duanestorey/Hifi-Amplifier/PCBs/AURORA/_Ready/PSU/readme.md

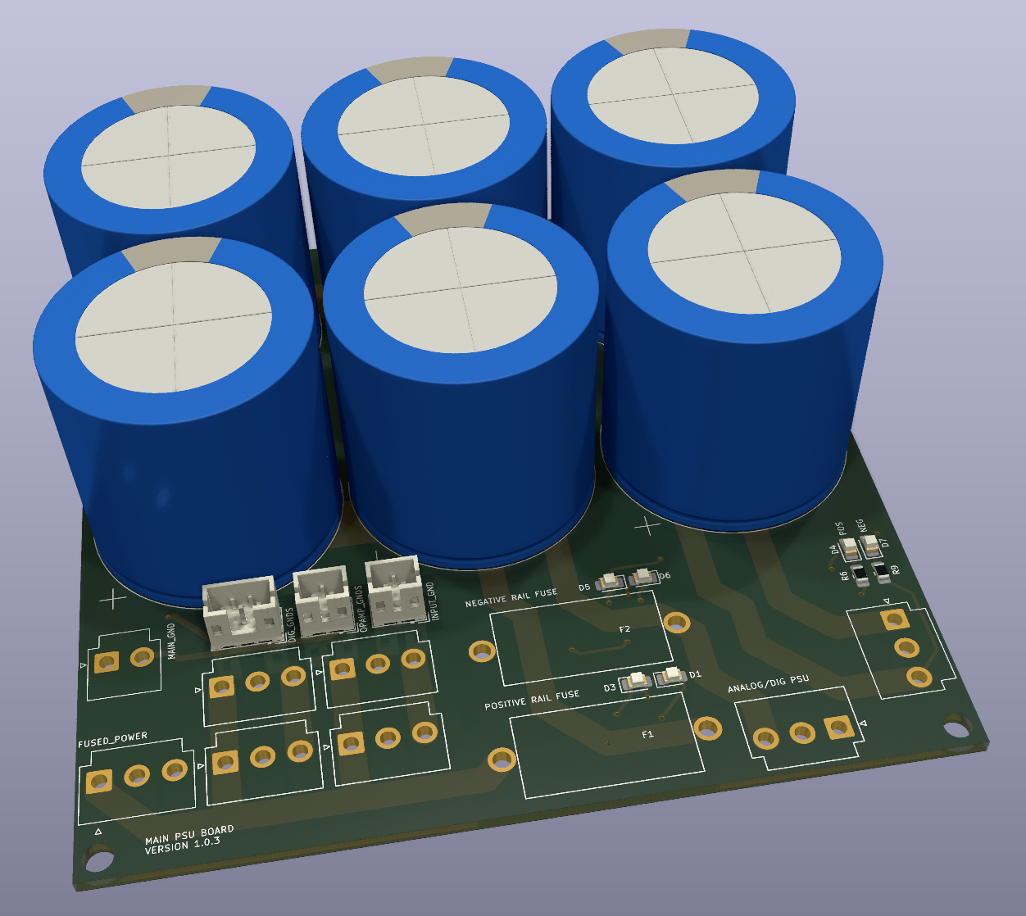
[picture p16: PCBs/AURORA/_Ready/PSU/screenshot.png]


# Main Amplifier Channel Power Supply

## Version History

- 1.0: Initial Release

## Speciality Components

* 30x50mm 15000uF 50V capacitors
* 5x20mm fuse holders
* 5V MELF Zener diodes
