duanestorey/Hifi-Amplifier/PCBs/AURORA/_Ready/FTDI/screenshot.png

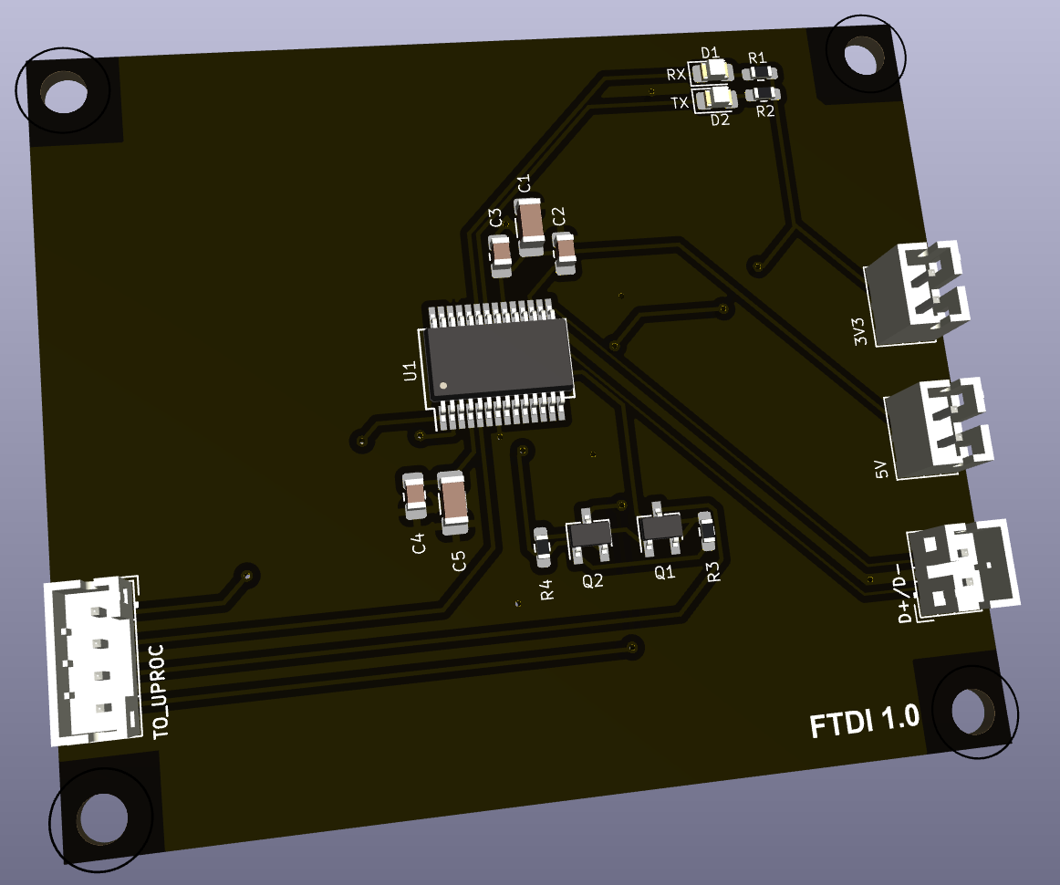
PCBs/AURORA/_Ready/FTDI/screenshot.png
