duanestorey/Hifi-Amplifier/PCBs/AURORA/_Ready/Lift/screenshot.png

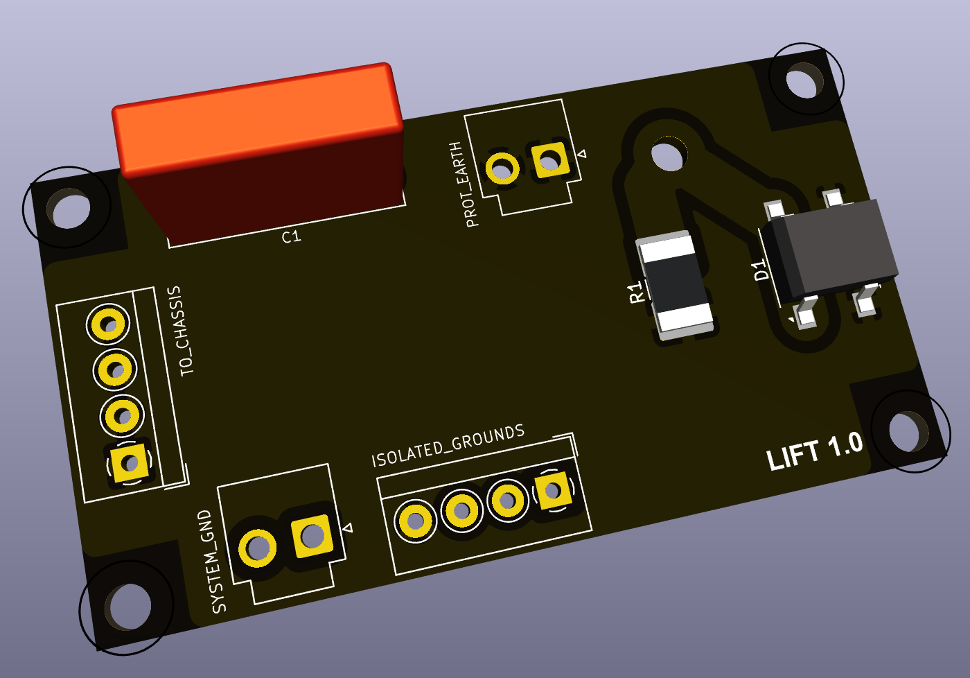
PCBs/AURORA/_Ready/Lift/screenshot.png
