duanestorey/Hifi-Amplifier/PCBs/AURORA/DSP/screenshot.png

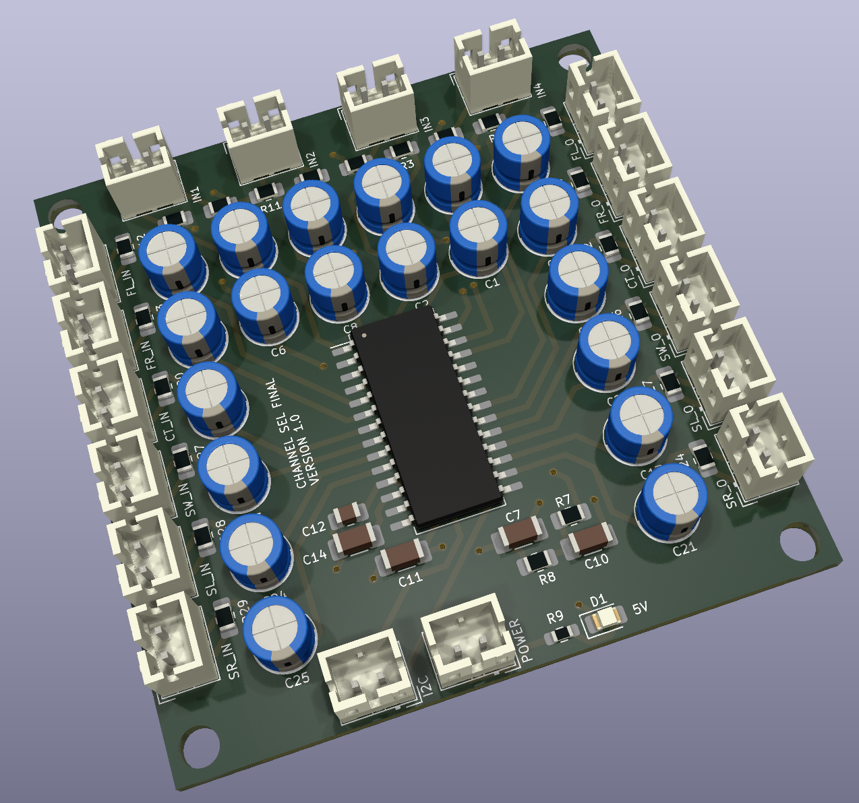
PCBs/AURORA/DSP/screenshot.png
