duanestorey/Hifi-Amplifier/PCBs/AURORA/Subwoofer/screenshot.png

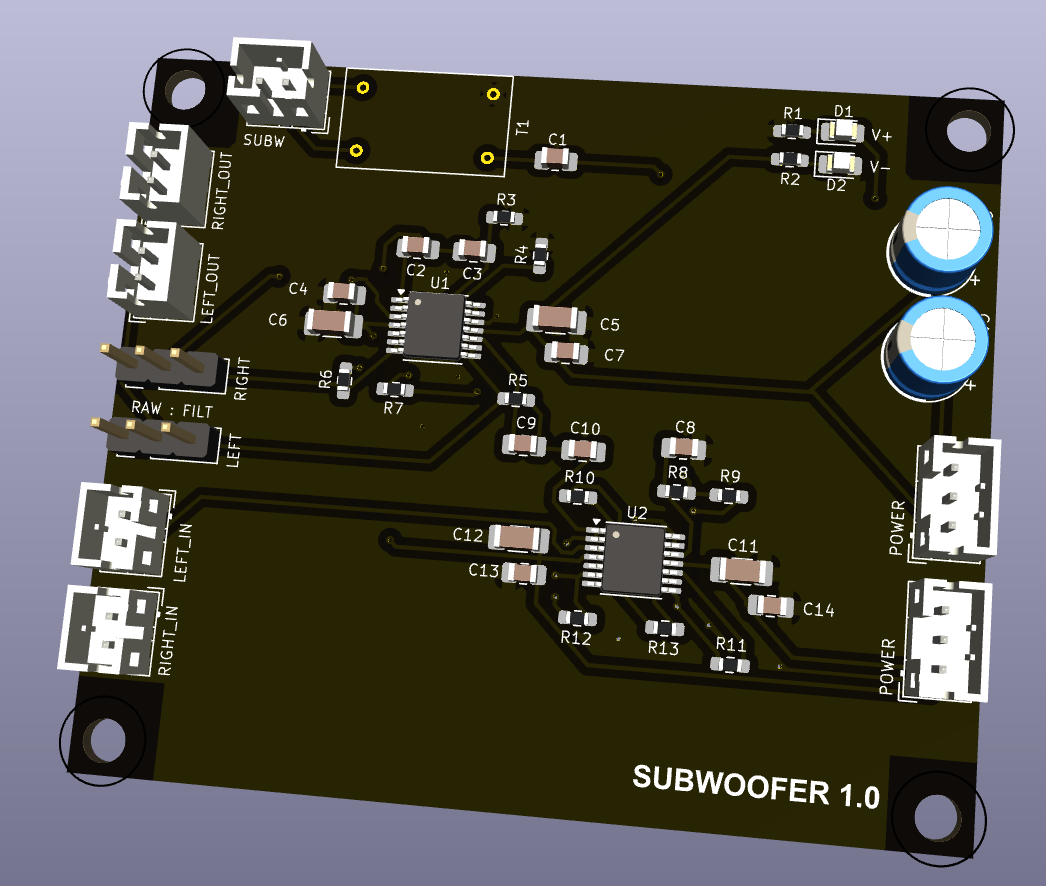
PCBs/AURORA/Subwoofer/screenshot.png
