duanestorey/Hifi-Amplifier/PCBs/DAC Filter/Filter/Low Noise/Screenshot 2023-10-08 at 9.19.52 PM.png

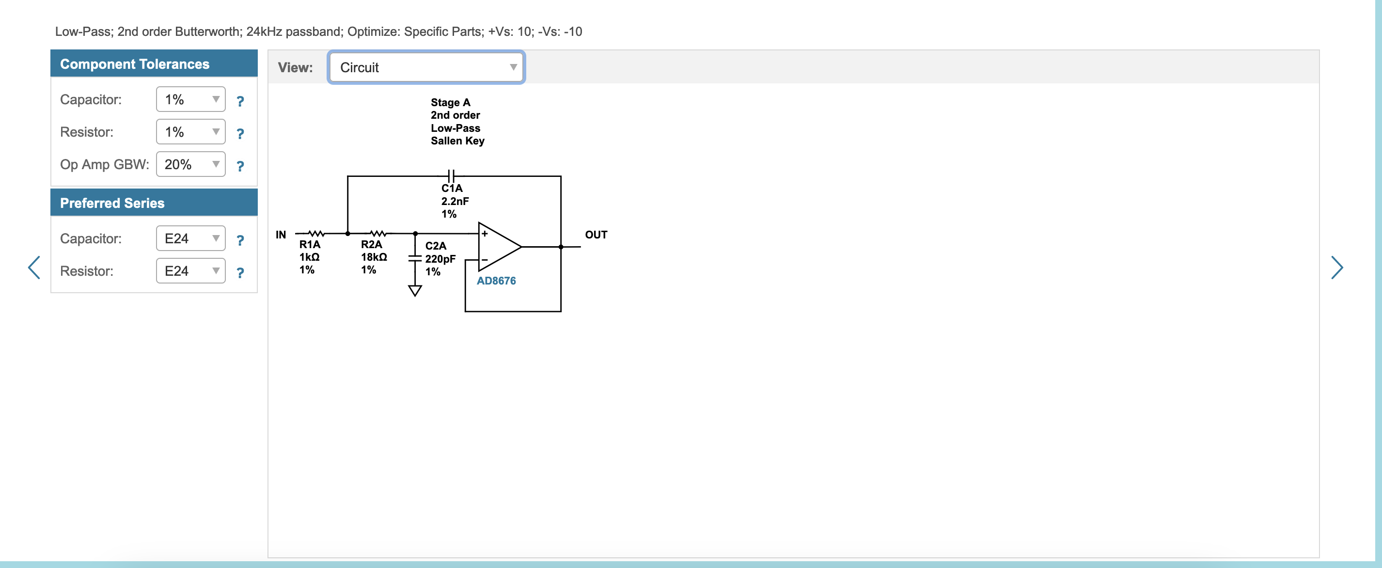
PCBs/DAC Filter/Filter/Low Noise/Screenshot 2023-10-08 at 9.19.52 PM.png
