duanestorey/Hifi-Amplifier/PCBs/AURORA/_Ready/Rectify/1.0/production/bom.csv

Designator | Footprint | Quantity | Value | LCSC Part #
C1, C2 | C_Rect_L13.0mm_W6.0mm_P10.00mm_FKS3_FKP3_MKS4 | 2 | 100N
D1, D3 | Diode_Bridge_Bourns_CD-DF4xxS | 2 | 652-CD-DF408SL
D2 | 0603 | 1 | YELLOW
D4 | 0603 | 1 | BLUE
H1, H2, H3, H4 | MountingHole_3.2mm_M3_Pad_TopOnly | 4 | MountingHole
J1 | JST_VH_B3P-VH_1x03_P3.96mm_Vertical | 1 | Conn_01x03_Male
J2, J3 | JST_VH_B2P-VH-B_1x02_P3.96mm_Vertical | 2 | Conn_01x02_Male
R1, R3 | 0603 | 2 | 16K
R2, R4 | 2512 | 2 | 10R 2W
