duanestorey/Hifi-Amplifier/PCBs/AURORA/DSP/ADAU/0.1/DSP.kicad_pcb

## KiCad design PCBs/AURORA/DSP/_Archived/ADAU/0.1/DSP.kicad_pcb (2024-12-19, an earlier design)

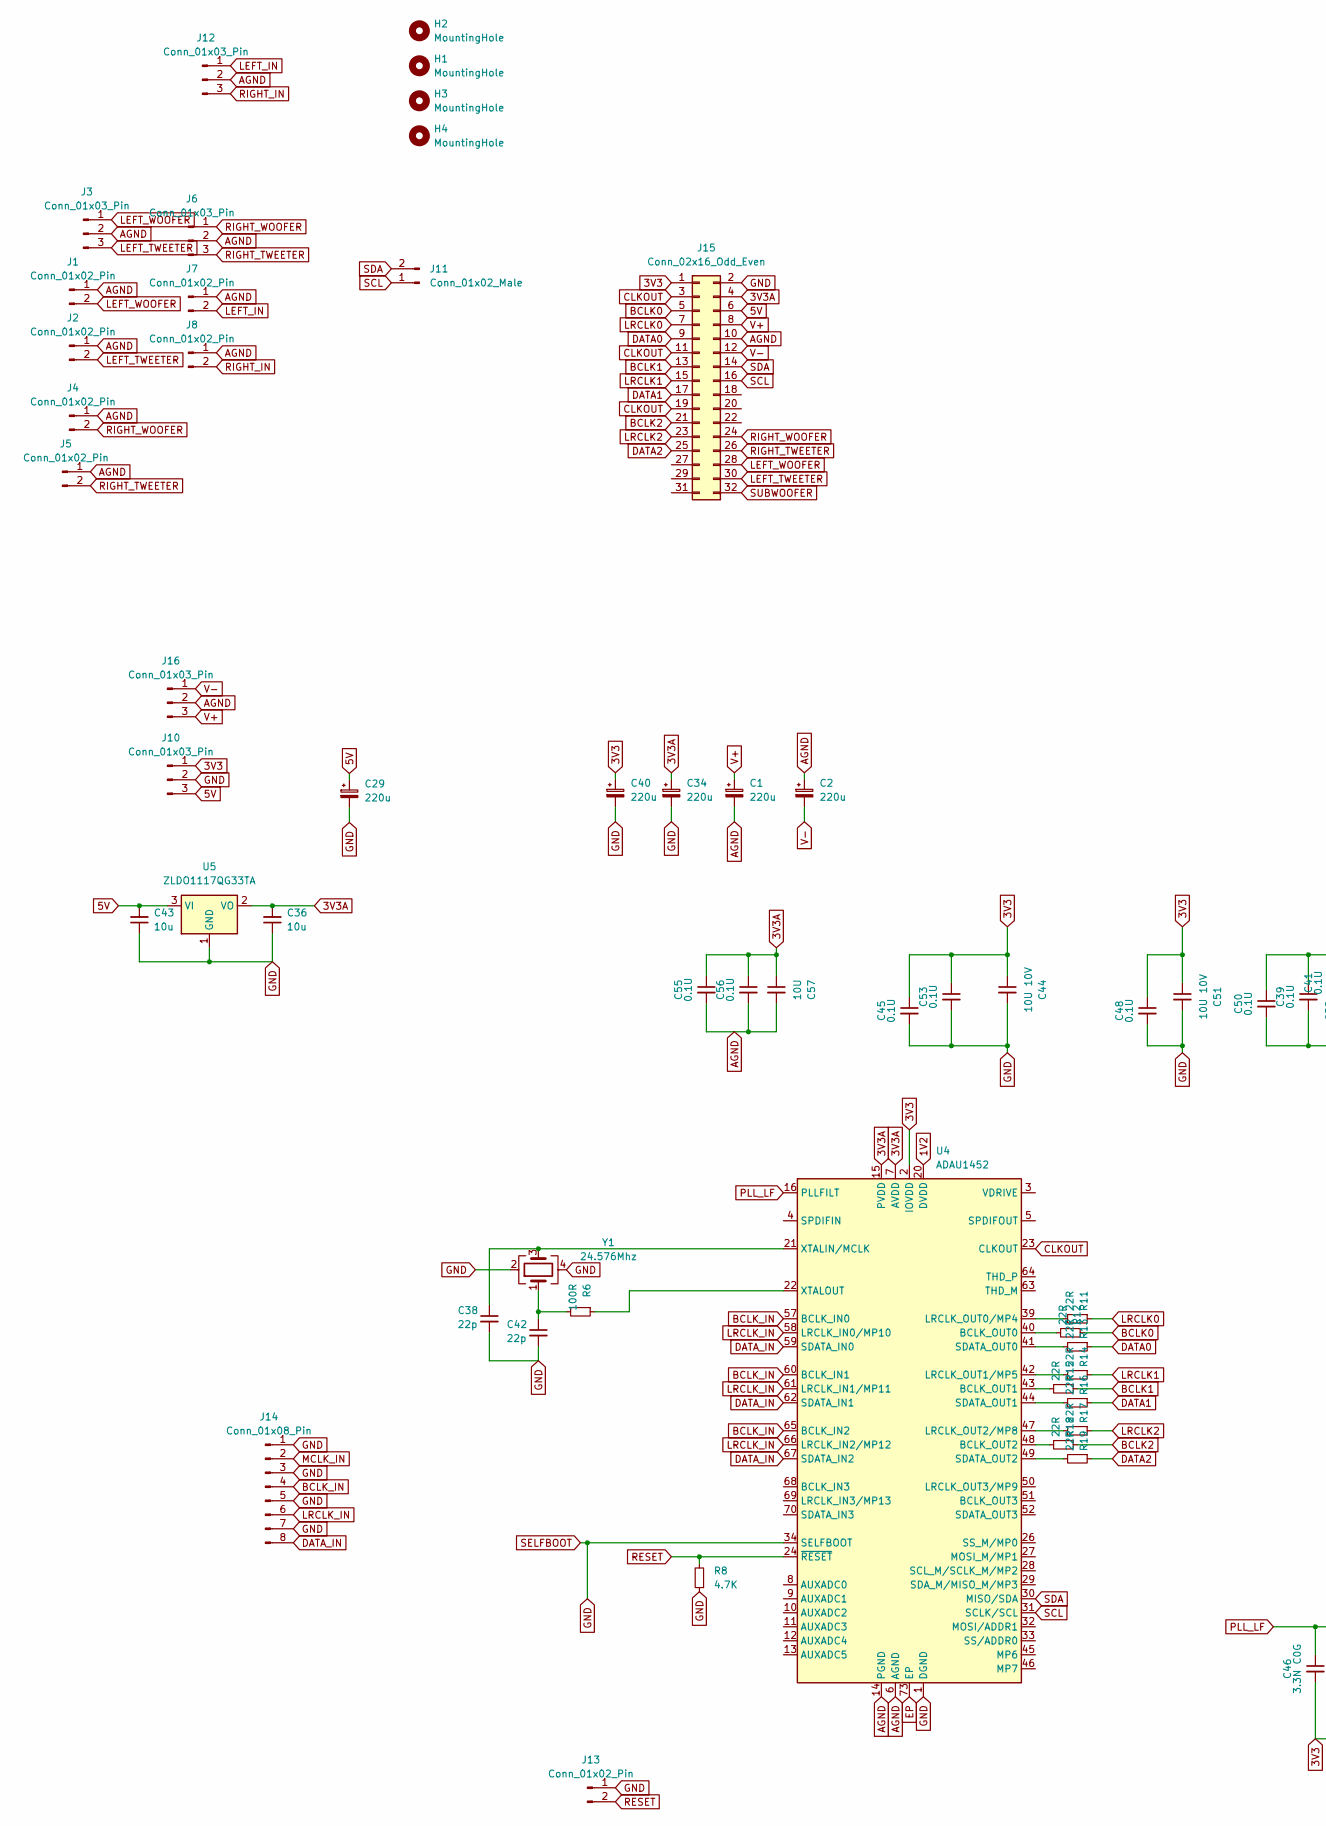
[picture p57: schematic DSP.kicad_sch, part in row 1, column 1]

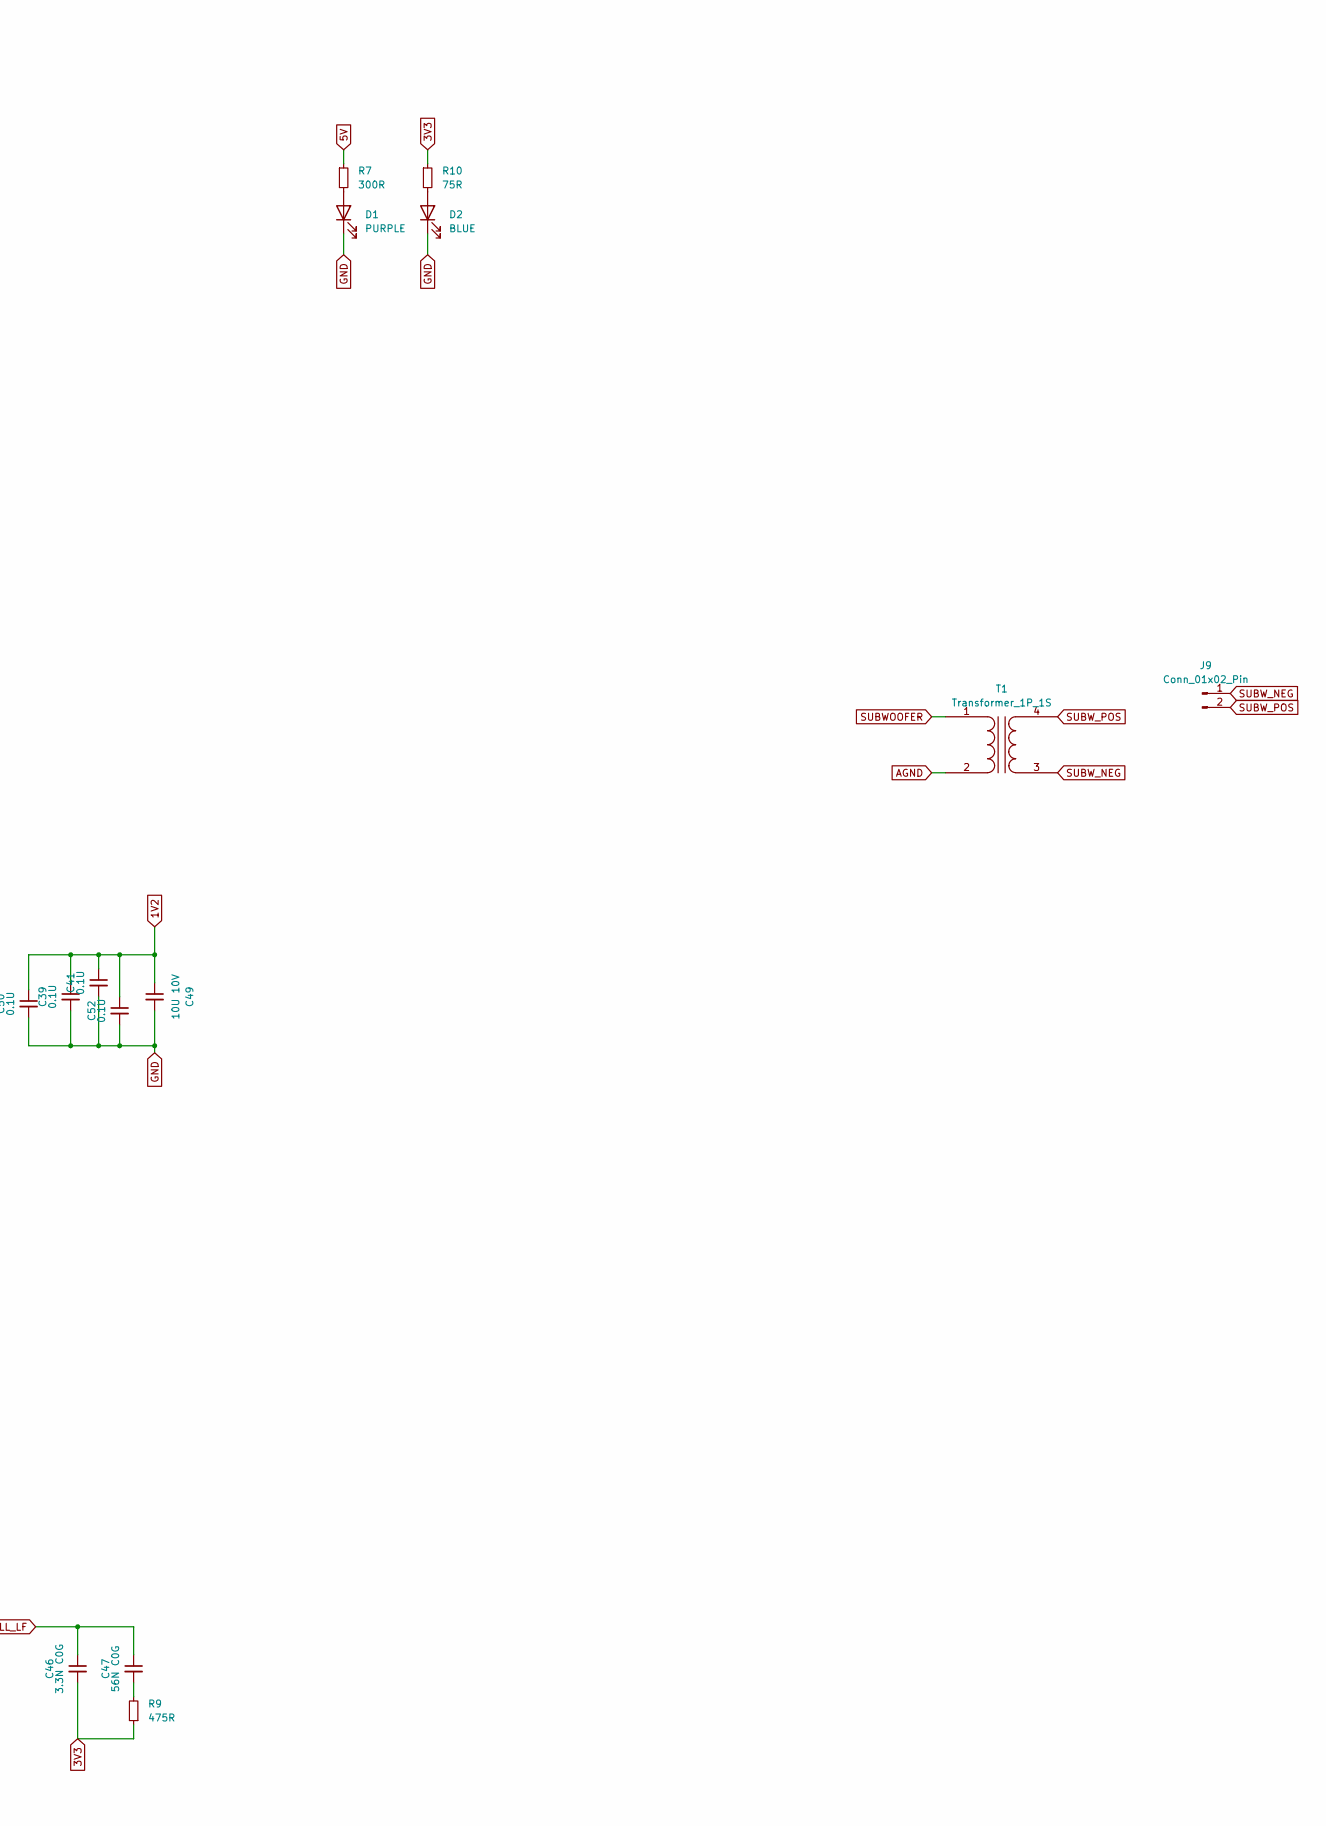
[picture p58: schematic DSP.kicad_sch, part in row 1, column 2]

Parts:
C1, C2, C29, C34, C40: 220u; CP_Radial_D6.3mm_P2.50mm
C36, C43: 10u; C_1206_3216Metric_Pad1.33x1.80mm_HandSolder
C38, C42: 22p; C_0805_2012Metric_Pad1.18x1.45mm_HandSolder
C39, C41, C45, C48, C50, C52, C53, C55, C56: 0.1U; C_0805_2012Metric_Pad1.18x1.45mm_HandSolder
C44, C49, C51: 10U 10V; C_1206_3216Metric_Pad1.33x1.80mm_HandSolder
C46: 3.3N C0G; C_0805_2012Metric_Pad1.18x1.45mm_HandSolder
C47: 56N C0G; C_0805_2012Metric_Pad1.18x1.45mm_HandSolder
C57: 10U; C_1206_3216Metric_Pad1.33x1.80mm_HandSolder
D1: PURPLE; D_0805_2012Metric
D2: BLUE; D_0805_2012Metric
H1, H2, H3, H4: MountingHole; MountingHole_3.2mm_M3
J1, J2, J4, J5, J7, J8, J9, J13: Conn_01x02_Pin; JST_PH_B2B-PH-K_1x02_P2.00mm_Vertical
J3, J6, J10, J12, J16: Conn_01x03_Pin; JST_PH_B3B-PH-K_1x03_P2.00mm_Vertical
J11: Conn_01x02_Male; JST_PH_B2B-PH-K_1x02_P2.00mm_Vertical
J14: Conn_01x08_Pin; JST_PH_B8B-PH-K_1x08_P2.00mm_Vertical
J15: Conn_02x16_Odd_Even; PinHeader_2x16_P2.54mm_Vertical
R6: 100R; R_0603_1608Metric_Pad0.98x0.95mm_HandSolder
R7: 300R; R_0603_1608Metric_Pad0.98x0.95mm_HandSolder
R8: 4.7K; R_0603_1608Metric_Pad0.98x0.95mm_HandSolder
R9: 475R; R_1206_3216Metric_Pad1.30x1.75mm_HandSolder
R10: 75R; R_0603_1608Metric_Pad0.98x0.95mm_HandSolder
R11, R12, R13, R14, R15, R16, R17, R18, R19: 22R; R_0603_1608Metric_Pad0.98x0.95mm_HandSolder
T1: Transformer_1P_1S; DA101C
U4: ADAU1452; LFCSP-72-1EP_10x10mm_P0.5mm_EP5.3x5.3mm
U5: ZLDO1117QG33TA; SOT-223-3_TabPin2
Y1: 24.576Mhz; Crystal_SMD_3225-4Pin_3.2x2.5mm_HandSoldering

Connections:
1V2: C39.1, C41.1, C49.1, C50.1, C52.1, U4.20 (DVDD), U4.35 (DVDD), U4.53 (DVDD), U4.71 (DVDD)
3V3: C40.1, C44.1, C45.1, C46.2, C48.1, C51.1, C53.1, J10.1, J15.1, R9.1, R10.1, U4.2 (IOVDD), U4.18 (IOVDD), U4.38 (IOVDD), U4.56 (IOVDD)
3V3A: C34.1, C36.2, C55.1, C56.1, C57.1, J15.4, U4.7 (AVDD), U4.15 (PVDD), U5.2 (VO)
5V: C29.1, C43.2, J10.3, J15.6, R7.1, U5.3 (VI)
AGND: C1.2, C2.1, C55.2, C56.2, C57.2, J1.1, J2.1, J3.2, J4.1, J5.1, J6.2, J7.1, J8.1, J12.2, J15.10, J16.2, T1.2 (AB), U4.6 (AGND), U4.14 (PGND)
BCLK0: J15.5, R12.1
BCLK1: J15.13, R15.1
BCLK2: J15.21, R18.1
BCLK_IN: J14.4, U4.57 (BCLK_IN0), U4.60 (BCLK_IN1), U4.65 (BCLK_IN2)
CLKOUT: J15.3, J15.11, J15.19, U4.23 (CLKOUT)
DATA0: J15.9, R13.1
DATA1: J15.17, R16.1
DATA2: J15.25, R19.1
DATA_IN: J14.8, U4.59 (SDATA_IN0), U4.62 (SDATA_IN1), U4.67 (SDATA_IN2)
EP: U4.73 (EP)
GND: C29.2, C34.2, C36.1, C38.2, C39.2, C40.2, C41.2, C42.2, C43.1, C44.2, C45.2, C48.2, C49.2, C50.2, C51.2, C52.2, C53.2, D1.1 (K), D2.1 (K), J10.2, J13.1, J14.1, J14.3, J14.5, J14.7, J15.2, R8.1, U4.1 (DGND), U4.17 (DGND), U4.19 (DGND), U4.25 (DGND), U4.34 (SELFBOOT), U4.36 (DGND), U4.37 (DGND), U4.54 (DGND), U4.55 (DGND), U4.72 (DGND), U5.1 (GND), Y1.2, Y1.4
LEFT_IN: J7.2, J12.1
LEFT_TWEETER: J2.2, J3.3, J15.30
LEFT_WOOFER: J1.2, J3.1, J15.28
LRCLK0: J15.7, R11.1
LRCLK1: J15.15, R14.1
LRCLK2: J15.23, R17.1
LRCLK_IN: J14.6, U4.58 (LRCLK_IN0/MP10), U4.61 (LRCLK_IN1/MP11), U4.66 (LRCLK_IN2/MP12)
MCLK_IN: J14.2
unnamed: C42.1, R6.2, Y1.1
unnamed: C47.2, R9.2
unnamed: D1.2 (A), R7.2
unnamed: D2.2 (A), R10.2
unnamed: R12.2, U4.40 (BCLK_OUT0)
unnamed: R15.2, U4.43 (BCLK_OUT1)
unnamed: R18.2, U4.48 (BCLK_OUT2)
unnamed: R11.2, U4.39 (LRCLK_OUT0/MP4)
unnamed: R14.2, U4.42 (LRCLK_OUT1/MP5)
unnamed: R17.2, U4.47 (LRCLK_OUT2/MP8)
unnamed: R13.2, U4.41 (SDATA_OUT0)
unnamed: R16.2, U4.44 (SDATA_OUT1)
unnamed: R19.2, U4.49 (SDATA_OUT2)
unnamed: C38.1, U4.21 (XTALIN/MCLK), Y1.3
unnamed: R6.1, U4.22 (XTALOUT)
PLL_LF: C46.1, C47.1, U4.16 (PLLFILT)
RESET: J13.2, R8.2, U4.24 (~RESET)
RIGHT_IN: J8.2, J12.3
RIGHT_TWEETER: J5.2, J6.3, J15.26
RIGHT_WOOFER: J4.2, J6.1, J15.24
SCL: J11.1, J15.16, U4.31 (SCLK/SCL)
SDA: J11.2, J15.14, U4.30 (MISO/SDA)
SUBWOOFER: J15.32, T1.1 (AA)
SUBW_NEG: J9.1, T1.3 (SA)
SUBW_POS: J9.2, T1.4 (SB)
V+: C1.1, J15.8, J16.3
V-: C2.2, J15.12, J16.1

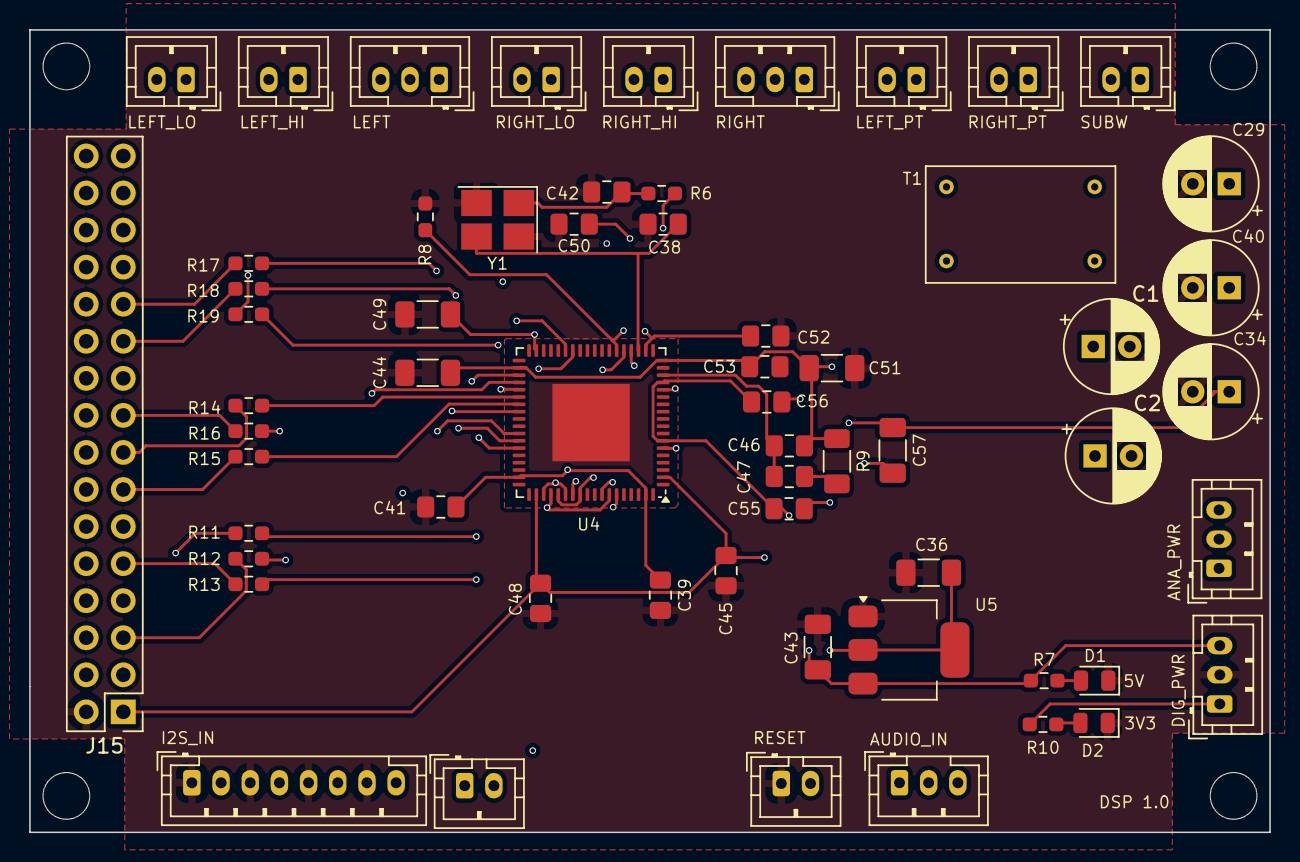
[picture p59: board PCBs/AURORA/DSP/_Archived/ADAU/0.1/DSP.kicad_pcb from above]

Board: 4 copper layers, 85.0 x 55.0 mm, 64 parts (0 on the bottom side), 49 nets.
