duanestorey/Hifi-Amplifier/PCBs/AURORA/InputSel/0.3/InputSel.kicad_pcb

## KiCad design PCBs/AURORA/InputSel/0.3/InputSel.kicad_pcb (2024-12-21)

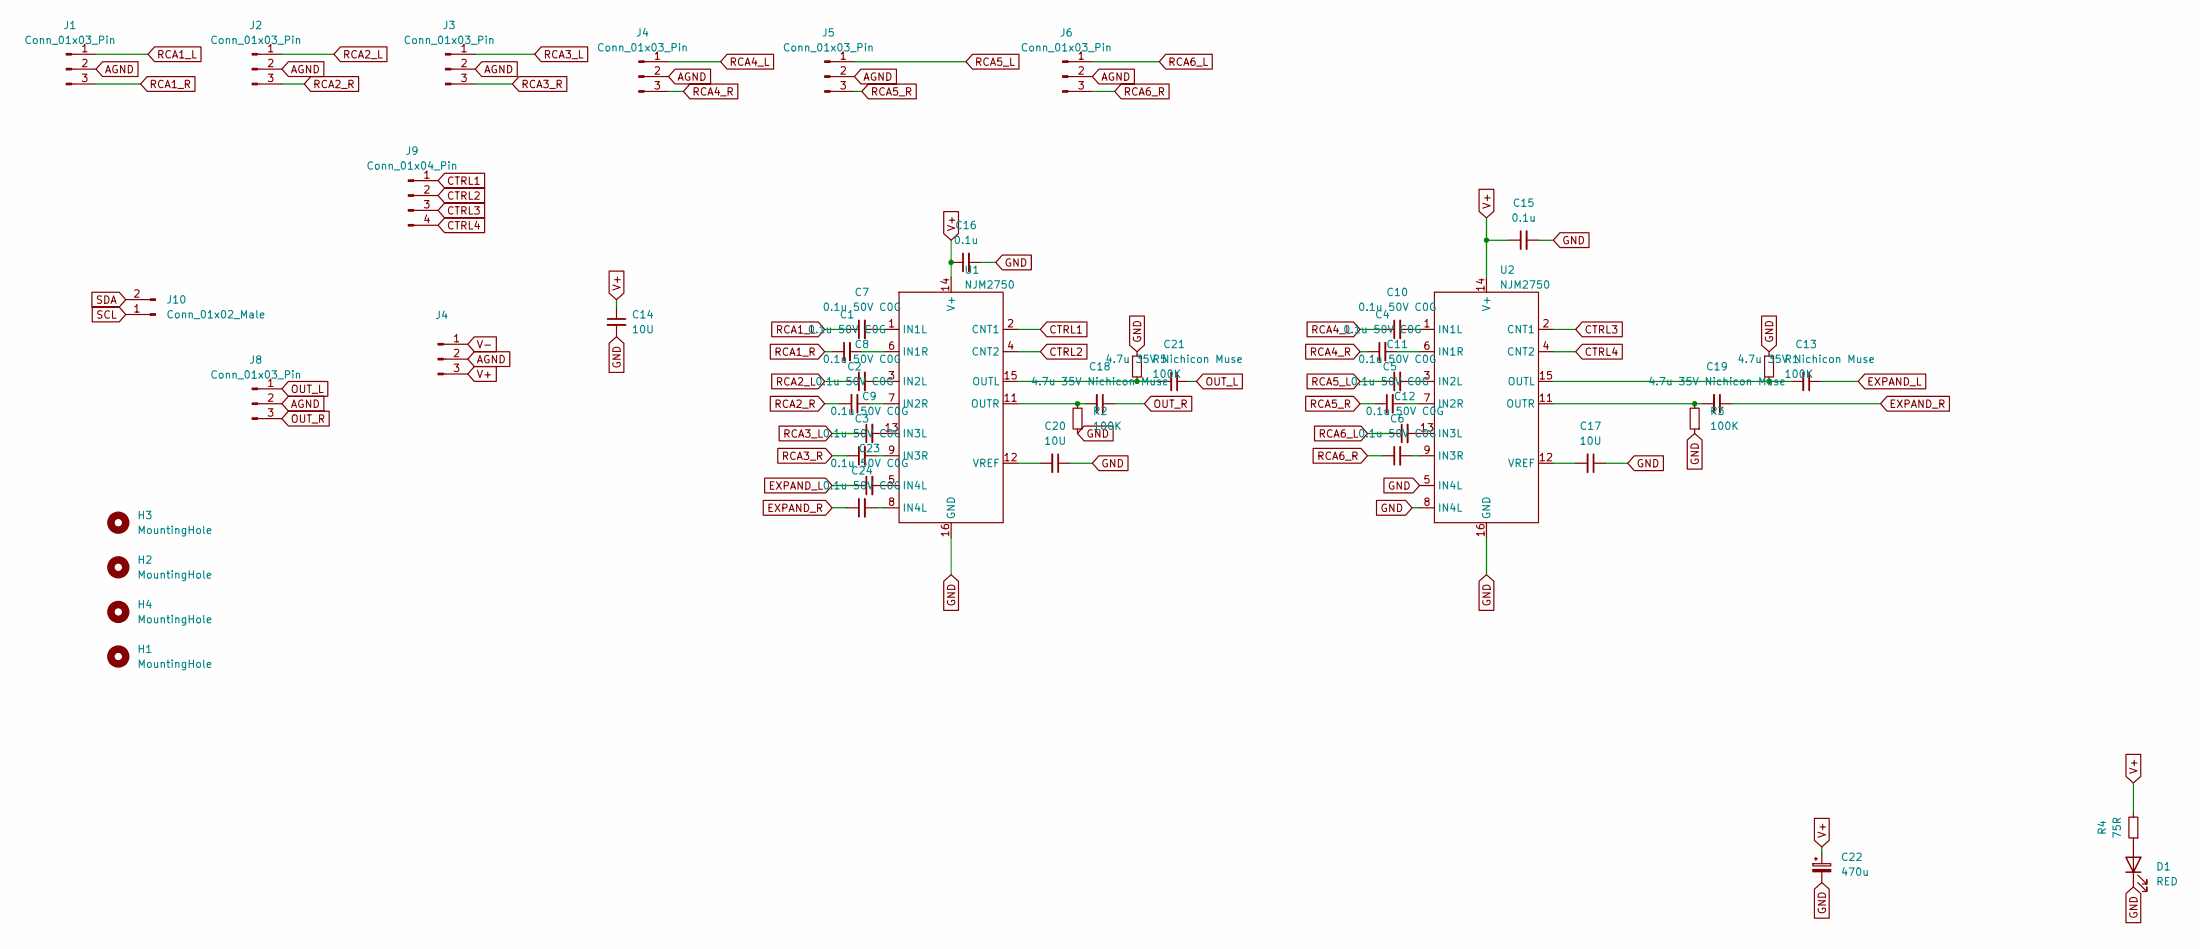
[picture p62: schematic InputSel.kicad_sch]

Parts:
C1, C2, C3, C4, C5, C6, C7, C8, C9, C10, C11, C12, C23, C24: 0.1u 50V C0G; C_1206_3216Metric_Pad1.33x1.80mm_HandSolder; Mouser 81-GRM3195C1H104JA5D
C13, C18, C19, C21: 4.7u 35V Nichicon Muse; CP_Radial_D5.0mm_P2.00mm
C14, C17, C20: 10U; C_1206_3216Metric_Pad1.33x1.80mm_HandSolder
C15, C16: 0.1u; C_0805_2012Metric_Pad1.18x1.45mm_HandSolder
C22: 470u; CP_Radial_D6.3mm_P2.50mm
D1: RED; LED_0805_2012Metric
H1, H2, H3, H4: MountingHole; MountingHole_3.2mm_M3_DIN965_Pad_TopOnly
J1, J2, J3, J5, J6, J8: Conn_01x03_Pin; JST_PH_B3B-PH-K_1x03_P2.00mm_Vertical
J4: Conn_01x03_Male; JST_PH_B3B-PH-K_1x03_P2.00mm_Vertical
J9: Conn_01x04_Pin; JST_PH_B4B-PH-K_1x04_P2.00mm_Vertical
J10: Conn_01x02_Male; JST_PH_B2B-PH-K_1x02_P2.00mm_Vertical
R1, R2, R3, R5: 100K; R_0603_1608Metric_Pad0.98x0.95mm_HandSolder; Mouser 603-AT0603FRE07100KL
R4: 75R; R_0603_1608Metric_Pad0.98x0.95mm_HandSolder
U1, U2: NJM2750; SOP-16_4.4x10.4mm_P1.27mm; Mouser NJM2750M

Connections:
AGND: J1.2, J2.2, J3.2, J4.2, J5.2, J6.2, J8.2; also elsewhere on the board
CTRL1: J9.1, U1.2 (CNT1)
CTRL2: J9.2, U1.4 (CNT2)
CTRL3: J9.3, U2.2 (CNT1)
CTRL4: J9.4, U2.4 (CNT2)
EXPAND_L: C13.1, C23.1
EXPAND_R: C19.1, C24.1
GND: C14.2, C15.2, C16.2, C17.1, C20.1, C22.2, D1.1 (K), R1.1, R2.1, R3.1, R5.1, U1.16 (GND), U2.5 (IN4L), U2.8 (IN4L), U2.16 (GND)
unnamed: C23.2, U1.5 (IN4L)
unnamed: C24.2, U1.8 (IN4L)
unnamed: D1.2 (A), R4.1
unnamed: C7.2, U1.1 (IN1L)
unnamed: C1.2, U1.6 (IN1R)
unnamed: C8.2, U1.3 (IN2L)
unnamed: C2.2, U1.7 (IN2R)
unnamed: C9.2, U1.13 (IN3L)
unnamed: C3.2, U1.9 (IN3R)
unnamed: C21.2, R5.2, U1.15 (OUTL)
unnamed: C18.2, R2.2, U1.11 (OUTR)
unnamed: C20.2, U1.12 (VREF)
unnamed: C10.2, U2.1 (IN1L)
unnamed: C4.2, U2.6 (IN1R)
unnamed: C11.2, U2.3 (IN2L)
unnamed: C5.2, U2.7 (IN2R)
unnamed: C12.2, U2.13 (IN3L)
unnamed: C6.2, U2.9 (IN3R)
unnamed: C13.2, R1.2, U2.15 (OUTL)
unnamed: C19.2, R3.2, U2.11 (OUTR)
unnamed: C17.2, U2.12 (VREF)
OUT_L: C21.1, J8.1
OUT_R: C18.1, J8.3
RCA1_L: C7.1, J1.1
RCA1_R: C1.1, J1.3
RCA2_L: C8.1, J2.1
RCA2_R: C2.1, J2.3
RCA3_L: C9.1, J3.1
RCA3_R: C3.1, J3.3
RCA5_L: C11.1, J5.1
RCA5_R: C5.1, J5.3
RCA6_L: C12.1, J6.1
RCA6_R: C6.1, J6.3
SCL: J10.1
SDA: J10.2

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
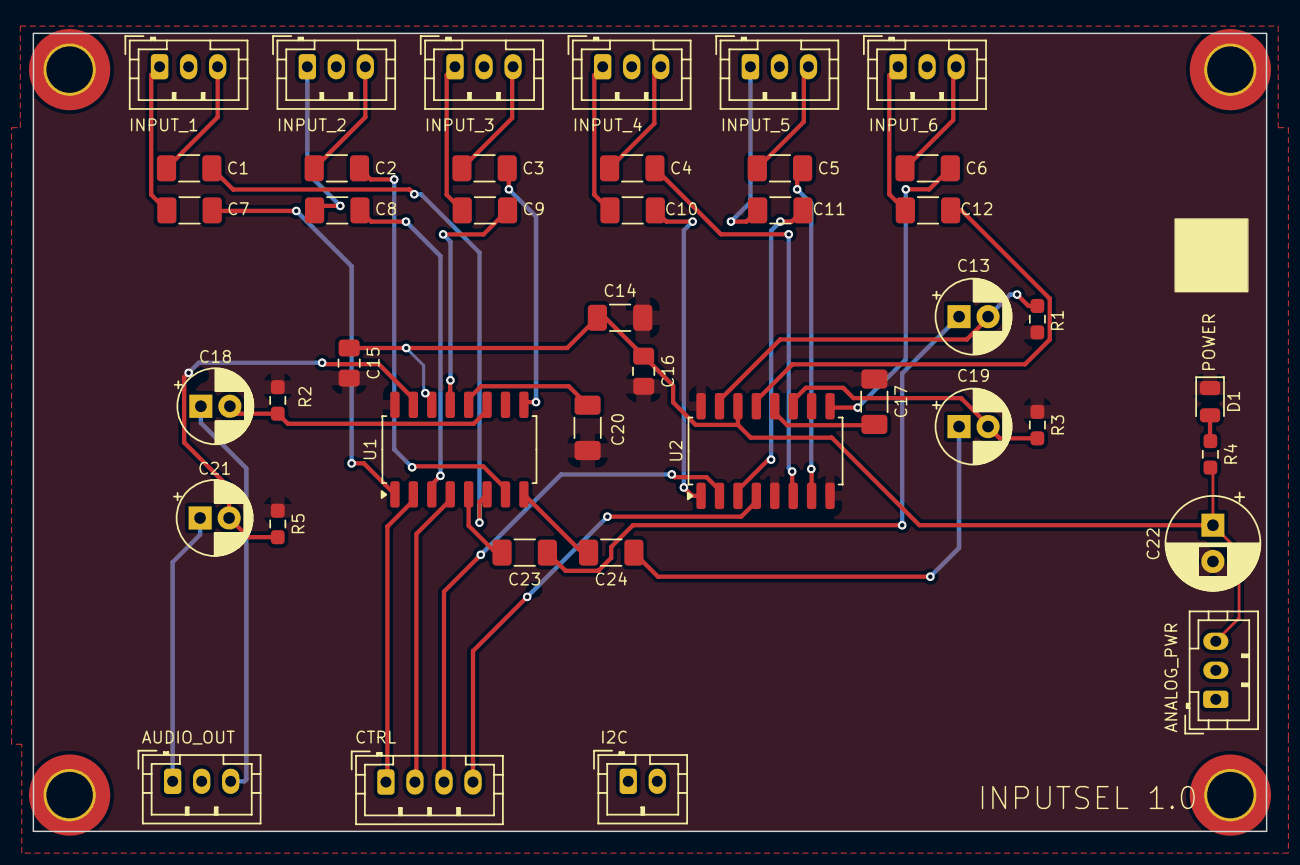
[picture p63: board PCBs/AURORA/InputSel/0.3/InputSel.kicad_pcb from above]

Board: 2 copper layers, 85.0 x 55.0 mm, 46 parts (0 on the bottom side), 44 nets.

Other parts of the board:
J7: Conn_01x03_Male; JST_PH_B3B-PH-K_1x03_P2.00mm_Vertical

Their connections:
AGND: J7.2; also elsewhere on the board
