duanestorey/Hifi-Amplifier/PCBs/AURORA/_Ready/PSU/1.0/PSU.kicad_pcb

## KiCad design PCBs/AURORA/_Ready/PSU/1.0/PSU.kicad_pcb (2024-12-19)

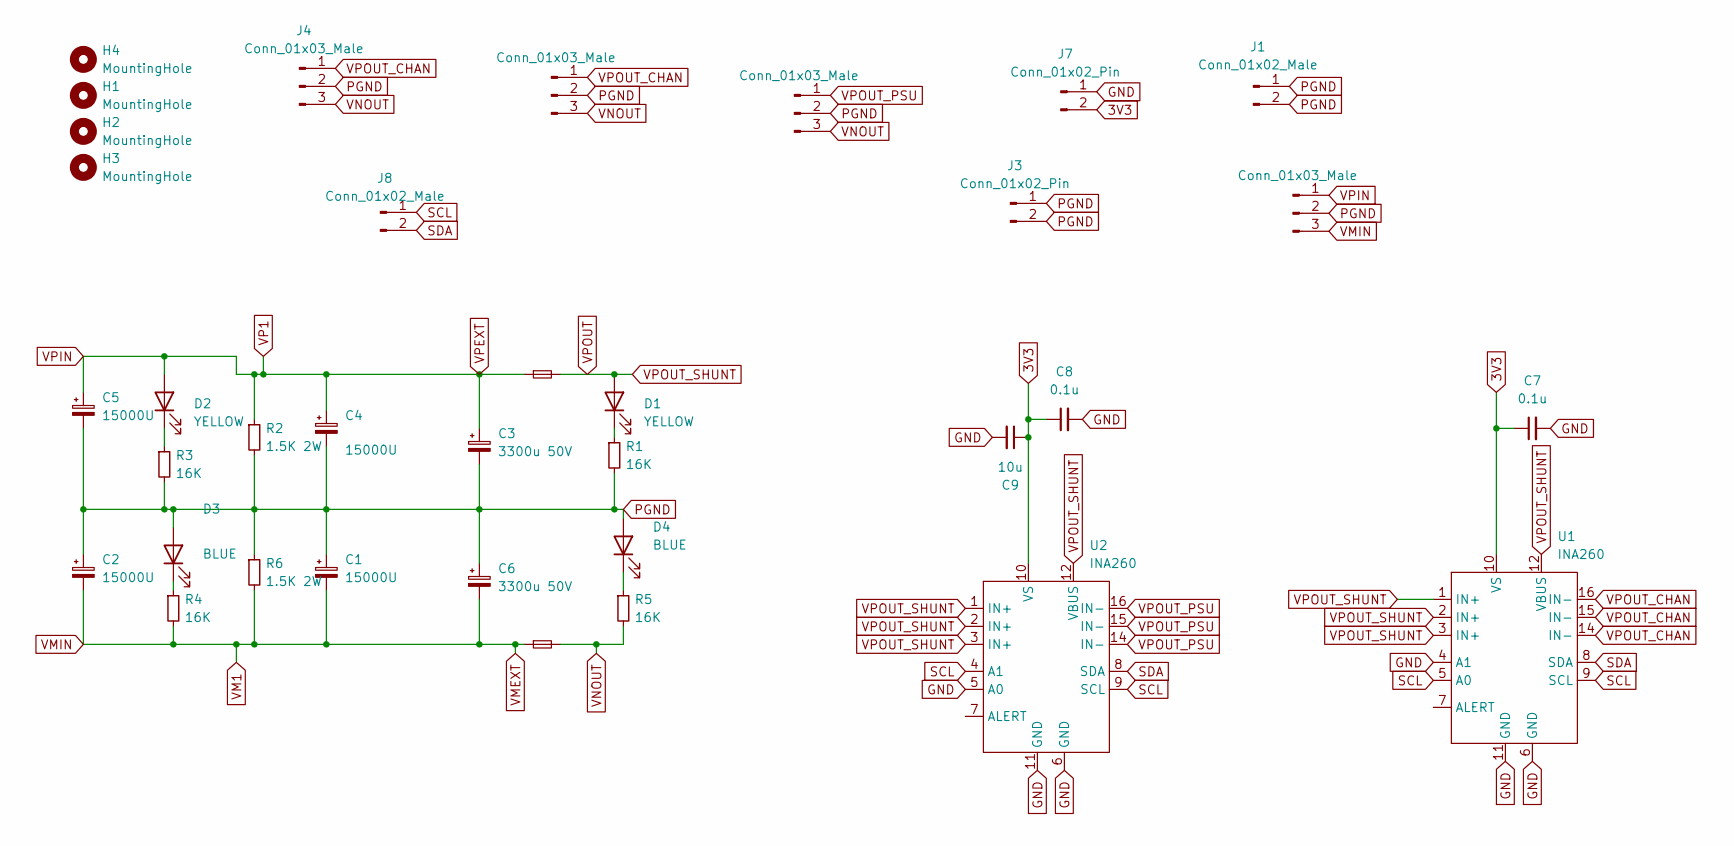
[picture p64: schematic PSU.kicad_sch]

Parts:
C1, C2, C4, C5: 15000U; CP_Radial_D30.0mm_P10.00mm_SnapIn
C3, C6: 3300u 50V; CP_Radial_D18.0mm_P7.50mm
C7, C8: 0.1u; C_0805_2012Metric_Pad1.18x1.45mm_HandSolder
C9: 10u; C_1206_3216Metric_Pad1.33x1.80mm_HandSolder
D1, D2: YELLOW; LED_0603_1608Metric_Pad1.05x0.95mm_HandSolder
D3, D4: BLUE; LED_0603_1608Metric_Pad1.05x0.95mm_HandSolder
F1, F2: Fuse_Small; Aliexpress Fuse 5x20
H1, H2, H3, H4: MountingHole; MountingHole_3mm_Pad_TopOnly
J1: Conn_01x02_Male; JST_VH_B2P-VH-B_1x02_P3.96mm_Vertical
J2, J4, J5, J6: Conn_01x03_Male; JST_VH_B3P-VH_1x03_P3.96mm_Vertical
J3, J7: Conn_01x02_Pin; JST_PH_B2B-PH-K_1x02_P2.00mm_Vertical
J8: Conn_01x02_Male; JST_PH_B2B-PH-K_1x02_P2.00mm_Vertical
R1, R3, R4, R5: 16K; LED_0603_1608Metric_Pad1.05x0.95mm_HandSolder; Mouser 71-CRCW060316K0FKEAC
R2, R6: 1.5K 2W; R_2512_6332Metric_Pad1.40x3.35mm_HandSolder; Mouser 652-CRM2512JW152ELF
U1, U2: INA260; TSSOP-16_4.4x5mm_P0.65mm; Mouser 595-INA260AIPWR

Connections:
3V3: C7.1, C8.1, C9.1, J7.2, U1.10 (VS), U2.10 (VS)
GND: C7.2, C8.2, C9.2, J7.1, U1.4 (A1), U1.6 (GND), U1.11 (GND), U2.5 (A0), U2.6 (GND), U2.11 (GND)
unnamed: D1.1 (K), R1.1
unnamed: D2.1 (K), R3.1
unnamed: D3.1 (K), R4.1
unnamed: D4.1 (K), R5.1
PGND: C1.1, C2.1, C3.2, C4.2, C5.2, C6.1, D3.2 (A), D4.2 (A), J1.1, J1.2, J2.2, J3.1, J3.2, J4.2, J5.2, J6.2, R1.2, R2.2, R3.2, R6.1
SCL: J8.1, U1.5 (A0), U1.9 (SCL), U2.4 (A1), U2.9 (SCL)
SDA: J8.2, U1.8 (SDA), U2.8 (SDA)
VM1: C1.2, C2.2, C6.2, F2.1, J2.3, R4.2, R6.2
VNOUT: F2.2, J4.3, J5.3, J6.3, R5.2
VP1: C3.1, C4.1, C5.1, D2.2 (A), F1.1, J2.1, R2.1
VPOUT: D1.2 (A), F1.2, U1.1 (IN+), U1.2 (IN+), U1.3 (IN+), U1.12 (VBUS), U2.1 (IN+), U2.2 (IN+), U2.3 (IN+), U2.12 (VBUS)
VPOUT_CHAN: J4.1, J5.1, U1.14 (IN-), U1.15 (IN-), U1.16 (IN-)
VPOUT_PSU: J6.1, U2.14 (IN-), U2.15 (IN-), U2.16 (IN-)

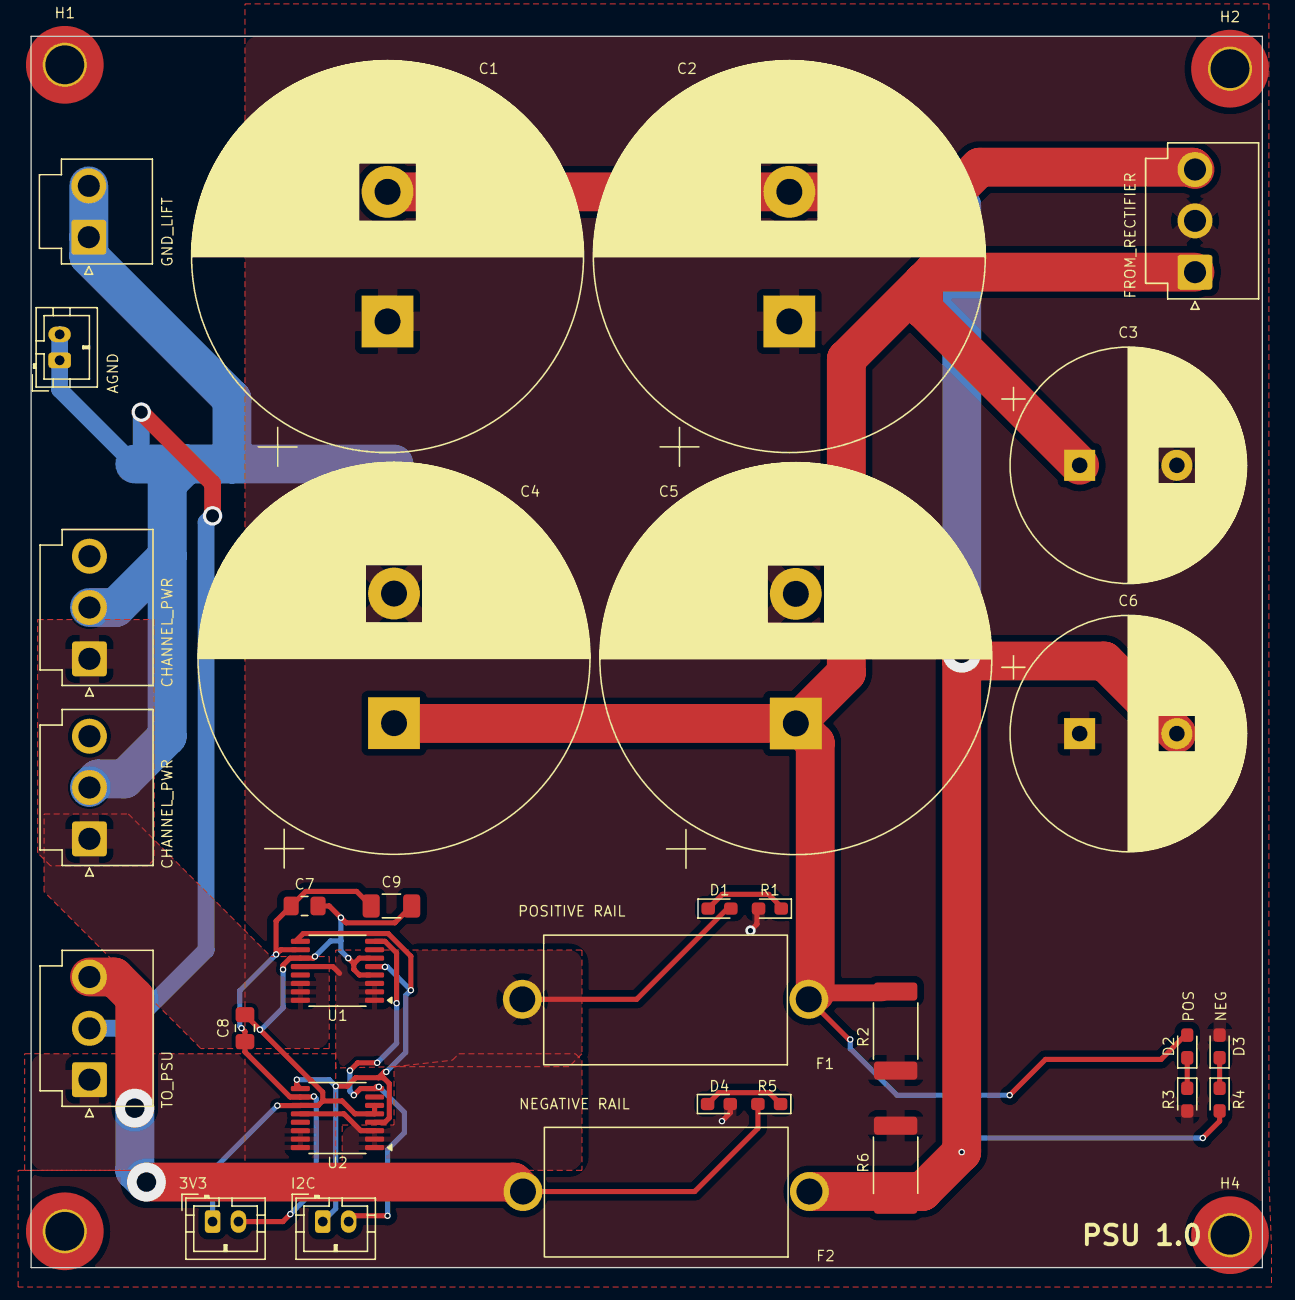
[picture p65: board PSU.kicad_pcb from above]

Board: 2 copper layers, 95.0 x 95.0 mm, 35 parts (0 on the bottom side), 15 nets.
