duanestorey/Hifi-Amplifier/PCBs/AURORA/_Ready/LM3886/1.0/LM3886.kicad_pcb

## KiCad design PCBs/AURORA/_Ready/LM3886/1.0/LM3886.kicad_pcb (2024-12-19)

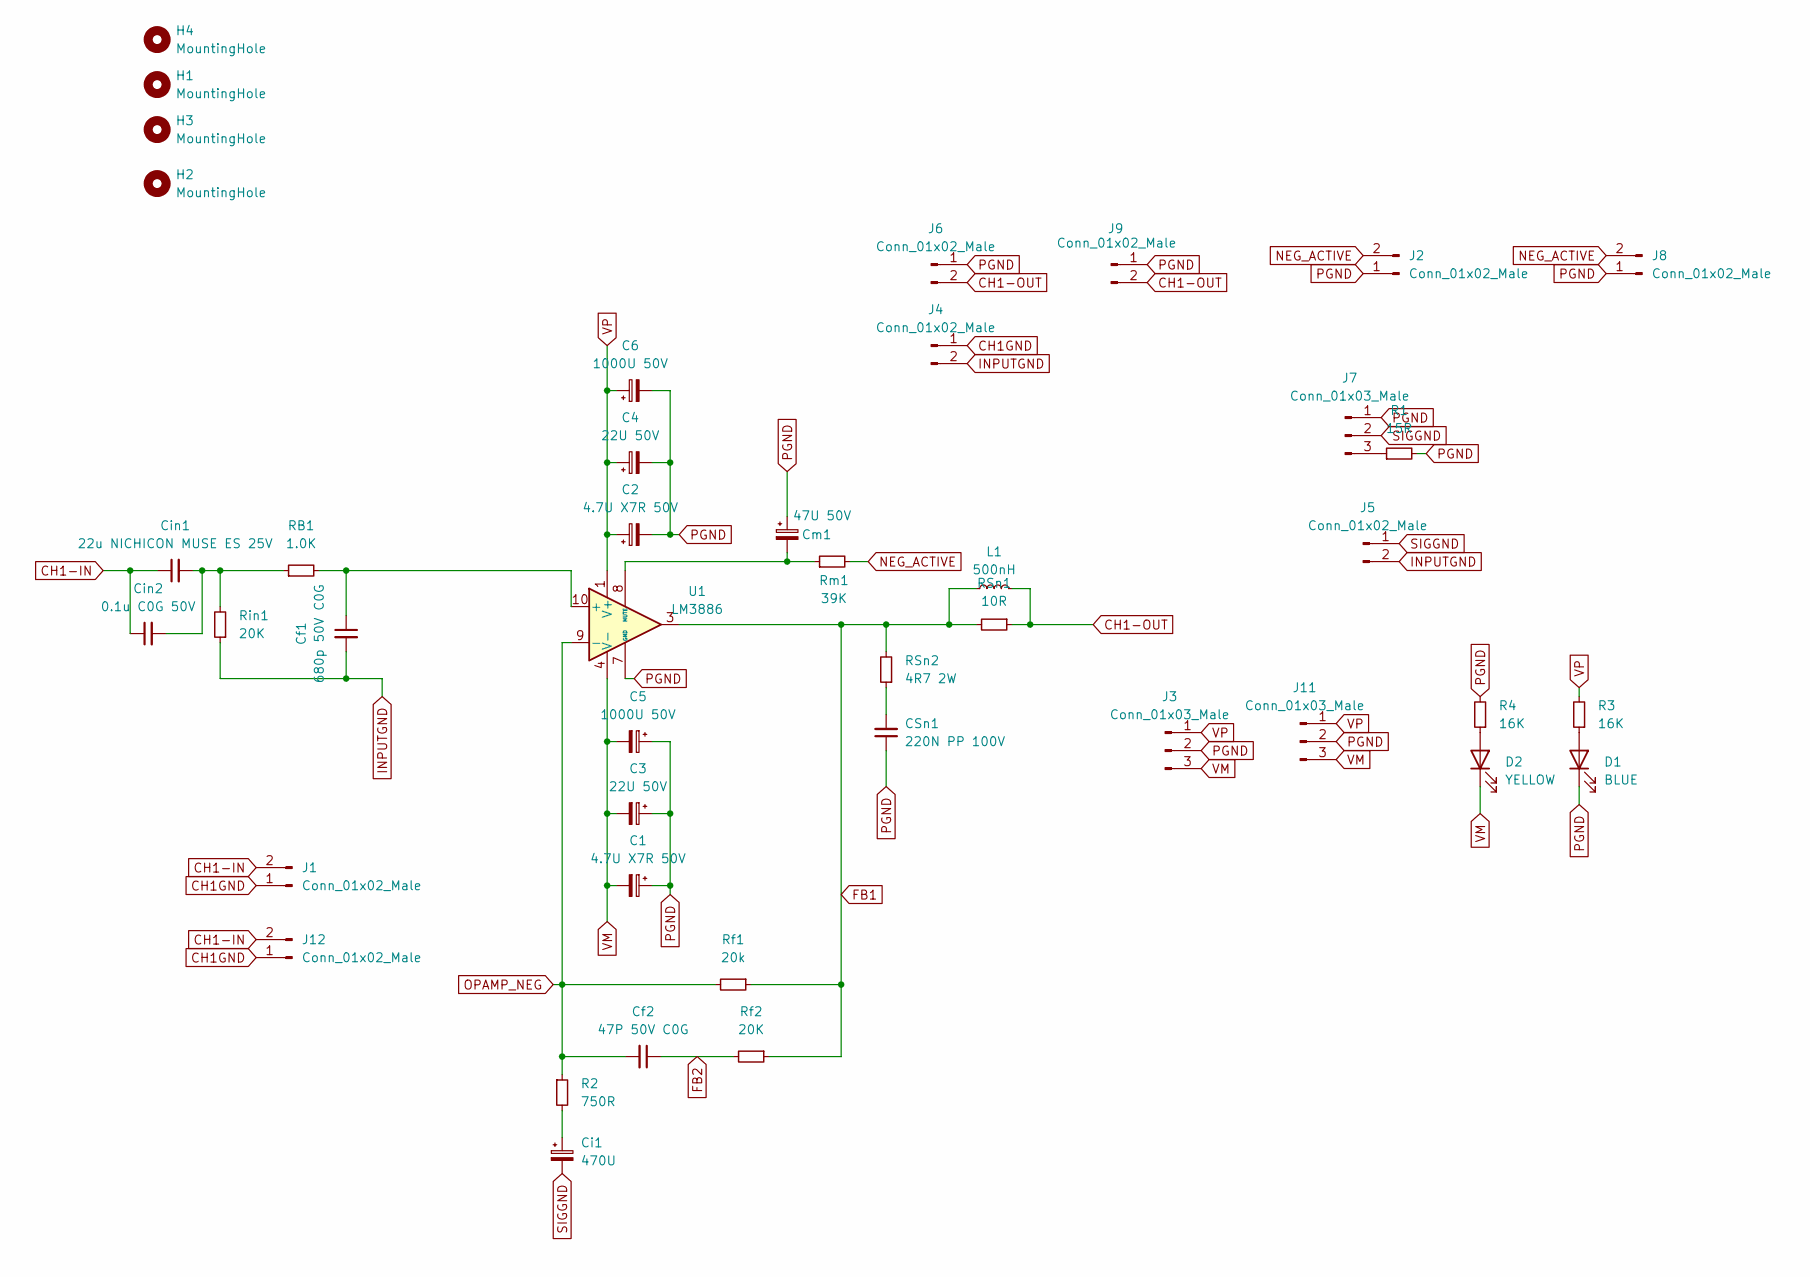
[picture p66: schematic LM3886.kicad_sch]

Parts:
C1, C2: 4.7U X7R 50V; C_1206_3216Metric_Pad1.33x1.80mm_HandSolder; Mouser 80-C1206X475J5RACTU
C3, C4: 22U 50V; CP_Radial_D6.3mm_P2.50mm
C5, C6: 1000U 50V; CP_Radial_D12.5mm_P5.00mm
CSn1: 220N PP 100V; C_Rect_L18.0mm_W7.0mm_P15.00mm_FKS3_FKP3; Mouser 505-MKP1D032204D00JB
Cf1: 680p 50V C0G; C_1206_3216Metric_Pad1.33x1.80mm_HandSolder; Mouser 603-CC126GRNPO9BN681
Cf2: 47P 50V C0G; C_1206_3216Metric_Pad1.33x1.80mm_HandSolder; Mouser 791-1206N470F500CT
Ci1: 470U; CP_Radial_D12.5mm_P5.00mm
Cin1: 22u NICHICON MUSE ES 25V; C_Radial_D6.3mm_H5.0mm_P2.50mm
Cin2: 0.1u C0G 50V; C_1206_3216Metric_Pad1.33x1.80mm_HandSolder; Mouser 81-GRT31C5C1H104FA2L
Cm1: 47U 50V; CP_Radial_D6.3mm_P2.50mm
D1: BLUE; LED_0603_1608Metric_Pad1.05x0.95mm_HandSolder
D2: YELLOW; LED_0603_1608Metric_Pad1.05x0.95mm_HandSolder
H1, H2, H3, H4: MountingHole; M3 Slot
J1, J2, J8, J12: Conn_01x02_Male; JST_PH_B2B-PH-K_1x02_P2.00mm_Vertical
J3, J11: Conn_01x03_Male; JST_VH_B3P-VH-B_1x03_P3.96mm_Vertical
J4, J5: Conn_01x02_Male; PinHeader_1x02_P2.54mm_Vertical
J6, J9: Conn_01x02_Male; JST_VH_B2P-VH_1x02_P3.96mm_Vertical
J7: Conn_01x03_Male; PinHeader_1x03_P2.54mm_Vertical
L1: 500nH; 500nH Inductor Aliexpress Air Gap
R1: 15R; R_1206_3216Metric_Pad1.30x1.75mm_HandSolder
R2: 750R; R_1206_3216Metric_Pad1.30x1.75mm_HandSolder; Mouser 603-RT1206FRE07750RL
R3, R4: 16K; R_0603_1608Metric_Pad0.98x0.95mm_HandSolder
RB1: 1.0K; R_1206_3216Metric_Pad1.30x1.75mm_HandSolder; Mouser 603-RT1206FRE131KL
RSn1: 10R; R_4020_10251Metric_Pad1.65x5.30mm_HandSolder; Mouser 279-355010RJT
RSn2: 4R7 2W; R_2512_6332Metric_Pad1.40x3.35mm_HandSolder; Mouser 603-RC2512JK-7W4R7
Rf1: 20k; R_1206_3216Metric_Pad1.30x1.75mm_HandSolder; Mouser 603-RT1206FRD0720KL
Rf2: 20K; R_1206_3216Metric_Pad1.30x1.75mm_HandSolder; Mouser 603-RT1206FRD0720KL
Rin1: 20K; R_1206_3216Metric_Pad1.30x1.75mm_HandSolder; Mouser 603-RT1206FRD0720KL
Rm1: 39K; R_1206_3216Metric_Pad1.30x1.75mm_HandSolder; Mouser 603-RC1206JR-0739KL
U1: LM3886; TO-220-11_P3.4x5.08mm_StaggerOdd_Lead4.85mm_Vertical

Connections:
CH1-IN: Cin1.1, Cin2.1, J1.2, J12.2
CH1-OUT: J6.2, J9.2, L1.2, RSn1.1
CH1GND: J1.1, J4.1, J12.1
FB1: L1.1, RSn1.2, RSn2.2, Rf1.1, Rf2.1, U1.3
FB2: Cf2.1, Rf2.2
INPUTGND: Cf1.2, J4.2, J5.2, Rin1.1
NEG_ACTIVE: J2.2, J8.2, Rm1.2
unnamed: CSn1.2, RSn2.1
unnamed: Ci1.1, R2.2
unnamed: Cin1.2, Cin2.2, RB1.1, Rin1.2
unnamed: D1.2 (A), R3.1
unnamed: D2.2 (A), R4.1
unnamed: J7.3, R1.1
unnamed: Cf1.1, RB1.2, U1.10 (+)
unnamed: Cm1.2, Rm1.1, U1.8 (MUTE)
OPAMP_NEG: Cf2.2, R2.1, Rf1.2, U1.9 (-)
PGND: C1.1, C2.2, C3.1, C4.2, C5.1, C6.2, CSn1.1, Cm1.1, D1.1 (K), J2.1, J3.2, J6.1, J7.1, J8.1, J9.1, J11.2, R1.2, R4.2, U1.7 (GND)
SIGGND: Ci1.2, J5.1, J7.2
VM: C1.2, C3.2, C5.2, D2.1 (K), J3.3, J11.3, U1.4 (V-)
VP: C2.1, C4.1, C6.1, J3.1, J11.1, R3.2, U1.1 (V+), U1.5 (V+)

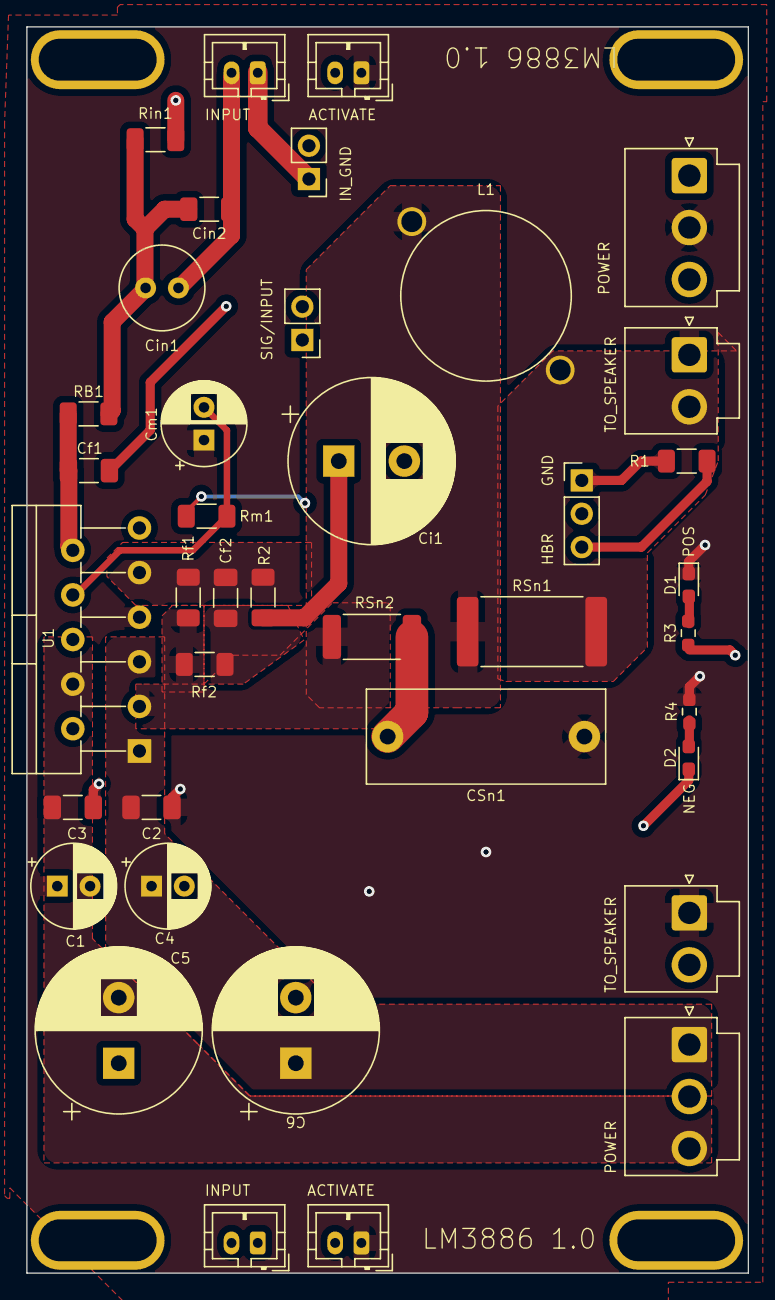
[picture p67: board LM3886.kicad_pcb from above]

Board: 4 copper layers, 55.0 x 95.0 mm, 43 parts (0 on the bottom side), 20 nets.
