duanestorey/Hifi-Amplifier/PCBs/AURORA/_Ready/Rectify/1.0/Rectify.kicad_pcb

## KiCad design PCBs/AURORA/_Ready/Rectify/1.0/Rectify.kicad_pcb (2024-12-19)

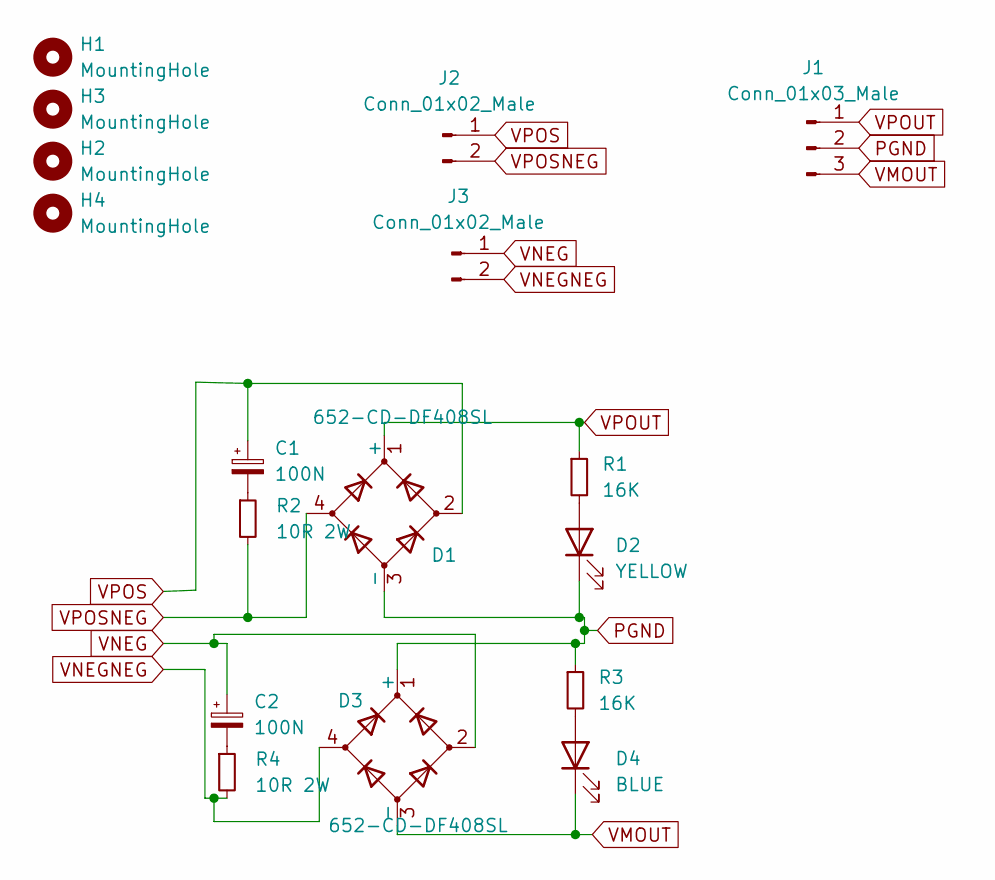
[picture p68: schematic Rectify.kicad_sch]

Parts:
C1, C2: 100N; C_Rect_L13.0mm_W6.0mm_P10.00mm_FKS3_FKP3_MKS4; Mouser 505-MKP1D031003G00JS
D1, D3: 652-CD-DF408SL; Diode_Bridge_Bourns_CD-DF4xxS; Mouser 652-CD-DF408SL
D2: YELLOW; LED_0603_1608Metric_Pad1.05x0.95mm_HandSolder
D4: BLUE; LED_0603_1608Metric_Pad1.05x0.95mm_HandSolder
H1, H2, H3, H4: MountingHole; MountingHole_3.2mm_M3_Pad_TopOnly
J1: Conn_01x03_Male; JST_VH_B3P-VH_1x03_P3.96mm_Vertical
J2, J3: Conn_01x02_Male; JST_VH_B2P-VH-B_1x02_P3.96mm_Vertical
R1, R3: 16K; R_0603_1608Metric_Pad0.98x0.95mm_HandSolder
R2, R4: 10R 2W; R_2512_6332Metric; Mouser 603-SR2512JK-7W10RL

Connections:
unnamed: C1.2, R2.1
unnamed: C2.2, R4.1
unnamed: D2.2 (A), R1.2
unnamed: D4.2 (A), R3.2
PGND: D1.3 (-), D2.1 (K), D3.1 (+), J1.2, R3.1
VMOUT: D3.3 (-), D4.1 (K), J1.3
VNEG: C2.1, D3.2, J3.1
VNEGNEG: D3.4, J3.2, R4.2
VPOS: C1.1, D1.2, J2.1
VPOSNEG: D1.4, J2.2, R2.2
VPOUT: D1.1 (+), J1.1, R1.1
