duanestorey/Hifi-Amplifier/PCBs/AURORA/_Ready/Rectify/1.0/Rectify.kicad_pcb

## KiCad design PCBs/AURORA/_Ready/Rectify/1.0/Rectify.kicad_pcb (continued)

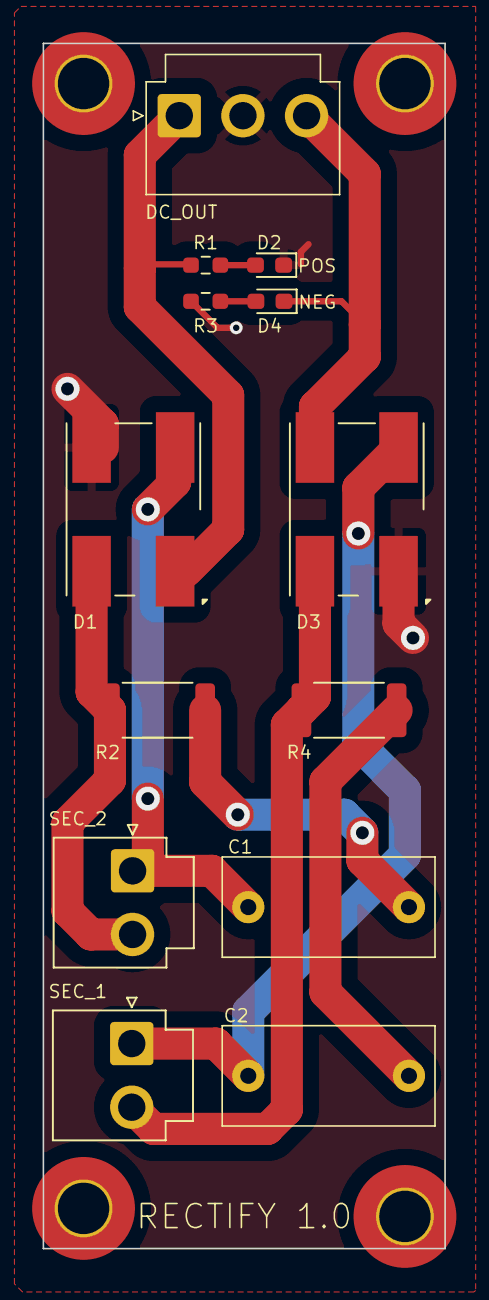
[picture p69: board Rectify.kicad_pcb from above]

Board: 2 copper layers, 25.0 x 75.0 mm, 17 parts (0 on the bottom side), 11 nets.
