duanestorey/Hifi-Amplifier/PCBs/AURORA/Subwoofer/0.1/Subwoofer.kicad_pcb

## KiCad design PCBs/_Archive/Subwoofer/0.1/Subwoofer.kicad_pcb (2024-12-08, an earlier design)

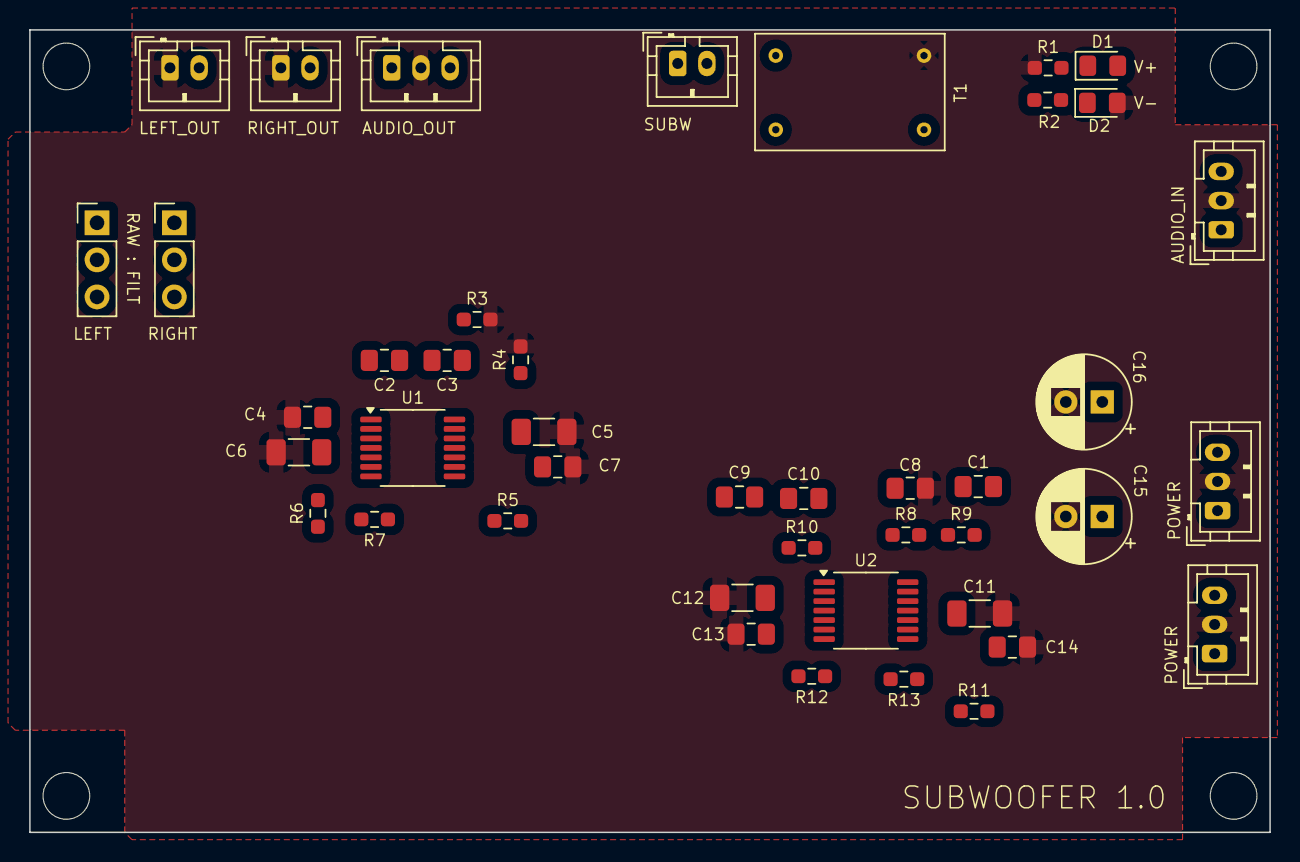
[picture p71: board Subwoofer.kicad_pcb from above]

Board: 2 copper layers, 85.0 x 55.0 mm, 47 parts (0 on the bottom side), 29 nets, no tracks yet.

Parts:
C1, C2, C3, C9, C10: 200N C0G; C_0805_2012Metric_Pad1.18x1.45mm_HandSolder
C4, C7, C13, C14: 0.1U; C_0805_2012Metric_Pad1.18x1.45mm_HandSolder
C5, C6, C11, C12: 10U; C_1206_3216Metric_Pad1.33x1.80mm_HandSolder
C8: 91N C0G; C_0805_2012Metric_Pad1.18x1.45mm_HandSolder
C15, C16: 470u; CP_Radial_D6.3mm_P2.50mm
D1: YELLOW; LED_0805_2012Metric_Pad1.15x1.40mm_HandSolder
D2: BLUE; LED_0805_2012Metric_Pad1.15x1.40mm_HandSolder
H1, H2, H3, H4: MountingHole; MountingHole_3.2mm_M3
J1, J2, J3: Conn_01x02_Pin; JST_PH_B2B-PH-K_1x02_P2.00mm_Vertical
J4, J5: Conn_01x03_Pin; PinHeader_1x03_P2.54mm_Vertical
J6, J8: Conn_01x03_Male; JST_PH_B3B-PH-K_1x03_P2.00mm_Vertical
J7, J10: Conn_01x03_Pin; JST_PH_B3B-PH-K_1x03_P2.00mm_Vertical
R1: 1.25K; R_0603_1608Metric_Pad0.98x0.95mm_HandSolder
R2: 1K; R_0603_1608Metric_Pad0.98x0.95mm_HandSolder
R3, R4, R5, R6: 6.8K; R_0603_1608Metric_Pad0.98x0.95mm_HandSolder
R7: 25k; R_0603_1608Metric_Pad0.98x0.95mm_HandSolder
R8: 20K; R_0603_1608Metric_Pad0.98x0.95mm_HandSolder
R9: 11K; R_0603_1608Metric_Pad0.98x0.95mm_HandSolder
R10, R11, R12, R13: 25K; R_0603_1608Metric_Pad0.98x0.95mm_HandSolder
T1: Transformer_Audio; DA101C
U1, U2: Opamp_Quad; TSSOP-14_4.4x5mm_P0.65mm

Connections:
AGND: C4.2, C5.2, C6.2, C7.2, C8.1, C11.2, C12.2, C13.2, C14.2, C15.2, C16.2, D2.2 (A), J2.1, J3.1, J6.2, J7.2, J8.2, J10.2, R1.1, R3.2, R4.2, T1.2 (AB), U1.12 (+)
LEFT_FILT: J5.3, R5.1, U1.8, U1.9 (-)
LEFT_IN: J5.1, J10.1, U2.3 (+)
LEFT_OUT: J3.2, J5.2, J7.1
unnamed: C1.2, R8.2, R9.1
unnamed: C2.1, C3.2, R6.2
unnamed: C9.2, C10.1, R5.2
unnamed: D1.1 (K), R1.2
unnamed: D2.1 (K), R2.2
unnamed: R10.1, R13.2, U2.7
unnamed: R9.2, R11.1, U2.8
unnamed: C2.2, R7.2, U1.1, U1.2 (-)
unnamed: C3.1, R3.1, U1.5 (+)
unnamed: C9.1, R4.1, U1.10 (+)
unnamed: U1.13 (-), U1.14
unnamed: C10.2, R12.2, U2.1, U2.2 (-)
unnamed: R10.2, U2.5 (+)
unnamed: R7.1, R12.1, U2.6 (-)
unnamed: R11.2, U2.10 (+)
unnamed: R13.1, U2.9 (-)
unnamed: C8.2, R8.1, U2.12 (+)
RIGHT_FILT: J4.3, R6.1, U1.6 (-), U1.7
RIGHT_IN: J4.1, J10.3, U1.3 (+)
RIGHT_OUT: J2.2, J4.2, J7.3
SUBW: C1.1, T1.1 (AA), U2.13 (-), U2.14
SUBWN: J1.1, T1.3 (SA)
SUBWP: J1.2, T1.4 (SB)
V+: C4.1, C6.1, C12.1, C13.1, C15.1, D1.2 (A), J6.3, J8.3, U1.4 (V+), U2.4 (V+)
V-: C5.1, C7.1, C11.1, C14.1, C16.1, J6.1, J8.1, R2.1, U1.11 (V-), U2.11 (V-)
