duanestorey/Hifi-Amplifier/PCBs/AURORA/_Ready/Mono/1.0/Mono.kicad_pcb

## KiCad design PCBs/AURORA/_Ready/Mono/1.0/Mono.kicad_pcb (2024-12-19)

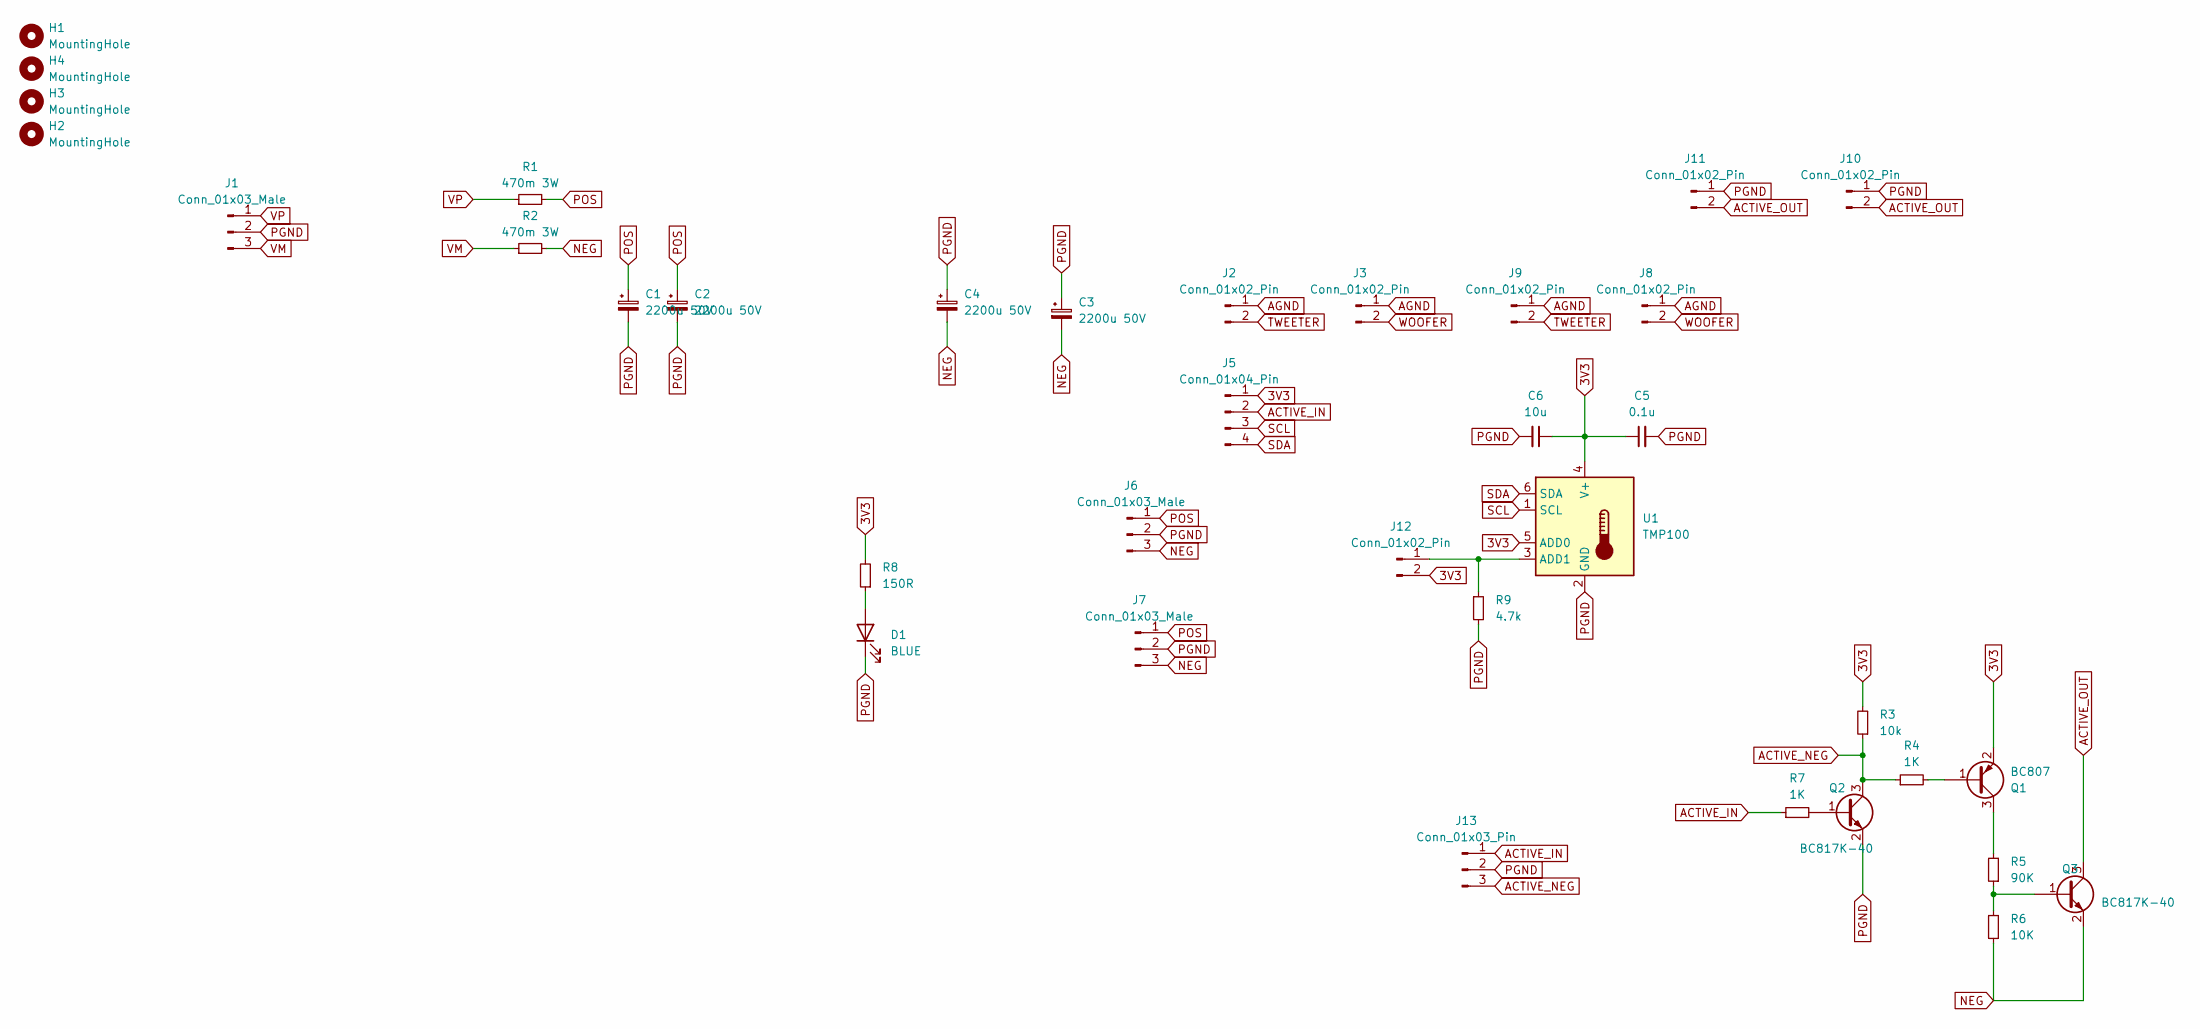
[picture p72: schematic Mono.kicad_sch]

Parts:
C1, C2, C3, C4: 2200u 50V; CP_Radial_D16.0mm_P7.50mm; Mouser 80-ESH228M050AM3AA
C5: 0.1u; C_0805_2012Metric_Pad1.18x1.45mm_HandSolder
C6: 10u; C_1206_3216Metric_Pad1.33x1.80mm_HandSolder
D1: BLUE; LED_0603_1608Metric_Pad1.05x0.95mm_HandSolder
H1, H2, H3, H4: MountingHole; MountingHole_3.2mm_M3_DIN965_Pad_TopOnly
J1, J6, J7: Conn_01x03_Male; JST_VH_B3P-VH-B_1x03_P3.96mm_Vertical
J2, J3, J8, J9, J10, J11: Conn_01x02_Pin; JST_PH_B2B-PH-K_1x02_P2.00mm_Vertical
J5: Conn_01x04_Pin; JST_PH_B4B-PH-K_1x04_P2.00mm_Vertical
J12: Conn_01x02_Pin; PinHeader_1x02_P2.54mm_Vertical
J13: Conn_01x03_Pin; JST_PH_B3B-PH-K_1x03_P2.00mm_Vertical
Q1: BC807; TSOT-23; Mouser 637-BC807-16
Q2, Q3: BC817K-40; TSOT-23; Mouser 637-BC817K-40
R1, R2: 470m 3W; R_1218_3246Metric_Pad1.22x4.75mm_HandSolder; Mouser RLW73PA3FR47TDF
R3: 10k; R_0603_1608Metric_Pad0.98x0.95mm_HandSolder
R4, R7: 1K; R_0603_1608Metric_Pad0.98x0.95mm_HandSolder
R5: 90K; R_0603_1608Metric_Pad0.98x0.95mm_HandSolder
R6: 10K; R_0603_1608Metric_Pad0.98x0.95mm_HandSolder
R8: 150R; R_0603_1608Metric_Pad0.98x0.95mm_HandSolder
R9: 4.7k; R_0603_1608Metric_Pad0.98x0.95mm_HandSolder
U1: TMP100; SOT-23-6

Connections:
3V3: C5.1, C6.1, J5.1, J12.2, Q1.2 (E), R3.2, R8.2, U1.4 (V+), U1.5 (ADD0)
ACTIVE_IN: J5.2, J13.1, R7.1
ACTIVE_NEG: J13.3, Q2.3 (C), R3.1, R4.1
ACTIVE_OUT: J10.2, J11.2, Q3.3 (C)
AGND: J2.1, J3.1, J8.1, J9.1
NEG: C3.2, C4.2, J6.3, J7.3, Q3.2 (E), R2.2, R6.1
unnamed: D1.2 (A), R8.1
unnamed: J12.1, R9.1, U1.3 (ADD1)
unnamed: Q1.1 (B), R4.2
unnamed: Q1.3 (C), R5.2
unnamed: Q2.1 (B), R7.2
unnamed: Q3.1 (B), R5.1, R6.2
PGND: C1.2, C2.2, C3.1, C4.1, C5.2, C6.2, D1.1 (K), J1.2, J6.2, J7.2, J10.1, J11.1, J13.2, Q2.2 (E), R9.2, U1.2 (GND)
POS: C1.1, C2.1, J6.1, J7.1, R1.2
SCL: J5.3, U1.1 (SCL)
SDA: J5.4, U1.6 (SDA)
TWEETER: J2.2, J9.2
VM: J1.3, R2.1
VP: J1.1, R1.1
WOOFER: J3.2, J8.2

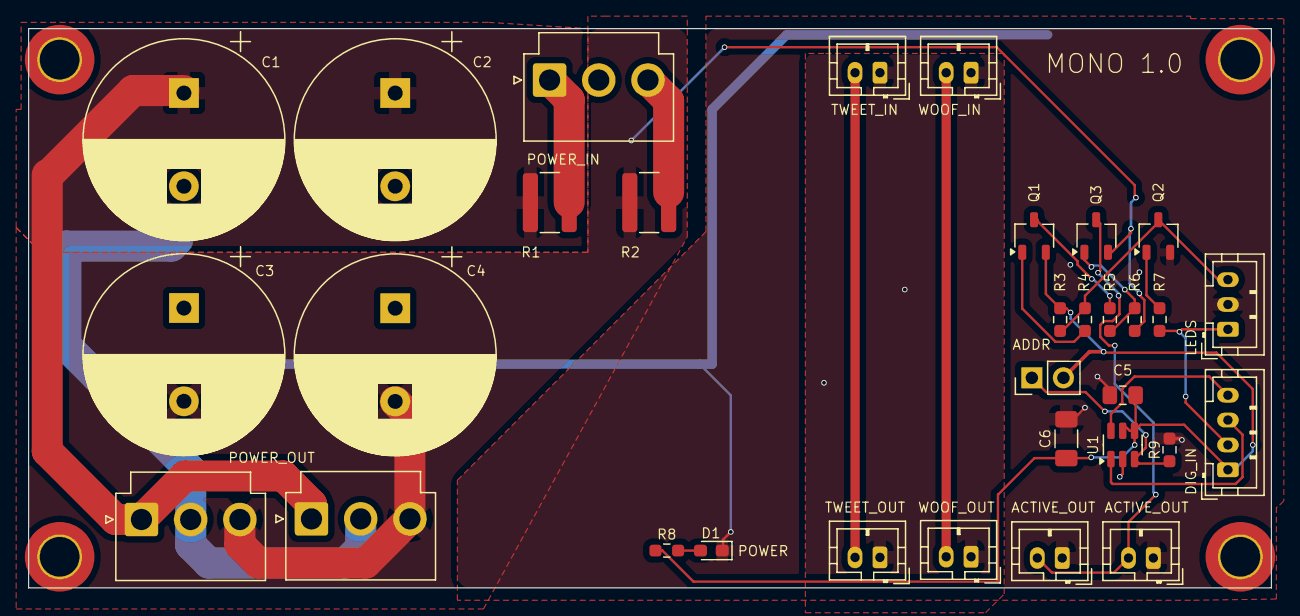
[picture p73: board Mono.kicad_pcb from above]

Board: 2 copper layers, 100.0 x 45.0 mm, 36 parts (0 on the bottom side), 20 nets.
