duanestorey/Hifi-Amplifier/PCBs/AURORA/InputSel/0.2/InputSel.kicad_pcb

## KiCad design PCBs/AURORA/InputSel/0.2/InputSel.kicad_pcb (2024-12-19)

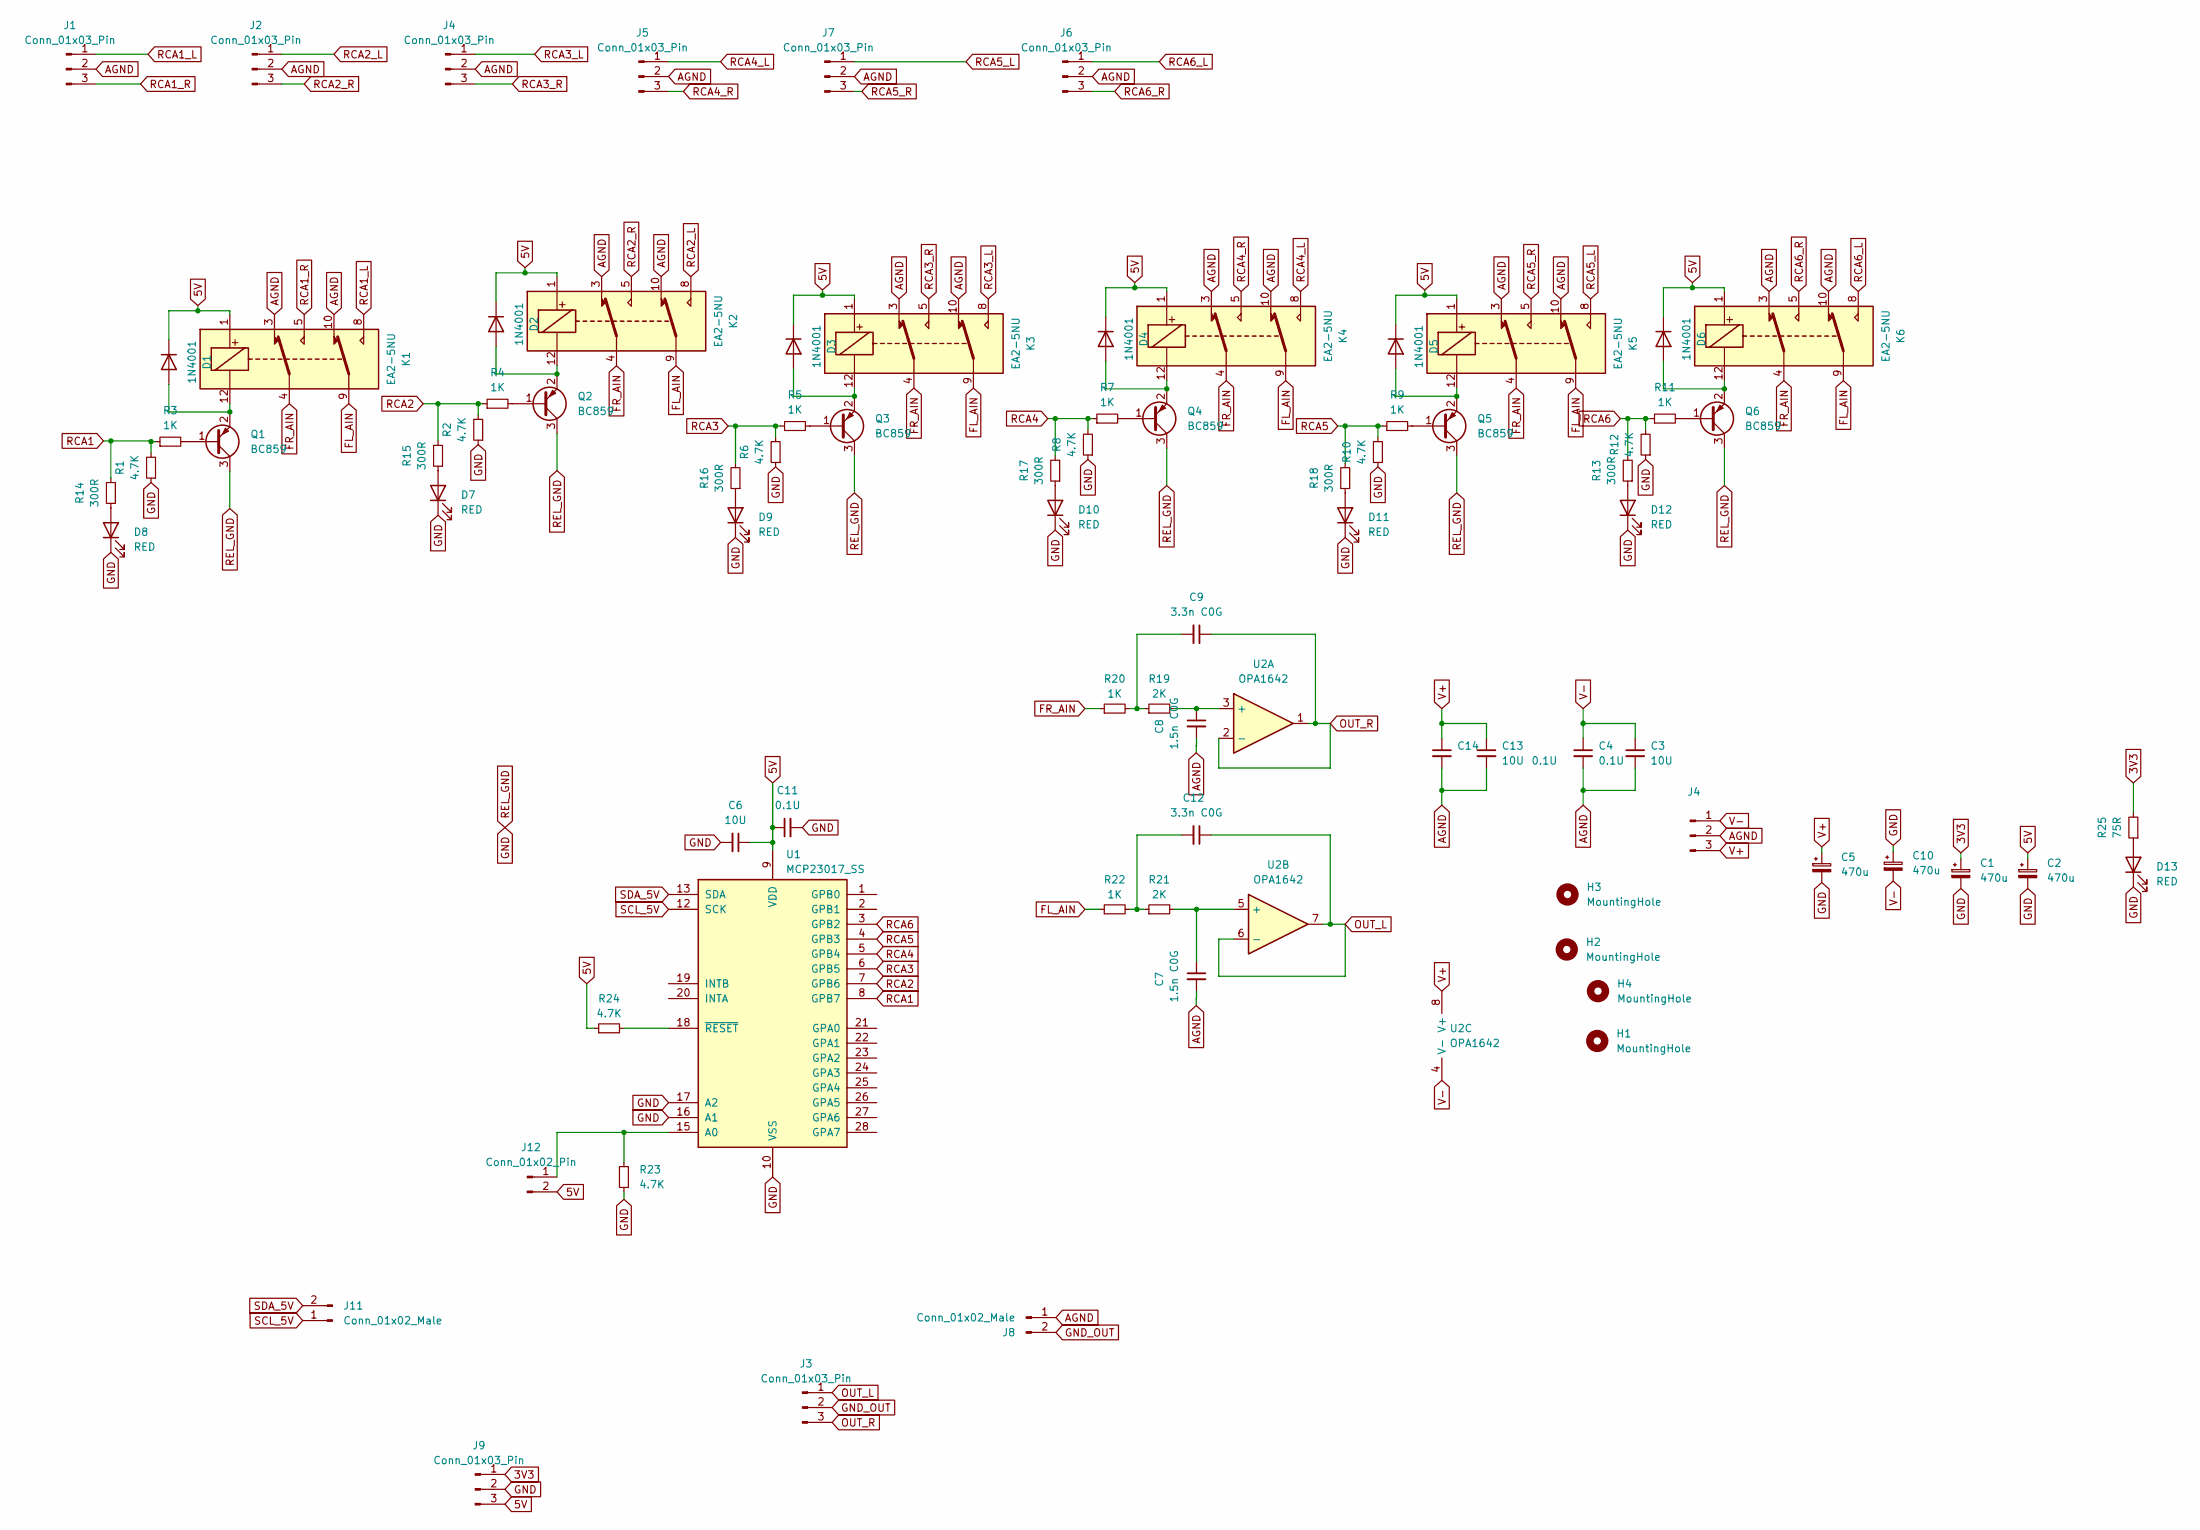
[picture p74: schematic InputSel.kicad_sch]

Parts:
C1, C2, C5, C10: 470u; CP_Radial_D6.3mm_P2.50mm
C3, C6, C13: 10U; C_1206_3216Metric_Pad1.33x1.80mm_HandSolder
C4, C11, C14: 0.1U; C_0805_2012Metric_Pad1.18x1.45mm_HandSolder
C7, C8: 1.5n C0G; C_0805_2012Metric_Pad1.18x1.45mm_HandSolder
C9, C12: 3.3n C0G; C_0805_2012Metric_Pad1.18x1.45mm_HandSolder
D1, D2, D3, D4, D5, D6: 1N4001; D_SMA
D7, D8, D9, D10, D11, D12, D13: RED; LED_0805_2012Metric
H1, H2, H3, H4: MountingHole; MountingHole_3.2mm_M3
J1, J2, J3, J5, J6, J7, J9: Conn_01x03_Pin; JST_PH_B3B-PH-K_1x03_P2.00mm_Vertical
J4: Conn_01x03_Male; JST_PH_B3B-PH-K_1x03_P2.00mm_Vertical
J8: Conn_01x02_Male; PinHeader_1x02_P2.54mm_Vertical
J11: Conn_01x02_Male; JST_PH_B2B-PH-K_1x02_P2.00mm_Vertical
J12: Conn_01x02_Pin; PinHeader_1x02_P2.54mm_Vertical
K1, K2, K3, K4, K5, K6: EA2-5NU; KEMET EA2
Q1, Q2, Q3, Q4, Q5, Q6: BC859; SOT-23
R1, R2, R6, R8, R10, R12, R23, R24: 4.7K; R_0603_1608Metric_Pad0.98x0.95mm_HandSolder
R3, R4, R5, R7, R9, R11, R20, R22: 1K; R_0603_1608Metric_Pad0.98x0.95mm_HandSolder
R13, R14, R15, R16, R17, R18: 300R; R_0603_1608Metric_Pad0.98x0.95mm_HandSolder
R19, R21: 2K; R_0603_1608Metric_Pad0.98x0.95mm_HandSolder
R25: 75R; R_0603_1608Metric_Pad0.98x0.95mm_HandSolder
U1: MCP23017_SS; SSOP-28_5.3x10.2mm_P0.65mm
U2: OPA1642; VSSOP-8_3x3mm_P0.65mm

Connections:
3V3: C1.1, J9.1, R25.2
5V: C2.1, C6.1, C11.1, D1.1 (K), D2.1 (K), D3.1 (K), D4.1 (K), D5.1 (K), D6.1 (K), J9.3, J12.2, K1.1, K2.1, K3.1, K4.1, K5.1, K6.1, R24.1, U1.9 (VDD)
AGND: C3.2, C4.2, C7.2, C8.2, C13.2, C14.2, J1.2, J2.2, J4.2, J5.2, J6.2, J7.2, J8.1, K1.3, K1.10, K2.3, K2.10, K3.3, K3.10, K4.3, K4.10, K5.3, K5.10, K6.3, K6.10; also elsewhere on the board
FL_AIN: K1.9, K2.9, K3.9, K4.9, K5.9, K6.9, R22.1
FR_AIN: K1.4, K2.4, K3.4, K4.4, K5.4, K6.4, R20.1
GND: C1.2, C2.2, C5.2, C6.2, C10.1, C11.2, D7.1 (K), D8.1 (K), D9.1 (K), D10.1 (K), D11.1 (K), D12.1 (K), D13.1 (K), J9.2, Q1.3 (C), Q2.3 (C), Q3.3 (C), Q4.3 (C), Q5.3 (C), Q6.3 (C), R1.1, R2.1, R6.1, R8.1, R10.1, R12.1, R23.1, U1.10 (VSS), U1.16 (A1), U1.17 (A2)
GND_OUT: J3.2, J8.2
unnamed: C9.2, R19.1, R20.2
unnamed: C12.2, R21.1, R22.2
unnamed: D1.2 (A), K1.12, Q1.2 (E)
unnamed: D2.2 (A), K2.12, Q2.2 (E)
unnamed: D3.2 (A), K3.12, Q3.2 (E)
unnamed: D4.2 (A), K4.12, Q4.2 (E)
unnamed: D5.2 (A), K5.12, Q5.2 (E)
unnamed: D6.2 (A), K6.12, Q6.2 (E)
unnamed: D7.2 (A), R15.1
unnamed: D8.2 (A), R14.1
unnamed: D9.2 (A), R16.1
unnamed: D10.2 (A), R17.1
unnamed: D11.2 (A), R18.1
unnamed: D12.2 (A), R13.1
unnamed: D13.2 (A), R25.1
unnamed: J12.1, R23.2, U1.15 (A0)
unnamed: Q1.1 (B), R3.2
unnamed: Q2.1 (B), R4.2
unnamed: Q3.1 (B), R5.2
unnamed: Q4.1 (B), R7.2
unnamed: Q5.1 (B), R9.2
unnamed: Q6.1 (B), R11.2
unnamed: R24.2, U1.18 (~RESET)
unnamed: C8.1, R19.2, U2.3 (+)
unnamed: C7.1, R21.2, U2.5 (+)
OUT_L: C12.1, J3.1, U2.6 (-), U2.7
OUT_R: C9.1, J3.3, U2.1, U2.2 (-)
RCA1: R1.2, R3.1, R14.2, U1.8 (GPB7)
RCA1_L: J1.1, K1.8
RCA1_R: J1.3, K1.5
RCA2: R2.2, R4.1, R15.2, U1.7 (GPB6)
RCA2_L: J2.1, K2.8
RCA2_R: J2.3, K2.5
RCA3: R5.1, R6.2, R16.2, U1.6 (GPB5)
RCA4: R7.1, R8.2, R17.2, U1.5 (GPB4)
RCA4_L: J5.1, K4.8
RCA4_R: J5.3, K4.5
RCA5: R9.1, R10.2, R18.2, U1.4 (GPB3)
RCA5_L: J7.1, K5.8
RCA5_R: J7.3, K5.5
RCA6: R11.1, R12.2, R13.2, U1.3 (GPB2)
RCA6_L: J6.1, K6.8
RCA6_R: J6.3, K6.5
SCL_5V: J11.1, U1.12 (SCK)
SDA_5V: J11.2, U1.13 (SDA)

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
Board: 4 copper layers, 82 parts (0 on the bottom side), 56 nets, no tracks yet.

Other parts of the board:
J10: Conn_01x03_Male; JST_PH_B3B-PH-K_1x03_P2.00mm_Vertical

Their connections:
AGND: J10.2; also elsewhere on the board
