duanestorey/Hifi-Amplifier/PCBs/AURORA/DualPSU/1.0/DualPSU.kicad_pcb

## KiCad design PCBs/AURORA/DualPSU/1.0/DualPSU.kicad_pcb (2024-12-19)

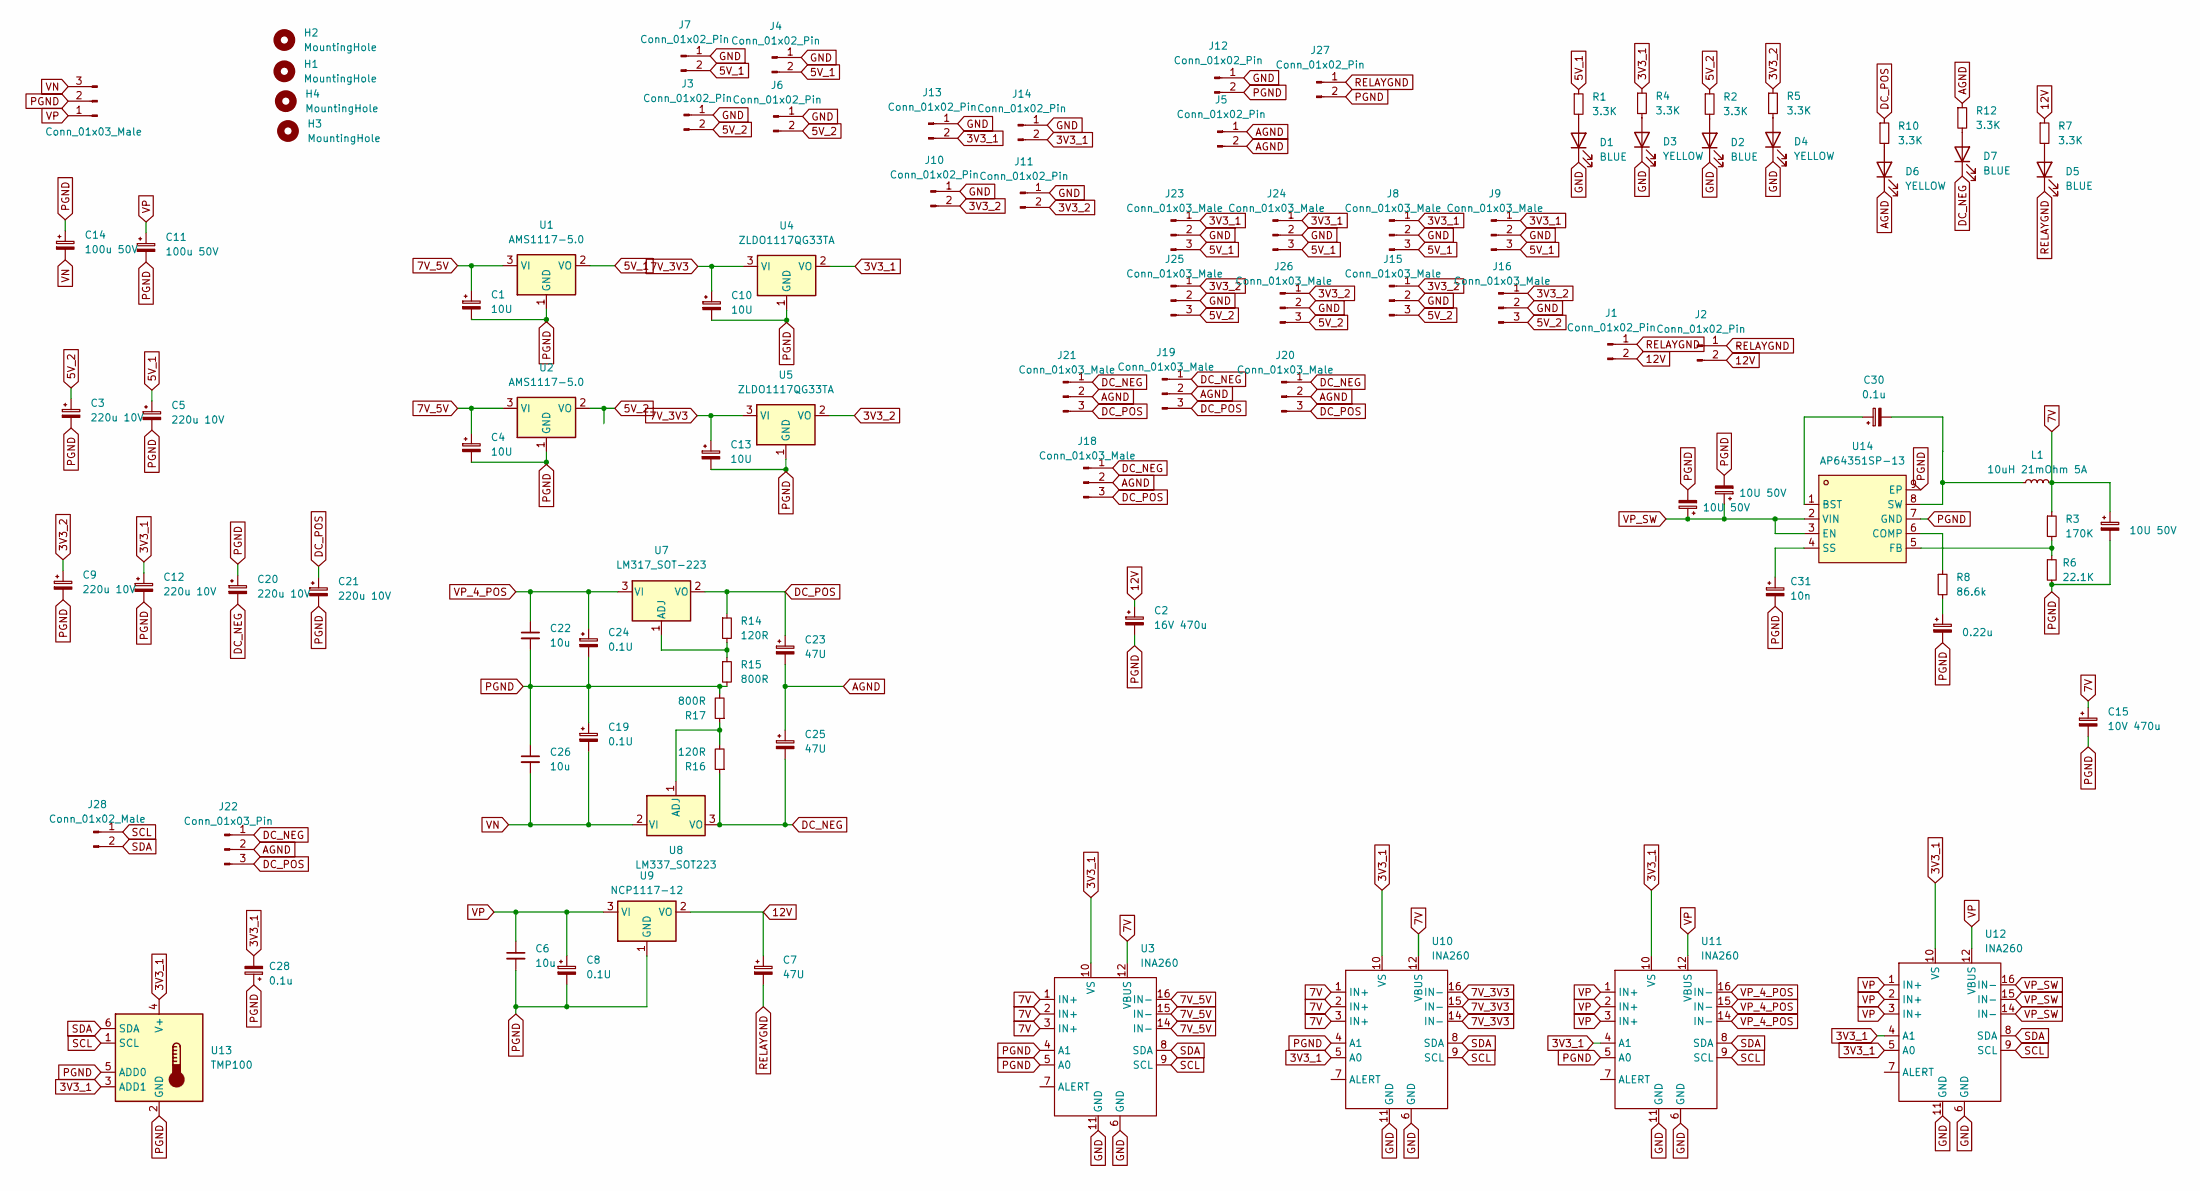
[picture p75: schematic DualPSU.kicad_sch]

Parts:
C1, C4, C10, C13: 10U; C_1206_3216Metric_Pad1.33x1.80mm_HandSolder
C2: 16V 470u; CP_Radial_D8.0mm_P3.50mm
C3, C5, C9, C12, C20, C21: 220u 10V; CP_Radial_D6.3mm_P2.50mm
C6, C22, C26: 10u; C_1206_3216Metric_Pad1.33x1.80mm_HandSolder
C7, C23, C25: 47U; C_1206_3216Metric_Pad1.33x1.80mm_HandSolder
C8, C19, C24: 0.1U; C_0603_1608Metric_Pad1.08x0.95mm_HandSolder
C11, C14: 100u 50V; CP_Radial_D8.0mm_P3.50mm
C15: 10V 470u; CP_Radial_D8.0mm_P3.50mm
C16, C18, C29: 10U 50V; C_1206_3216Metric_Pad1.33x1.80mm_HandSolder
C27: 0.22u; C_0805_2012Metric_Pad1.18x1.45mm_HandSolder
C28, C30: 0.1u; C_0805_2012Metric_Pad1.18x1.45mm_HandSolder
C31: 10n; C_0805_2012Metric_Pad1.18x1.45mm_HandSolder
D1, D2, D5, D7: BLUE; LED_0805_2012Metric_Pad1.15x1.40mm_HandSolder
D3, D4, D6: YELLOW; LED_0805_2012Metric_Pad1.15x1.40mm_HandSolder
H1, H2, H3, H4: MountingHole; MountingHole_3.2mm_M3_DIN965_Pad_TopOnly
J1, J2, J3, J4, J5, J6, J7, J10, J11, J13, J14: Conn_01x02_Pin; JST_PH_B2B-PH-K_1x02_P2.00mm_Vertical
J8, J9, J15, J16, J18, J19, J20, J21, J23, J24, J25, J26: Conn_01x03_Male; JST_PH_B3B-PH-K_1x03_P2.00mm_Vertical
J12, J27: Conn_01x02_Pin; PinHeader_1x02_P2.54mm_Vertical
J17: Conn_01x03_Male; JST_VH_B3P-VH_1x03_P3.96mm_Vertical
J22: Conn_01x03_Pin; PinHeader_1x03_P2.54mm_Vertical
J28: Conn_01x02_Male; JST_PH_B2B-PH-K_1x02_P2.00mm_Vertical
L1: 10uH 21mOhm 5A; L_Vishay_IHLP-4040; Mouser 704-DR1040-7R0-R
R1, R2, R4, R5, R7, R10, R12: 3.3K; R_0603_1608Metric_Pad0.98x0.95mm_HandSolder
R3: 170K; R_0603_1608Metric_Pad0.98x0.95mm_HandSolder
R6: 22.1K; R_0603_1608Metric_Pad0.98x0.95mm_HandSolder; Mouser 603-RC0603JR-07820KP
R8: 86.6k; R_0603_1608Metric_Pad0.98x0.95mm_HandSolder; Mouser 71-CRCW0603-86.6K-E3
R14, R16: 120R; R_0603_1608Metric_Pad0.98x0.95mm_HandSolder
R15, R17: 800R; R_0603_1608Metric_Pad0.98x0.95mm_HandSolder
U1, U2: AMS1117-5.0; SOT-223-3_TabPin2; Mouser 926-LM1117MPX5.0NOPB
U3, U10, U11, U12: INA260; TSSOP-16_4.4x5mm_P0.65mm
U4, U5: ZLDO1117QG33TA; SOT-223-3_TabPin2; Mouser ZLDO1117QG33TA
U7: LM317_SOT-223; SOT-223-3_TabPin2; Mouser 595-LM317DCY
U8: LM337_SOT223; SOT-223-3_TabPin2; Mouser 926-LM337IMPX/NOPB
U9: NCP1117-12; SOT-223; Mouser 863-NCP1117ST12T3G
U13: TMP100; SOT-23-6; Mouser 595-TMP100NA/3K
U14: AP64351SP-13; SOIC-8_L4.9-W3.9-P1.27-LS6.0-BL-EP; LCSC Part C3192339

Connections:
3V3_1: C12.1, C28.2, J8.1, J9.1, J13.2, J14.2, J23.1, J24.1, R4.1, U3.10 (VS), U4.2 (VO), U10.5 (A0), U10.10 (VS), U11.4 (A1), U11.10 (VS), U12.4 (A1), U12.5 (A0), U12.10 (VS), U13.3 (ADD1), U13.4 (V+)
3V3_2: C9.1, J10.2, J11.2, J15.1, J16.1, J25.1, J26.1, R5.1, U5.2 (VO)
5V_1: C5.1, J4.2, J7.2, J8.3, J9.3, J23.3, J24.3, R1.1, U1.2 (VO)
5V_2: C3.1, J3.2, J6.2, J15.3, J16.3, J25.3, J26.3, R2.1, U2.2 (VO)
7V: C15.1, C18.1, L1.2, R3.1, U3.1 (IN+), U3.2 (IN+), U3.3 (IN+), U3.12 (VBUS), U10.1 (IN+), U10.2 (IN+), U10.3 (IN+), U10.12 (VBUS)
7V_3V3: C10.1, C13.1, U4.3 (VI), U5.3 (VI), U10.14 (IN-), U10.15 (IN-), U10.16 (IN-)
7V_5V: C1.1, C4.1, U1.3 (VI), U2.3 (VI), U3.14 (IN-), U3.15 (IN-), U3.16 (IN-)
12V: C2.1, C7.1, J1.2, J2.2, R7.1, U9.2 (VO)
AGND: C23.2, C25.1, D6.1 (K), J5.1, J5.2, J18.2, J19.2, J20.2, J21.2, J22.2, R12.1
DC_NEG: C20.2, C25.2, D7.1 (K), J18.1, J19.1, J20.1, J21.1, J22.1, R16.1, U8.3 (VO)
DC_POS: C21.1, C23.1, J18.3, J19.3, J20.3, J21.3, J22.3, R10.1, R14.1, U7.2 (VO)
GND: D1.1 (K), D2.1 (K), D3.1 (K), D4.1 (K), J3.1, J4.1, J6.1, J7.1, J8.2, J9.2, J10.1, J11.1, J12.1, J13.1, J14.1, J15.2, J16.2, J23.2, J24.2, J25.2, J26.2, U3.6 (GND), U3.11 (GND), U10.6 (GND), U10.11 (GND), U11.6 (GND), U11.11 (GND), U12.6 (GND), U12.11 (GND)
unnamed: C27.1, R8.2
unnamed: D1.2 (A), R1.2
unnamed: D2.2 (A), R2.2
unnamed: D3.2 (A), R4.2
unnamed: D4.2 (A), R5.2
unnamed: D5.2 (A), R7.2
unnamed: D6.2 (A), R10.2
unnamed: D7.2 (A), R12.2
unnamed: R14.2, R15.1, U7.1 (ADJ)
unnamed: R16.2, R17.1, U8.1 (ADJ)
unnamed: C30.1, U14.1 (BST)
unnamed: R8.1, U14.6 (COMP)
unnamed: R3.2, R6.1, U14.5 (FB)
unnamed: C31.1, U14.4 (SS)
unnamed: C30.2, L1.1, U14.8 (SW)
PGND: C1.2, C2.2, C3.2, C4.2, C5.2, C6.2, C8.2, C9.2, C10.2, C11.2, C12.2, C13.2, C14.1, C15.2, C16.2, C18.2, C19.1, C20.1, C21.2, C22.2, C24.2, C26.1, C27.2, C28.1, C29.2, C31.2, J12.2, J17.2, J27.2, R6.2, R15.2, R17.2, U1.1 (GND), U2.1 (GND), U3.4 (A1), U3.5 (A0), U4.1 (GND), U5.1 (GND), U9.1 (GND), U10.4 (A1), U11.5 (A0), U13.2 (GND), U13.5 (ADD0), U14.7 (GND), U14.9 (EP)
RELAYGND: C7.2, D5.1 (K), J1.1, J2.1, J27.1
SCL: J28.1, U3.9 (SCL), U10.9 (SCL), U11.9 (SCL), U12.9 (SCL), U13.1 (SCL)
SDA: J28.2, U3.8 (SDA), U10.8 (SDA), U11.8 (SDA), U12.8 (SDA), U13.6 (SDA)
VN: C14.2, C19.2, C26.2, J17.3, U8.2 (VI)
VP: C6.1, C8.1, C11.1, J17.1, U9.3 (VI), U11.1 (IN+), U11.2 (IN+), U11.3 (IN+), U11.12 (VBUS), U12.1 (IN+), U12.2 (IN+), U12.3 (IN+), U12.12 (VBUS)
VP_4_POS: C22.1, C24.1, U7.3 (VI), U11.14 (IN-), U11.15 (IN-), U11.16 (IN-)
VP_SW: C16.1, C29.1, U12.14 (IN-), U12.15 (IN-), U12.16 (IN-), U14.2 (VIN), U14.3 (EN)

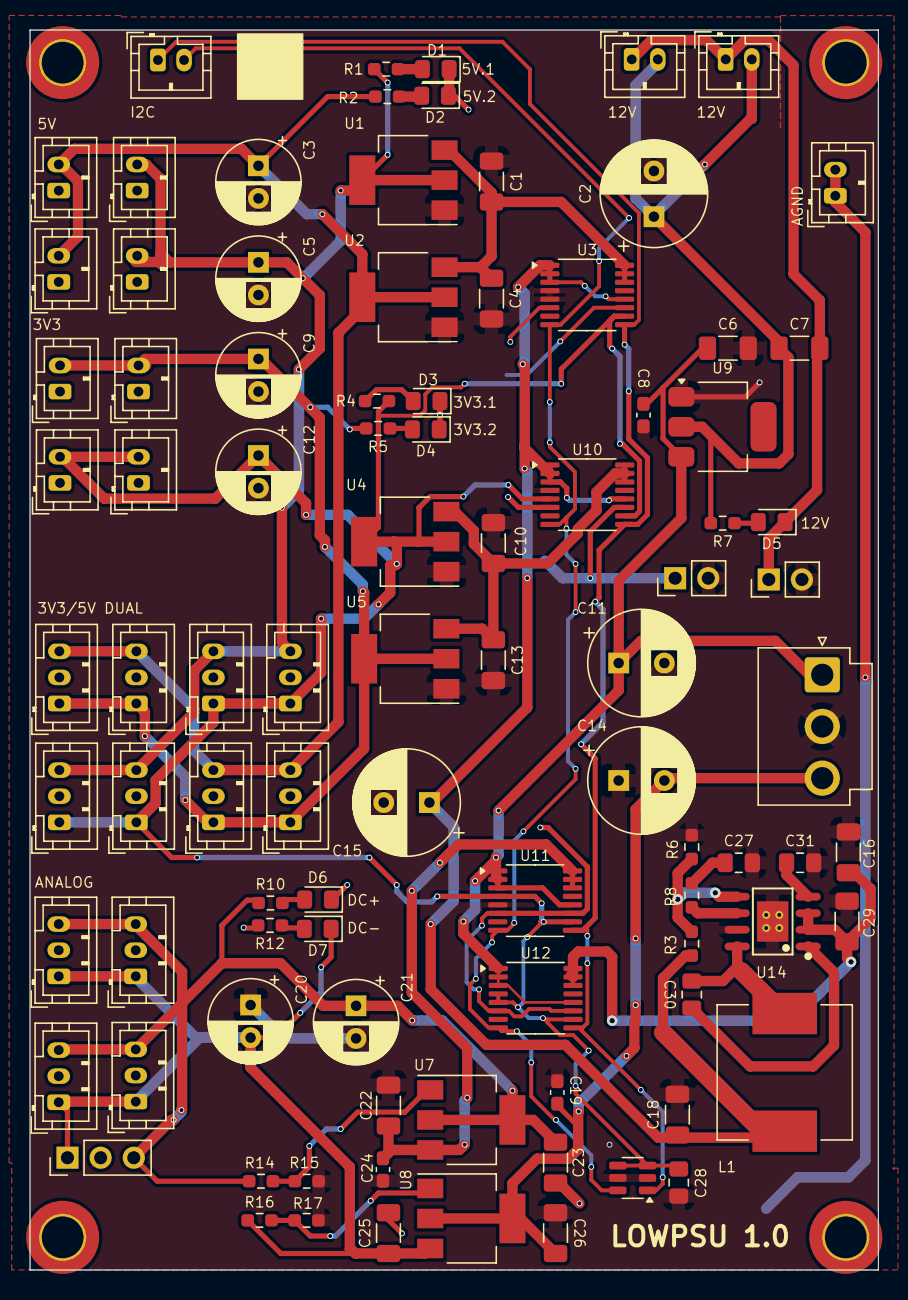
[picture p76: board DualPSU.kicad_pcb from above]

Board: 2 copper layers, 65.0 x 95.0 mm, 97 parts (0 on the bottom side), 35 nets.
