duanestorey/Hifi-Amplifier/PCBs/AURORA/_Ready/Vinyl/1.0/Vinyl.kicad_pcb

## KiCad design PCBs/AURORA/_Ready/Vinyl/1.0/Vinyl.kicad_pcb (2024-12-19)

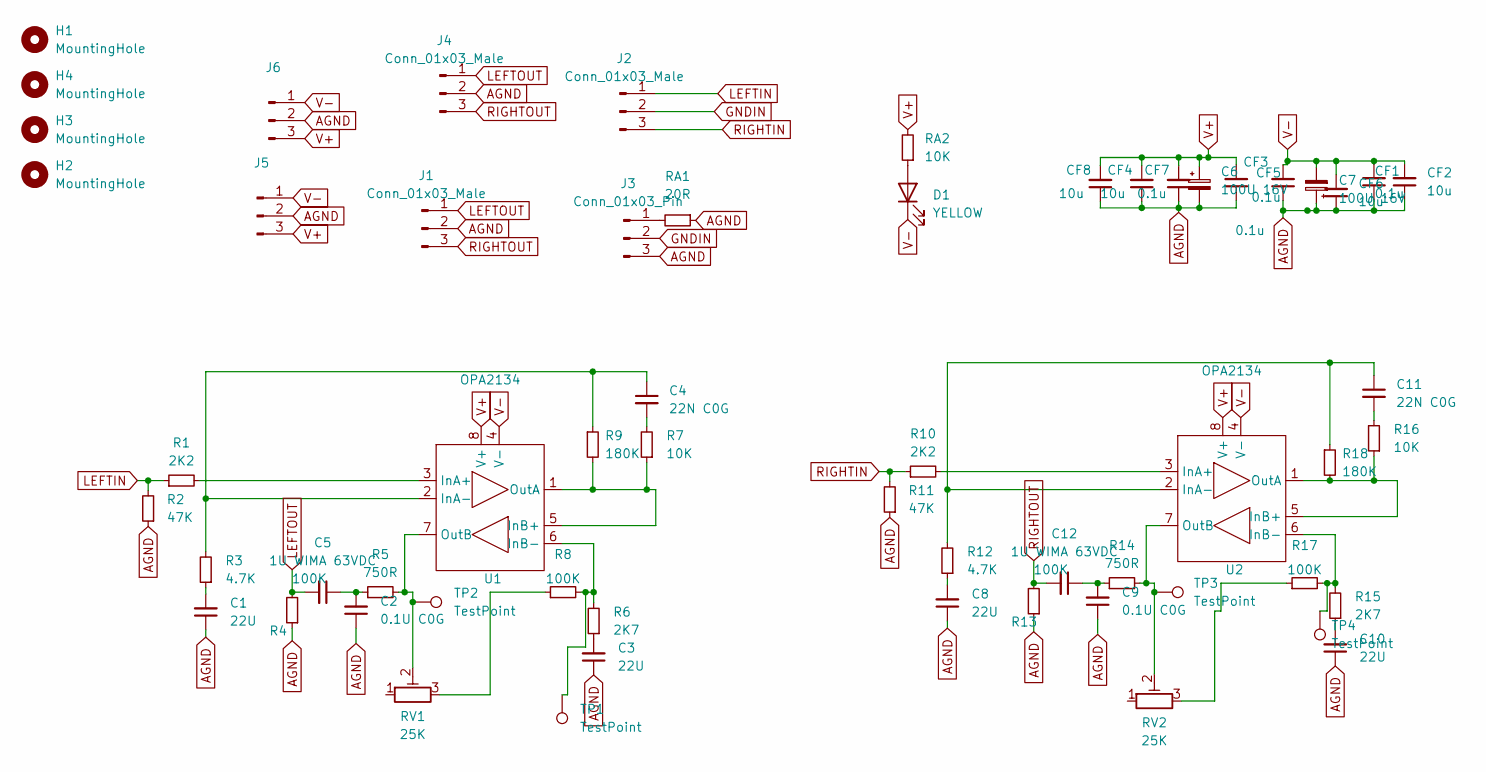
[picture p77: schematic Vinyl.kicad_sch]

Parts:
C1, C3, C8, C10: 22U; CP_Radial_D6.3mm_P2.50mm
C2, C9: 0.1U C0G; C_1206_3216Metric_Pad1.33x1.80mm_HandSolder
C4, C11: 22N C0G; C_0805_2012Metric_Pad1.18x1.45mm_HandSolder
C5, C12: 1U WIMA 63VDC; C_Rect_L7.2mm_W11.0mm_P5.00mm_FKS2_FKP2_MKS2_MKP2; Mouser 505-MKP2C0411NMN
C6, C7: 100U 16V; CP_Radial_D6.3mm_P2.50mm
CF1, CF3, CF5, CF7: 0.1u; C_0805_2012Metric_Pad1.18x1.45mm_HandSolder
CF2, CF4, CF6, CF8: 10u; C_1206_3216Metric_Pad1.33x1.80mm_HandSolder
D1: YELLOW; LED_0603_1608Metric_Pad1.05x0.95mm_HandSolder
H1, H2, H3, H4: MountingHole; MountingHole_3.2mm_M3_DIN965_Pad_TopOnly
J1, J2, J5, J6: Conn_01x03_Male; JST_PH_B3B-PH-K_1x03_P2.00mm_Vertical
J3: Conn_01x03_Pin; PinHeader_1x03_P2.54mm_Vertical
J4: Conn_01x03_Male; PinHeader_1x03_P2.54mm_Vertical
R1, R10: 2K2; R_0805_2012Metric_Pad1.20x1.40mm_HandSolder
R2, R11: 47K; R_0805_2012Metric_Pad1.20x1.40mm_HandSolder
R3, R12: 4.7K; R_0805_2012Metric_Pad1.20x1.40mm_HandSolder
R4, R8, R13, R17: 100K; R_0805_2012Metric_Pad1.20x1.40mm_HandSolder
R5, R14: 750R; R_0805_2012Metric_Pad1.20x1.40mm_HandSolder
R6, R15: 2K7; R_0805_2012Metric_Pad1.20x1.40mm_HandSolder
R7, R16: 10K; R_0805_2012Metric_Pad1.20x1.40mm_HandSolder
R9, R18: 180K; R_0805_2012Metric_Pad1.20x1.40mm_HandSolder
RA1: 20R; R_0603_1608Metric
RA2: 10K; R_0603_1608Metric
RV1, RV2: 25K; Potentiometer_Bourns_3296W_Vertical
TP1, TP2, TP3, TP4: TestPoint; TestPoint_THTPad_1.5x1.5mm_Drill0.7mm
U1, U2: OPA2134; DIP-8_W7.62mm_Socket

Connections:
AGND: C1.1, C2.1, C3.1, C6.2, C7.1, C8.1, C9.1, C10.1, CF1.1, CF2.1, CF3.1, CF4.1, CF5.1, CF6.1, CF7.1, CF8.1, J1.2, J3.3, J4.2, J5.2, J6.2, R2.1, R4.1, R11.1, R13.1, RA1.1
GNDIN: J2.2, J3.2
LEFTIN: J2.1, R1.1, R2.2
LEFTOUT: C5.2, J1.1, J4.1, R4.2
unnamed: C1.2, R3.1
unnamed: C2.2, C5.1, R5.1
unnamed: C3.2, R6.1
unnamed: C4.2, R7.2
unnamed: C8.2, R12.1
unnamed: C10.2, R15.1
unnamed: C11.2, R16.2
unnamed: C9.2, C12.1, R14.1
unnamed: D1.2 (A), RA2.1
unnamed: J3.1, RA1.2
unnamed: R8.1, RV1.3
unnamed: R17.1, RV2.3
unnamed: R1.2, U1.3 (InA+)
unnamed: C4.1, R3.2, R9.1, U1.2 (InA-)
unnamed: R7.1, R9.2, U1.1 (OutA), U1.5 (InB+)
unnamed: R6.2, R8.2, TP1.1, U1.6 (InB-)
unnamed: R5.2, RV1.2, TP2.1, U1.7 (OutB)
unnamed: R10.2, U2.3 (InA+)
unnamed: C11.1, R12.2, R18.1, U2.2 (InA-)
unnamed: R16.1, R18.2, U2.1 (OutA), U2.5 (InB+)
unnamed: R15.2, R17.2, TP4.1, U2.6 (InB-)
unnamed: R14.2, RV2.2, TP3.1, U2.7 (OutB)
RIGHTIN: J2.3, R10.1, R11.2
RIGHTOUT: C12.2, J1.3, J4.3, R13.2
V+: C6.1, CF3.2, CF4.2, CF7.2, CF8.2, J5.3, J6.3, RA2.2, U1.8 (V+), U2.8 (V+)
V-: C7.2, CF1.2, CF2.2, CF5.2, CF6.2, D1.1 (K), J5.1, J6.1, U1.4 (V-), U2.4 (V-)

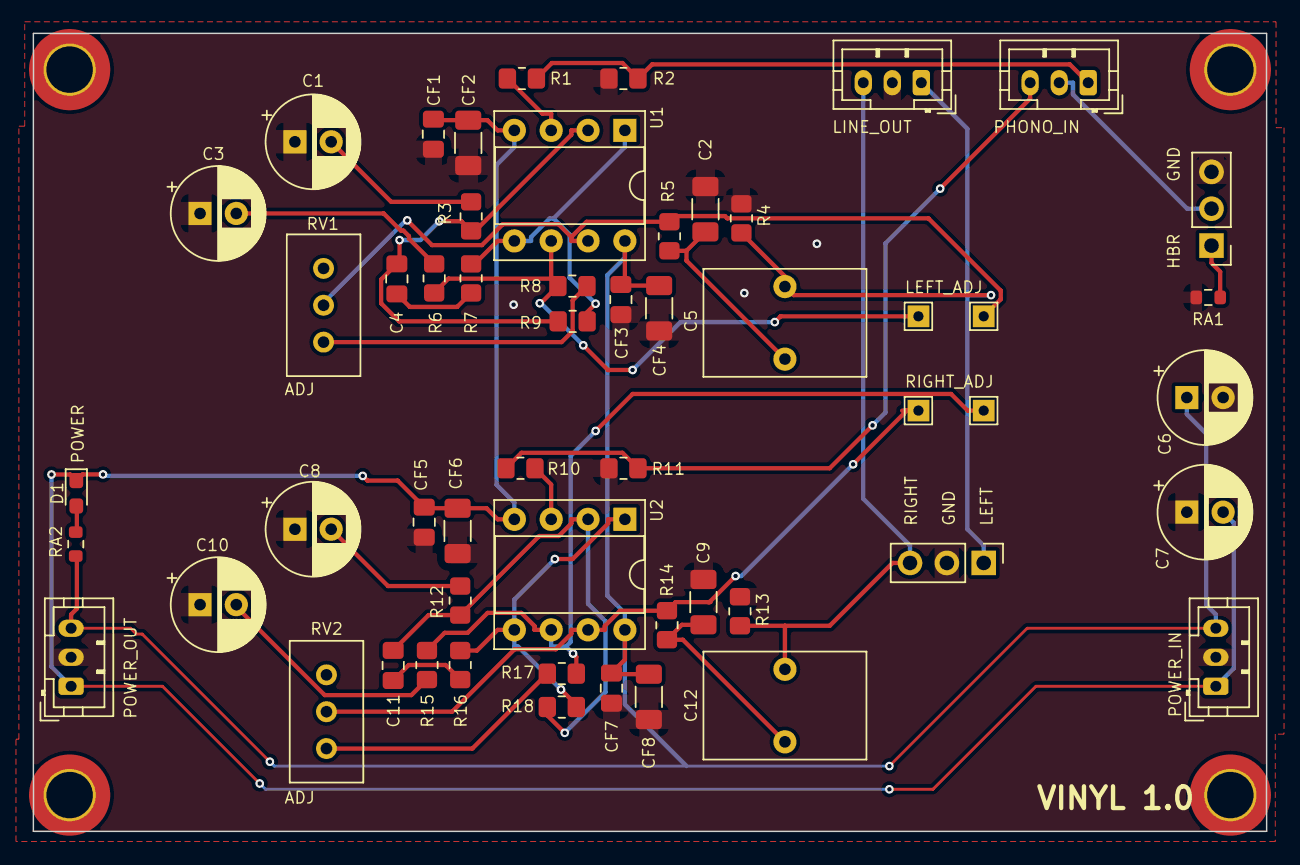
[picture p78: board Vinyl.kicad_pcb from above]

Board: 2 copper layers, 85.0 x 55.0 mm, 59 parts (0 on the bottom side), 30 nets.
