duanestorey/Hifi-Amplifier/PCBs/Test/Test.kicad_pcb

## KiCad design PCBs/Test/Test.kicad_pcb (2024-12-19)

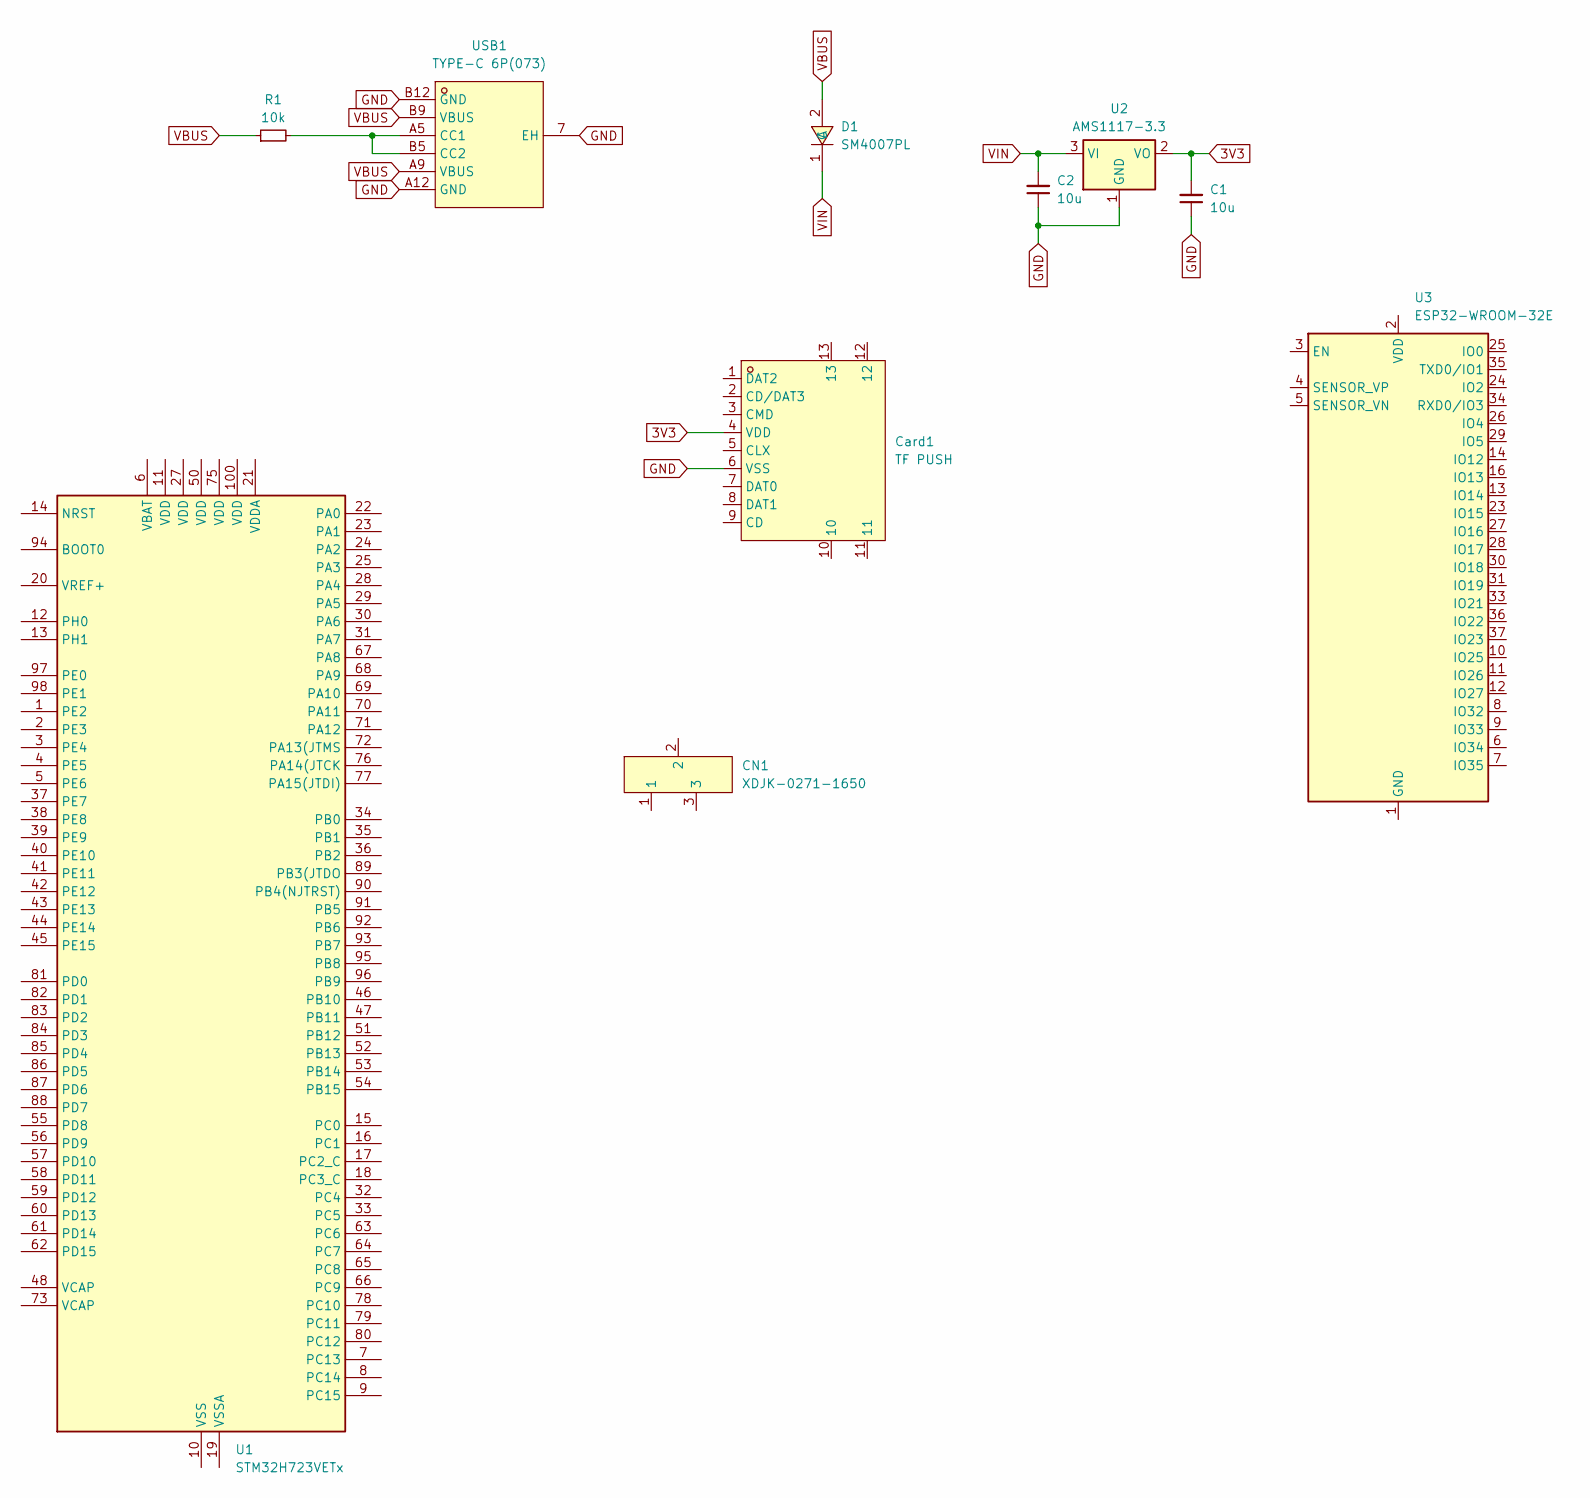
[picture p79: schematic Test.kicad_sch]

Parts:
C1, C2: 10u; C_0603_1608Metric; LCSC C57112
CN1: XDJK-0271-1650; CONN-TH_XDJK-0271-1650; LCSC Part C7527522
Card1: TF PUSH; TF-SMD_TF-PUSH; LCSC Part C393941
D1: SM4007PL; SOD-123F_L2.8-W1.8-LS3.7-RD; LCSC Part C64898
R1: 10k; R_0402_1005Metric; LCSC C25744
U1: STM32H723VETx; LQFP-100_14x14mm_P0.5mm; LCSC C730141
U2: AMS1117-3.3; SOT-223-3_TabPin2; LCSC C6186
U3: ESP32-WROOM-32E; ESP32-WROOM-32D; LCSC C701342
USB1: TYPE-C 6P(073); TYPE-C-SMD_TYPE-C-6P_5; LCSC Part C668623

Connections:
3V3: C1.2, Card1.4 (VDD), U2.2 (VO)
GND: C1.1, C2.1, Card1.6 (VSS), U2.1 (GND), USB1.7 (EH), USB1.A12 (GND), USB1.B12 (GND)
unnamed: U1.10 (VSS), U1.26 (VSS), U1.49 (VSS), U1.74 (VSS), U1.99 (VSS)
unnamed: U3.1 (GND), U3.15 (GND), U3.38 (GND), U3.39 (GND)
unnamed: R1.2, USB1.A5 (CC1), USB1.B5 (CC2)
VBUS: D1.2 (A), R1.1, USB1.A9 (VBUS), USB1.B9 (VBUS)
VIN: C2.2, D1.1 (C), U2.3 (VI)

Board: 2 copper layers, 10 parts (0 on the bottom side), 7 nets, no tracks yet.
