duanestorey/Hifi-Amplifier/PCBs/1/CS8416 + PCB5122/1.0/CS8416-PCB5122.kicad_pcb

## KiCad design PCBs/1/CS8416 + PCB5122/1.0/CS8416-PCB5122.kicad_pcb (2024-12-19)

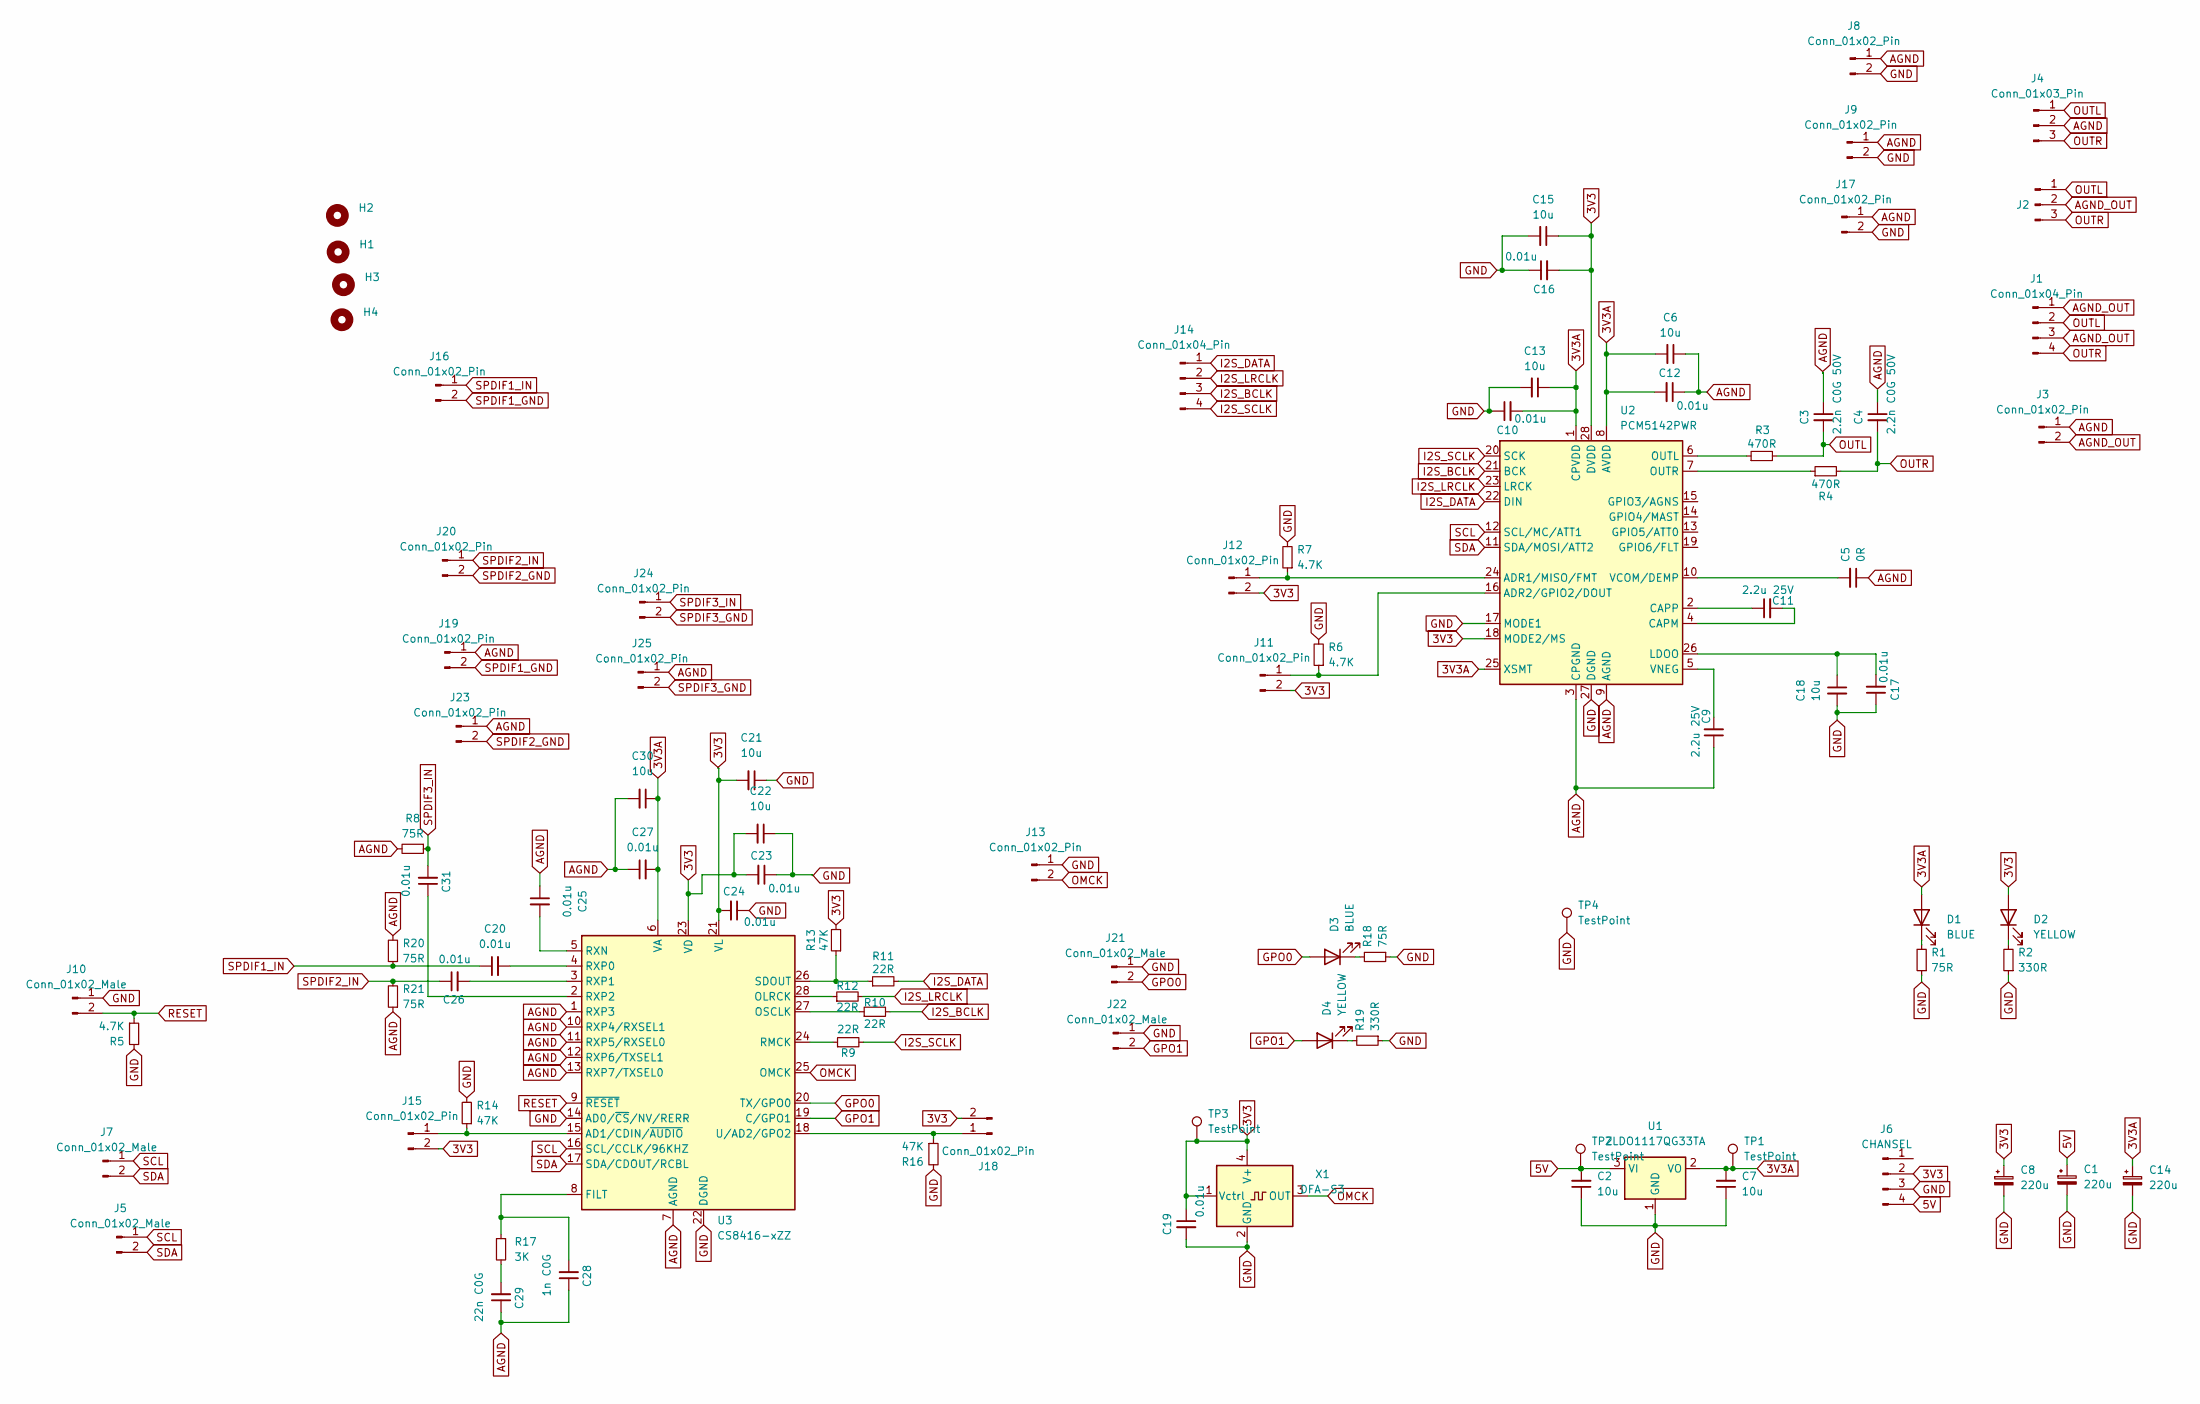
[picture p80: schematic CS8416-PCB5122.kicad_sch]

Parts:
C1, C8, C14: 220u; CP_Radial_D6.3mm_P2.50mm
C2, C6, C7, C13, C15, C18, C21, C22, C30: 10u; C_1206_3216Metric_Pad1.33x1.80mm_HandSolder
C3, C4: 2.2n C0G 50V; C_0805_2012Metric
C5: 0R; C_1206_3216Metric_Pad1.33x1.80mm_HandSolder
C9, C11: 2.2u 25V; C_0805_2012Metric
C10, C12, C16, C17, C19, C23, C24, C27: 0.01u; C_0805_2012Metric
C20, C25, C26, C31: 0.01u; C_0805_2012Metric_Pad1.18x1.45mm_HandSolder
C28: 1n C0G; C_0805_2012Metric_Pad1.18x1.45mm_HandSolder
C29: 22n C0G; C_0805_2012Metric_Pad1.18x1.45mm_HandSolder
D1, D3: BLUE; LED_0805_2012Metric_Pad1.15x1.40mm_HandSolder
D2, D4: YELLOW; LED_0805_2012Metric_Pad1.15x1.40mm_HandSolder
H1, H2, H3, H4: MountingHole; MountingHole_3.2mm_M3
J1: Conn_01x04_Pin; JST_PH_B4B-PH-K_1x04_P2.00mm_Vertical
J2: Conn_01x03_Pin; JST_PH_B3B-PH-K_1x03_P2.00mm_Vertical
J3, J8, J9, J11, J12, J13, J15, J17, J18, J19, J23, J25: Conn_01x02_Pin; PinHeader_1x02_P2.54mm_Vertical
J4: Conn_01x03_Pin; PinHeader_1x03_P2.54mm_Vertical
J5, J7, J10, J21, J22: Conn_01x02_Male; JST_PH_B2B-PH-K_1x02_P2.00mm_Vertical
J6: CHANSEL; JST_XH_B4B-XH-A_1x04_P2.50mm_Vertical
J14: Conn_01x04_Pin; PinHeader_1x04_P2.54mm_Vertical
J16, J20, J24: Conn_01x02_Pin; JST_XH_B2B-XH-A_1x02_P2.50mm_Vertical
R1, R8, R18, R20, R21: 75R; R_0603_1608Metric_Pad0.98x0.95mm_HandSolder
R2, R19: 330R; R_0603_1608Metric_Pad0.98x0.95mm_HandSolder
R3, R4: 470R; R_0603_1608Metric_Pad0.98x0.95mm_HandSolder
R5, R6, R7: 4.7K; R_0603_1608Metric_Pad0.98x0.95mm_HandSolder
R9, R10, R11, R12: 22R; R_0603_1608Metric_Pad0.98x0.95mm_HandSolder
R13, R14, R16: 47K; R_0603_1608Metric_Pad0.98x0.95mm_HandSolder
R17: 3K; R_0603_1608Metric_Pad0.98x0.95mm_HandSolder
TP1, TP2, TP3, TP4: TestPoint; TestPoint_Pad_2.0x2.0mm
U1: ZLDO1117QG33TA; SOT-223-3_TabPin2
U2: PCM5142PWR; TSSOP-28_4.4x9.7mm_P0.65mm
U3: CS8416-xZZ; TSSOP-28_4.4x9.7mm_P0.65mm
X1: DFA-S3; Oscillator_SMD_EuroQuartz_XO53-4Pin_5.0x3.2mm

Connections:
3V3: C8.1, C15.1, C16.2, C19.1, C21.2, C22.2, C23.2, C24.2, D2.2 (A), J6.2, J11.2, J12.2, J15.2, J18.2, R13.2, TP3.1, U2.18 (MODE2/MS), U2.28 (DVDD), U3.21 (VL), U3.23 (VD), X1.1 (Vctrl), X1.4 (V+)
3V3A: C6.2, C7.2, C10.2, C12.2, C13.1, C14.1, C27.2, C30.1, D1.2 (A), TP1.1, U1.2 (VO), U2.1 (CPVDD), U2.8 (AVDD), U2.25 (XSMT), U3.6 (VA)
5V: C1.1, C2.2, J6.4, TP2.1, U1.3 (VI)
AGND: C3.1, C4.1, C5.1, C6.1, C9.1, C12.1, C25.1, C27.1, C28.1, C29.1, C30.2, J3.1, J4.2, J8.1, J9.1, J17.1, J19.1, J23.1, J25.1, R8.2, R20.2, R21.1, U2.3 (CPGND), U2.9 (AGND), U3.1 (RXP3), U3.7 (AGND), U3.10 (RXP4/RXSEL1), U3.11 (RXP5/RXSEL0), U3.12 (RXP6/TXSEL1), U3.13 (RXP7/TXSEL0)
AGND_OUT: J1.1, J1.3, J2.2, J3.2
GND: C1.2, C2.1, C7.1, C8.2, C10.1, C13.2, C14.2, C15.2, C16.1, C17.1, C18.2, C19.2, C21.1, C22.1, C23.1, C24.1, J6.3, J8.2, J9.2, J10.1, J13.1, J17.2, J21.1, J22.1, R1.1, R2.1, R5.2, R6.2, R7.2, R14.2, R16.2, R18.1, R19.1, TP4.1, U1.1 (GND), U2.17 (MODE1), U2.27 (DGND), U3.14 (AD0/~CS/NV/RERR), U3.22 (DGND), X1.2 (GND)
GPO0: D3.2 (A), J21.2, U3.20 (TX/GPO0)
GPO1: D4.2 (A), J22.2, U3.19 (C/GPO1)
I2S_BCLK: J14.3, R10.2, U2.21 (BCK)
I2S_DATA: J14.1, R11.2, U2.22 (DIN)
I2S_LRCLK: J14.2, R12.2, U2.23 (LRCK)
I2S_SCLK: J14.4, R9.2, U2.20 (SCK)
unnamed: C29.2, R17.2
unnamed: D1.1 (K), R1.2
unnamed: D2.1 (K), R2.2
unnamed: D3.1 (K), R18.2
unnamed: D4.1 (K), R19.2
unnamed: J11.1, R6.1, U2.16 (ADR2/GPIO2/DOUT)
unnamed: J12.1, R7.1, U2.24 (ADR1/MISO/FMT)
unnamed: J15.1, R14.1, U3.15 (AD1/CDIN/~AUDIO)
unnamed: J18.1, R16.1, U3.18 (U/AD2/GPO2)
unnamed: C11.2, U2.4 (CAPM)
unnamed: C11.1, U2.2 (CAPP)
unnamed: C17.2, C18.1, U2.26 (LDOO)
unnamed: R3.1, U2.6 (OUTL)
unnamed: R4.1, U2.7 (OUTR)
unnamed: C5.2, U2.10 (VCOM/DEMP)
unnamed: C9.2, U2.5 (VNEG)
unnamed: C28.2, R17.1, U3.8 (FILT)
unnamed: R12.1, U3.28 (OLRCK)
unnamed: R10.1, U3.27 (OSCLK)
unnamed: R9.1, U3.24 (RMCK)
unnamed: C25.2, U3.5 (RXN)
unnamed: C20.2, U3.4 (RXP0)
unnamed: C26.2, U3.3 (RXP1)
unnamed: C31.1, U3.2 (RXP2)
unnamed: R11.1, R13.1, U3.26 (SDOUT)
OMCK: J13.2, U3.25 (OMCK), X1.3 (OUT)
OUTL: C3.2, J1.2, J2.1, J4.1, R3.2
OUTR: C4.2, J1.4, J2.3, J4.3, R4.2
RESET: J10.2, R5.1, U3.9 (~RESET)
SCL: J5.1, J7.1, U2.12 (SCL/MC/ATT1), U3.16 (SCL/CCLK/96KHZ)
SDA: J5.2, J7.2, U2.11 (SDA/MOSI/ATT2), U3.17 (SDA/CDOUT/RCBL)
SPDIF1_GND: J16.2, J19.2
SPDIF1_IN: C20.1, J16.1, R20.1
SPDIF2_GND: J20.2, J23.2
SPDIF2_IN: C26.1, J20.1, R21.2
SPDIF3_GND: J24.2, J25.2
SPDIF3_IN: C31.2, J24.1, R8.1

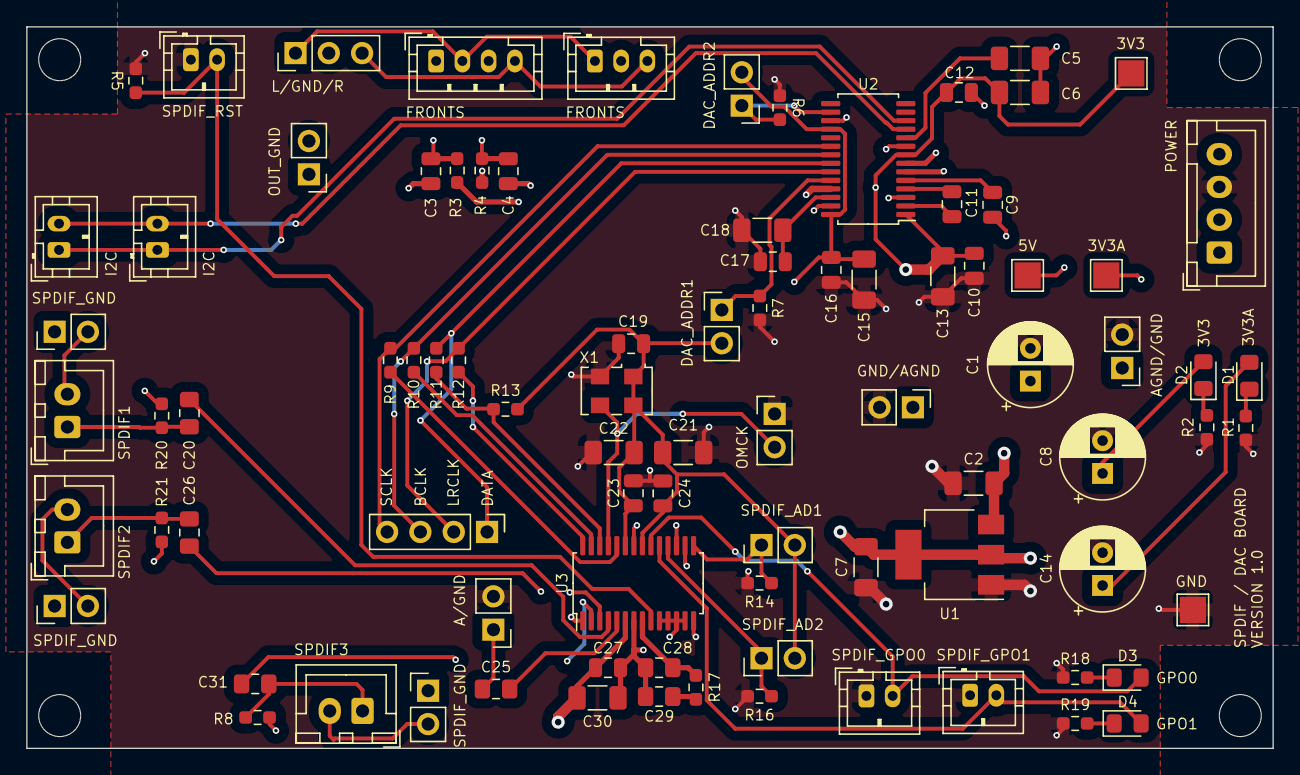
[picture p81: board CS8416-PCB5122.kicad_pcb from above]

Board: 4 copper layers, 95.0 x 55.0 mm, 92 parts (0 on the bottom side), 49 nets.
