duanestorey/Hifi-Amplifier/PCBs/1/Channel Amplifier/2.0/PowerAmp.kicad_pcb

## KiCad design PCBs/1/Channel Amplifier/2.0/PowerAmp.kicad_pcb (2024-12-08)

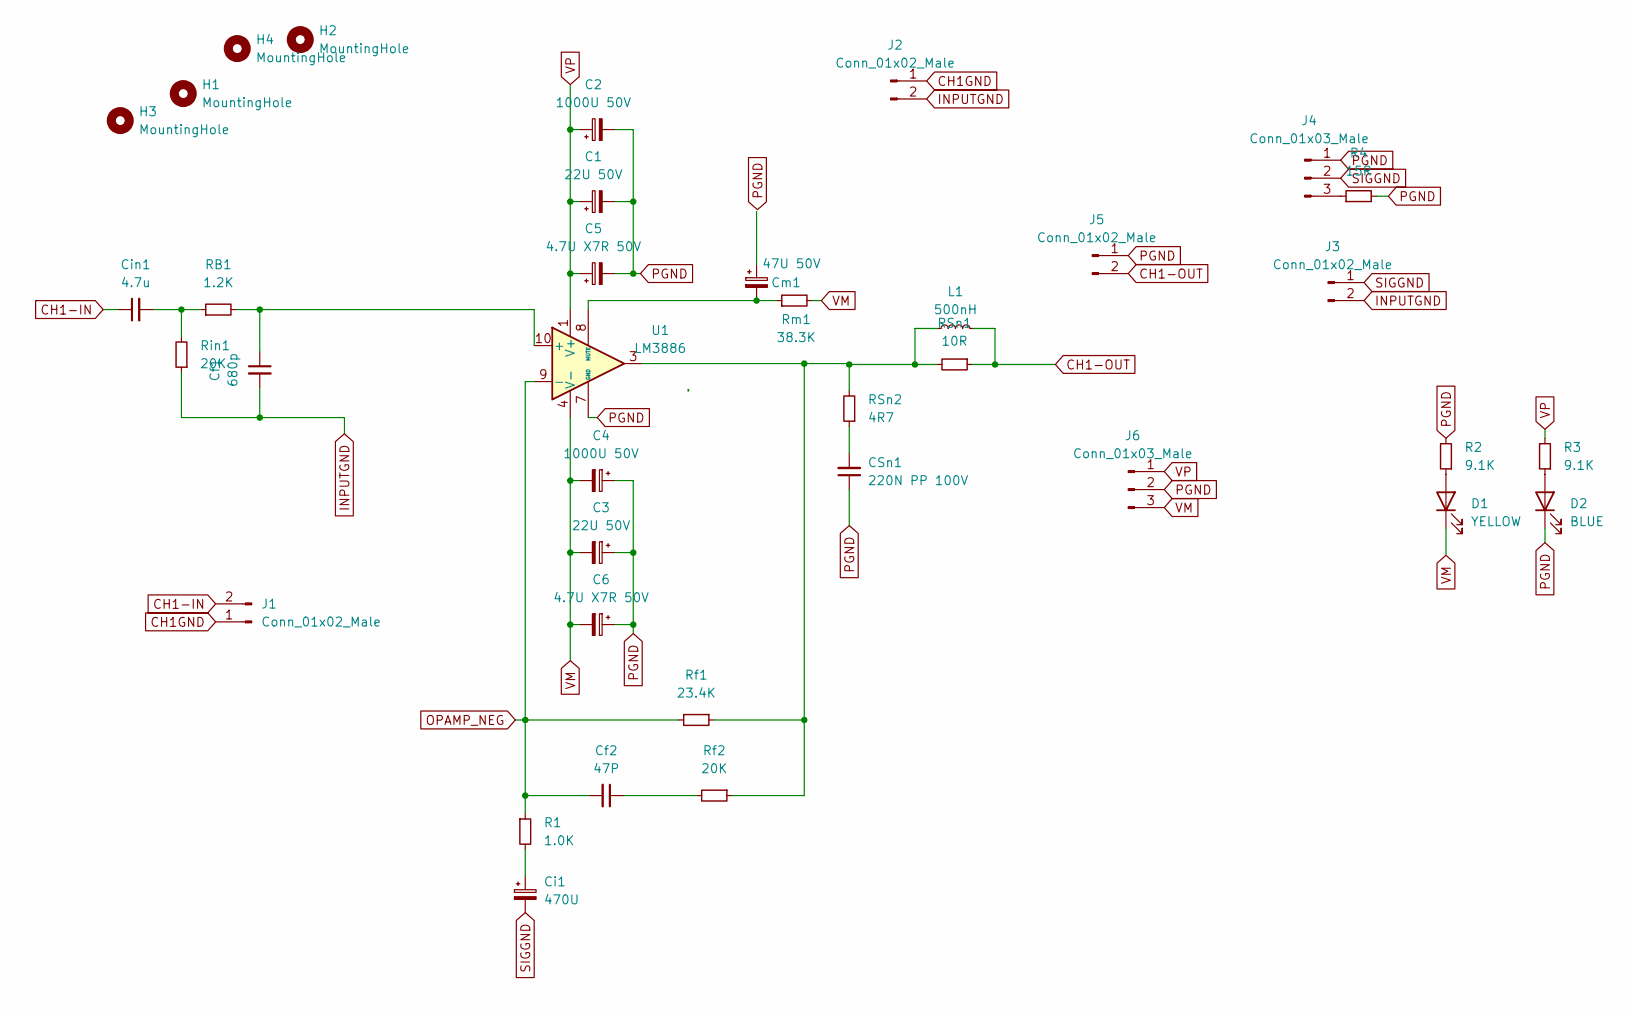
[picture p84: schematic PowerAmp.kicad_sch]

Parts:
C1, C3: 22U 50V; CP_Radial_D6.3mm_P2.50mm
C2, C4: 1000U 50V; CP_Radial_D12.5mm_P5.00mm
C5, C6: 4.7U X7R 50V; C_1206_3216Metric_Pad1.33x1.80mm_HandSolder
CSn1: 220N PP 100V; C_Rect_L18.0mm_W7.0mm_P15.00mm_FKS3_FKP3
Cf1: 680p; C_1206_3216Metric_Pad1.33x1.80mm_HandSolder
Cf2: 47P; C_1206_3216Metric_Pad1.33x1.80mm_HandSolder
Ci1: 470U; CP_Radial_D12.5mm_P5.00mm
Cin1: 4.7u; 4.7uF Polypropylene Aliexpress
Cm1: 47U 50V; CP_Radial_D6.3mm_P2.50mm
D1: YELLOW; LED_0805_2012Metric_Pad1.15x1.40mm_HandSolder
D2: BLUE; LED_0805_2012Metric_Pad1.15x1.40mm_HandSolder
H1, H2, H3, H4: MountingHole; MountingHole_3mm
J1: Conn_01x02_Male; JST_PH_B2B-PH-K_1x02_P2.00mm_Vertical
J2, J3: Conn_01x02_Male; PinHeader_1x02_P2.54mm_Vertical
J4: Conn_01x03_Male; PinHeader_1x03_P2.54mm_Vertical
J5: Conn_01x02_Male; JST_VH_B2P-VH_1x02_P3.96mm_Vertical
J6: Conn_01x03_Male; JST_VH_B3P-VH-B_1x03_P3.96mm_Vertical
L1: 500nH; 500nH Inductor Aliexpress Air Gap
R1: 1.0K; R_1206_3216Metric_Pad1.30x1.75mm_HandSolder
R2, R3: 9.1K; R_0805_2012Metric_Pad1.20x1.40mm_HandSolder
R4: 15R; R_0805_2012Metric_Pad1.20x1.40mm_HandSolder
RB1: 1.2K; R_1206_3216Metric_Pad1.30x1.75mm_HandSolder
RSn1: 10R; R_4020_10251Metric_Pad1.65x5.30mm_HandSolder
RSn2: 4R7; R_Axial_DIN0411_L9.9mm_D3.6mm_P12.70mm_Horizontal
Rf1: 23.4K; R_1206_3216Metric_Pad1.30x1.75mm_HandSolder
Rf2: 20K; R_1206_3216Metric_Pad1.30x1.75mm_HandSolder
Rin1: 20K; R_1206_3216Metric_Pad1.30x1.75mm_HandSolder
Rm1: 38.3K; R_1206_3216Metric_Pad1.30x1.75mm_HandSolder
U1: LM3886; TO-220-11_P3.4x5.08mm_StaggerOdd_Lead4.85mm_Vertical

Connections:
CH1-IN: Cin1.1, J1.2
CH1-OUT: J5.2, L1.2, RSn1.1
CH1GND: J1.1, J2.1
INPUTGND: Cf1.2, J2.2, J3.2, Rin1.1
unnamed: CSn1.2, RSn2.1
unnamed: Cf2.1, Rf2.2
unnamed: Ci1.1, R1.2
unnamed: Cin1.2, RB1.1, Rin1.2
unnamed: D1.2 (A), R2.1
unnamed: D2.2 (A), R3.1
unnamed: J4.3, R4.1
unnamed: L1.1, RSn1.2, RSn2.2, Rf1.1, Rf2.1, U1.3
unnamed: Cf1.1, RB1.2, U1.10 (+)
unnamed: Cm1.2, Rm1.1, U1.8 (MUTE)
OPAMP_NEG: Cf2.2, R1.1, Rf1.2, U1.9 (-)
PGND: C1.2, C2.2, C3.1, C4.1, C5.2, C6.1, CSn1.1, D2.1 (K), J4.1, J5.1, J6.2, R2.2, R4.2, U1.7 (GND)
SIGGND: Ci1.2, J3.1, J4.2
VM: C3.2, C4.2, C6.2, D1.1 (K), J6.3, Rm1.2, U1.4 (V-)
VP: C1.1, C2.1, C5.1, J6.1, R3.2, U1.1 (V+), U1.5 (V+)

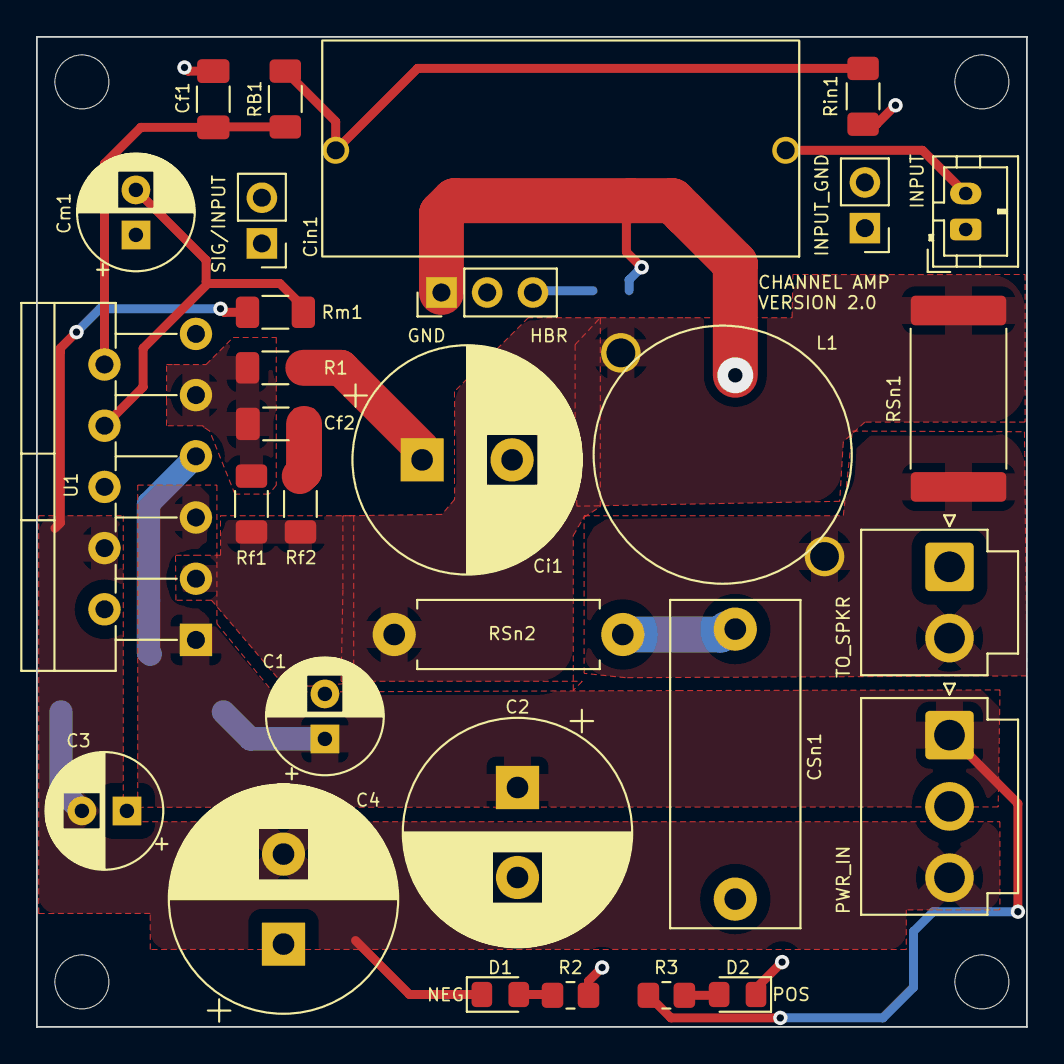
[picture p85: board PowerAmp.kicad_pcb from above]

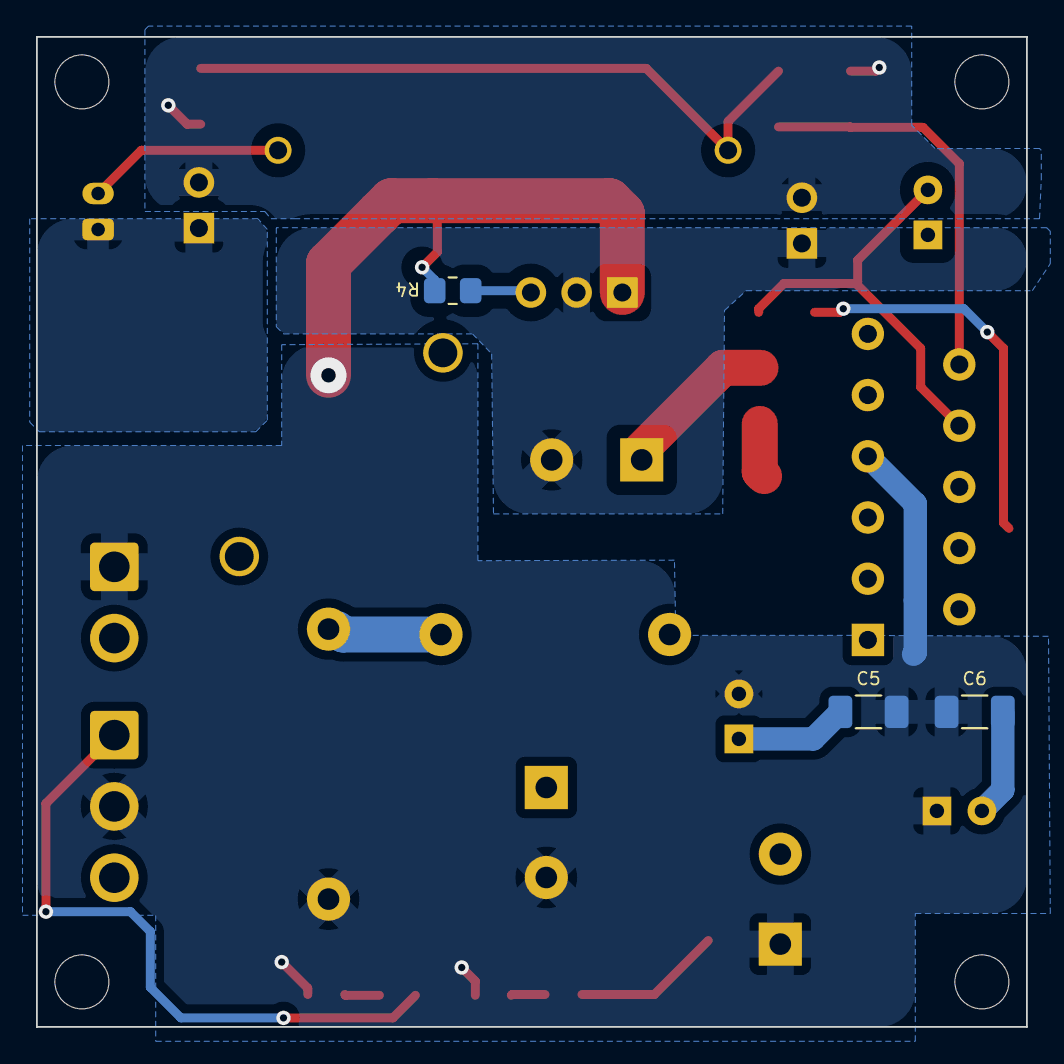
[picture p86: board PowerAmp.kicad_pcb from below]

Board: 2 copper layers, 55.0 x 55.0 mm, 37 parts (3 on the bottom side), 19 nets.
