duanestorey/Hifi-Amplifier/PCBs/AURORA/InputSel/0.1/ChannelSelector.kicad_pcb

## KiCad design PCBs/AURORA/InputSel/0.1/ChannelSelector.kicad_pcb (2024-12-08)

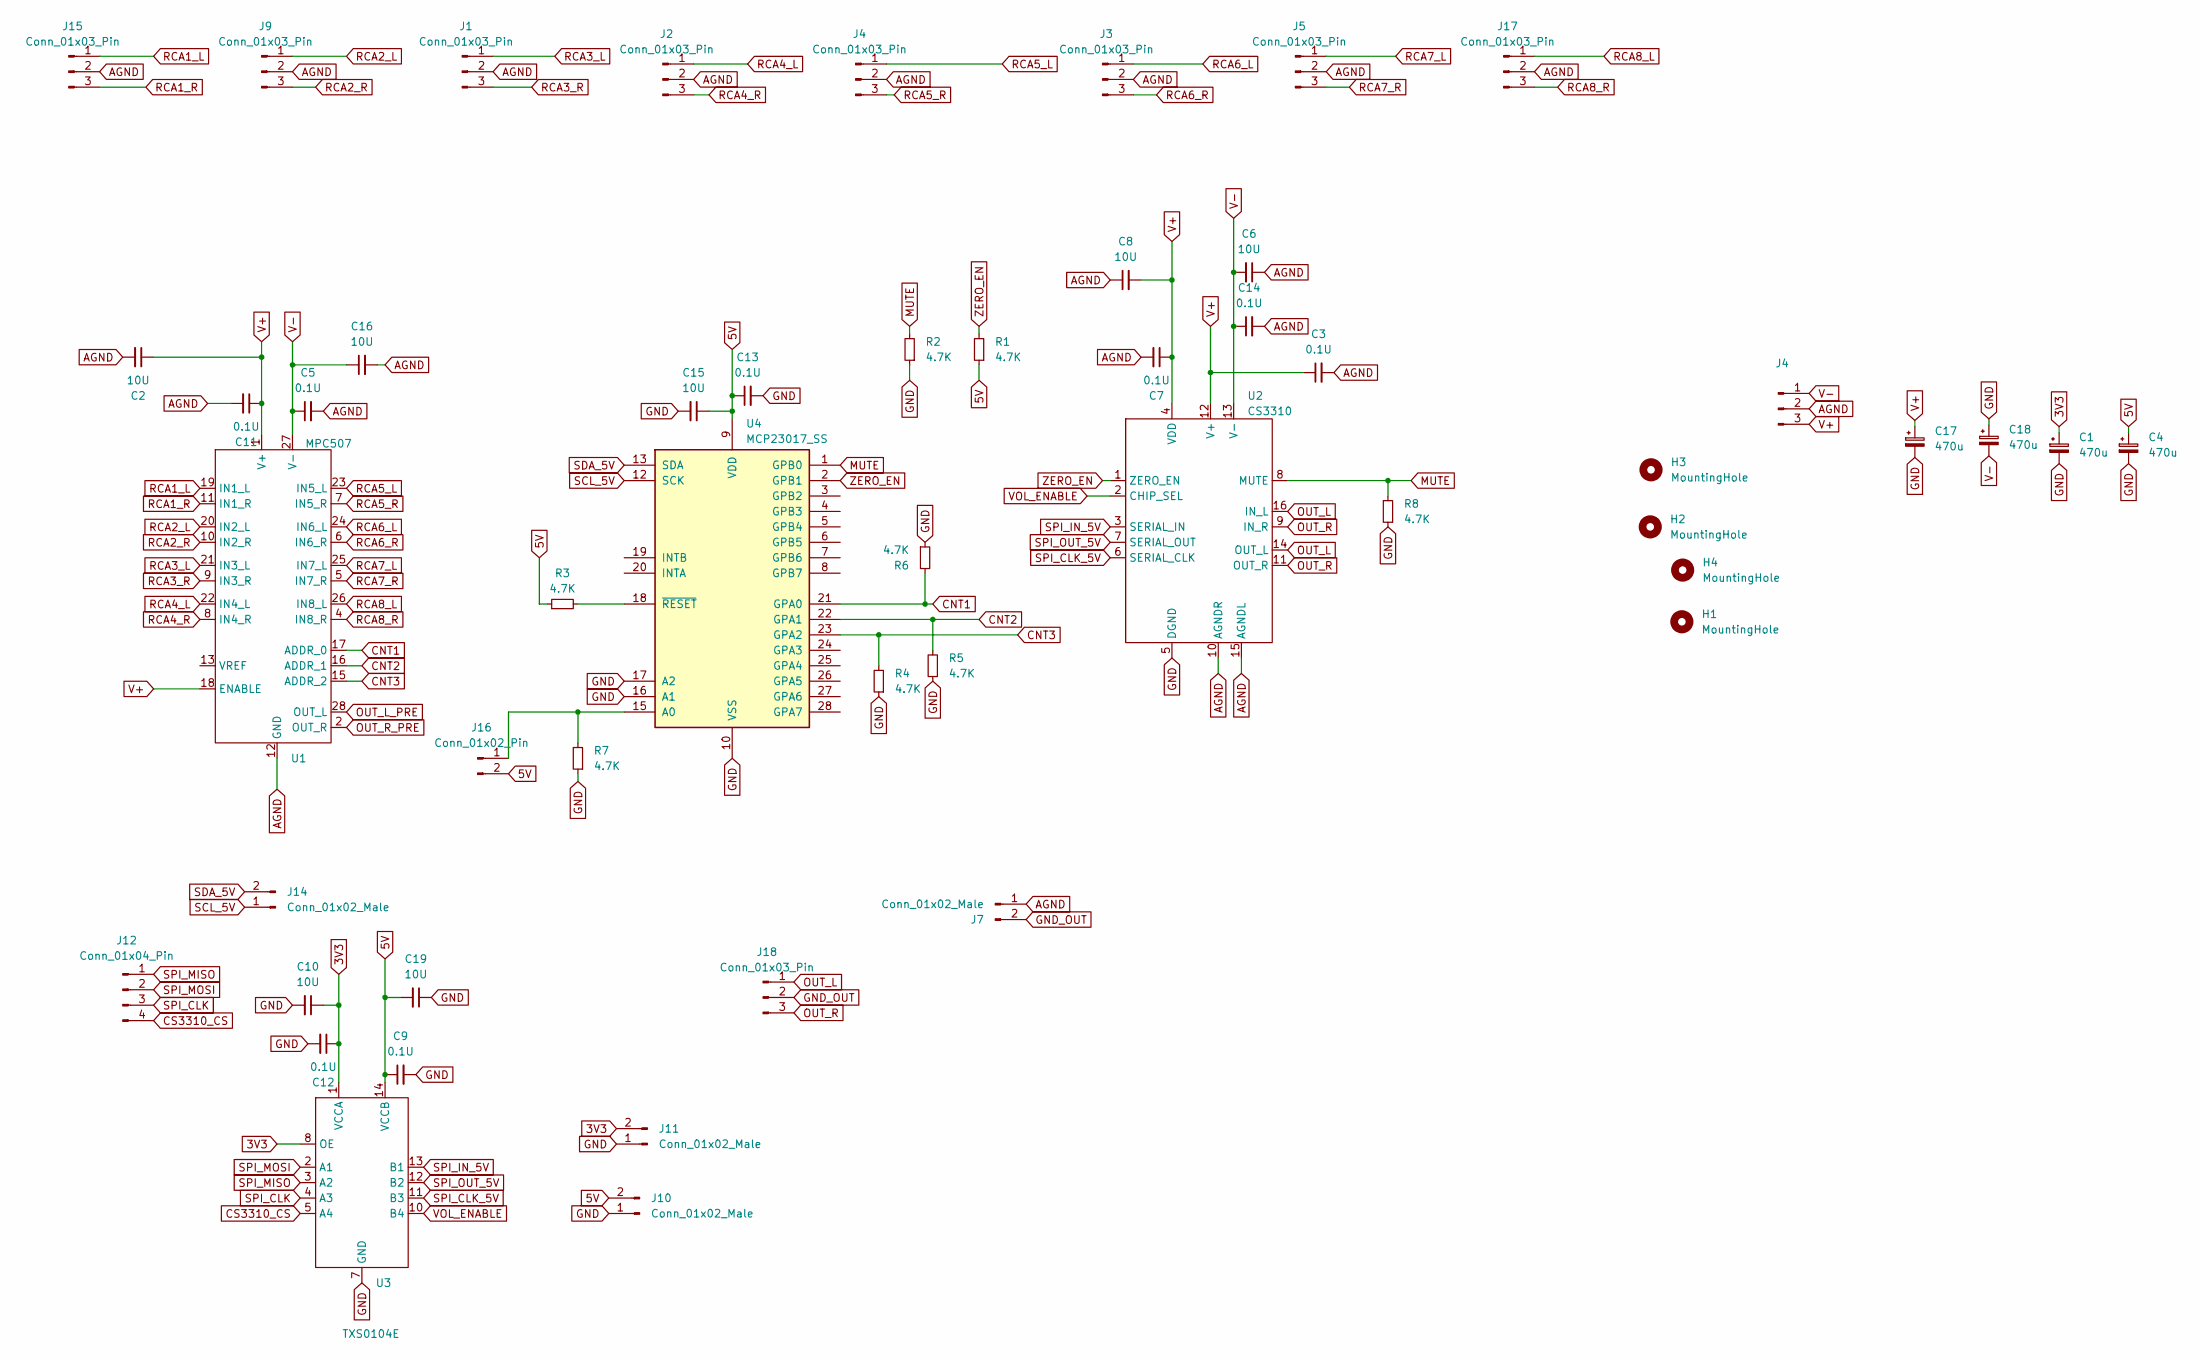
[picture p87: schematic ChannelSelector.kicad_sch]

Parts:
C1, C4, C17, C18: 470u; CP_Radial_D6.3mm_P2.50mm
C2, C6, C8, C10, C15, C16, C19: 10U; C_1206_3216Metric_Pad1.33x1.80mm_HandSolder
C3, C5, C7, C9, C11, C12, C13, C14: 0.1U; C_0805_2012Metric_Pad1.18x1.45mm_HandSolder
H1, H2, H3, H4: MountingHole; MountingHole_3.2mm_M3
J1, J2, J3, J4, J5, J9, J15, J17, J18: Conn_01x03_Pin; JST_PH_B3B-PH-K_1x03_P2.00mm_Vertical
J7: Conn_01x02_Male; PinHeader_1x02_P2.54mm_Vertical
J10, J11, J14: Conn_01x02_Male; JST_PH_B2B-PH-K_1x02_P2.00mm_Vertical
J12: Conn_01x04_Pin; JST_PH_B4B-PH-K_1x04_P2.00mm_Vertical
J16: Conn_01x02_Pin; PinHeader_1x02_P2.54mm_Vertical
R1, R2, R3, R4, R5, R6, R7, R8: 4.7K; R_0603_1608Metric_Pad0.98x0.95mm_HandSolder
U1: MPC507; SOIC-28W_7.5x18.7mm_P1.27mm
U2: CS3310; SOIC-16W_7.5x10.3mm_P1.27mm
U3: TXS0104E; TSSOP-14_4.4x5mm_P0.65mm
U4: MCP23017_SS; SSOP-28_5.3x10.2mm_P0.65mm

Connections:
3V3: C1.1, C10.1, C12.1, J11.2, U3.1 (VCCA), U3.8 (OE)
5V: C4.1, C9.1, C13.1, C15.1, C19.2, J10.2, J16.2, R1.1, R3.1, U3.14 (VCCB), U4.9 (VDD)
AGND: C2.2, C3.2, C5.2, C6.1, C7.2, C8.1, C11.2, C14.2, C16.2, J1.2, J2.2, J3.2, J4.2, J5.2, J7.1, J9.2, J15.2, J17.2, U1.12 (GND), U2.10 (AGNDR), U2.15 (AGNDL); also elsewhere on the board
CNT1: R6.2, U1.17 (ADDR_0), U4.21 (GPA0)
CNT2: R5.2, U1.16 (ADDR_1), U4.22 (GPA1)
CNT3: R4.2, U1.15 (ADDR_2), U4.23 (GPA2)
CS3310_CS: J12.4, U3.5 (A4)
GND: C1.2, C4.2, C9.2, C10.2, C12.2, C13.2, C15.2, C17.2, C18.1, C19.1, J10.1, J11.1, R2.1, R4.1, R5.1, R6.1, R7.1, R8.1, U2.5 (DGND), U3.7 (GND), U4.10 (VSS), U4.16 (A1), U4.17 (A2)
GND_OUT: J7.2, J18.2
MUTE: R2.2, R8.2, U2.8 (MUTE), U4.1 (GPB0)
unnamed: J16.1, R7.2, U4.15 (A0)
unnamed: R3.2, U4.18 (~RESET)
OUT_L: J18.1, U2.14 (OUT_L), U2.16 (IN_L)
OUT_L_PRE: U1.28 (OUT_L)
OUT_R: J18.3, U2.9 (IN_R), U2.11 (OUT_R)
OUT_R_PRE: U1.2 (OUT_R)
RCA1_L: J15.1, U1.19 (IN1_L)
RCA1_R: J15.3, U1.11 (IN1_R)
RCA2_L: J9.1, U1.20 (IN2_L)
RCA2_R: J9.3, U1.10 (IN2_R)
RCA3_L: J1.1, U1.21 (IN3_L)
RCA3_R: J1.3, U1.9 (IN3_R)
RCA4_L: J2.1, U1.22 (IN4_L)
RCA4_R: J2.3, U1.8 (IN4_R)
RCA6_L: J3.1, U1.24 (IN6_L)
RCA6_R: J3.3, U1.6 (IN6_R)
RCA7_L: J5.1, U1.25 (IN7_L)
RCA7_R: J5.3, U1.5 (IN7_R)
RCA8_L: J17.1, U1.26 (IN8_L)
RCA8_R: J17.3, U1.4 (IN8_R)
SCL_5V: J14.1, U4.12 (SCK)
SDA_5V: J14.2, U4.13 (SDA)
SPI_CLK: J12.3, U3.4 (A3)
SPI_CLK_5V: U2.6 (SERIAL_CLK), U3.11 (B3)
SPI_IN_5V: U2.3 (SERIAL_IN), U3.13 (B1)
SPI_MISO: J12.1, U3.3 (A2)
SPI_MOSI: J12.2, U3.2 (A1)
SPI_OUT_5V: U2.7 (SERIAL_OUT), U3.12 (B2)
VOL_ENABLE: U2.2 (CHIP_SEL), U3.10 (B4)
ZERO_EN: R1.2, U2.1 (ZERO_EN), U4.2 (GPB1)

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
Board: 4 copper layers, 51 parts (0 on the bottom side), 42 nets, no tracks yet.

Other parts of the board:
J13: Conn_01x03_Male; JST_PH_B3B-PH-K_1x03_P2.00mm_Vertical

Their connections:
AGND: J13.2; also elsewhere on the board
