duanestorey/Hifi-Amplifier/PCBs/1/Microprocessor/2.0/uProcessor.kicad_pcb

## KiCad design PCBs/1/Microprocessor/2.0/uProcessor.kicad_pcb (2024-12-05, an earlier design)

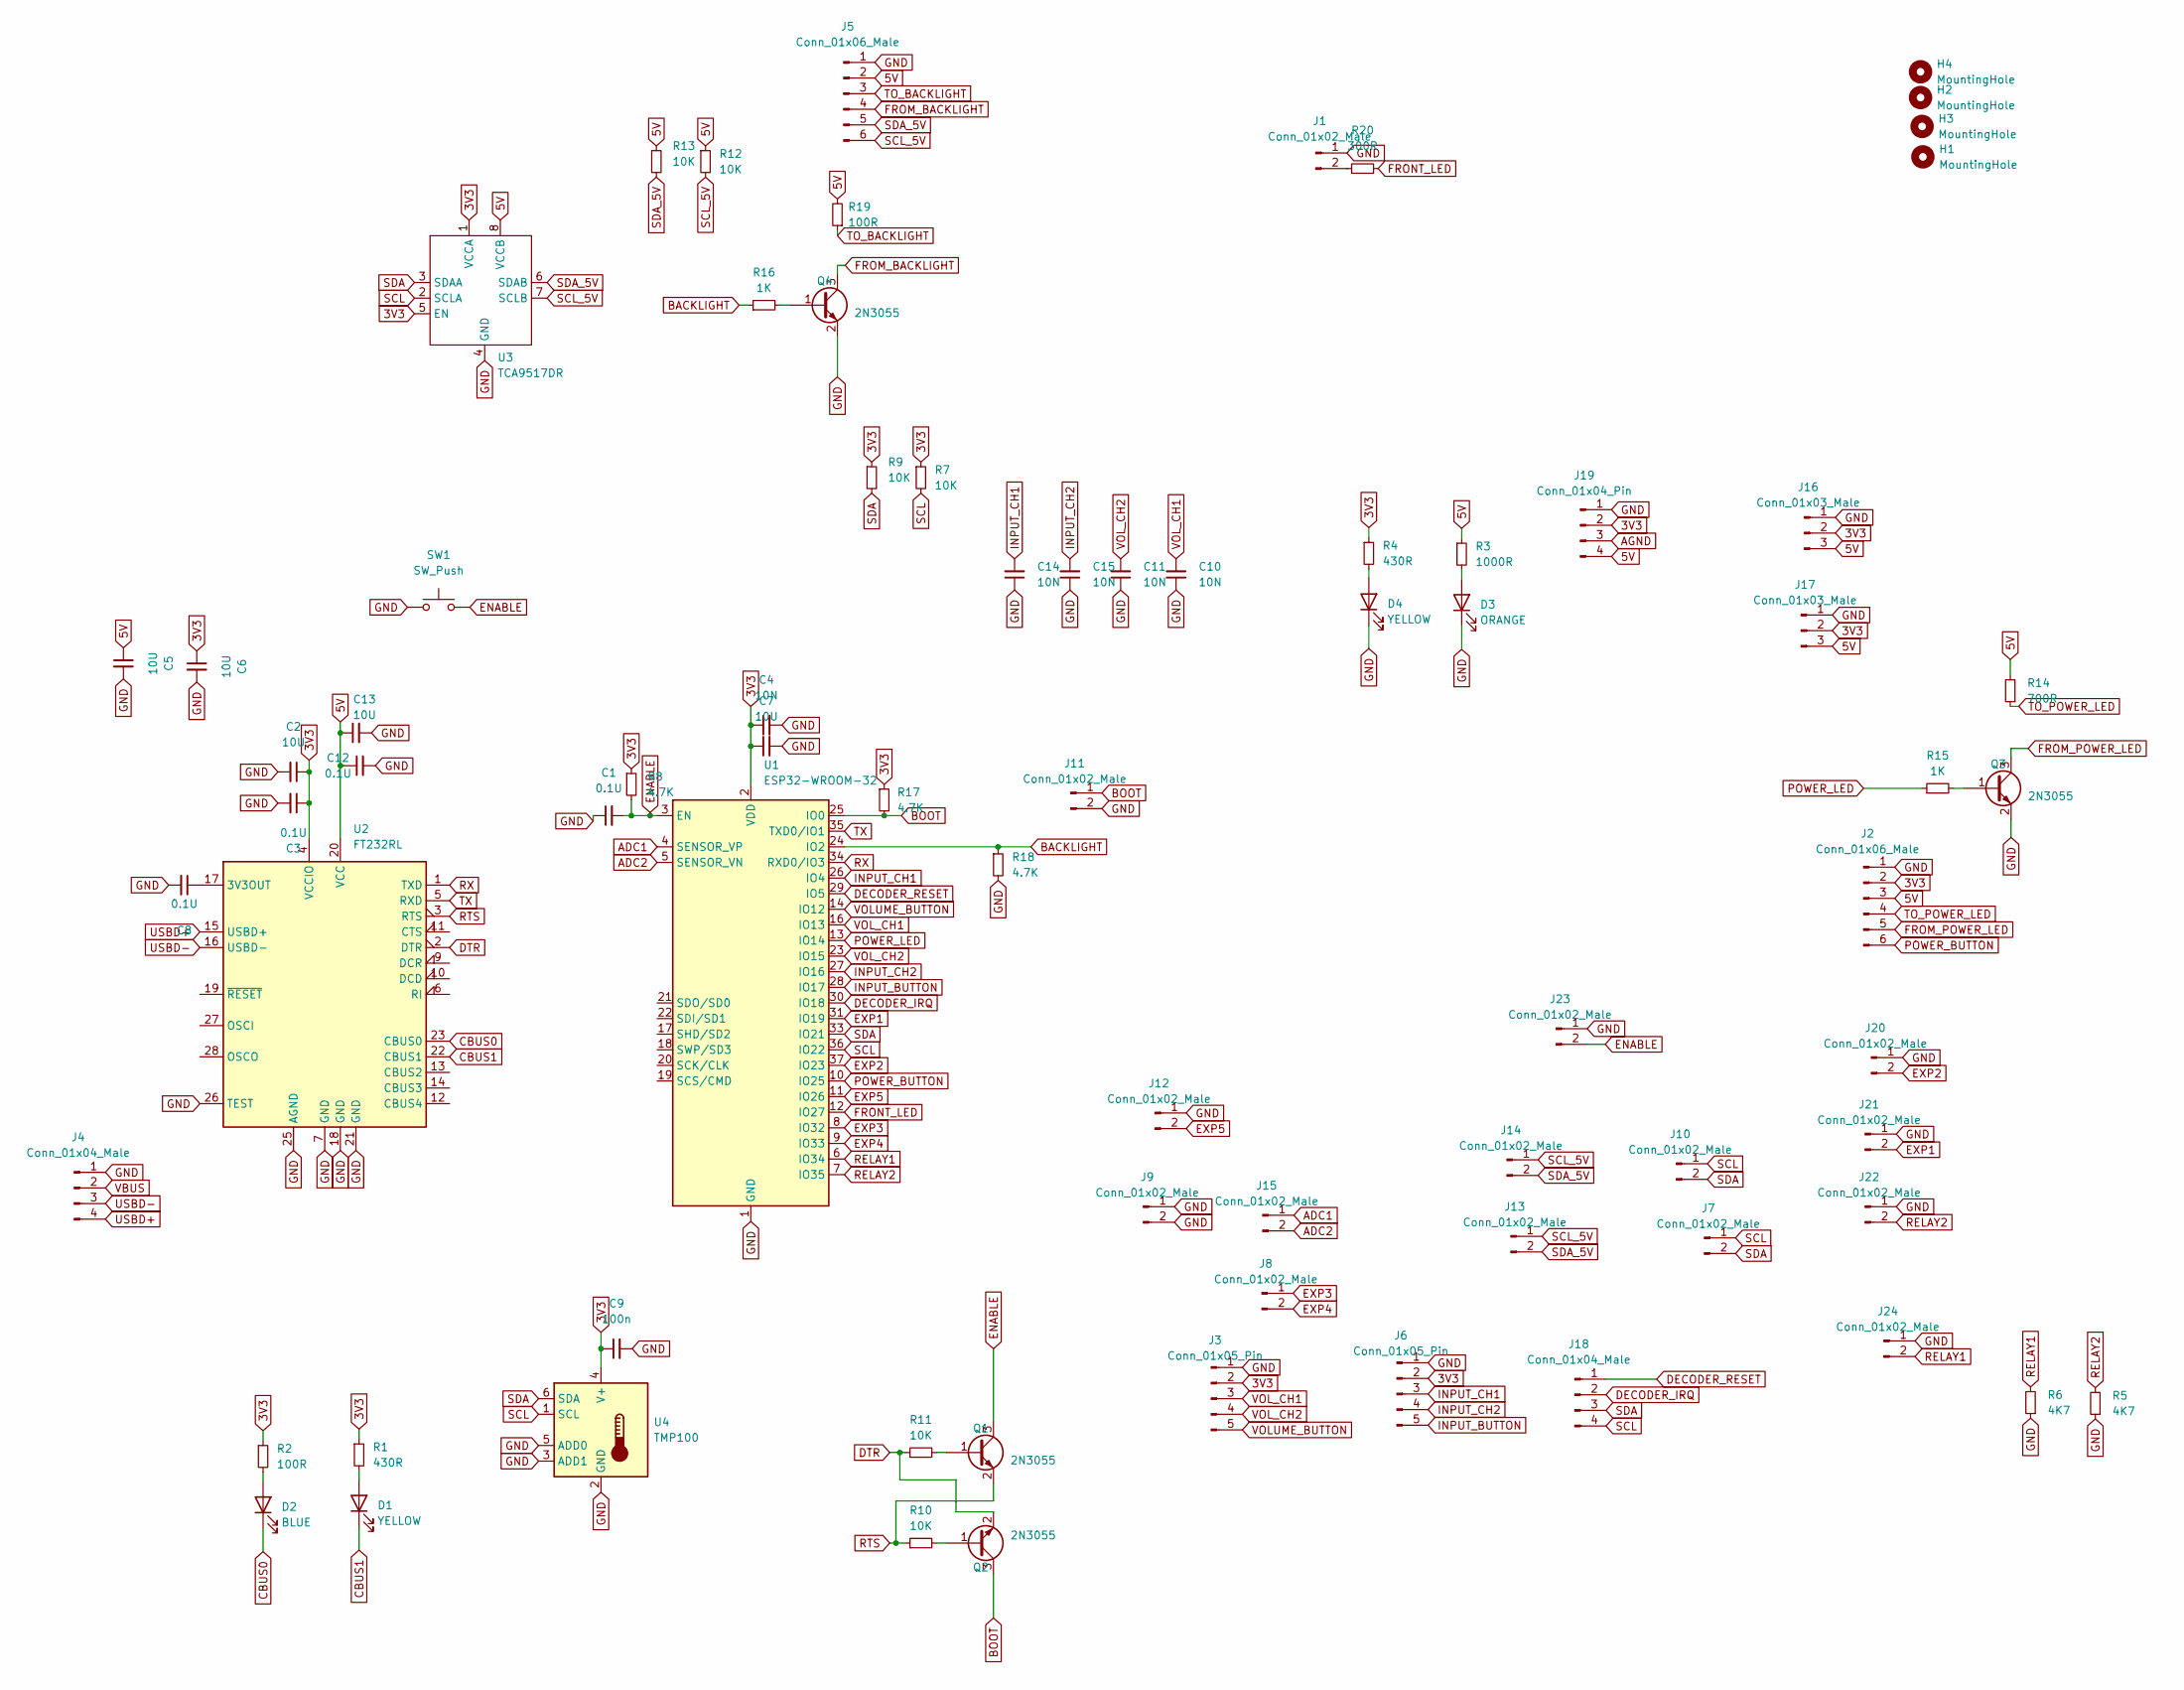
[picture p88: schematic uProcessor.kicad_sch]

Parts:
C1, C3, C8, C12: 0.1U; C_0805_2012Metric_Pad1.18x1.45mm_HandSolder
C2, C5, C6, C7, C13: 10U; C_1206_3216Metric_Pad1.33x1.80mm_HandSolder
C4: 10N; C_0805_2012Metric_Pad1.18x1.45mm_HandSolder
C9: 100n; C_0805_2012Metric_Pad1.18x1.45mm_HandSolder
C10, C11, C14, C15: 10N; C_0603_1608Metric_Pad1.08x0.95mm_HandSolder
D1: YELLOW; LED_0805_2012Metric_Pad1.15x1.40mm_HandSolder; LCSC XL-1608UBC-04
D2: BLUE; LED_0805_2012Metric_Pad1.15x1.40mm_HandSolder; LCSC XL-1608UBC-04
D3: ORANGE; LED_0805_2012Metric_Pad1.15x1.40mm_HandSolder; LCSC XL-1608UBC-04
D4: YELLOW; LED_0805_2012Metric_Pad1.15x1.40mm_HandSolder; LCSC NCD0603R1
H1, H2, H3, H4: MountingHole; MountingHole_3.2mm_M3
J1, J7, J10, J13, J14, J20, J21, J22, J23, J24: Conn_01x02_Male; JST_PH_B2B-PH-K_1x02_P2.00mm_Vertical
J2, J5: Conn_01x06_Male; JST_PH_B6B-PH-K_1x06_P2.00mm_Vertical
J3, J6: Conn_01x05_Pin; JST_PH_B5B-PH-K_1x05_P2.00mm_Vertical
J4, J18: Conn_01x04_Male; JST_PH_B4B-PH-K_1x04_P2.00mm_Vertical
J8, J9, J11, J12, J15: Conn_01x02_Male; PinHeader_1x02_P2.54mm_Vertical
J16, J17: Conn_01x03_Male; PinHeader_1x03_P2.54mm_Vertical
J19: Conn_01x04_Pin; JST_XH_B4B-XH-A_1x04_P2.50mm_Vertical
Q1, Q2, Q3, Q4: 2N3055; TSOT-23
R1, R4: 430R; R_0603_1608Metric_Pad0.98x0.95mm_HandSolder
R2, R19: 100R; R_0603_1608Metric_Pad0.98x0.95mm_HandSolder
R3: 1000R; R_0603_1608Metric_Pad0.98x0.95mm_HandSolder
R5, R6: 4K7; R_0603_1608Metric_Pad0.98x0.95mm_HandSolder
R7, R9, R10, R11, R12, R13: 10K; R_0603_1608Metric_Pad0.98x0.95mm_HandSolder
R8, R17, R18: 4.7K; R_0603_1608Metric_Pad0.98x0.95mm_HandSolder
R14: 700R; R_0603_1608Metric_Pad0.98x0.95mm_HandSolder
R15, R16: 1K; R_0603_1608Metric_Pad0.98x0.95mm_HandSolder
R20: 300R; R_0603_1608Metric_Pad0.98x0.95mm_HandSolder
SW1: SW_Push; Button Aliexpress 4x4
U1: ESP32-WROOM-32; ESP32-WROOM-32UE
U2: FT232RL; SSOP-28_5.3x10.2mm_P0.65mm
U3: TCA9517DR; SOIC-8_3.9x4.9mm_P1.27mm
U4: TMP100; SOT-23-6

Connections:
3V3: C2.1, C3.1, C4.1, C6.1, C7.1, C9.1, J2.2, J3.2, J6.2, J16.2, J17.2, J19.2, R1.1, R2.1, R4.1, R7.1, R8.1, R9.1, R17.1, U1.2 (VDD), U2.4 (VCCIO), U3.1 (VCCA), U3.5 (EN), U4.4 (V+)
5V: C5.1, C12.1, C13.1, J2.3, J5.2, J16.3, J17.3, J19.4, R3.1, R12.1, R13.1, R14.2, R19.2, U2.20 (VCC), U3.8 (VCCB)
ADC1: J15.1, U1.4 (SENSOR_VP)
ADC2: J15.2, U1.5 (SENSOR_VN)
AGND: J19.3
BACKLIGHT: R16.1, R18.1, U1.24 (IO2)
BOOT: J11.1, Q2.3 (C), R17.2, U1.25 (IO0)
CBUS0: D2.1 (K), U2.23 (CBUS0)
CBUS1: D1.1 (K), U2.22 (CBUS1)
DECODER_IRQ: J18.2, U1.30 (IO18)
DECODER_RESET: J18.1, U1.29 (IO5)
DTR: Q2.2 (E), R11.1, U2.2 (DTR)
ENABLE: C1.2, J23.2, Q1.3 (C), R8.2, SW1.2, U1.3 (EN)
EXP1: J21.2, U1.31 (IO19)
EXP2: J20.2, U1.37 (IO23)
EXP3: J8.1, U1.8 (IO32)
EXP4: J8.2, U1.9 (IO33)
EXP5: J12.2, U1.11 (IO26)
FROM_BACKLIGHT: J5.4, Q4.3 (C)
FROM_POWER_LED: J2.5, Q3.3 (C)
FRONT_LED: R20.2, U1.12 (IO27)
GND: C1.1, C2.2, C3.2, C4.2, C5.2, C6.2, C7.2, C8.2, C9.2, C10.1, C11.1, C12.2, C13.2, C14.1, C15.1, D3.1 (K), D4.1 (K), J1.1, J2.1, J3.1, J4.1, J5.1, J6.1, J9.1, J9.2, J11.2, J12.1, J16.1, J17.1, J19.1, J20.1, J21.1, J22.1, J23.1, J24.1, Q3.2 (E), Q4.2 (E), R5.1, R6.1, R18.2, SW1.1, U1.1 (GND), U1.15 (GND), U1.38 (GND), U1.39 (GND), U2.7 (GND), U2.18 (GND), U2.21 (GND), U2.25 (AGND), U2.26 (TEST), U3.4 (GND), U4.2 (GND), U4.3 (ADD1), U4.5 (ADD0)
INPUT_BUTTON: J6.5, U1.28 (IO17)
INPUT_CH1: C14.2, J6.3, U1.26 (IO4)
INPUT_CH2: C15.2, J6.4, U1.27 (IO16)
unnamed: D1.2 (A), R1.2
unnamed: D2.2 (A), R2.2
unnamed: D3.2 (A), R3.2
unnamed: D4.2 (A), R4.2
unnamed: J1.2, R20.1
unnamed: Q1.1 (B), R11.2
unnamed: Q2.1 (B), R10.2
unnamed: Q3.1 (B), R15.2
unnamed: Q4.1 (B), R16.2
unnamed: C8.1, U2.17 (3V3OUT)
POWER_BUTTON: J2.6, U1.10 (IO25)
POWER_LED: R15.1, U1.13 (IO14)
RELAY1: J24.2, R6.2, U1.6 (IO34)
RELAY2: J22.2, R5.2, U1.7 (IO35)
RTS: Q1.2 (E), R10.1, U2.3 (RTS)
RX: U1.34 (RXD0/IO3), U2.1 (TXD)
SCL: J7.1, J10.1, J18.4, R7.2, U1.36 (IO22), U3.2 (SCLA), U4.1 (SCL)
SCL_5V: J5.6, J13.1, J14.1, R12.2, U3.7 (SCLB)
SDA: J7.2, J10.2, J18.3, R9.2, U1.33 (IO21), U3.3 (SDAA), U4.6 (SDA)
SDA_5V: J5.5, J13.2, J14.2, R13.2, U3.6 (SDAB)
TO_BACKLIGHT: J5.3, R19.1
TO_POWER_LED: J2.4, R14.1
TX: U1.35 (TXD0/IO1), U2.5 (RXD)
USBD+: J4.4, U2.15 (USBD+)
USBD-: J4.3, U2.16 (USBD-)
VBUS: J4.2
VOLUME_BUTTON: J3.5, U1.14 (IO12)
VOL_CH1: C10.2, J3.3, U1.16 (IO13)
VOL_CH2: C11.2, J3.4, U1.23 (IO15)

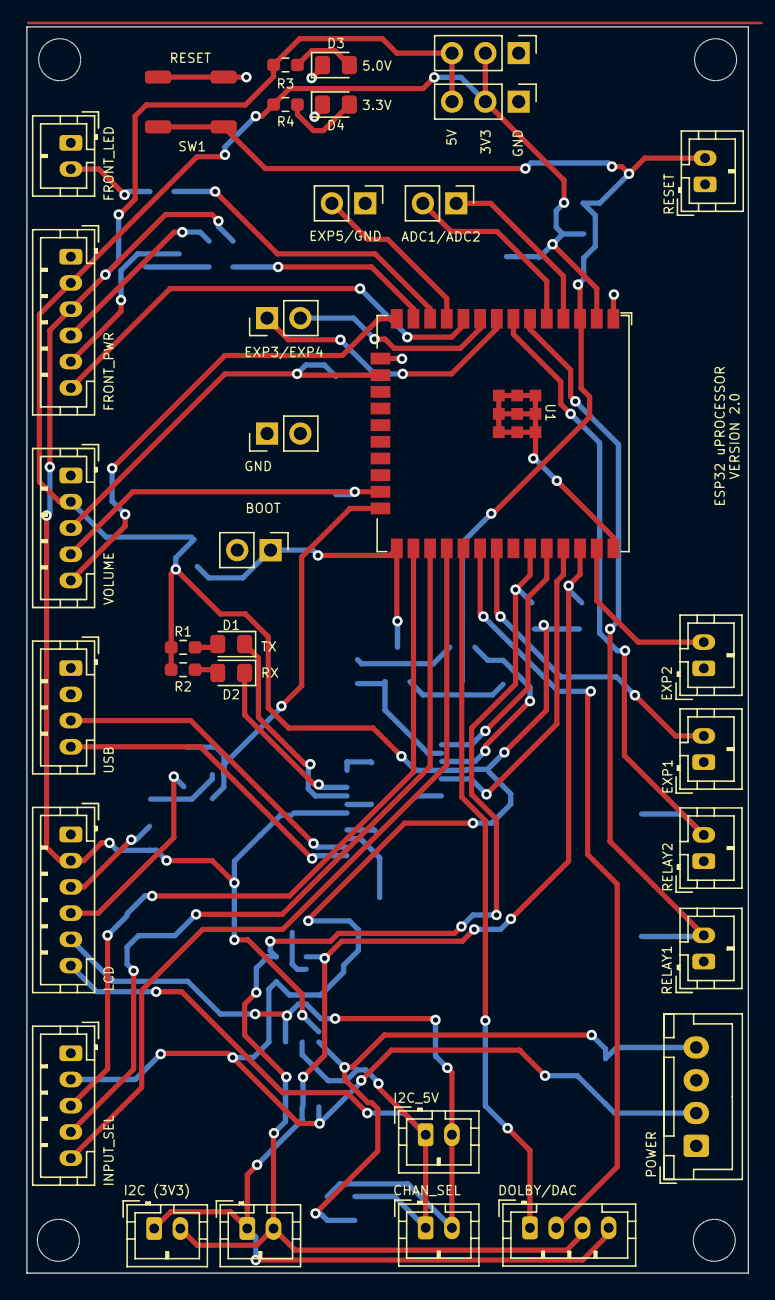
[picture p89: board PCBs/1/Microprocessor/2.0/uProcessor.kicad_pcb from above]

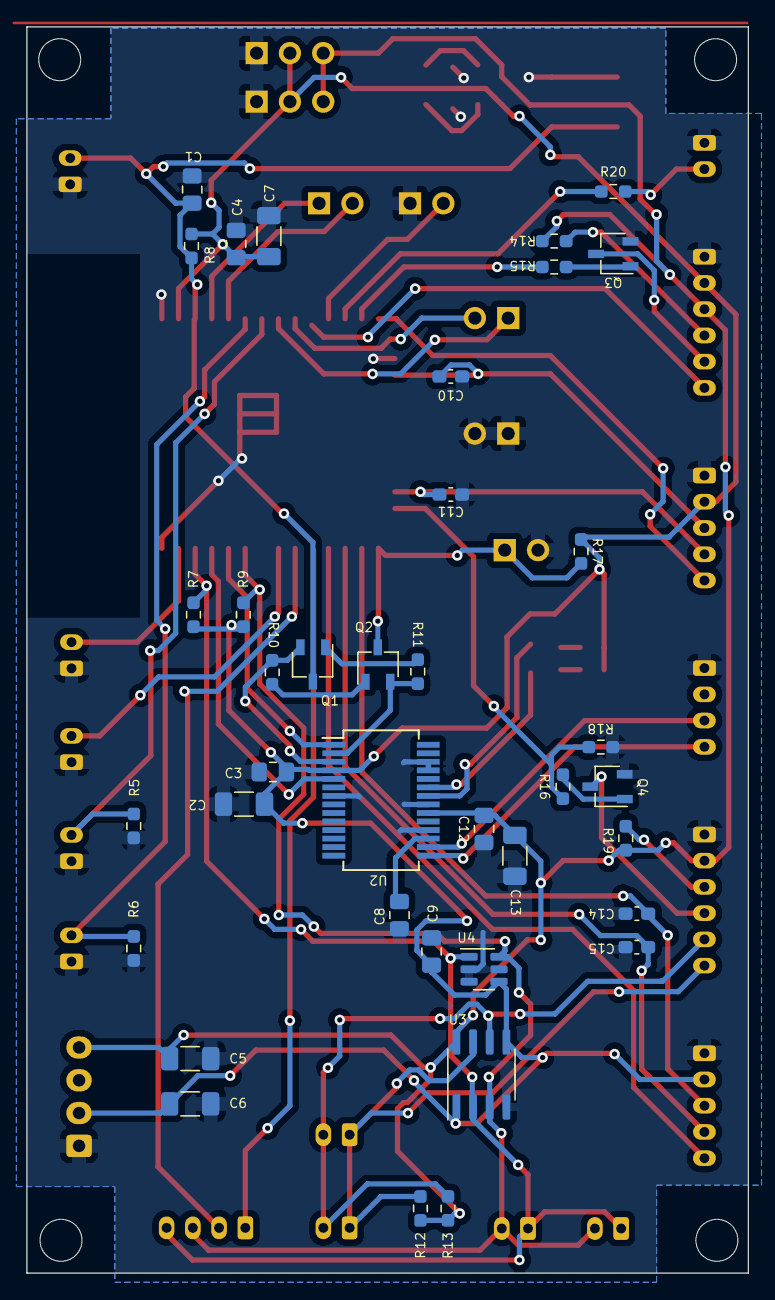
[picture p90: board PCBs/1/Microprocessor/2.0/uProcessor.kicad_pcb from below]

Board: 2 copper layers, 55.0 x 95.0 mm, 76 parts (38 on the bottom side), 52 nets.
