duanestorey/Hifi-Amplifier/PCBs/1/Power Supply (Opamps)/2.1/OpampPower.kicad_pcb

## KiCad design PCBs/1/Power Supply (Opamps)/2.1/OpampPower.kicad_pcb (2023-11-04)

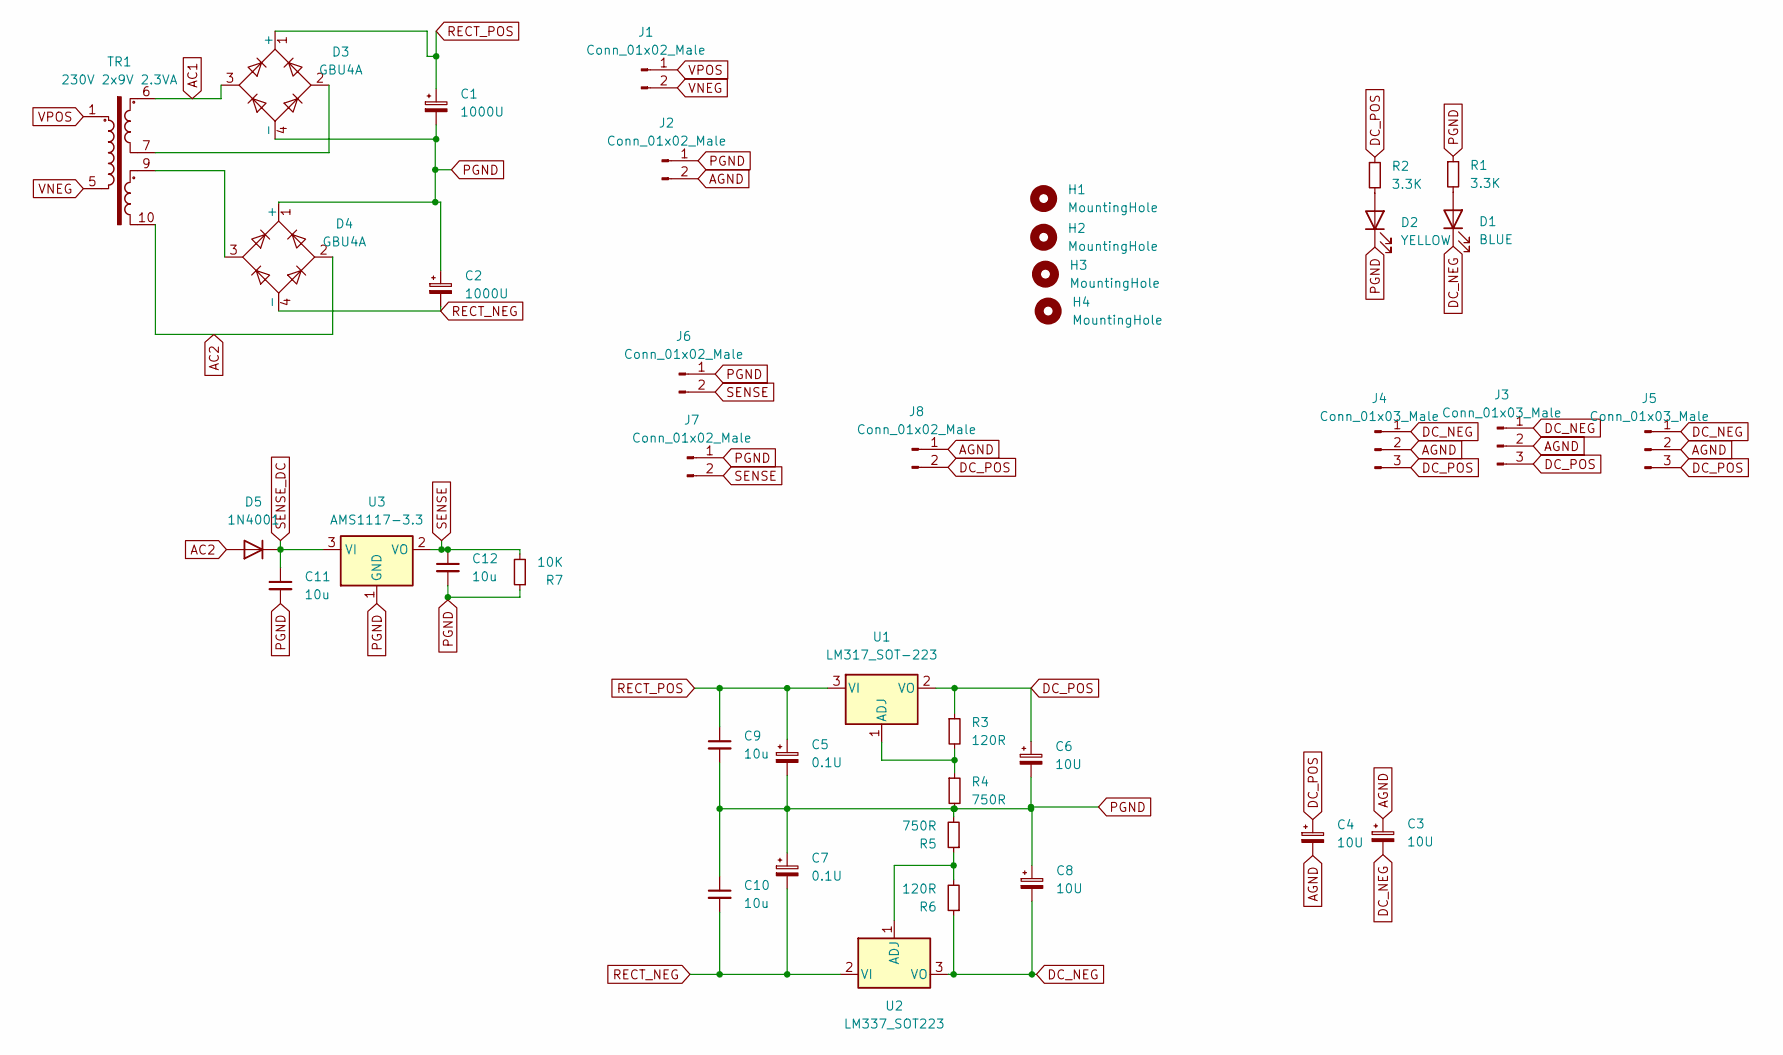
[picture p91: schematic OpampPower.kicad_sch]

Parts:
C1, C2: 1000U; CP_Radial_D10.0mm_P5.00mm_P7.50mm
C3, C4, C6, C8: 10U; C_1206_3216Metric_Pad1.33x1.80mm_HandSolder
C5, C7: 0.1U; C_0603_1608Metric_Pad1.08x0.95mm_HandSolder
C9, C10, C11, C12: 10u; C_1206_3216Metric_Pad1.33x1.80mm_HandSolder
D1: BLUE; LED_0805_2012Metric_Pad1.15x1.40mm_HandSolder
D2: YELLOW; LED_0805_2012Metric_Pad1.15x1.40mm_HandSolder
D3, D4: GBU4A; Diode_Bridge_Vishay_GBU
D5: 1N4001; D_SMA
H1, H2, H3, H4: MountingHole; MountingHole_3.2mm_M3
J1, J2: Conn_01x02_Male; JST_XH_B2B-XH-A_1x02_P2.50mm_Vertical
J3, J4, J5: Conn_01x03_Male; JST_PH_B3B-PH-K_1x03_P2.00mm_Vertical
J6, J7, J8: Conn_01x02_Male; JST_PH_B2B-PH-K_1x02_P2.00mm_Vertical
R1, R2: 3.3K; R_0603_1608Metric_Pad0.98x0.95mm_HandSolder
R3, R6: 120R; R_0603_1608Metric_Pad0.98x0.95mm_HandSolder
R4, R5: 750R; R_0603_1608Metric_Pad0.98x0.95mm_HandSolder
R7: 10K; R_0603_1608Metric_Pad0.98x0.95mm_HandSolder
TR1: 230V 2x9V 2.3VA; Transformer_Breve_TEZ-28x33
U1: LM317_SOT-223; SOT-223-3_TabPin2
U2: LM337_SOT223; SOT-223-3_TabPin2
U3: AMS1117-3.3; SOT-223-3_TabPin2

Connections:
AC1: D3.3, TR1.6
AC2: D4.2, D5.2 (A), TR1.10
AGND: C3.1, C4.2, J2.2, J3.2, J4.2, J5.2, J8.1
DC_NEG: C3.2, C8.2, D1.1 (K), J3.1, J4.1, J5.1, R6.1, U2.3 (VO)
DC_POS: C4.1, C6.1, J3.3, J4.3, J5.3, J8.2, R2.1, R3.1, U1.2 (VO)
unnamed: D1.2 (A), R1.2
unnamed: D2.2 (A), R2.2
unnamed: D3.2, TR1.7
unnamed: D4.3, TR1.9
unnamed: R3.2, R4.1, U1.1 (ADJ)
unnamed: R5.1, R6.2, U2.1 (ADJ)
PGND: C1.2, C2.1, C5.2, C6.2, C7.1, C8.1, C9.2, C10.1, C11.2, C12.2, D2.1 (K), D3.4 (-), D4.1 (+), J2.1, J6.1, J7.1, R1.1, R4.2, R5.2, R7.1, U3.1 (GND)
RECT_NEG: C2.2, C7.2, C10.2, D4.4 (-), U2.2 (VI)
RECT_POS: C1.1, C5.1, C9.1, D3.1 (+), U1.3 (VI)
SENSE: C12.1, J6.2, J7.2, R7.2, U3.2 (VO)
SENSE_DC: C11.1, D5.1 (K), U3.3 (VI)
VNEG: J1.2, TR1.5
VPOS: J1.1, TR1.1

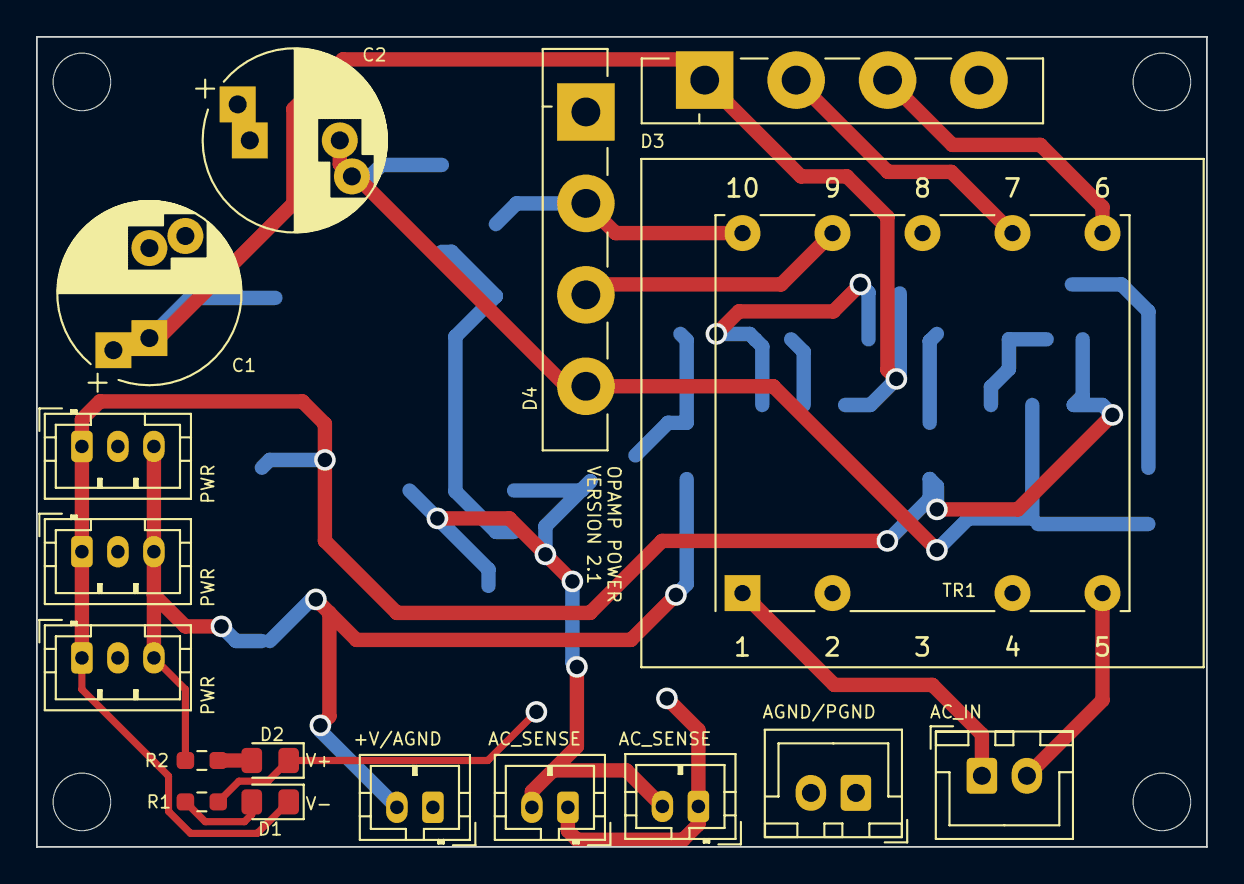
[picture p92: board OpampPower.kicad_pcb from above]

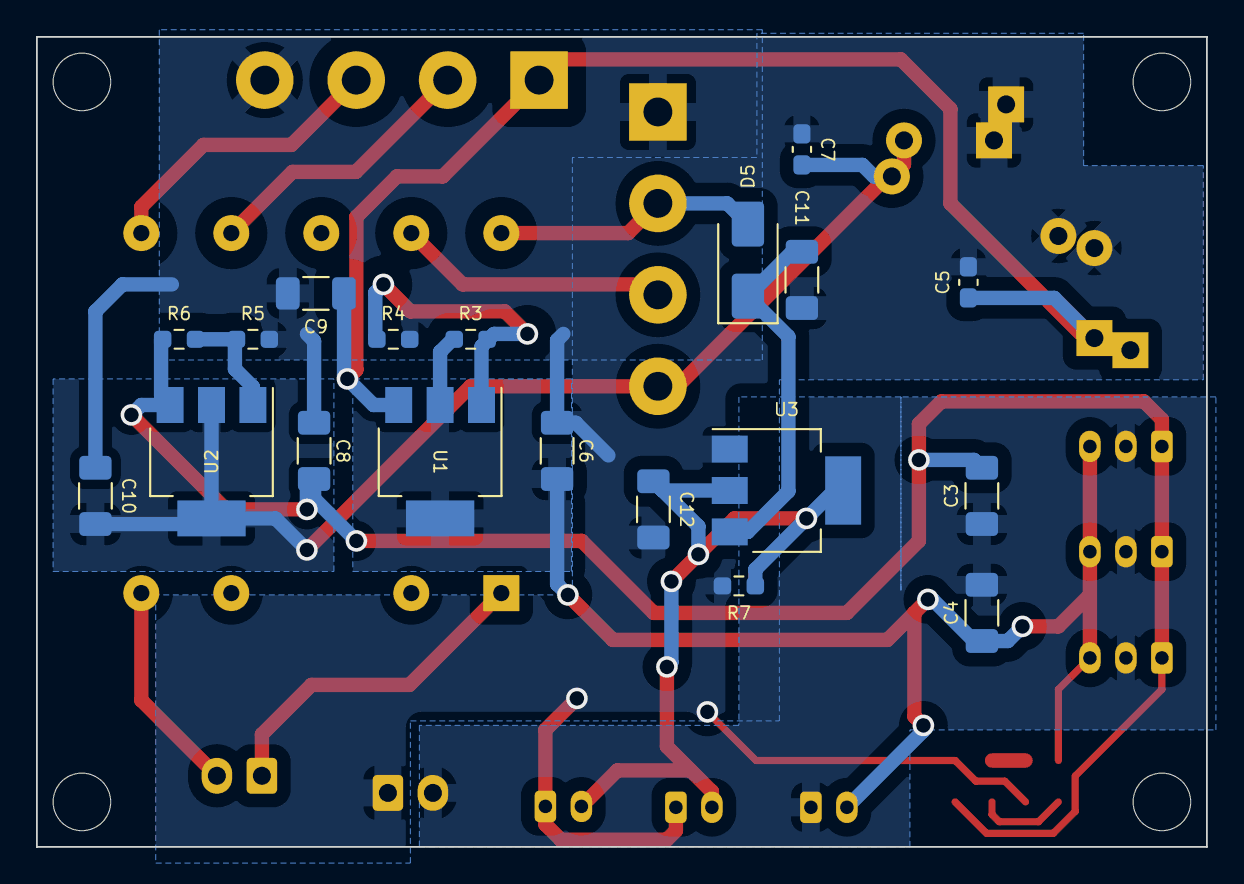
[picture p93: board OpampPower.kicad_pcb from below]

Board: 2 copper layers, 65.0 x 45.0 mm, 40 parts (19 on the bottom side), 18 nets.
