duanestorey/Hifi-Amplifier/PCBs/1/Channel Selector/1.3/ChannelSelector.kicad_pcb

## KiCad design PCBs/1/Channel Selector/1.3/ChannelSelector.kicad_pcb (2023-10-25)

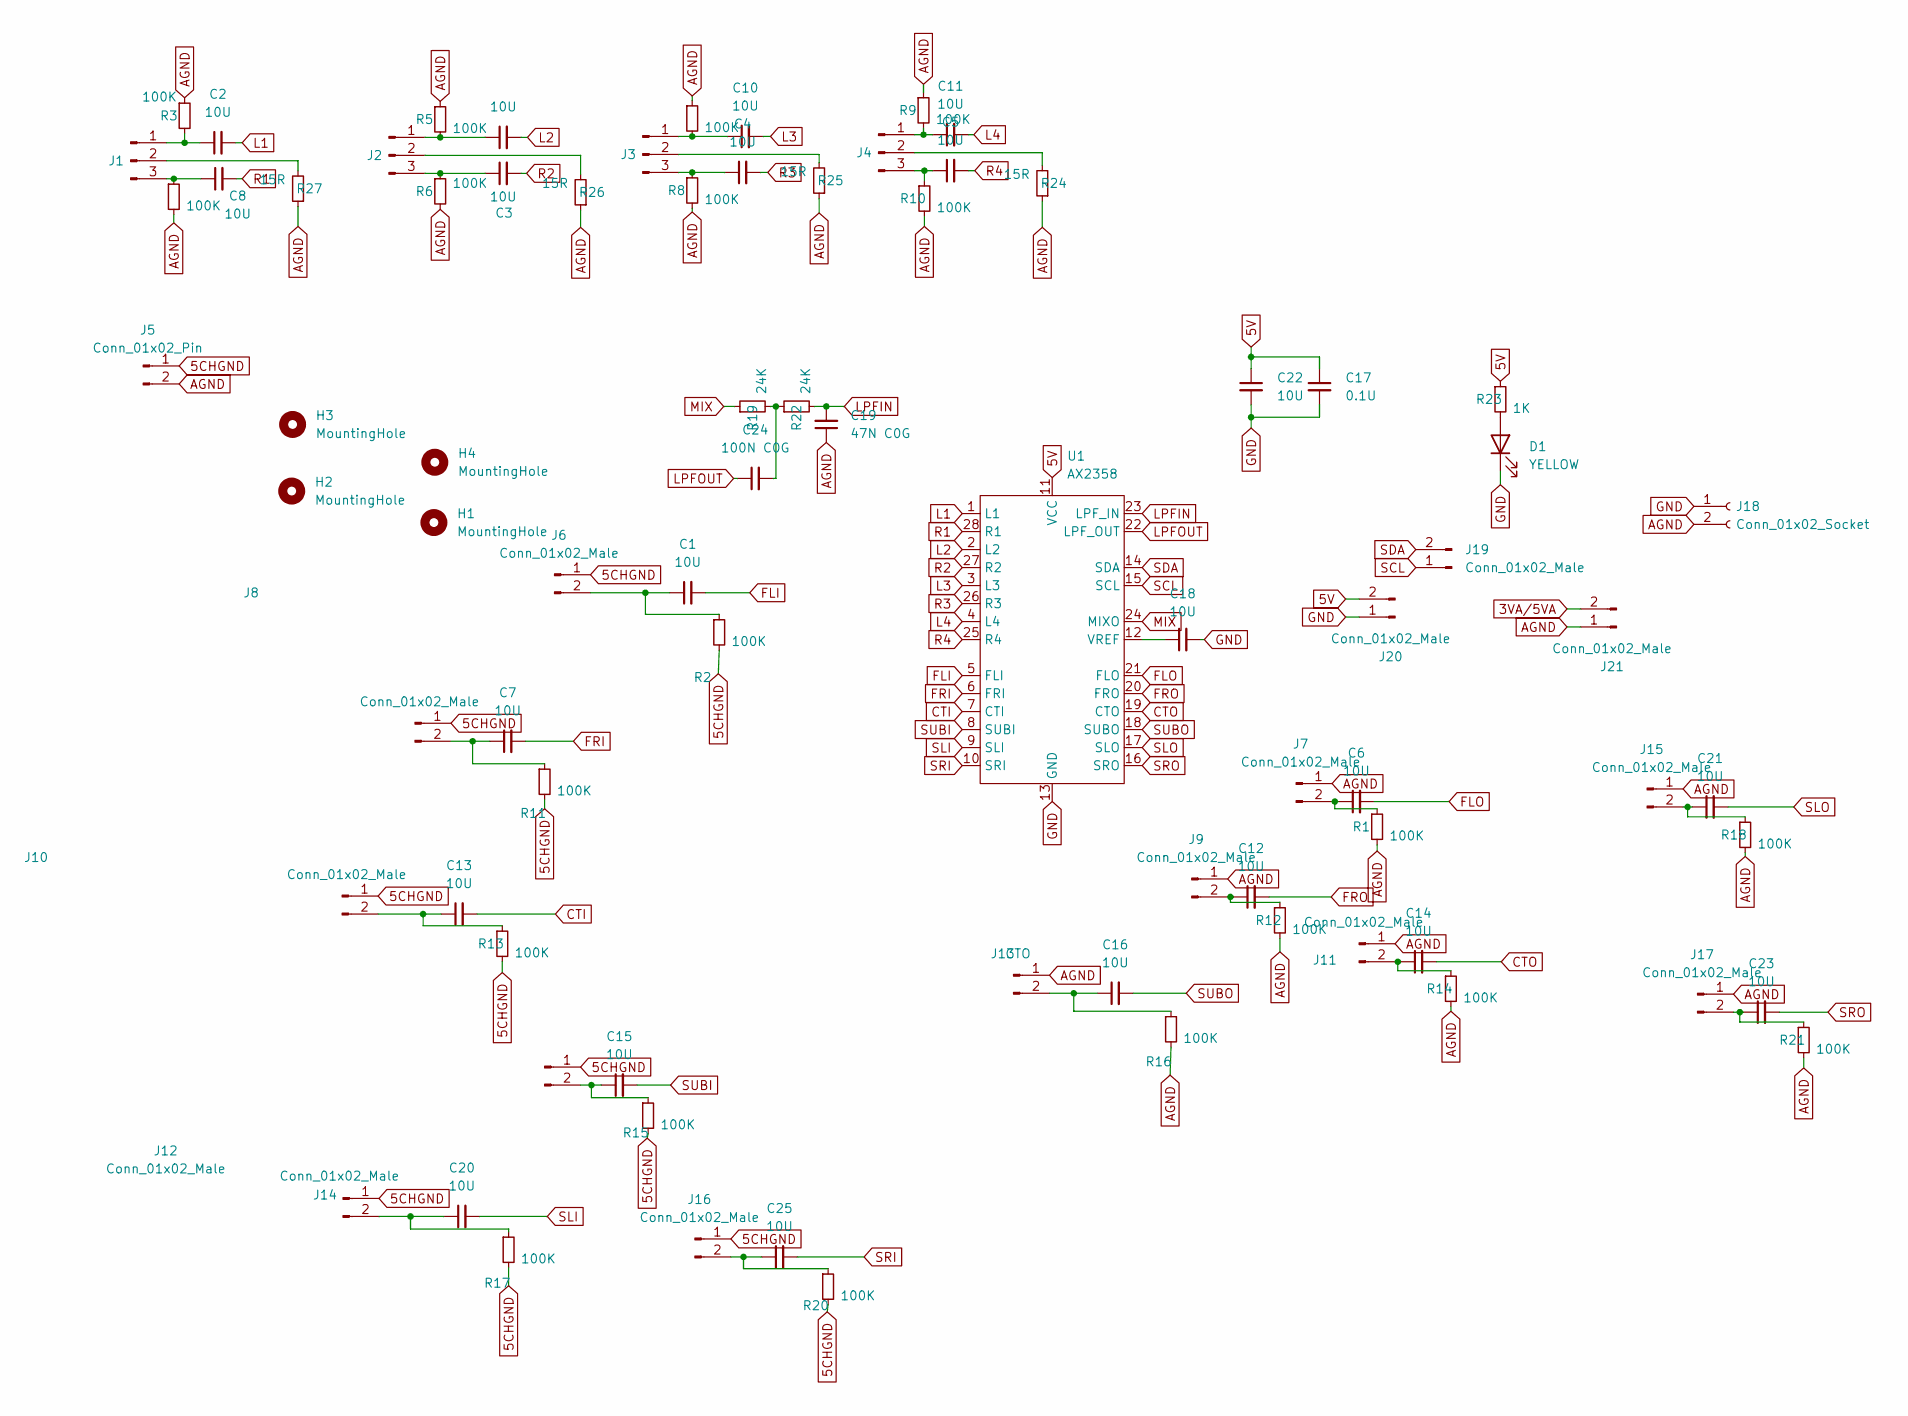
[picture p94: schematic ChannelSelector.kicad_sch]

Parts:
C1, C2, C3, C4, C5, C6, C7, C8, C9, C10, C11, C12, C13, C14, C15, C16, C20, C21, C23, C25: 10U; CP_Radial_D5.0mm_P2.50mm
C17: 0.1U; C_0805_2012Metric_Pad1.18x1.45mm_HandSolder
C18, C22: 10U; C_1206_3216Metric_Pad1.33x1.80mm_HandSolder
C19: 47N C0G; C_1206_3216Metric_Pad1.33x1.80mm_HandSolder
C24: 100N C0G; C_1206_3216Metric_Pad1.33x1.80mm_HandSolder
D1: YELLOW; LED_0805_2012Metric_Pad1.15x1.40mm_HandSolder
H1, H2, H3, H4: MountingHole; MountingHole_3.2mm_M3
J1, J2, J3, J4: Conn_01x03_Pin; JST_PH_B3B-PH-K_1x03_P2.00mm_Vertical
J5: Conn_01x02_Pin; PinHeader_1x02_P2.54mm_Vertical
J6, J7, J8, J9, J10, J11, J12, J14, J15, J16, J17, J19, J20, J21: Conn_01x02_Male; JST_PH_B2B-PH-K_1x02_P2.00mm_Vertical
J13: CTO; JST_PH_B2B-PH-K_1x02_P2.00mm_Vertical
J18: Conn_01x02_Socket; PinHeader_1x02_P2.54mm_Vertical
R1, R2, R3, R4, R5, R6, R7, R8, R9, R10, R11, R12, R13, R14, R15, R16, R17, R18, R20, R21: 100K; R_0805_2012Metric_Pad1.20x1.40mm_HandSolder
R19, R22: 24K; R_0805_2012Metric_Pad1.20x1.40mm_HandSolder
R23: 1K; R_0603_1608Metric_Pad0.98x0.95mm_HandSolder
R24, R25, R26, R27: 15R; R_0603_1608Metric_Pad0.98x0.95mm_HandSolder
U1: AX2358; SOIC-28W_7.5x18.7mm_P1.27mm

Connections:
3VA/5VA: J21.2
5CHGND: J5.1, J6.1, J8.1, J10.1, J12.1, J14.1, J16.1, R2.2, R11.2, R13.2, R15.2, R17.2, R20.2
5V: C17.1, C22.1, J20.2, R23.1, U1.11 (VCC)
AGND: C19.1, J5.2, J7.1, J9.1, J11.1, J13.1, J15.1, J17.1, J18.2, J21.1, R1.2, R3.1, R4.2, R5.1, R6.2, R7.1, R8.2, R9.1, R10.2, R12.2, R14.2, R16.2, R18.2, R21.2, R24.1, R25.1, R26.1, R27.1
CTI: C13.2, U1.7 (CTI)
CTO: C14.2, U1.19 (CTO)
FLI: C1.2, U1.5 (FLI)
FLO: C6.2, U1.21 (FLO)
FRI: C7.2, U1.6 (FRI)
FRO: C12.2, U1.20 (FRO)
GND: C17.2, C18.2, C22.2, D1.1 (K), J18.1, J20.1, U1.13 (GND)
L1: C2.2, U1.1 (L1)
L2: C9.2, U1.2 (L2)
L3: C10.2, U1.3 (L3)
L4: C11.2, U1.4 (L4)
LPFIN: C19.2, R22.2, U1.23 (LPF_IN)
LPFOUT: C24.1, U1.22 (LPF_OUT)
MIX: R19.1, U1.24 (MIXO)
unnamed: C24.2, R19.2, R22.1
unnamed: D1.2 (A), R23.2
unnamed: C2.1, J1.1, R3.2
unnamed: J1.2, R27.2
unnamed: C8.1, J1.3, R4.1
unnamed: C9.1, J2.1, R5.2
unnamed: J2.2, R26.2
unnamed: C3.1, J2.3, R6.1
unnamed: C10.1, J3.1, R7.2
unnamed: J3.2, R25.2
unnamed: C4.1, J3.3, R8.1
unnamed: C11.1, J4.1, R9.2
unnamed: J4.2, R24.2
unnamed: C5.1, J4.3, R10.1
unnamed: C1.1, J6.2, R2.1
unnamed: C6.1, J7.2, R1.1
unnamed: C7.1, J8.2, R11.1
unnamed: C12.1, J9.2, R12.1
unnamed: C13.1, J10.2, R13.1
unnamed: C14.1, J11.2, R14.1
unnamed: C15.1, J12.2, R15.1
unnamed: C16.1, J13.2, R16.1
unnamed: C20.1, J14.2, R17.1
unnamed: C21.1, J15.2, R18.1
unnamed: C25.1, J16.2, R20.1
unnamed: C23.1, J17.2, R21.1
unnamed: C18.1, U1.12 (VREF)
R1: C8.2, U1.28 (R1)
R2: C3.2, U1.27 (R2)
R3: C4.2, U1.26 (R3)
R4: C5.2, U1.25 (R4)
SCL: J19.1, U1.15 (SCL)
SDA: J19.2, U1.14 (SDA)
SLI: C20.2, U1.9 (SLI)
SLO: C21.2, U1.17 (SLO)
SRI: C25.2, U1.10 (SRI)
SRO: C23.2, U1.16 (SRO)
SUBI: C15.2, U1.8 (SUBI)
SUBO: C16.2, U1.18 (SUBO)
