duanestorey/Hifi-Amplifier/PCBs/1/Channel Selector/1.3/ChannelSelector.kicad_pcb

## KiCad design PCBs/1/Channel Selector/1.3/ChannelSelector.kicad_pcb (continued)

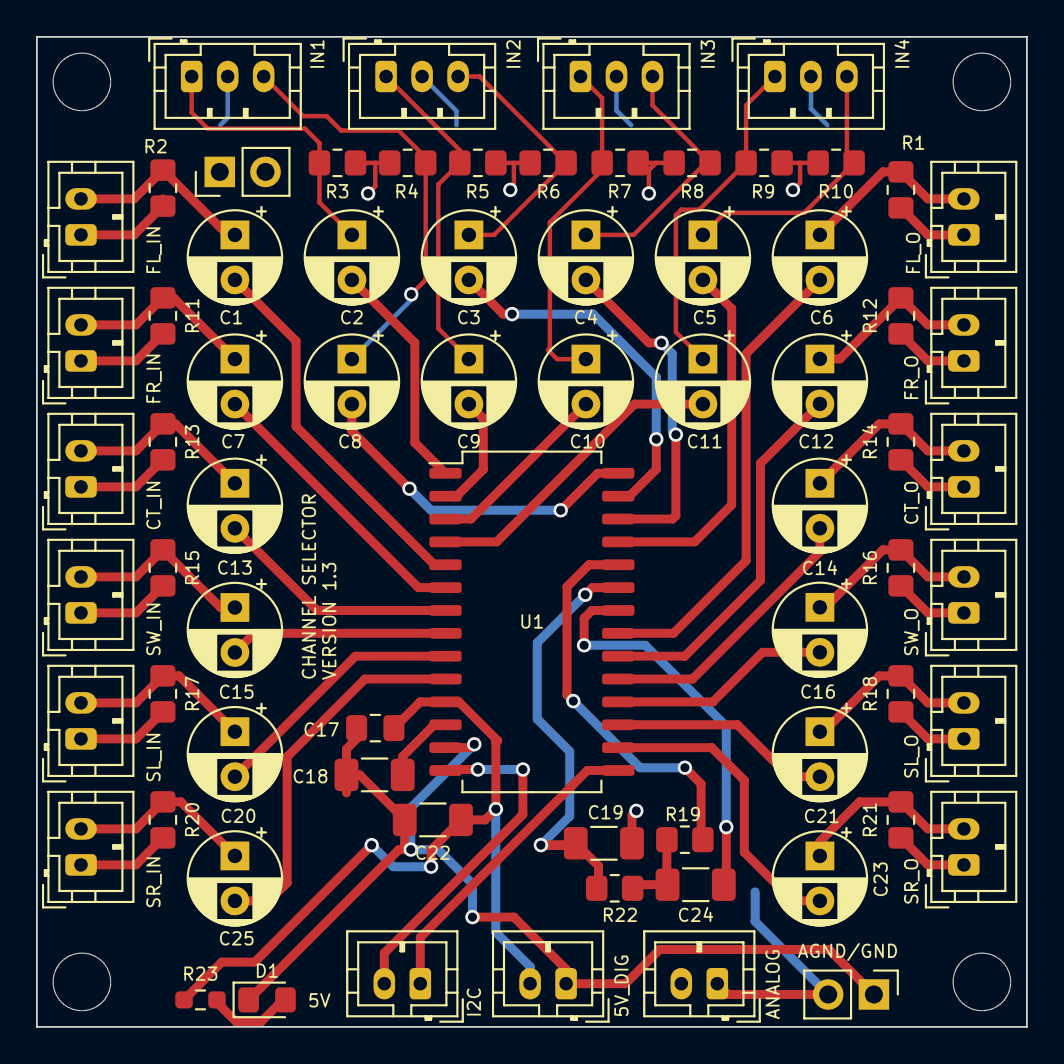
[picture p95: board PCBs/1/Channel Selector/1.3/ChannelSelector.kicad_pcb from above]

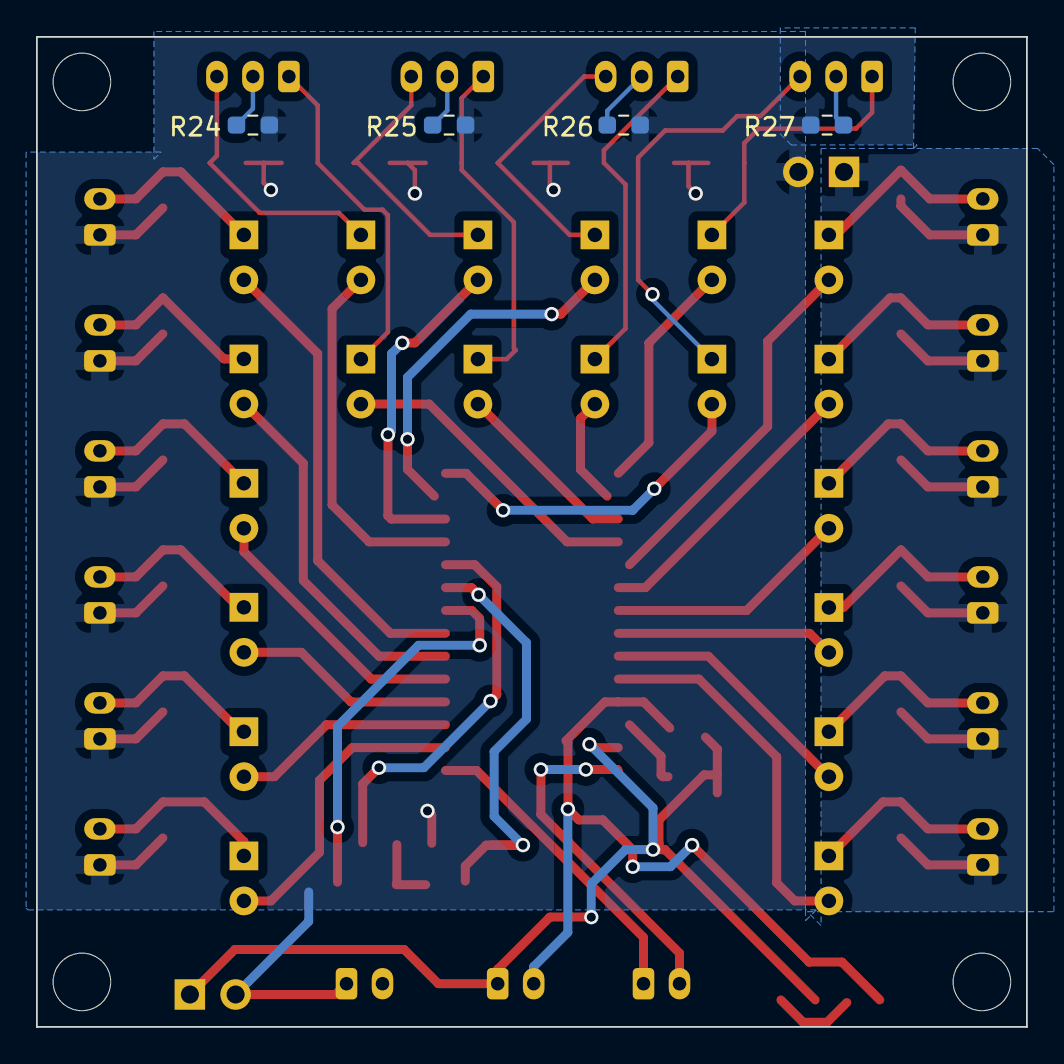
[picture p96: board PCBs/1/Channel Selector/1.3/ChannelSelector.kicad_pcb from below]

Board: 2 copper layers, 55.0 x 55.0 mm, 79 parts (4 on the bottom side), 56 nets.
