duanestorey/Hifi-Amplifier/PCBs/_Archive/DAC PCM5122/1.1/DAC.kicad_pcb

## KiCad design PCBs/_Archive/DAC PCM5122/1.1/DAC.kicad_pcb (2023-10-27, an earlier design)

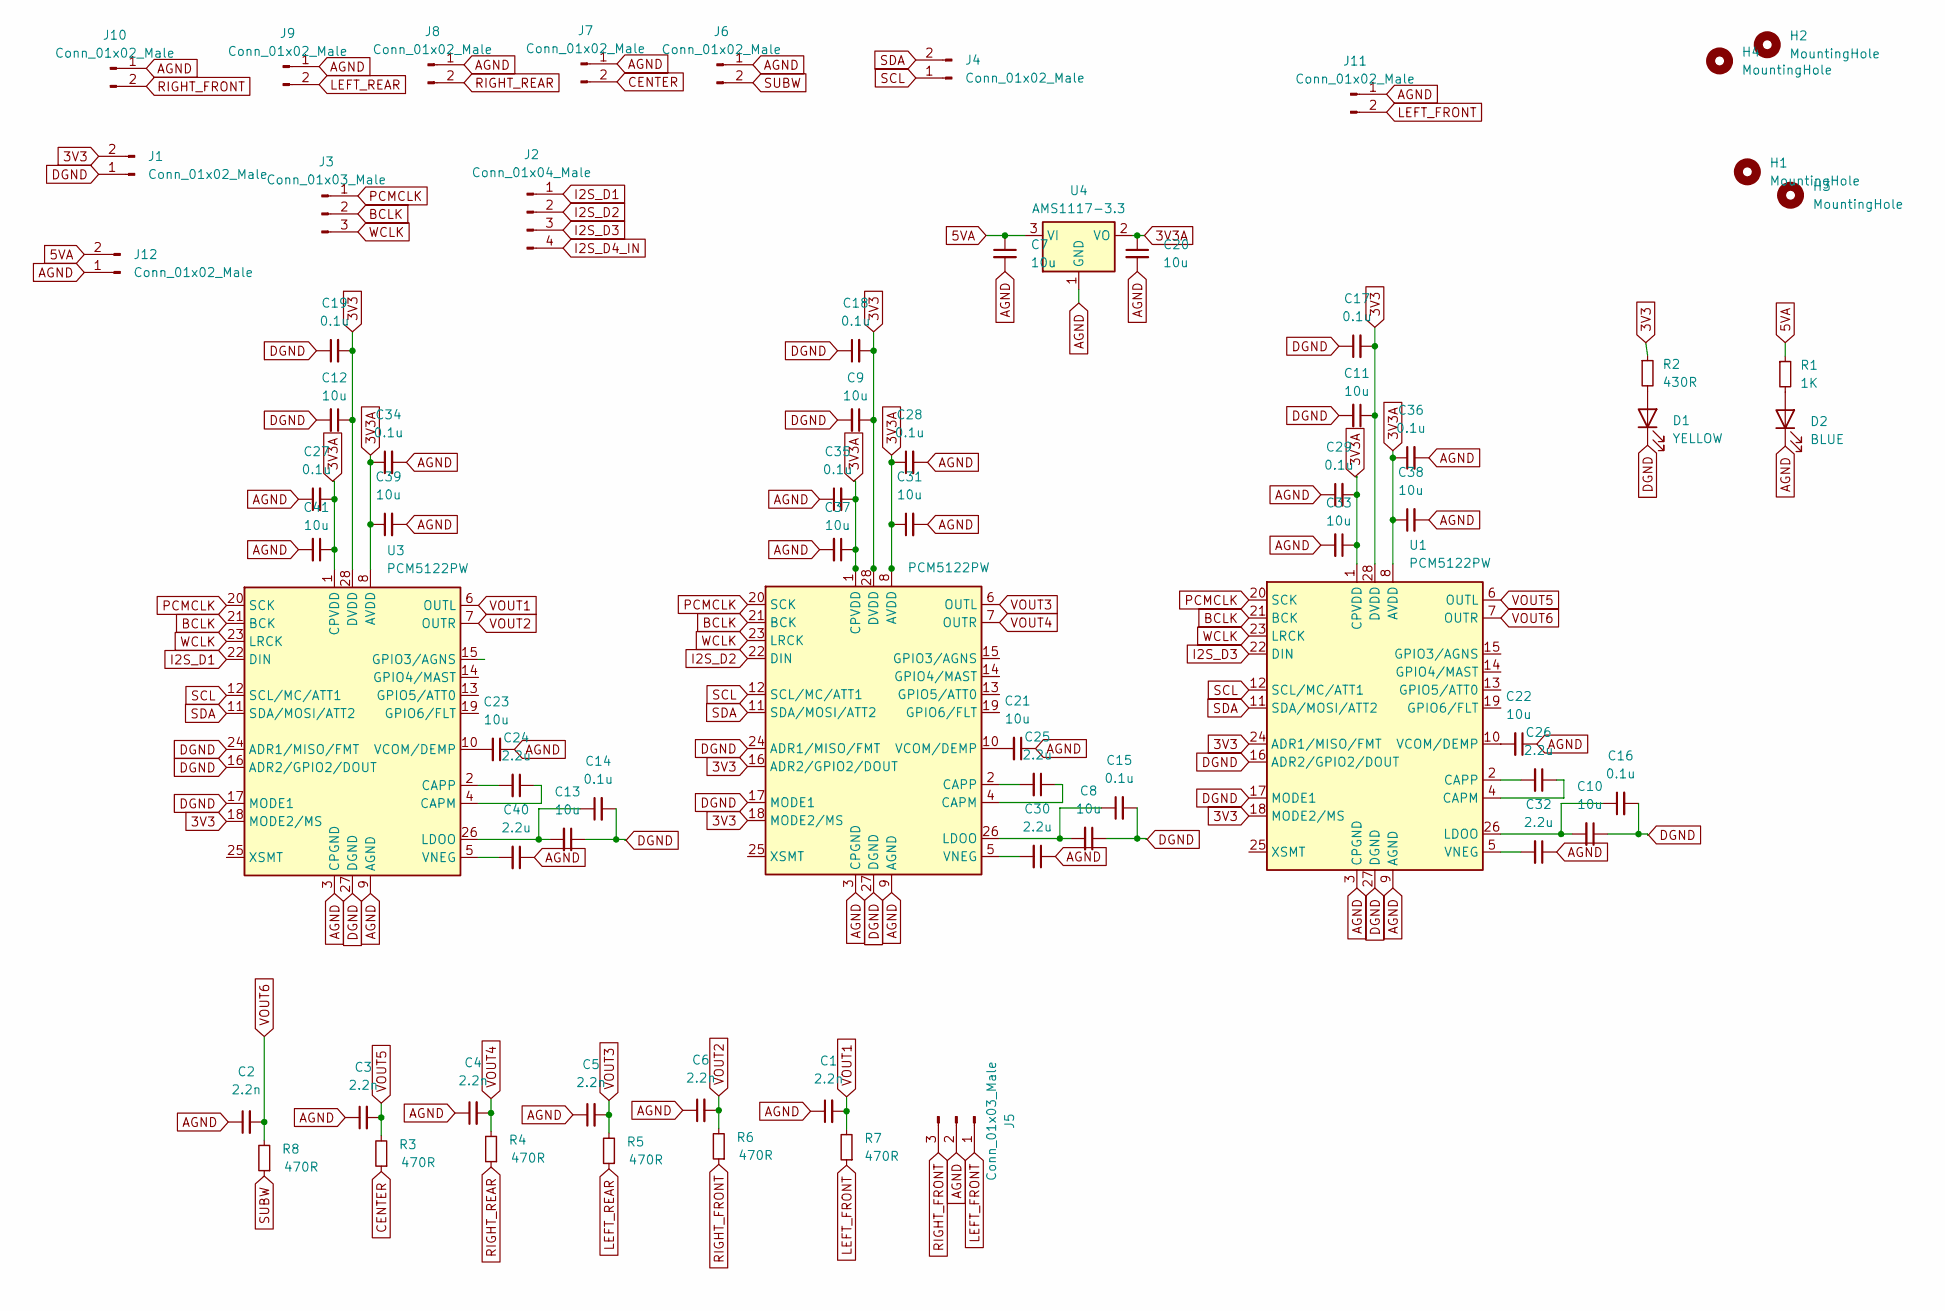
[picture p97: schematic DAC.kicad_sch]

Parts:
C1, C2, C3, C4, C5, C6: 2.2n; C_1206_3216Metric_Pad1.33x1.80mm_HandSolder
C7, C8, C9, C10, C11, C12, C13, C20, C21, C22, C23, C31, C33, C37, C38, C39, C41: 10u; C_1206_3216Metric_Pad1.33x1.80mm_HandSolder
C14, C15, C16, C17, C18, C19, C27, C28, C29, C34, C35, C36: 0.1u; C_0805_2012Metric_Pad1.18x1.45mm_HandSolder
C24, C25, C26, C30, C32, C40: 2.2u; C_1206_3216Metric_Pad1.33x1.80mm_HandSolder
D1: YELLOW; LED_0805_2012Metric_Pad1.15x1.40mm_HandSolder
D2: BLUE; LED_0805_2012Metric_Pad1.15x1.40mm_HandSolder
H1, H2, H3, H4: MountingHole; MountingHole_3.2mm_M3
J1, J4, J6, J7, J8, J9, J10, J11, J12: Conn_01x02_Male; JST_PH_B2B-PH-K_1x02_P2.00mm_Vertical
J2: Conn_01x04_Male; JST_PH_B4B-PH-K_1x04_P2.00mm_Vertical
J3: Conn_01x03_Male; JST_PH_B3B-PH-K_1x03_P2.00mm_Vertical
J5: Conn_01x03_Male; PinHeader_1x03_P2.54mm_Vertical
R1: 1K; R_0603_1608Metric_Pad0.98x0.95mm_HandSolder
R2: 430R; R_0603_1608Metric_Pad0.98x0.95mm_HandSolder
R3, R4, R5, R6, R7, R8: 470R; R_1206_3216Metric_Pad1.30x1.75mm_HandSolder
U1, U2, U3: PCM5122PW; TSSOP-28_4.4x9.7mm_P0.65mm
U4: AMS1117-3.3; SOT-223-3_TabPin2

Connections:
3V3: C9.1, C11.1, C12.1, C17.2, C18.2, C19.2, J1.2, R2.1, U1.18 (MODE2/MS), U1.24 (ADR1/MISO/FMT), U1.28 (DVDD), U2.16 (ADR2/GPIO2/DOUT), U2.18 (MODE2/MS), U2.28 (DVDD), U3.18 (MODE2/MS), U3.28 (DVDD)
3V3A: C20.1, C27.2, C28.1, C29.2, C31.1, C33.1, C34.1, C35.2, C36.1, C37.1, C38.1, C39.1, C41.1, U1.1 (CPVDD), U1.8 (AVDD), U2.1 (CPVDD), U2.8 (AVDD), U3.1 (CPVDD), U3.8 (AVDD), U4.2 (VO)
5VA: C7.1, J12.2, R1.1, U4.3 (VI)
AGND: C1.1, C2.1, C3.1, C4.1, C5.1, C6.1, C7.2, C20.2, C21.1, C22.1, C23.1, C27.1, C28.2, C29.1, C30.1, C31.2, C32.1, C33.2, C34.2, C35.1, C36.2, C37.2, C38.2, C39.2, C40.1, C41.2, D2.1 (K), J5.2, J6.1, J7.1, J8.1, J9.1, J10.1, J11.1, J12.1, U1.3 (CPGND), U1.9 (AGND), U2.3 (CPGND), U2.9 (AGND), U3.3 (CPGND), U3.9 (AGND), U4.1 (GND)
BCLK: J3.2, U1.21 (BCK), U2.21 (BCK), U3.21 (BCK)
CENTER: J7.2, R3.1
DGND: C8.1, C9.2, C10.1, C11.2, C12.2, C13.1, C14.2, C15.2, C16.2, C17.1, C18.1, C19.1, D1.1 (K), J1.1, U1.16 (ADR2/GPIO2/DOUT), U1.17 (MODE1), U1.27 (DGND), U2.17 (MODE1), U2.24 (ADR1/MISO/FMT), U2.27 (DGND), U3.16 (ADR2/GPIO2/DOUT), U3.17 (MODE1), U3.24 (ADR1/MISO/FMT), U3.27 (DGND)
I2S_D1: J2.1, U3.22 (DIN)
I2S_D2: J2.2, U2.22 (DIN)
I2S_D3: J2.3, U1.22 (DIN)
I2S_D4_IN: J2.4
LEFT_FRONT: J5.1, J11.2, R7.1
LEFT_REAR: J9.2, R5.1
unnamed: D1.2 (A), R2.2
unnamed: D2.2 (A), R1.2
unnamed: C26.1, U1.4 (CAPM)
unnamed: C26.2, U1.2 (CAPP)
unnamed: C10.2, C16.1, U1.26 (LDOO)
unnamed: C22.2, U1.10 (VCOM/DEMP)
unnamed: C32.2, U1.5 (VNEG)
unnamed: C25.1, U2.4 (CAPM)
unnamed: C25.2, U2.2 (CAPP)
unnamed: C8.2, C15.1, U2.26 (LDOO)
unnamed: C21.2, U2.10 (VCOM/DEMP)
unnamed: C30.2, U2.5 (VNEG)
unnamed: C24.1, U3.4 (CAPM)
unnamed: C24.2, U3.2 (CAPP)
unnamed: C13.2, C14.1, U3.26 (LDOO)
unnamed: C23.2, U3.10 (VCOM/DEMP)
unnamed: C40.2, U3.5 (VNEG)
PCMCLK: J3.1, U1.20 (SCK), U2.20 (SCK), U3.20 (SCK)
RIGHT_FRONT: J5.3, J10.2, R6.1
RIGHT_REAR: J8.2, R4.1
SCL: J4.1, U1.12 (SCL/MC/ATT1), U2.12 (SCL/MC/ATT1), U3.12 (SCL/MC/ATT1)
SDA: J4.2, U1.11 (SDA/MOSI/ATT2), U2.11 (SDA/MOSI/ATT2), U3.11 (SDA/MOSI/ATT2)
SUBW: J6.2, R8.1
VOUT1: C1.2, R7.2, U3.6 (OUTL)
VOUT2: C6.2, R6.2, U3.7 (OUTR)
VOUT3: C5.2, R5.2, U2.6 (OUTL)
VOUT4: C4.2, R4.2, U2.7 (OUTR)
VOUT5: C3.2, R3.2, U1.6 (OUTL)
VOUT6: C2.2, R8.2, U1.7 (OUTR)
WCLK: J3.3, U1.23 (LRCK), U2.23 (LRCK), U3.23 (LRCK)

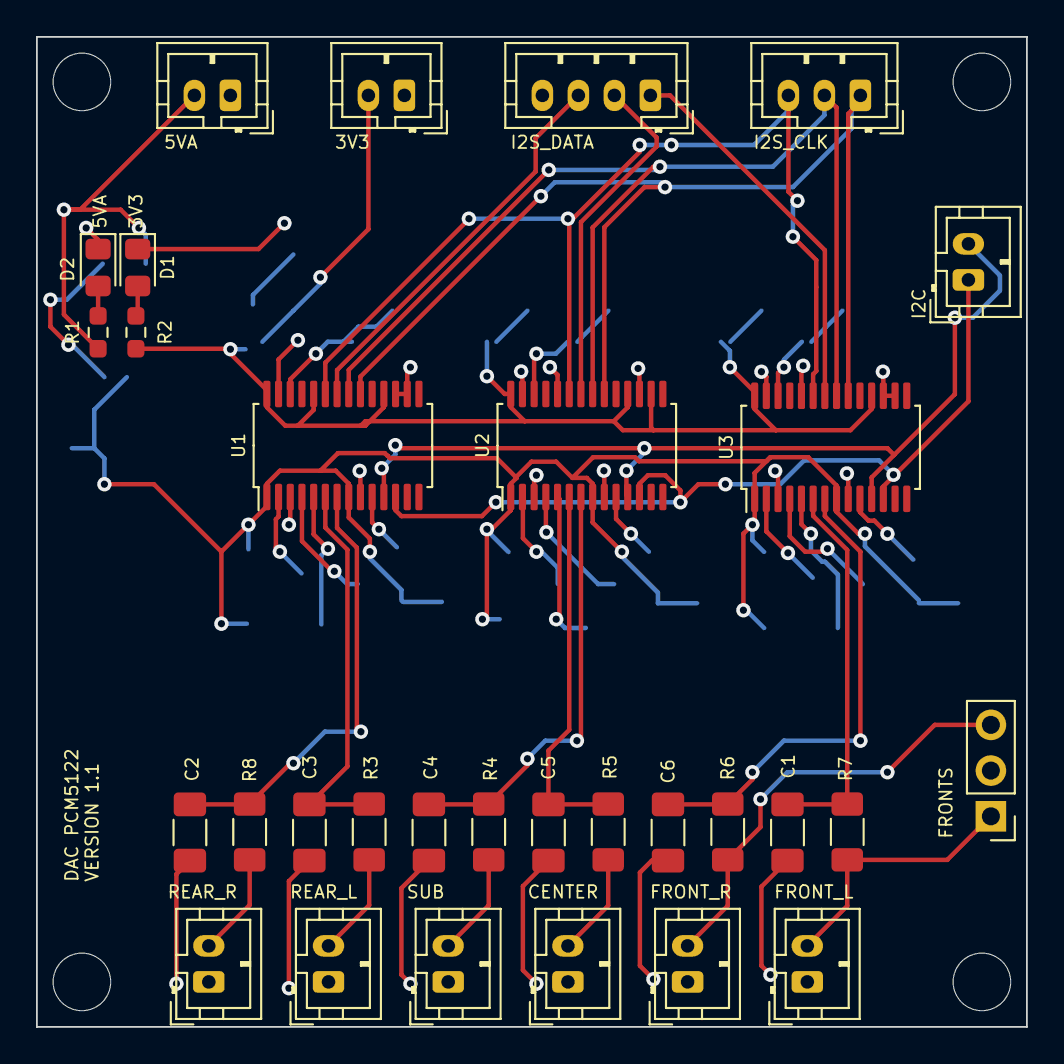
[picture p98: board PCBs/_Archive/DAC PCM5122/1.1/DAC.kicad_pcb from above]

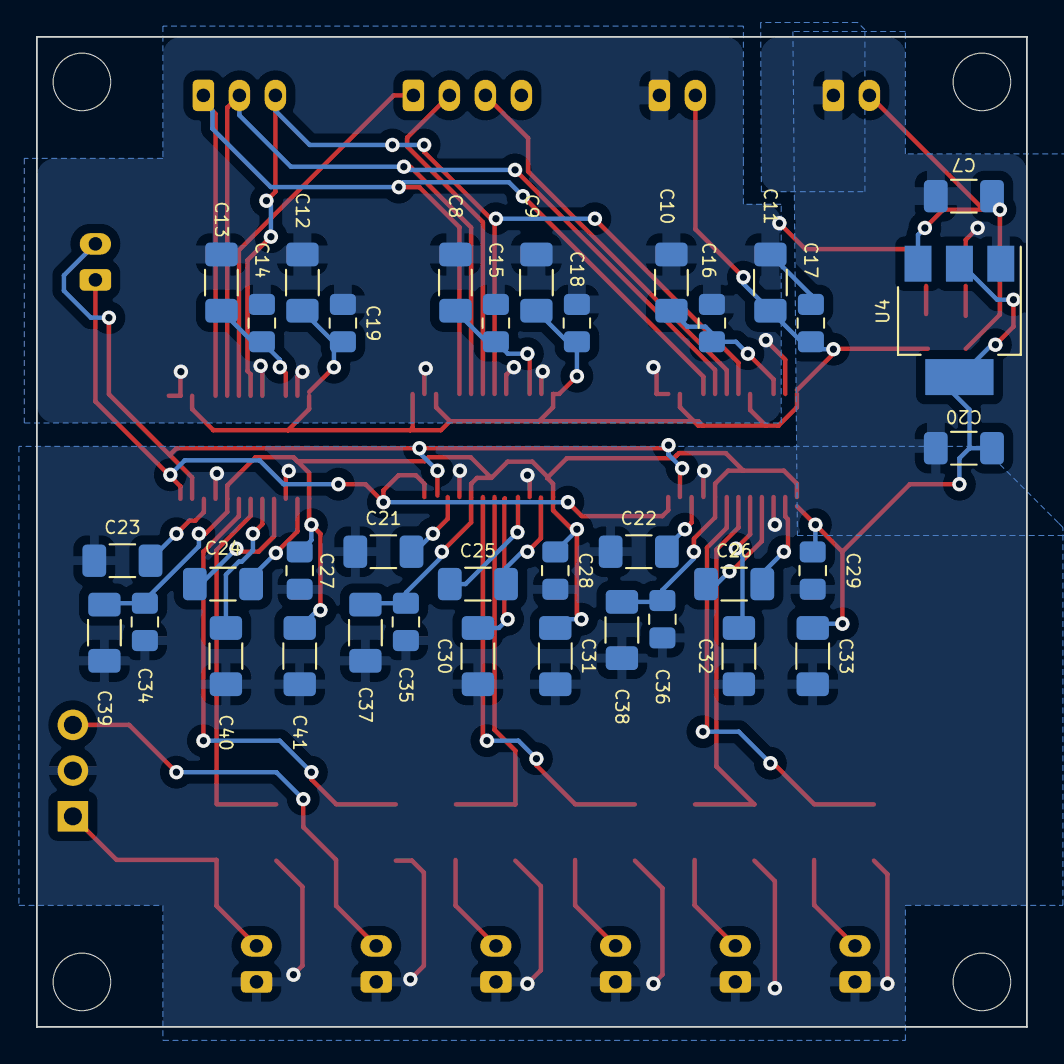
[picture p99: board PCBs/_Archive/DAC PCM5122/1.1/DAC.kicad_pcb from below]

Board: 2 copper layers, 55.0 x 55.0 mm, 71 parts (36 on the bottom side), 42 nets.
