duanestorey/Hifi-Amplifier/PCBs/1/Power Supply (Digital)/2.1/DPSU.kicad_pcb

## KiCad design PCBs/1/Power Supply (Digital)/2.1/DPSU.kicad_pcb (2023-10-31)

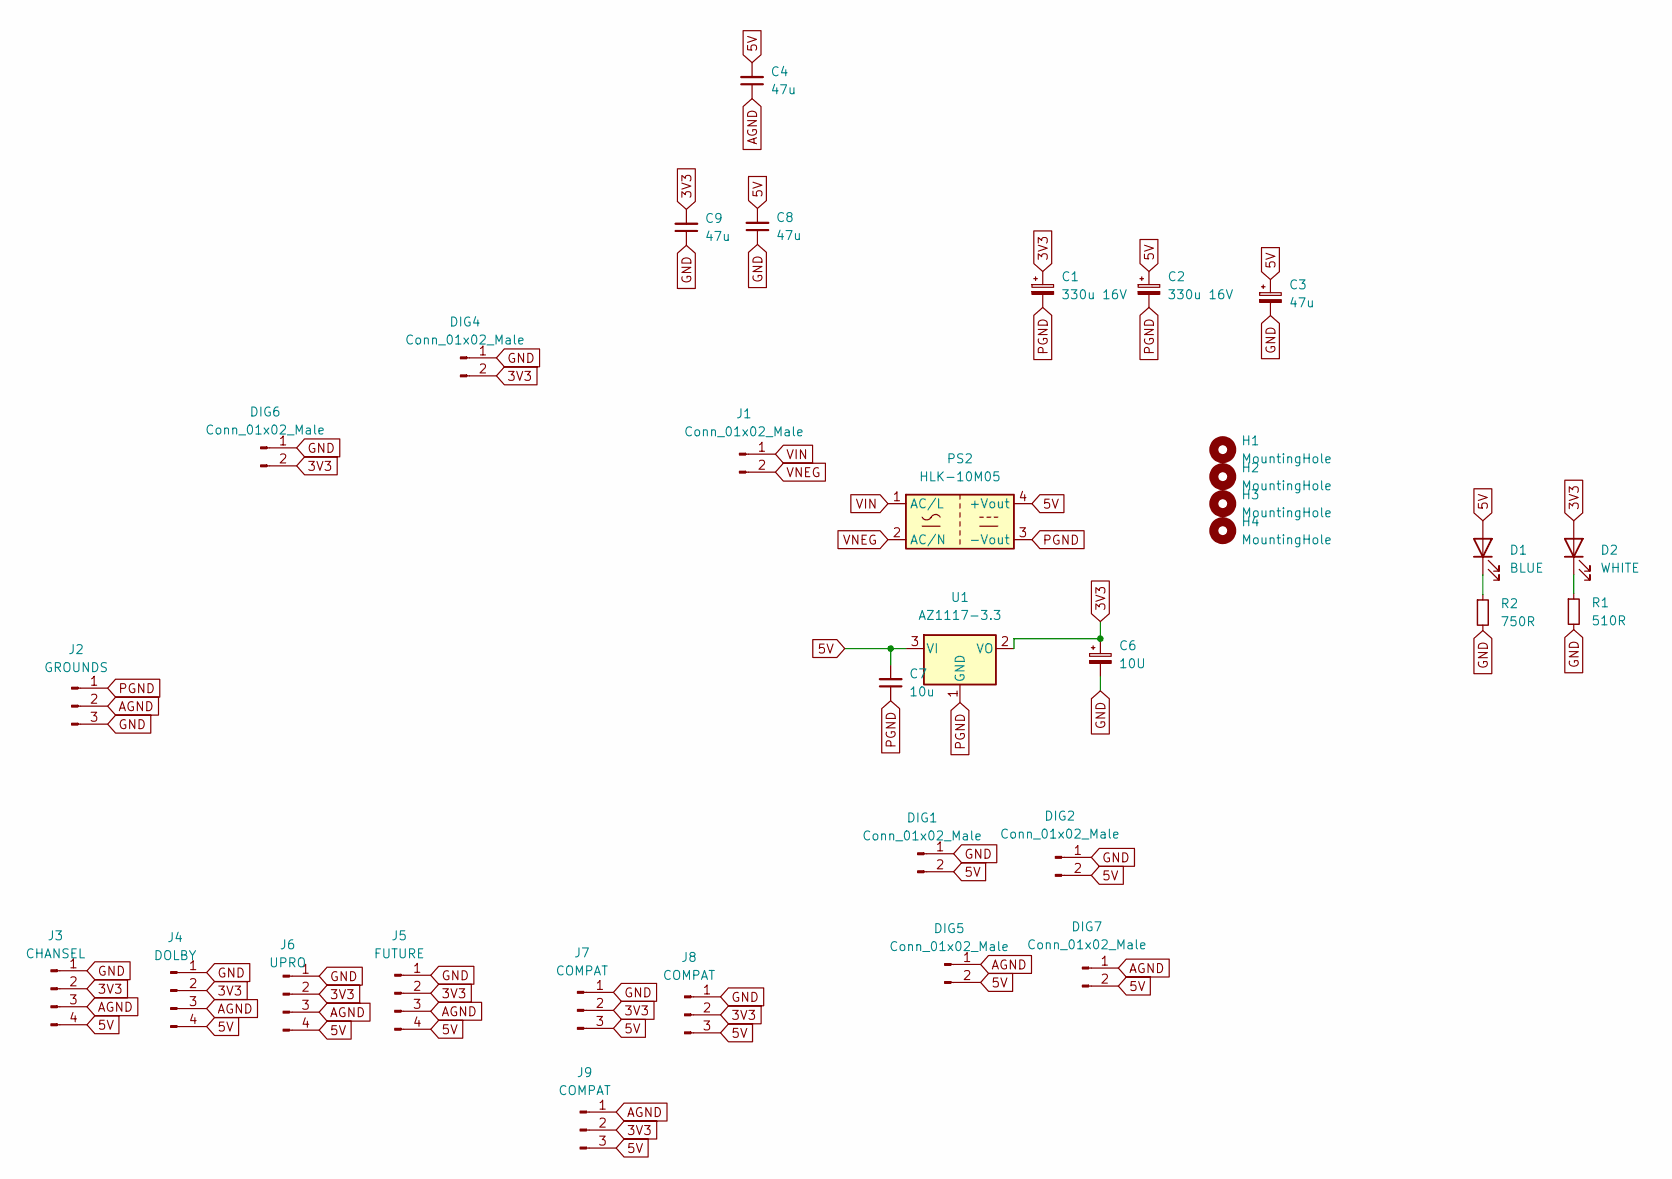
[picture p100: schematic DPSU.kicad_sch]

Parts:
C1, C2: 330u 16V; CP_Radial_D8.0mm_P2.50mm
C3, C4, C8, C9: 47u; C_1206_3216Metric_Pad1.33x1.80mm_HandSolder
C6: 10U; C_1206_3216Metric_Pad1.33x1.80mm_HandSolder
C7: 10u; C_1206_3216Metric_Pad1.33x1.80mm_HandSolder
D1: BLUE; LED_0805_2012Metric_Pad1.15x1.40mm_HandSolder
D2: WHITE; LED_0805_2012Metric_Pad1.15x1.40mm_HandSolder
DIG1, DIG2, DIG4, DIG5, DIG6, DIG7: Conn_01x02_Male; JST_PH_B2B-PH-K_1x02_P2.00mm_Vertical
H1, H2, H3, H4: MountingHole; MountingHole_3.2mm_M3
J1: Conn_01x02_Male; JST_XH_B2B-XH-A_1x02_P2.50mm_Vertical
J2: GROUNDS; JST_XH_B3B-XH-A_1x03_P2.50mm_Vertical
J3: CHANSEL; JST_XH_B4B-XH-A_1x04_P2.50mm_Vertical
J4: DOLBY; JST_XH_B4B-XH-A_1x04_P2.50mm_Vertical
J5: FUTURE; JST_XH_B4B-XH-A_1x04_P2.50mm_Vertical
J6: UPRO; JST_XH_B4B-XH-A_1x04_P2.50mm_Vertical
J7, J8, J9: COMPAT; JST_PH_B3B-PH-K_1x03_P2.00mm_Vertical
PS2: HLK-10M05
R1: 510R; R_0805_2012Metric_Pad1.20x1.40mm_HandSolder
R2: 750R; R_0805_2012Metric_Pad1.20x1.40mm_HandSolder
U1: AZ1117-3.3; SOT-223

Connections:
3V3: C1.1, C6.1, C9.2, D2.2 (A), DIG4.2, DIG6.2, J3.2, J4.2, J5.2, J6.2, J7.2, J8.2, J9.2, U1.2 (VO)
5V: C2.1, C3.1, C4.2, C7.2, C8.2, D1.2 (A), DIG1.2, DIG2.2, DIG5.2, DIG7.2, J3.4, J4.4, J5.4, J6.4, J7.3, J8.3, J9.3, PS2.4 (+Vout), U1.3 (VI)
AGND: C4.1, DIG5.1, DIG7.1, J2.2, J3.3, J4.3, J5.3, J6.3, J9.1
GND: C3.2, C6.2, C8.1, C9.1, DIG1.1, DIG2.1, DIG4.1, DIG6.1, J2.3, J3.1, J4.1, J5.1, J6.1, J7.1, J8.1, R1.2, R2.2
unnamed: D1.1 (K), R2.1
unnamed: D2.1 (K), R1.1
PGND: C1.2, C2.2, C7.1, J2.1, PS2.3 (-Vout), U1.1 (GND)
VIN: J1.1, PS2.1 (AC/L)
VNEG: J1.2, PS2.2 (AC/N)

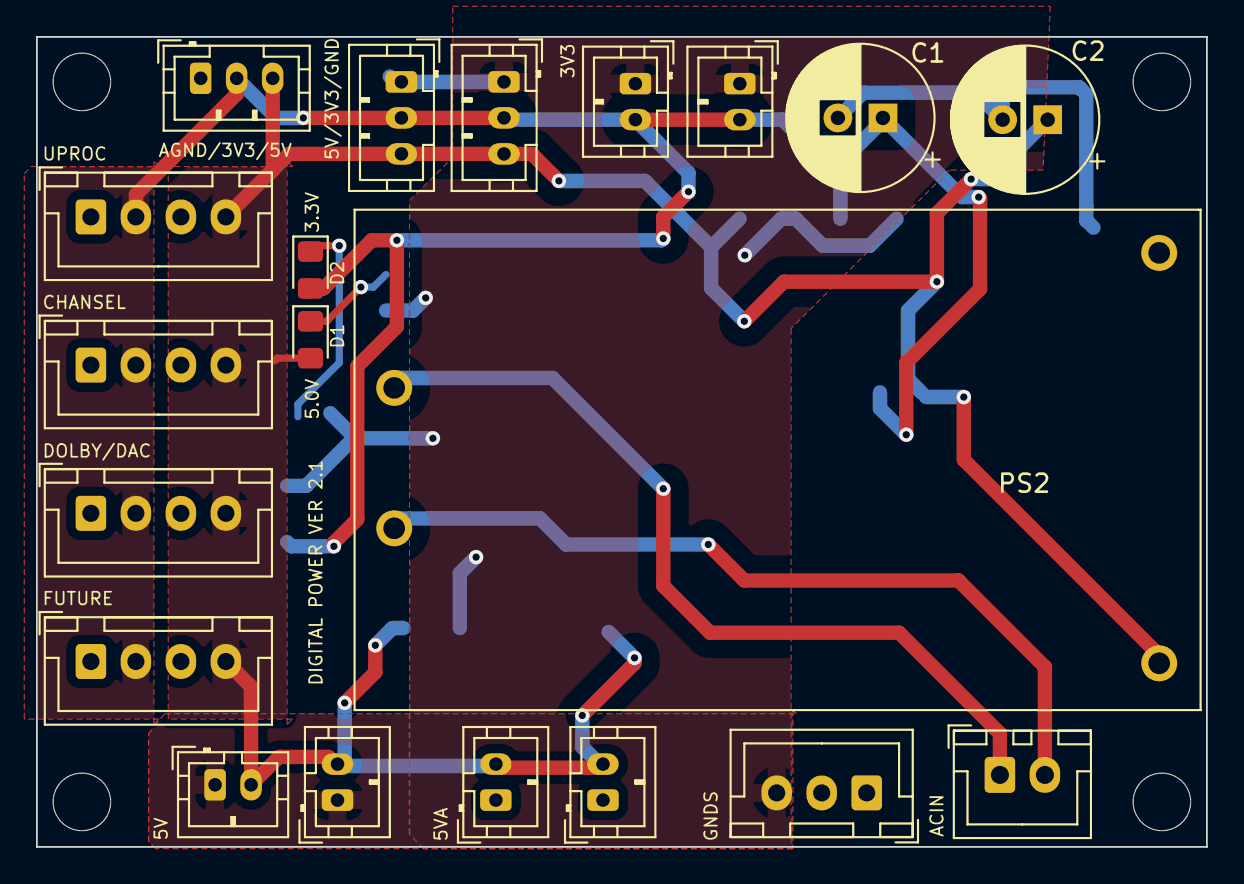
[picture p101: board DPSU.kicad_pcb from above]

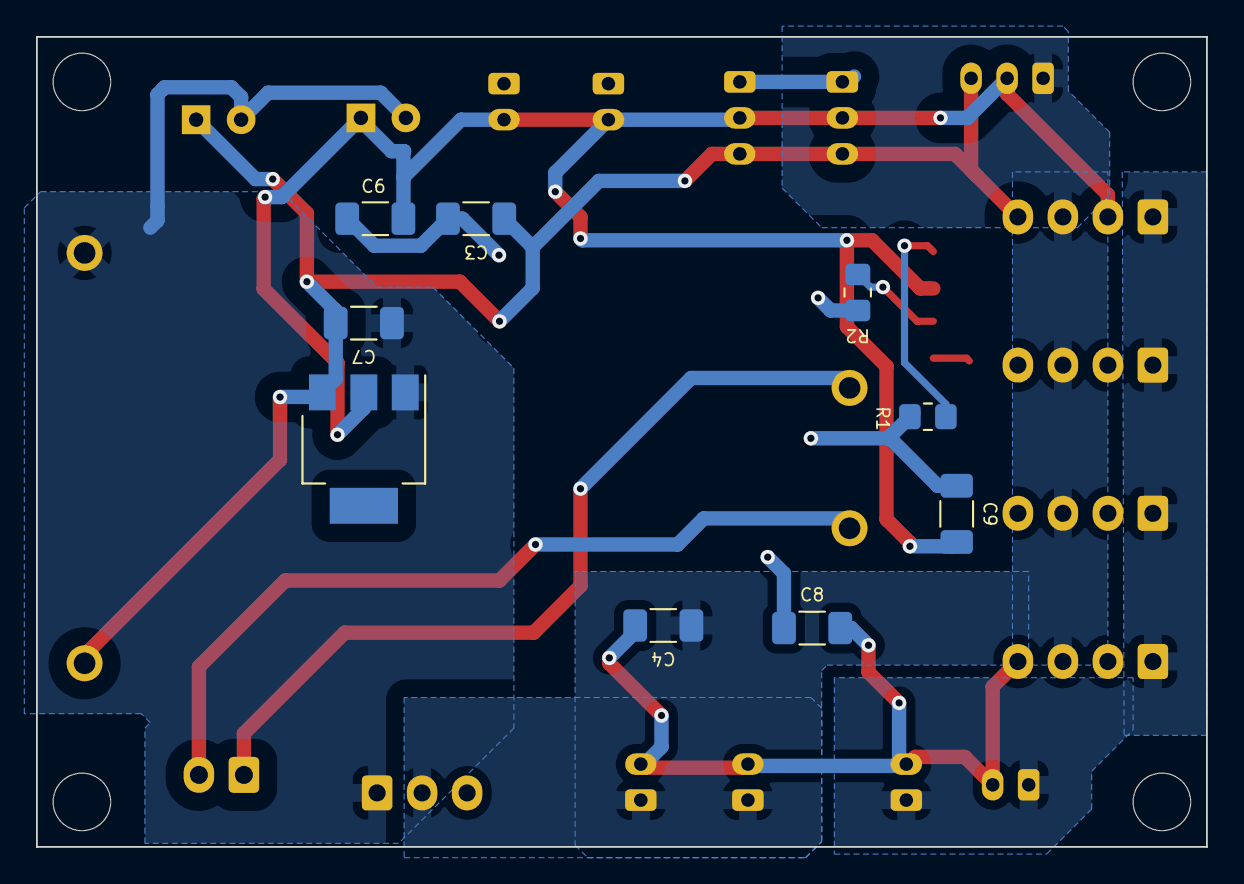
[picture p102: board DPSU.kicad_pcb from below]

Board: 2 copper layers, 65.0 x 45.0 mm, 33 parts (9 on the bottom side), 9 nets.
