duanestorey/Hifi-Amplifier/PCBs/CS8416 SPDIF/3.0/DAC.kicad_sch

## KiCad design PCBs/CS8416 SPDIF/3.0/DAC.kicad_sch (2024-11-29)

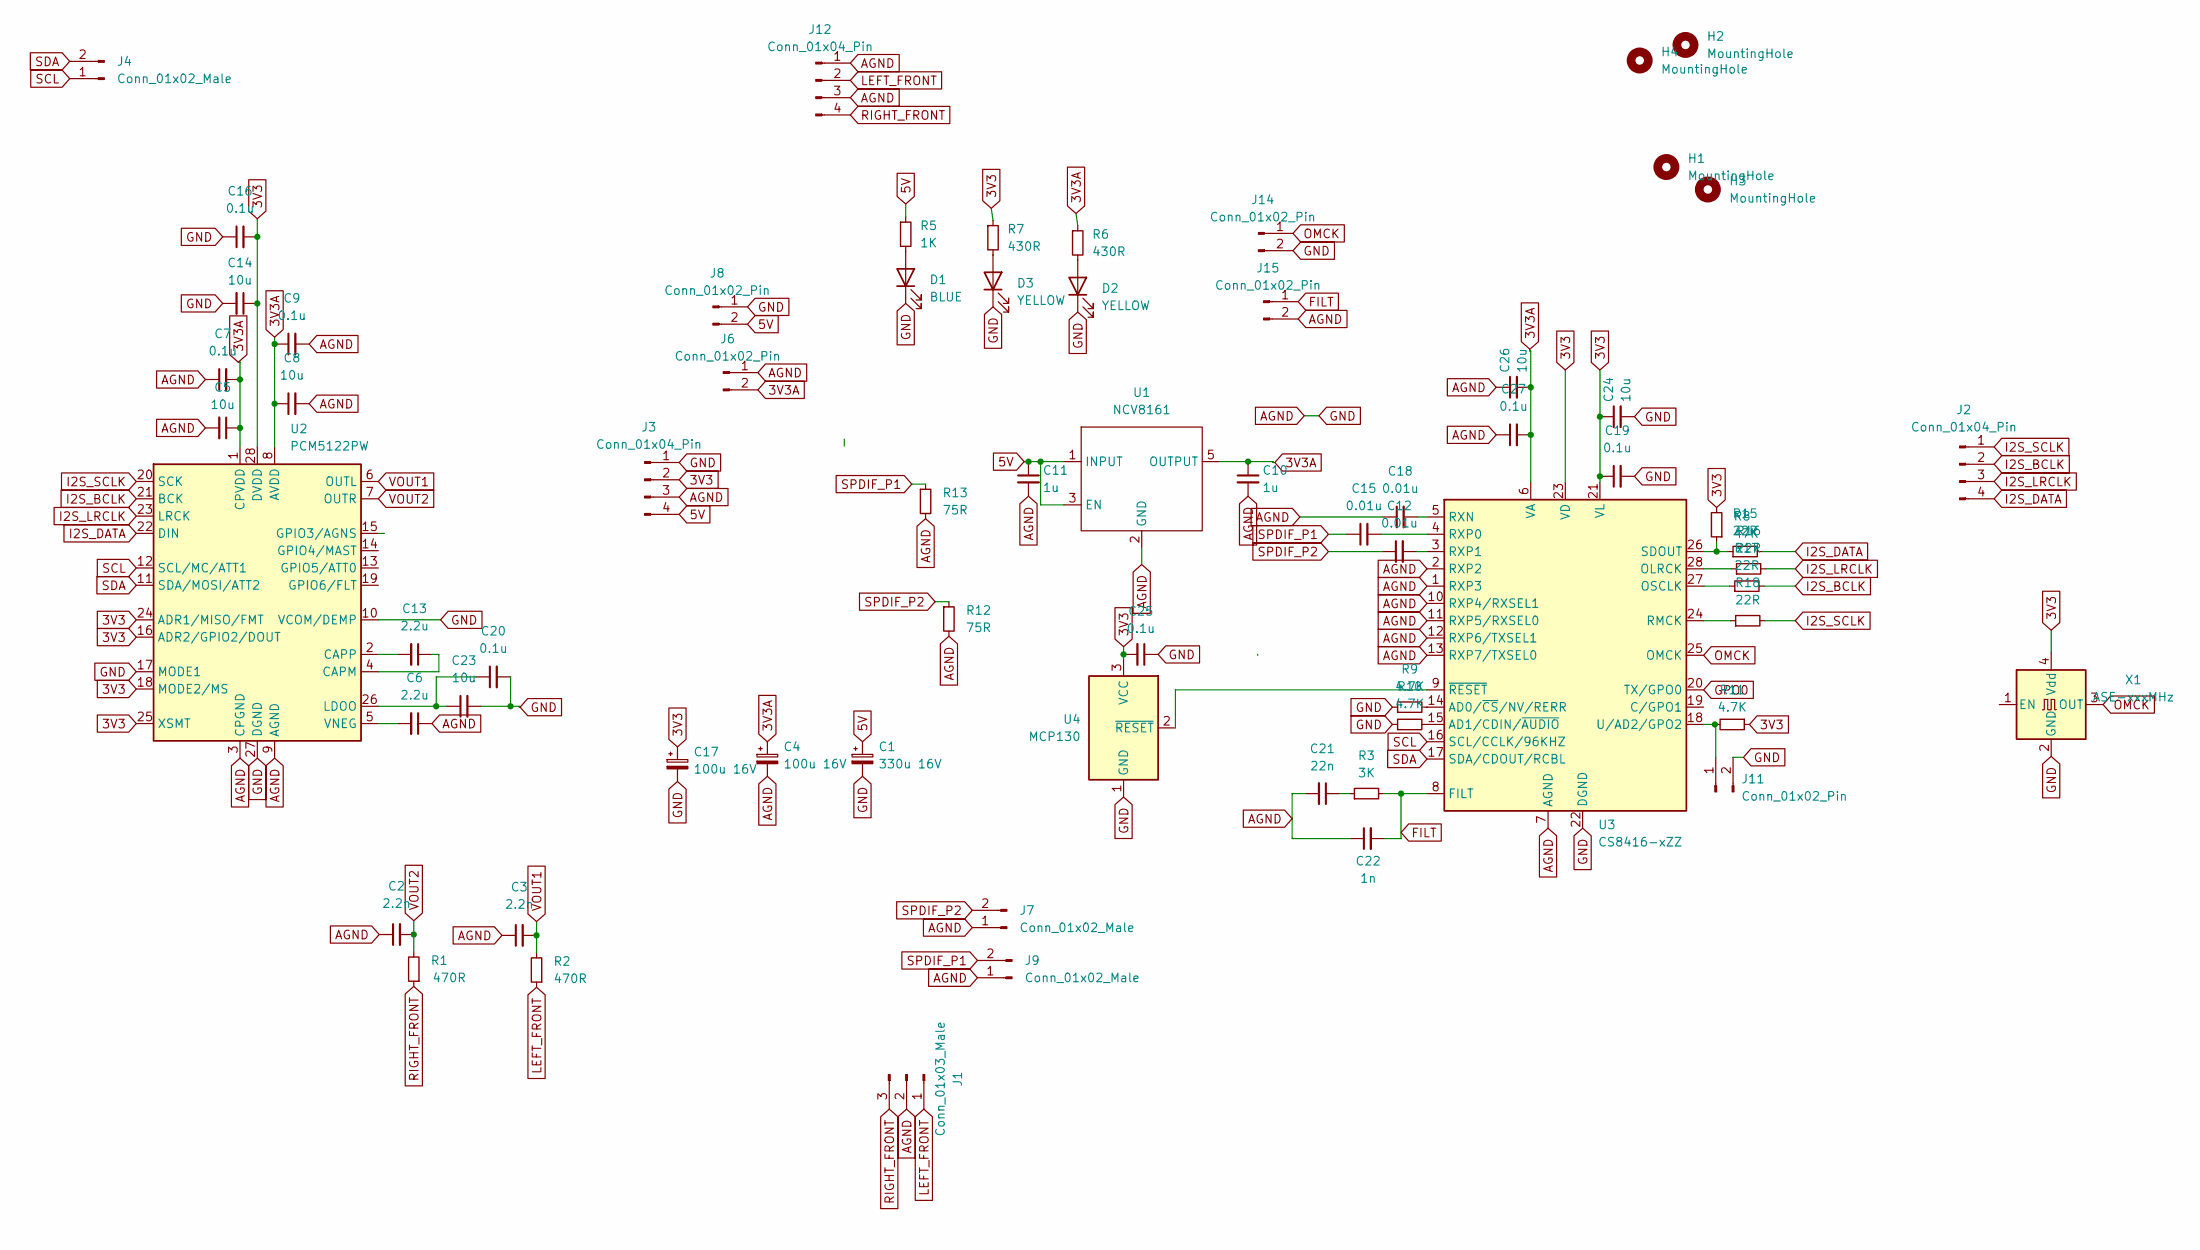
[picture p103: schematic DAC.kicad_sch]

Parts:
C1: 330u 16V; CP_Radial_D8.0mm_P2.50mm
C2, C3: 2.2n; C_1206_3216Metric_Pad1.33x1.80mm_HandSolder
C4, C17: 100u 16V; CP_Radial_D5.0mm_P2.50mm
C5, C8, C14, C23, C24, C26: 10u; C_1206_3216Metric_Pad1.33x1.80mm_HandSolder
C6, C13: 2.2u; C_1206_3216Metric_Pad1.33x1.80mm_HandSolder
C7, C9, C16, C19, C20, C25, C27: 0.1u; C_0805_2012Metric_Pad1.18x1.45mm_HandSolder
C10, C11: 1u; C_1206_3216Metric_Pad1.33x1.80mm_HandSolder
C12, C15, C18: 0.01u; C_0805_2012Metric_Pad1.18x1.45mm_HandSolder
C21: 22n; C_0805_2012Metric_Pad1.18x1.45mm_HandSolder
C22: 1n; C_0805_2012Metric_Pad1.18x1.45mm_HandSolder
D1: BLUE; LED_0805_2012Metric_Pad1.15x1.40mm_HandSolder
D2, D3: YELLOW; LED_0805_2012Metric_Pad1.15x1.40mm_HandSolder
H1, H2, H3, H4: MountingHole; MountingHole_3.2mm_M3
J1: Conn_01x03_Male; PinHeader_1x03_P2.54mm_Vertical
J2: Conn_01x04_Pin; PinHeader_1x04_P2.54mm_Vertical
J3: Conn_01x04_Pin; JST_XH_B4B-XH-A_1x04_P2.50mm_Vertical
J4: Conn_01x02_Male; JST_PH_B2B-PH-K_1x02_P2.00mm_Vertical
J6, J8, J11, J14, J15: Conn_01x02_Pin; PinHeader_1x02_P2.54mm_Vertical
J7, J9: Conn_01x02_Male; JST_XH_B2B-XH-A_1x02_P2.50mm_Vertical
J12: Conn_01x04_Pin; JST_PH_B4B-PH-K_1x04_P2.00mm_Vertical
R1, R2: 470R; R_1206_3216Metric_Pad1.30x1.75mm_HandSolder
R3: 3K; R_0603_1608Metric_Pad0.98x0.95mm_HandSolder
R5: 1K; R_0603_1608Metric_Pad0.98x0.95mm_HandSolder
R6, R7: 430R; R_0603_1608Metric_Pad0.98x0.95mm_HandSolder
R8: 47K; R_0603_1608Metric_Pad0.98x0.95mm_HandSolder
R9, R10, R11: 4.7K; R_0603_1608Metric_Pad0.98x0.95mm_HandSolder
R12, R13: 75R; R_0603_1608Metric_Pad0.98x0.95mm_HandSolder
R15, R16, R17, R18: 22R; R_0603_1608Metric_Pad0.98x0.95mm_HandSolder
U1: NCV8161; TSOT-23-5
U2: PCM5122PW; TSSOP-28_4.4x9.7mm_P0.65mm
U3: CS8416-xZZ; TSSOP-28_4.4x9.7mm_P0.65mm
U4: MCP130; SOT-23
X1: ASE-xxxMHz; Oscillator_SMD_Abracon_ASE-4Pin_3.2x2.5mm

Connections:
3V3: C14.1, C16.2, C17.1, C19.1, C24.1, C25.2, J3.2, R7.1, R8.2, R11.1, U2.16 (ADR2/GPIO2/DOUT), U2.18 (MODE2/MS), U2.24 (ADR1/MISO/FMT), U2.25 (XSMT), U2.28 (DVDD), U3.21 (VL), U3.23 (VD), U4.3 (VCC), X1.4 (Vdd)
3V3A: C4.1, C5.1, C7.2, C8.1, C9.1, C10.1, C26.2, C27.2, J6.2, R6.1, U1.5 (OUTPUT), U2.1 (CPVDD), U2.8 (AVDD), U3.6 (VA)
5V: C1.1, C11.1, J3.4, J8.2, R5.1, U1.1 (INPUT), U1.3 (EN)
AGND: C1.2, C2.1, C3.1, C4.2, C5.2, C6.1, C7.1, C8.2, C9.2, C10.2, C11.2, C14.2, C16.1, C17.2, C18.1, C19.2, C20.2, C21.2, C22.1, C23.2, C24.2, C25.1, C26.1, C27.1, D1.1 (K), D2.1 (K), D3.1 (K), J1.2, J3.1, J3.3, J6.1, J7.1, J8.1, J9.1, J11.2, J12.1, J12.3, J14.2, J15.2, R9.1, R10.1, R12.2, R13.2, U1.2 (GND), U2.3 (CPGND), U2.9 (AGND), U2.10 (VCOM/DEMP), U2.17 (MODE1), U2.27 (DGND), U3.1 (RXP3), U3.2 (RXP2), U3.7 (AGND), U3.10 (RXP4/RXSEL1), U3.11 (RXP5/RXSEL0), U3.12 (RXP6/TXSEL1), U3.13 (RXP7/TXSEL0), U3.22 (DGND), U4.1 (GND), X1.2 (GND)
FILT: C22.2, J15.1, R3.2, U3.8 (FILT)
GPO0: U3.20 (TX/GPO0)
I2S_BCLK: J2.2, R17.2, U2.21 (BCK)
I2S_DATA: J2.4, R15.2, U2.22 (DIN)
I2S_LRCLK: J2.3, R16.2, U2.23 (LRCK)
I2S_SCLK: J2.1, R18.2, U2.20 (SCK)
LEFT_FRONT: J1.1, J12.2, R2.1
unnamed: C6.2, U2.5 (VNEG)
unnamed: C12.2, U3.3 (RXP1)
unnamed: C13.1, U2.4 (CAPM)
unnamed: C13.2, U2.2 (CAPP)
unnamed: C15.2, U3.4 (RXP0)
unnamed: C18.2, U3.5 (RXN)
unnamed: C20.1, C23.1, U2.26 (LDOO)
unnamed: C21.1, R3.1
unnamed: D1.2 (A), R5.2
unnamed: D2.2 (A), R6.2
unnamed: D3.2 (A), R7.2
unnamed: J11.1, R11.2, U3.18 (U/AD2/GPO2)
unnamed: R9.2, U3.14 (AD0/~CS/NV/RERR)
unnamed: R10.2, U3.15 (AD1/CDIN/~AUDIO)
unnamed: R8.1, R15.1, U3.26 (SDOUT)
unnamed: R16.1, U3.28 (OLRCK)
unnamed: R17.1, U3.27 (OSCLK)
unnamed: R18.1, U3.24 (RMCK)
unnamed: U3.9 (~RESET), U4.2 (~RESET)
OMCK: J14.1, U3.25 (OMCK), X1.3 (OUT)
RIGHT_FRONT: J1.3, J12.4, R1.1
SCL: J4.1, U2.12 (SCL/MC/ATT1), U3.16 (SCL/CCLK/96KHZ)
SDA: J4.2, U2.11 (SDA/MOSI/ATT2), U3.17 (SDA/CDOUT/RCBL)
SPDIF_P1: C15.1, J9.2, R13.1
SPDIF_P2: C12.1, J7.2, R12.1
VOUT1: C3.2, R2.2, U2.6 (OUTL)
VOUT2: C2.2, R1.2, U2.7 (OUTR)
