duanestorey/Hifi-Amplifier/PCBs/DAC Filter/1.1/DAC Filter.kicad_sch

## KiCad design PCBs/DAC Filter/1.1/DAC Filter.kicad_sch (2023-10-17)

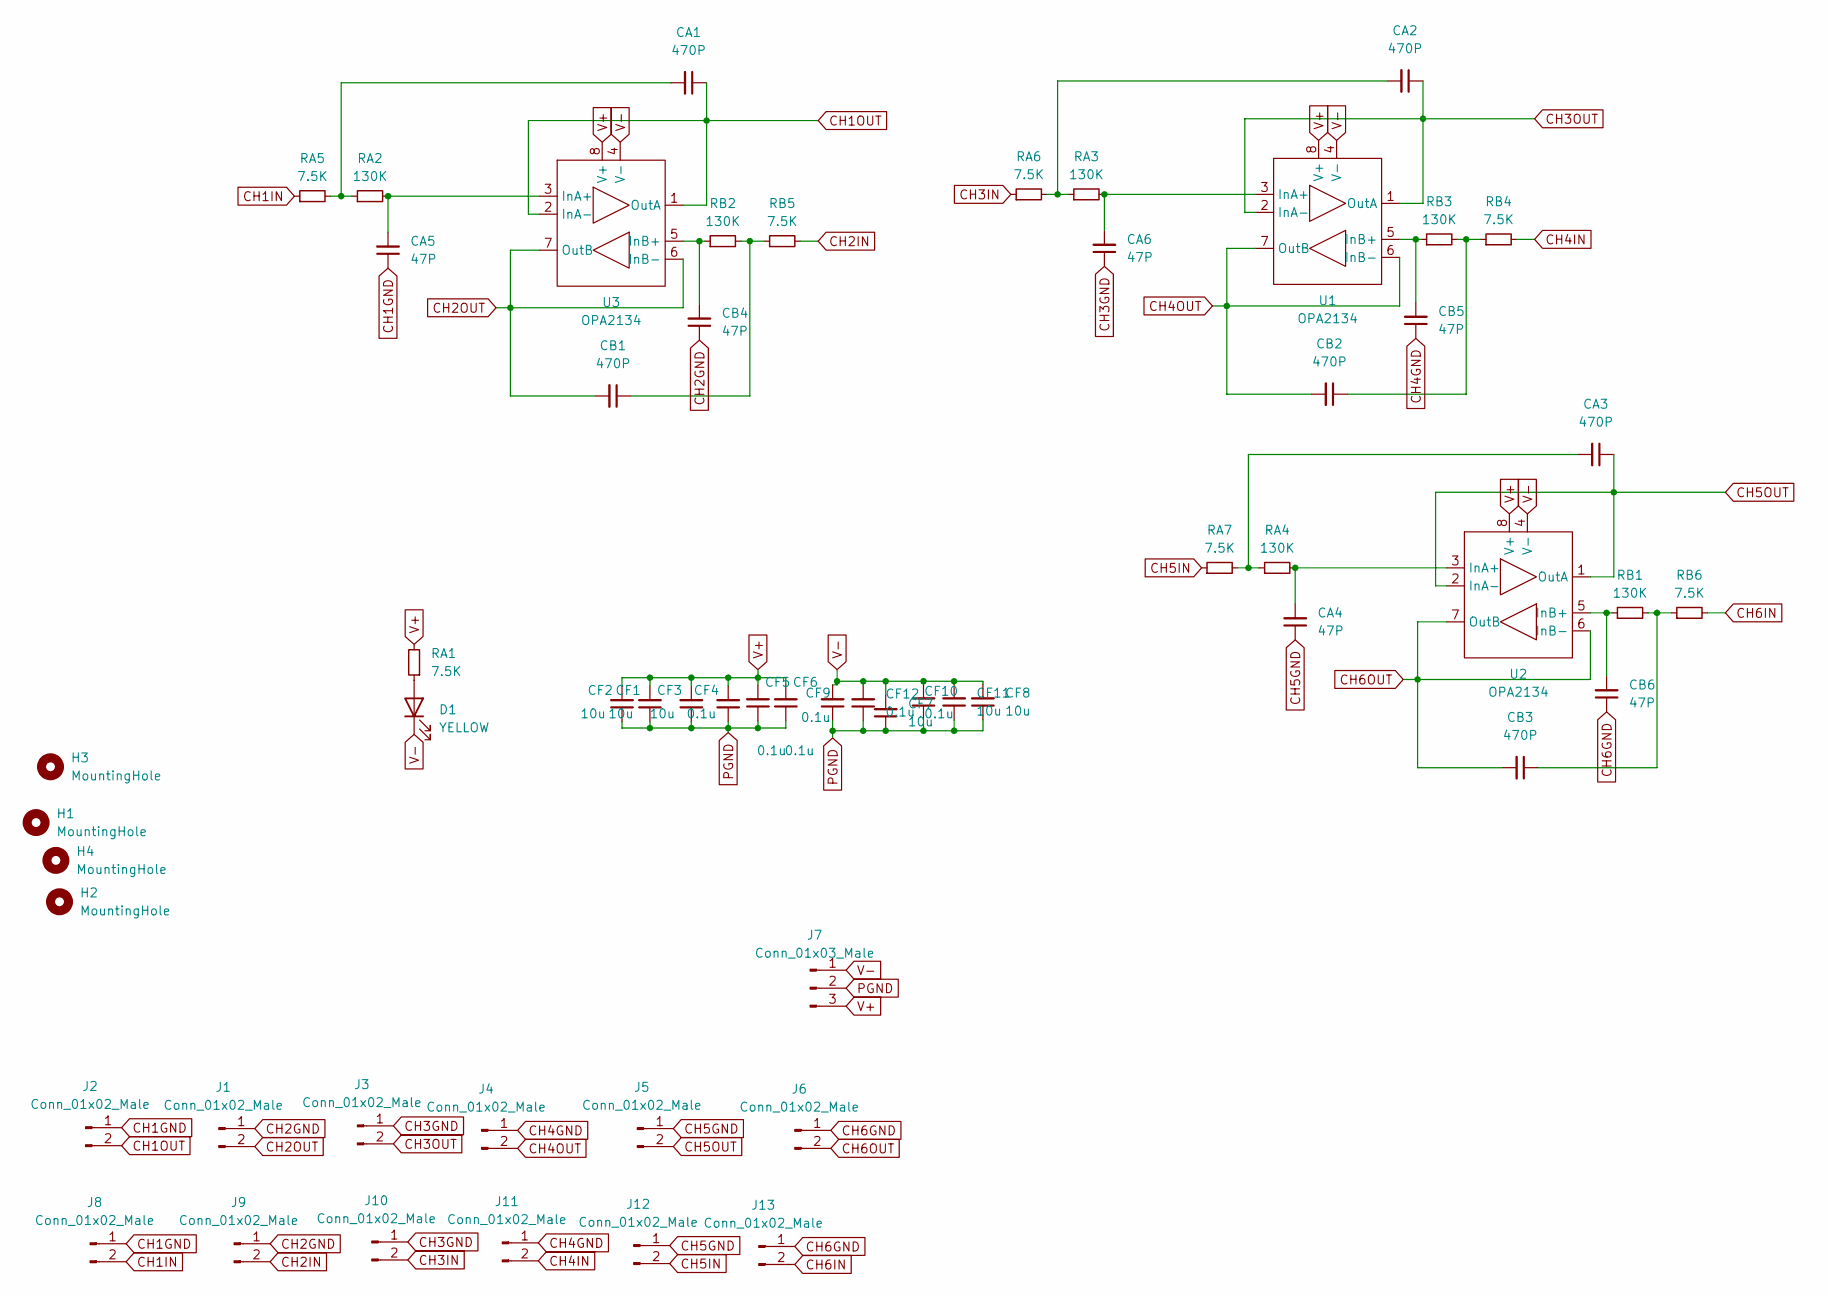
[picture p104: schematic DAC Filter.kicad_sch]

Parts:
CA1, CA2, CA3: 470P; C_1206_3216Metric_Pad1.33x1.80mm_HandSolder
CA4, CA5, CA6: 47P; C_1206_3216Metric_Pad1.33x1.80mm_HandSolder
CB1, CB2, CB3: 470P; C_1206_3216Metric_Pad1.33x1.80mm_HandSolder
CB4, CB5, CB6: 47P; C_1206_3216Metric_Pad1.33x1.80mm_HandSolder
CF1, CF2, CF3, CF7, CF8, CF11: 10u; C_1206_3216Metric_Pad1.33x1.80mm_HandSolder
CF4, CF5, CF6, CF9, CF10, CF12: 0.1u; C_0805_2012Metric_Pad1.18x1.45mm_HandSolder
D1: YELLOW; LED_0805_2012Metric_Pad1.15x1.40mm_HandSolder
H1, H2, H3, H4: MountingHole; MountingHole_3.2mm_M3
J1, J2, J3, J4, J5, J6, J8, J9, J10, J11, J12, J13: Conn_01x02_Male; JST_PH_B2B-PH-K_1x02_P2.00mm_Vertical
J7: Conn_01x03_Male; JST_PH_B3B-PH-K_1x03_P2.00mm_Vertical
RA1: 7.5K; R_0603_1608Metric
RA2, RA3, RA4: 130K; R_1206_3216Metric_Pad1.30x1.75mm_HandSolder
RA5, RA6, RA7: 7.5K; R_1206_3216Metric_Pad1.30x1.75mm_HandSolder
RB1, RB2, RB3: 130K; R_1206_3216Metric_Pad1.30x1.75mm_HandSolder
RB4, RB5, RB6: 7.5K; R_1206_3216Metric_Pad1.30x1.75mm_HandSolder
U1, U2, U3: OPA2134; DIP-8_W7.62mm_Socket

Connections:
CH1GND: CA5.1, J2.1, J8.1
CH1IN: J8.2, RA5.1
CH1OUT: CA1.1, J2.2, U3.1 (OutA), U3.2 (InA-)
CH2GND: CB4.1, J1.1, J9.1
CH2IN: J9.2, RB5.2
CH2OUT: CB1.2, J1.2, U3.6 (InB-), U3.7 (OutB)
CH3GND: CA6.1, J3.1, J10.1
CH3IN: J10.2, RA6.1
CH3OUT: CA2.1, J3.2, U1.1 (OutA), U1.2 (InA-)
CH4GND: CB5.1, J4.1, J11.1
CH4IN: J11.2, RB4.2
CH4OUT: CB2.2, J4.2, U1.6 (InB-), U1.7 (OutB)
CH5GND: CA4.1, J5.1, J12.1
CH5IN: J12.2, RA7.1
CH5OUT: CA3.1, J5.2, U2.1 (OutA), U2.2 (InA-)
CH6GND: CB6.1, J6.1, J13.1
CH6IN: J13.2, RB6.2
CH6OUT: CB3.2, J6.2, U2.6 (InB-), U2.7 (OutB)
unnamed: CA1.2, RA2.1, RA5.2
unnamed: CA2.2, RA3.1, RA6.2
unnamed: CA3.2, RA4.1, RA7.2
unnamed: CA4.2, RA4.2, U2.3 (InA+)
unnamed: CA5.2, RA2.2, U3.3 (InA+)
unnamed: CA6.2, RA3.2, U1.3 (InA+)
unnamed: CB1.1, RB2.2, RB5.1
unnamed: CB2.1, RB3.2, RB4.1
unnamed: CB3.1, RB1.2, RB6.1
unnamed: CB4.2, RB2.1, U3.5 (InB+)
unnamed: CB5.2, RB3.1, U1.5 (InB+)
unnamed: CB6.2, RB1.1, U2.5 (InB+)
unnamed: D1.2 (A), RA1.1
PGND: CF1.1, CF2.1, CF3.1, CF4.1, CF5.1, CF6.1, CF7.1, CF8.1, CF9.1, CF10.1, CF11.1, CF12.1, J7.2
V+: CF1.2, CF2.2, CF3.2, CF4.2, CF5.2, CF6.2, J7.3, RA1.2, U1.8 (V+), U2.8 (V+), U3.8 (V+)
V-: CF7.2, CF8.2, CF9.2, CF10.2, CF11.2, CF12.2, D1.1 (K), J7.1, U1.4 (V-), U2.4 (V-), U3.4 (V-)
