duanestorey/Hifi-Amplifier/PCBs/DolbyDecoder/3.0/DolbyDecoder.kicad_sch

## KiCad design PCBs/DolbyDecoder/3.0/DolbyDecoder.kicad_sch (2024-11-29)

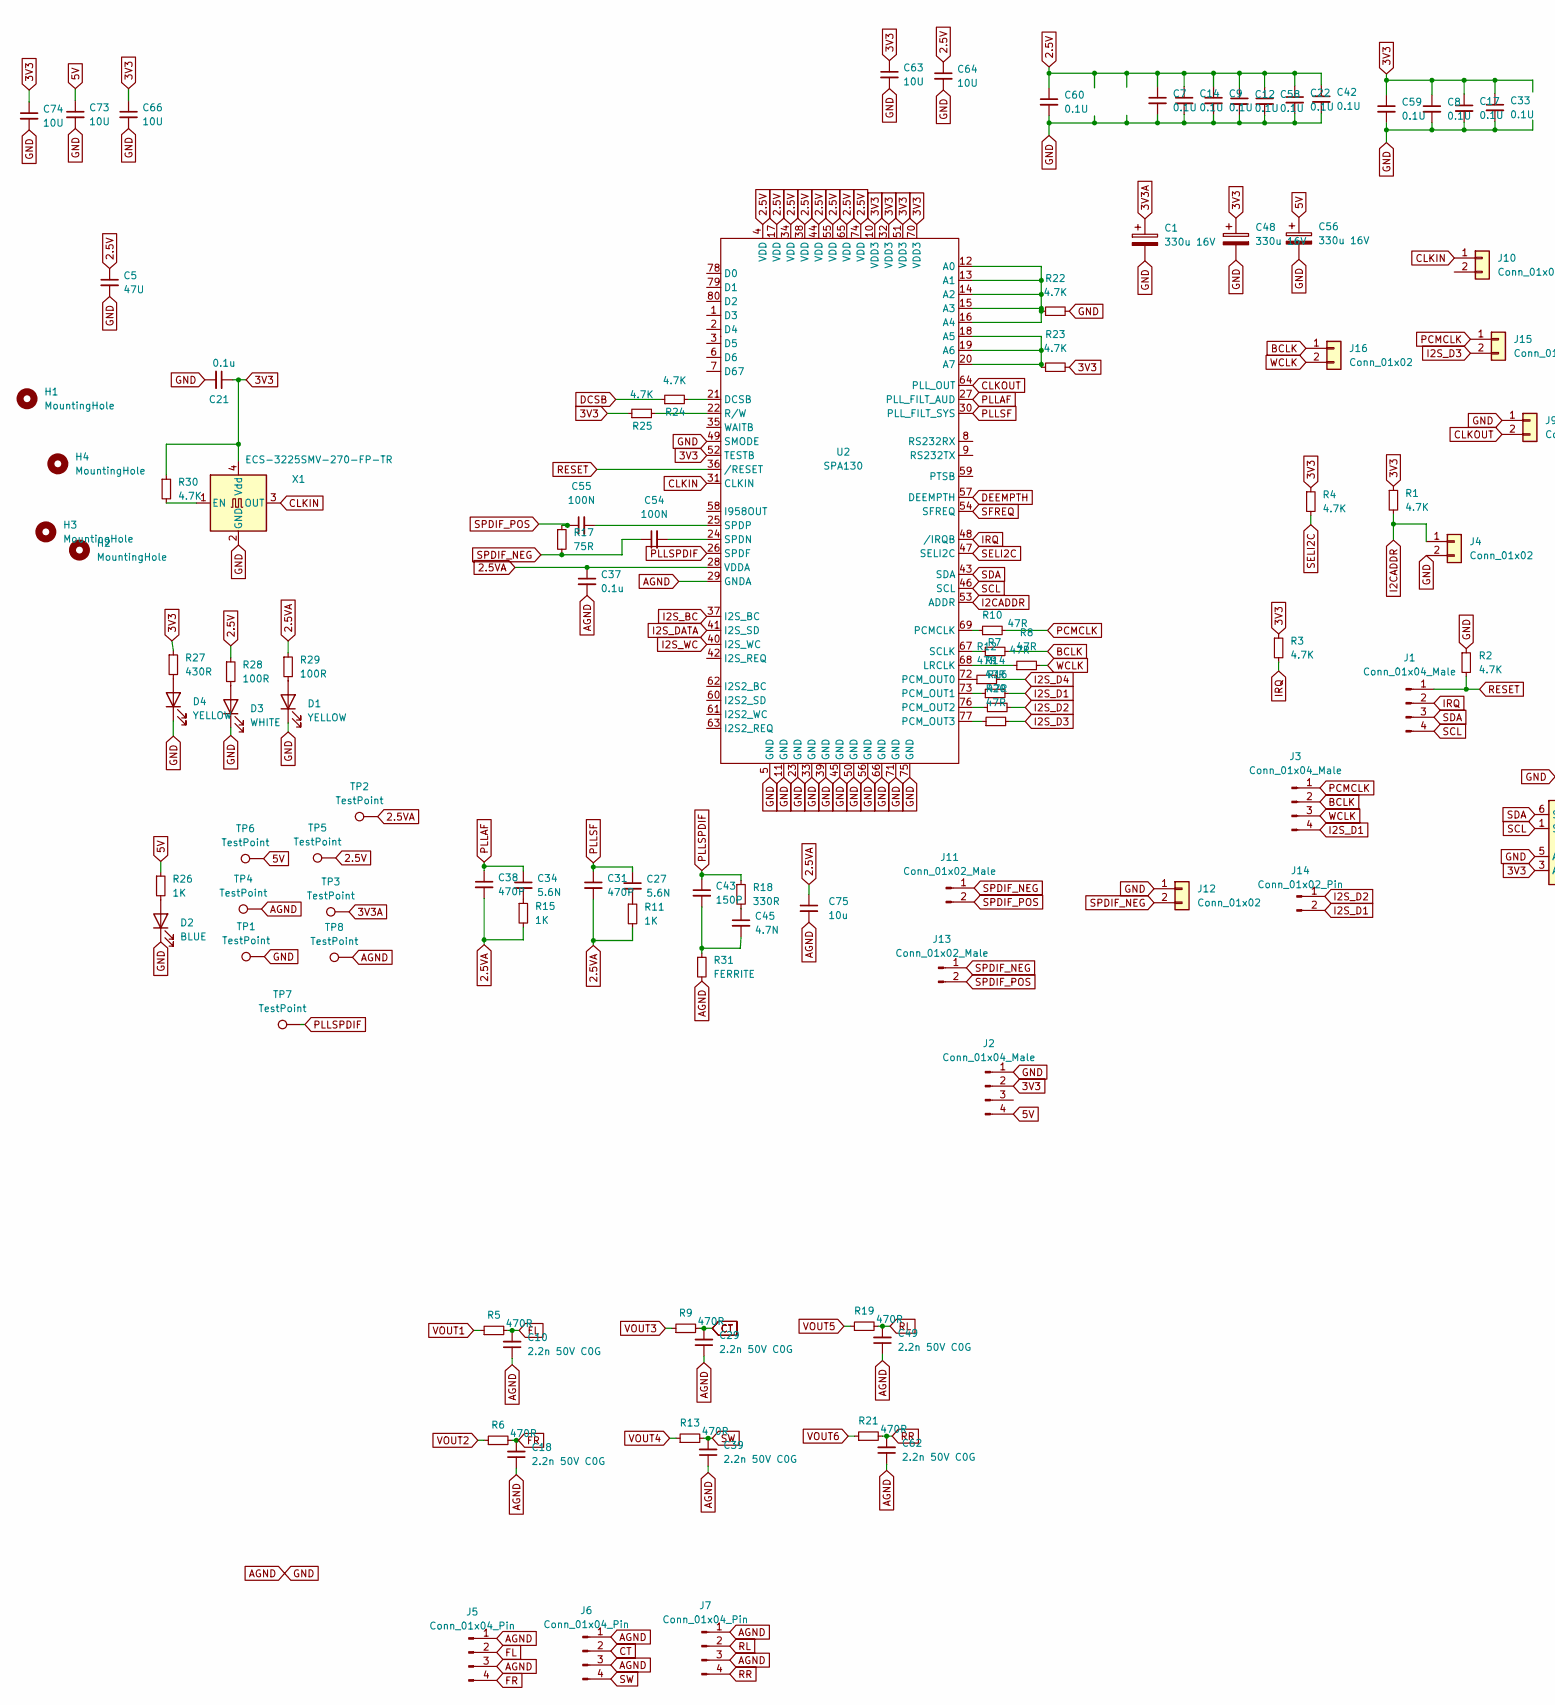
[picture p105: schematic DolbyDecoder.kicad_sch, part in row 1, column 1]

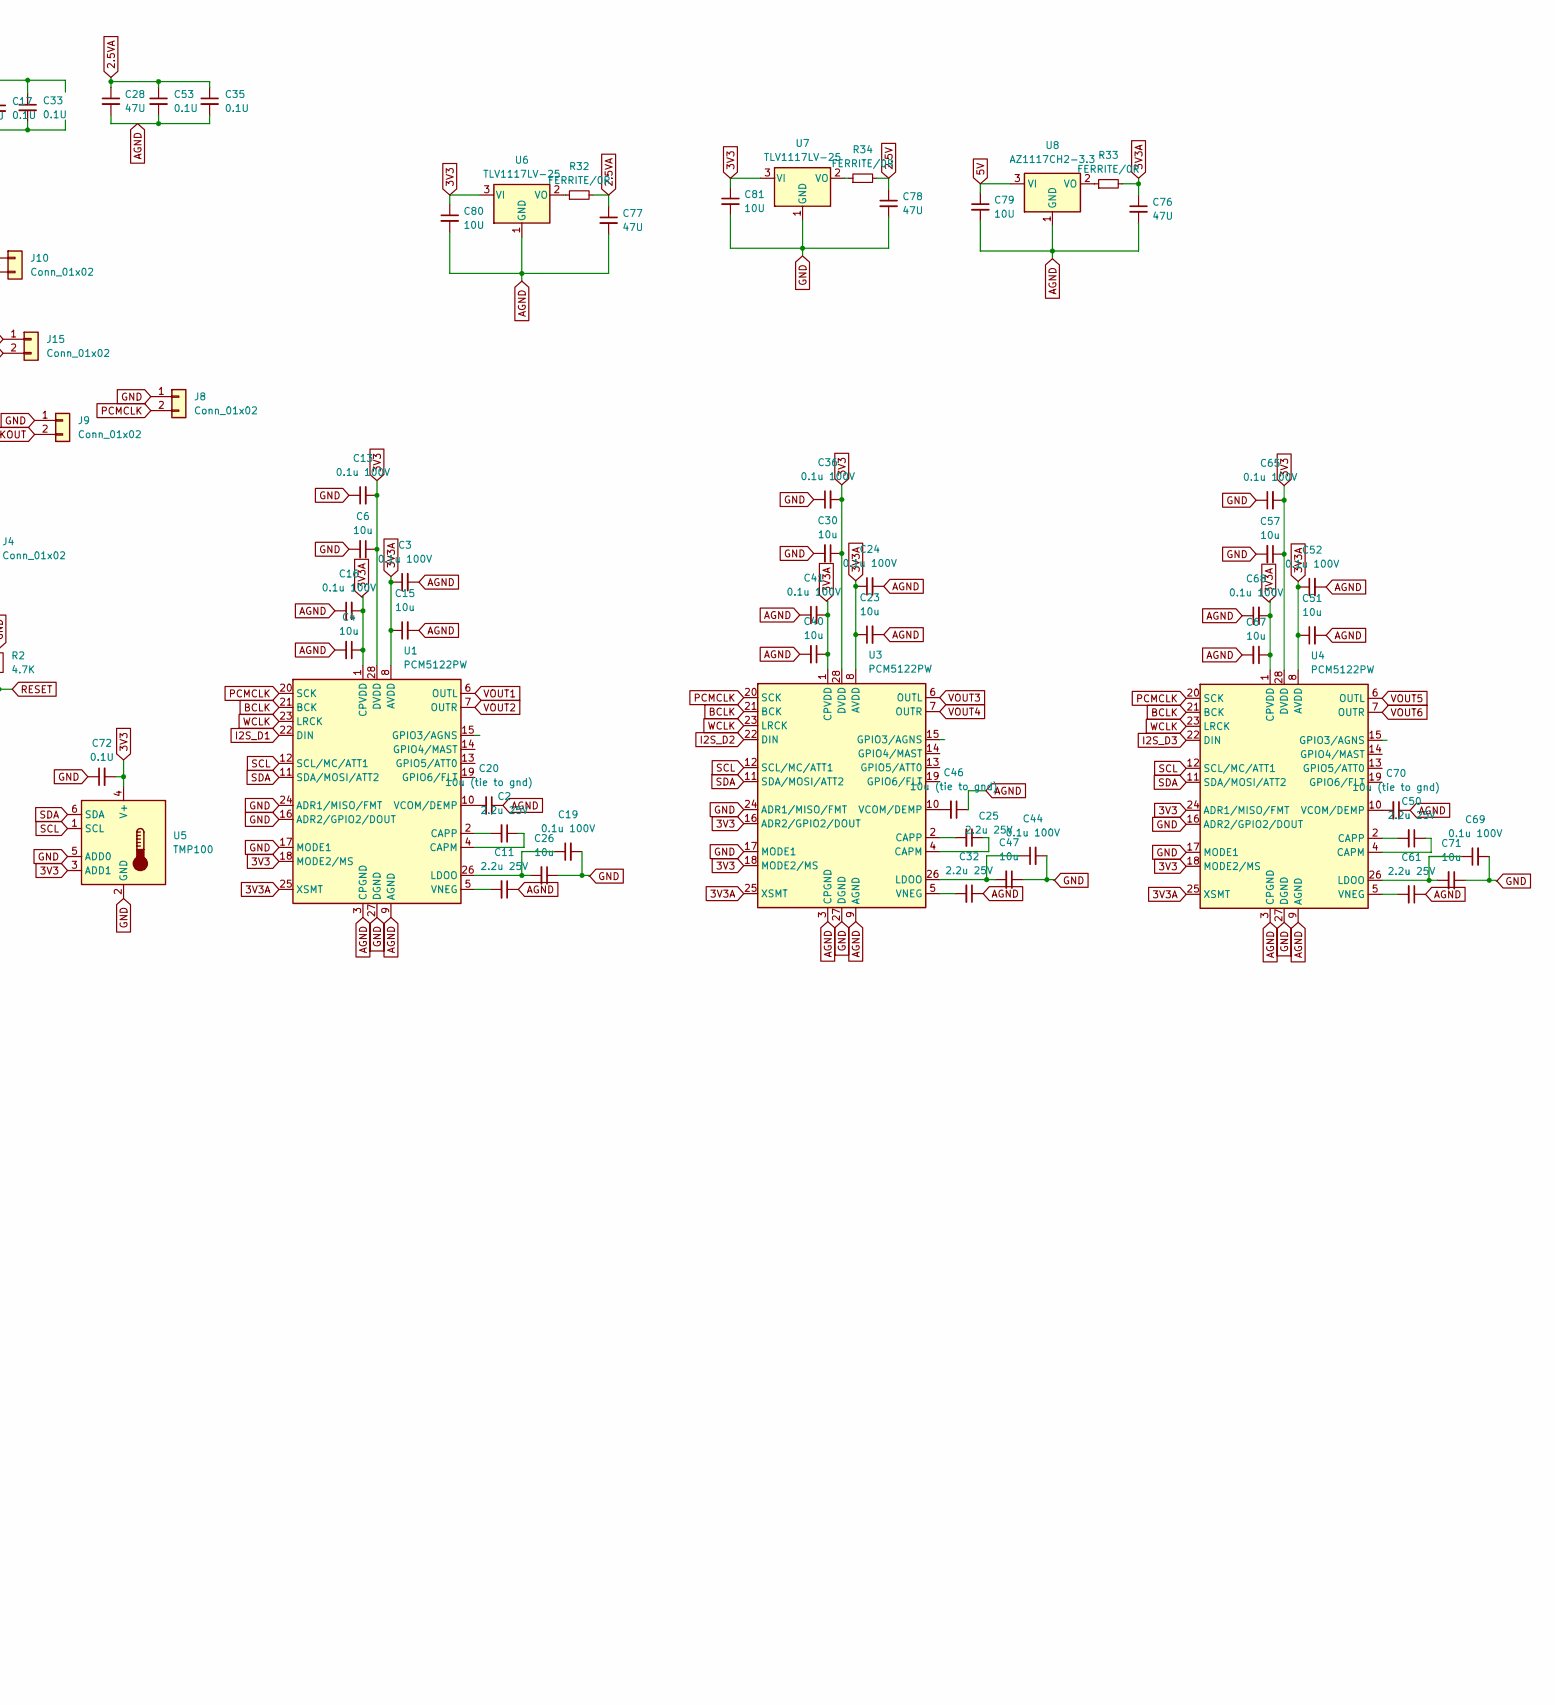
[picture p106: schematic DolbyDecoder.kicad_sch, part in row 1, column 2]

Parts:
C1, C48, C56: 330u 16V; CP_Radial_D8.0mm_P2.50mm
C2, C11, C25, C32, C50, C61: 2.2u 25V; C_1206_3216Metric_Pad1.33x1.80mm_HandSolder
C3, C13, C16, C19, C24, C36, C41, C44, C52, C65, C68, C69: 0.1u 100V; C_0805_2012Metric_Pad1.18x1.45mm_HandSolder
C4, C6, C15, C23, C26, C30, C40, C47, C51, C57, C67, C71, C75: 10u; C_1206_3216Metric_Pad1.33x1.80mm_HandSolder
C5, C28, C76, C77, C78: 47U; C_1206_3216Metric_Pad1.33x1.80mm_HandSolder
C7, C8, C9, C12, C14, C17, C22, C33, C35, C42, C53, C58, C59, C60, C72: 0.1U; C_0805_2012Metric_Pad1.18x1.45mm_HandSolder
C10, C18, C29, C39, C49, C62: 2.2n 50V C0G; C_1206_3216Metric_Pad1.33x1.80mm_HandSolder
C20, C46, C70: 10u (tie to gnd); C_1206_3216Metric_Pad1.33x1.80mm_HandSolder
C21, C37: 0.1u; C_0805_2012Metric_Pad1.18x1.45mm_HandSolder
C27, C34: 5.6N; C_0805_2012Metric_Pad1.18x1.45mm_HandSolder
C31, C38: 470P; C_0805_2012Metric_Pad1.18x1.45mm_HandSolder
C43: 150P; C_0805_2012Metric_Pad1.18x1.45mm_HandSolder
C45: 4.7N; C_0805_2012Metric_Pad1.18x1.45mm_HandSolder
C54, C55: 100N; C_0805_2012Metric_Pad1.18x1.45mm_HandSolder
C63, C64, C66, C73, C74, C79, C80, C81: 10U; C_1206_3216Metric_Pad1.33x1.80mm_HandSolder
D1, D4: YELLOW; LED_0805_2012Metric_Pad1.15x1.40mm_HandSolder
D2: BLUE; LED_0805_2012Metric_Pad1.15x1.40mm_HandSolder
D3: WHITE; LED_0805_2012Metric_Pad1.15x1.40mm_HandSolder
H1, H2, H3, H4: MountingHole; MountingHole_3.2mm_M3
J1: Conn_01x04_Male; JST_PH_B4B-PH-K_1x04_P2.00mm_Vertical
J2: Conn_01x04_Male; JST_XH_B4B-XH-A_1x04_P2.50mm_Vertical
J3: Conn_01x04_Male; PinHeader_1x04_P2.54mm_Vertical
J4, J8, J9, J10, J12, J15, J16: Conn_01x02; PinHeader_1x02_P2.54mm_Vertical
J5, J6, J7: Conn_01x04_Pin; JST_PH_B4B-PH-K_1x04_P2.00mm_Vertical
J11: Conn_01x02_Male; JST_XH_B2B-XH-A_1x02_P2.50mm_Vertical
J13: Conn_01x02_Male; PinHeader_1x02_P2.54mm_Vertical
J14: Conn_01x02_Pin; PinHeader_1x02_P2.54mm_Vertical
R1, R2, R3, R4, R22, R23, R24, R25, R30: 4.7K; R_0603_1608Metric_Pad0.98x0.95mm_HandSolder
R5, R6, R9, R13, R19, R21: 470R; R_1206_3216Metric_Pad1.30x1.75mm_HandSolder
R7, R8, R10, R12, R14, R16, R20: 47R; R_0805_2012Metric_Pad1.20x1.40mm_HandSolder
R11, R15, R26: 1K; R_0603_1608Metric_Pad0.98x0.95mm_HandSolder
R17: 75R; R_0603_1608Metric_Pad0.98x0.95mm_HandSolder
R18: 330R; R_0603_1608Metric_Pad0.98x0.95mm_HandSolder
R27: 430R; R_0603_1608Metric_Pad0.98x0.95mm_HandSolder
R28, R29: 100R; R_0603_1608Metric_Pad0.98x0.95mm_HandSolder
R31: FERRITE; R_0603_1608Metric_Pad0.98x0.95mm_HandSolder
R32, R33, R34: FERRITE/0R; R_0603_1608Metric_Pad0.98x0.95mm_HandSolder
TP1, TP2, TP3, TP4, TP5, TP6, TP7, TP8: TestPoint; TestPoint_THTPad_1.5x1.5mm_Drill0.7mm
U1, U3, U4: PCM5122PW; TSSOP-28_4.4x9.7mm_P0.65mm
U2: SPA130; LQFP-80_14x14mm_P0.65mm
U5: TMP100; SOT-23-6
U6, U7: TLV1117LV-25; SOT-223-3_TabPin2
U8: AZ1117CH2-3.3; SOT-223-3_TabPin2
X1: ECS-3225SMV-270-FP-TR; Oscillator_SMD_EuroQuartz_XO32-4Pin_3.2x2.5mm_HandSoldering

Connections:
2.5V: C5.1, C7.1, C9.1, C12.1, C14.1, C22.1, C42.1, C58.1, C60.1, C64.1, C78.1, R28.1, R34.2, TP5.1, U2.4 (VDD), U2.17 (VDD), U2.34 (VDD), U2.38 (VDD), U2.44 (VDD), U2.55 (VDD), U2.65 (VDD), U2.74 (VDD)
2.5VA: C28.1, C31.2, C35.1, C37.1, C38.2, C53.1, C75.1, C77.1, R11.2, R15.2, R29.1, R32.2, TP2.1, U2.28 (VDDA)
3V3: C6.1, C8.1, C13.2, C17.1, C21.1, C30.1, C33.1, C36.2, C48.1, C57.1, C59.1, C63.1, C65.2, C66.1, C72.2, C74.1, C80.1, C81.1, J2.2, R1.1, R3.1, R4.1, R23.2, R25.1, R27.1, R30.1, U1.18 (MODE2/MS), U1.28 (DVDD), U2.10 (VDD3), U2.32 (VDD3), U2.51 (VDD3), U2.52 (TESTB), U2.70 (VDD3), U3.16 (ADR2/GPIO2/DOUT), U3.18 (MODE2/MS), U3.28 (DVDD), U4.18 (MODE2/MS), U4.24 (ADR1/MISO/FMT), U4.28 (DVDD), U5.3 (ADD1), U5.4 (V+), U6.3 (VI), U7.3 (VI), X1.4 (Vdd)
3V3A: C1.1, C3.1, C4.1, C15.1, C16.2, C23.1, C24.1, C40.1, C41.2, C51.1, C52.1, C67.1, C68.2, C76.1, R33.2, TP3.1, U1.1 (CPVDD), U1.8 (AVDD), U1.25 (XSMT), U3.1 (CPVDD), U3.8 (AVDD), U3.25 (XSMT), U4.1 (CPVDD), U4.8 (AVDD), U4.25 (XSMT)
5V: C56.1, C73.1, C79.1, J2.4, R26.1, TP6.1, U8.3 (VI)
AGND: C1.2, C3.2, C4.2, C5.2, C6.2, C7.2, C8.2, C9.2, C10.1, C11.1, C12.2, C13.1, C14.2, C15.2, C16.1, C17.2, C18.1, C19.2, C20.1, C21.2, C22.2, C23.2, C24.2, C26.1, C28.2, C29.1, C30.2, C32.1, C33.2, C35.2, C36.1, C37.2, C39.1, C40.2, C41.1, C42.2, C44.2, C46.1, C47.1, C48.2, C49.1, C51.2, C52.2, C53.2, C56.2, C57.2, C58.2, C59.2, C60.2, C61.1, C62.1, C63.2, C64.2, C65.1, C66.2, C67.2, C68.1, C69.2, C70.1, C71.1, C72.1, C73.2, C74.2, C75.2, C76.2, C77.2, C78.2, C79.2, C80.2, C81.2, D1.1 (K), D2.1 (K), D3.1 (K), D4.1 (K), J2.1, J4.2, J5.1, J5.3, J6.1, J6.3, J7.1, J7.3, J8.1, J9.1, J12.1, R2.1, R22.2, R31.2, TP1.1, TP4.1, TP8.1, U1.3 (CPGND), U1.9 (AGND), U1.16 (ADR2/GPIO2/DOUT), U1.17 (MODE1), U1.24 (ADR1/MISO/FMT), U1.27 (DGND), U2.5 (GND), U2.11 (GND), U2.23 (GND), U2.29 (GNDA), U2.33 (GND), U2.39 (GND), U2.45 (GND), U2.49 (SMODE), U2.50 (GND), U2.56 (GND), U2.66 (GND), U2.71 (GND), U2.75 (GND), U3.3 (CPGND), U3.9 (AGND), U3.17 (MODE1), U3.24 (ADR1/MISO/FMT), U3.27 (DGND), U4.3 (CPGND), U4.9 (AGND), U4.16 (ADR2/GPIO2/DOUT), U4.17 (MODE1), U4.27 (DGND), U5.2 (GND), U5.5 (ADD0), U6.1 (GND), U7.1 (GND), U8.1 (GND), X1.2 (GND)
BCLK: J3.2, J16.1, R7.2, U1.21 (BCK), U3.21 (BCK), U4.21 (BCK)
CLKIN: J10.1, U2.31 (CLKIN), X1.3 (OUT)
CLKOUT: J9.2, U2.64 (PLL_OUT)
CT: C29.2, J6.2, R9.2
DCSB: R24.1
DEEMPTH: U2.57 (DEEMPTH)
FL: C10.2, J5.2, R5.2
FR: C18.2, J5.4, R6.2
I2CADDR: J4.1, R1.2, U2.53 (ADDR)
I2S_BC: U2.37 (I2S_BC)
I2S_D1: J3.4, J14.2, R14.2, U1.22 (DIN)
I2S_D2: J14.1, R16.2, U3.22 (DIN)
I2S_D3: J15.2, R20.2, U4.22 (DIN)
I2S_D4: R12.2
I2S_DATA: U2.41 (I2S_SD)
I2S_WC: U2.40 (I2S_WC)
IRQ: J1.2, R3.2, U2.48 (/IRQB)
unnamed: C2.1, U1.4 (CAPM)
unnamed: C2.2, U1.2 (CAPP)
unnamed: C11.2, U1.5 (VNEG)
unnamed: C19.1, C26.2, U1.26 (LDOO)
unnamed: C20.2, U1.10 (VCOM/DEMP)
unnamed: C25.1, U3.4 (CAPM)
unnamed: C25.2, U3.2 (CAPP)
unnamed: C27.2, R11.1
unnamed: C32.2, U3.5 (VNEG)
unnamed: C34.2, R15.1
unnamed: C43.2, C45.2, R31.1
unnamed: C44.1, C47.2, U3.26 (LDOO)
unnamed: C45.1, R18.2
unnamed: C46.2, U3.10 (VCOM/DEMP)
unnamed: C50.1, U4.4 (CAPM)
unnamed: C50.2, U4.2 (CAPP)
unnamed: C54.2, U2.24 (SPDN)
unnamed: C55.2, U2.25 (SPDP)
unnamed: C61.2, U4.5 (VNEG)
unnamed: C69.1, C71.2, U4.26 (LDOO)
unnamed: C70.2, U4.10 (VCOM/DEMP)
unnamed: D1.2 (A), R29.2
unnamed: D2.2 (A), R26.2
unnamed: D3.2 (A), R28.2
unnamed: D4.2 (A), R27.2
unnamed: R7.1, U2.67 (SCLK)
unnamed: R8.1, U2.68 (LRCLK)
unnamed: R10.1, U2.69 (PCMCLK)
unnamed: R12.1, U2.72 (PCM_OUT0)
unnamed: R14.1, U2.73 (PCM_OUT1)
unnamed: R16.1, U2.76 (PCM_OUT2)
unnamed: R20.1, U2.77 (PCM_OUT3)
unnamed: R22.1, U2.12 (A0), U2.13 (A1), U2.14 (A2), U2.15 (A3), U2.16 (A4)
unnamed: R23.1, U2.18 (A5), U2.19 (A6), U2.20 (A7)
unnamed: R24.2, U2.21 (DCSB)
unnamed: R25.2, U2.22 (R/W)
unnamed: R30.2, X1.1 (EN)
unnamed: R32.1, U6.2 (VO)
unnamed: R33.1, U8.2 (VO)
unnamed: R34.1, U7.2 (VO)
PCMCLK: J3.1, J8.2, J15.1, R10.2, U1.20 (SCK), U3.20 (SCK), U4.20 (SCK)
PLLAF: C34.1, C38.1, U2.27 (PLL_FILT_AUD)
PLLSF: C27.1, C31.1, U2.30 (PLL_FILT_SYS)
PLLSPDIF: C43.1, R18.1, TP7.1, U2.26 (SPDF)
RESET: J1.1, R2.2, U2.36 (/RESET)
RL: C49.2, J7.2, R19.2
RR: C62.2, J7.4, R21.2
SCL: J1.4, U1.12 (SCL/MC/ATT1), U2.46 (SCL), U3.12 (SCL/MC/ATT1), U4.12 (SCL/MC/ATT1), U5.1 (SCL)
SDA: J1.3, U1.11 (SDA/MOSI/ATT2), U2.43 (SDA), U3.11 (SDA/MOSI/ATT2), U4.11 (SDA/MOSI/ATT2), U5.6 (SDA)
SELI2C: R4.2, U2.47 (SELI2C)
SFREQ: U2.54 (SFREQ)
SPDIF_NEG: C54.1, J11.1, J12.2, J13.1, R17.2
SPDIF_POS: C55.1, J11.2, J13.2, R17.1
SW: C39.2, J6.4, R13.2
VOUT1: R5.1, U1.6 (OUTL)
VOUT2: R6.1, U1.7 (OUTR)
VOUT3: R9.1, U3.6 (OUTL)
VOUT4: R13.1, U3.7 (OUTR)
VOUT5: R19.1, U4.6 (OUTL)
VOUT6: R21.1, U4.7 (OUTR)
WCLK: J3.3, J16.2, R8.2, U1.23 (LRCK), U3.23 (LRCK), U4.23 (LRCK)
