duanestorey/Hifi-Amplifier/PCBs/SOIC DIP/1.0/SOIC DIP.kicad_sch

## KiCad design PCBs/SOIC DIP/1.0/SOIC DIP.kicad_sch (2023-10-17)

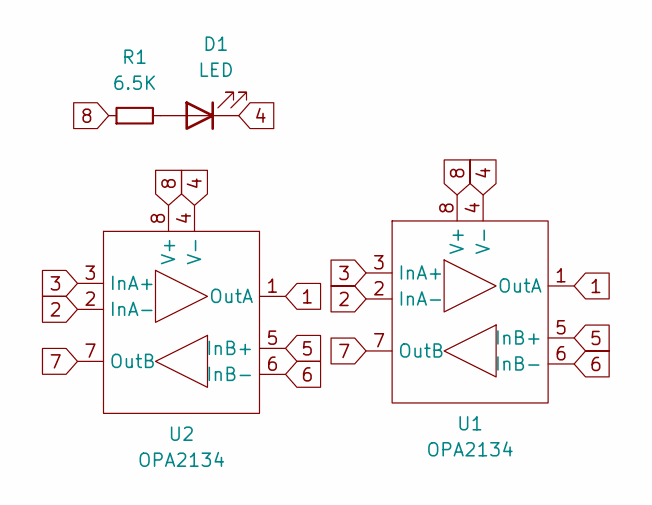
[picture p107: schematic SOIC DIP.kicad_sch]

Parts:
D1: LED; LED_0805_2012Metric_Pad1.15x1.40mm_HandSolder
R1: 6.5K; R_0805_2012Metric_Pad1.20x1.40mm_HandSolder
U1: OPA2134; DIP-8_W7.62mm_Socket
U2: OPA2134; SOIC-8_3.9x4.9mm_P1.27mm

Connections:
1: U1.1 (OutA), U2.1 (OutA)
2: U1.2 (InA-), U2.2 (InA-)
3: U1.3 (InA+), U2.3 (InA+)
4: D1.1 (K), U1.4 (V-), U2.4 (V-)
5: U1.5 (InB+), U2.5 (InB+)
6: U1.6 (InB-), U2.6 (InB-)
7: U1.7 (OutB), U2.7 (OutB)
8: R1.1, U1.8 (V+), U2.8 (V+)
unnamed: D1.2 (A), R1.2
