duanestorey/Hifi-Amplifier/PCBs/1/BindingPosts/1.0/BindingPosts.kicad_sch

## KiCad design PCBs/1/BindingPosts/1.0/BindingPosts.kicad_sch (2023-10-17)

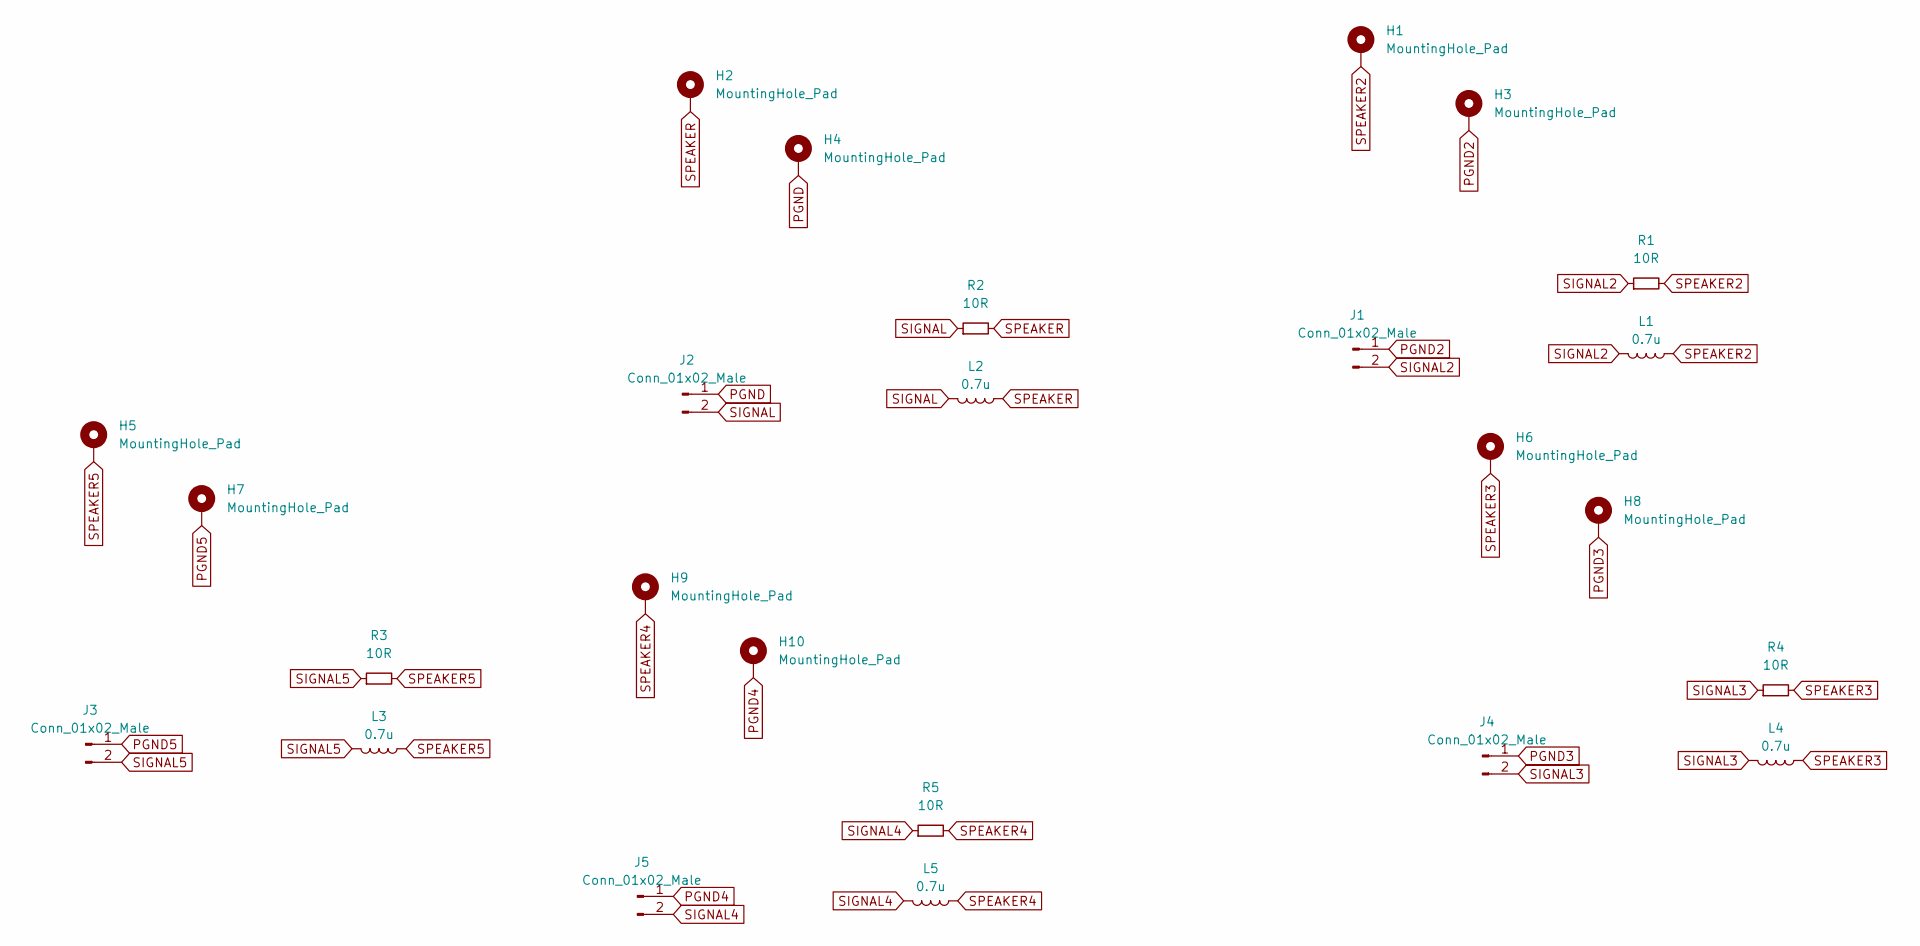
[picture p108: schematic BindingPosts.kicad_sch]

Parts:
H1, H2, H3, H4, H5, H6, H7, H8, H9, H10: MountingHole_Pad; MountingHole_4.3mm_M4_DIN965_Pad
J1, J2, J3, J4, J5: Conn_01x02_Male; JST_VH_B2P-VH-B_1x02_P3.96mm_Vertical
L1, L2, L3, L4, L5: 0.7u; L_Axial_L26.0mm_D10.0mm_P30.48mm_Horizontal_Fastron_77A
R1, R2, R3, R4, R5: 10R; R_Axial_Power_L25.0mm_W6.4mm_P27.94mm

Connections:
PGND: H4.1, J2.1
PGND2: H3.1, J1.1
PGND3: H8.1, J4.1
PGND4: H10.1, J5.1
PGND5: H7.1, J3.1
SIGNAL: J2.2, L2.2, R2.1
SIGNAL2: J1.2, L1.2, R1.1
SIGNAL3: J4.2, L4.2, R4.1
SIGNAL4: J5.2, L5.2, R5.1
SIGNAL5: J3.2, L3.2, R3.1
SPEAKER: H2.1, L2.1, R2.2
SPEAKER2: H1.1, L1.1, R1.2
SPEAKER3: H6.1, L4.1, R4.2
SPEAKER4: H9.1, L5.1, R5.2
SPEAKER5: H5.1, L3.1, R3.2
