duanestorey/Hifi-Amplifier/PCBs/1/BindingPosts/1.1/BindingPosts.kicad_sch

## KiCad design PCBs/1/BindingPosts/1.1/BindingPosts.kicad_sch (2023-10-25)

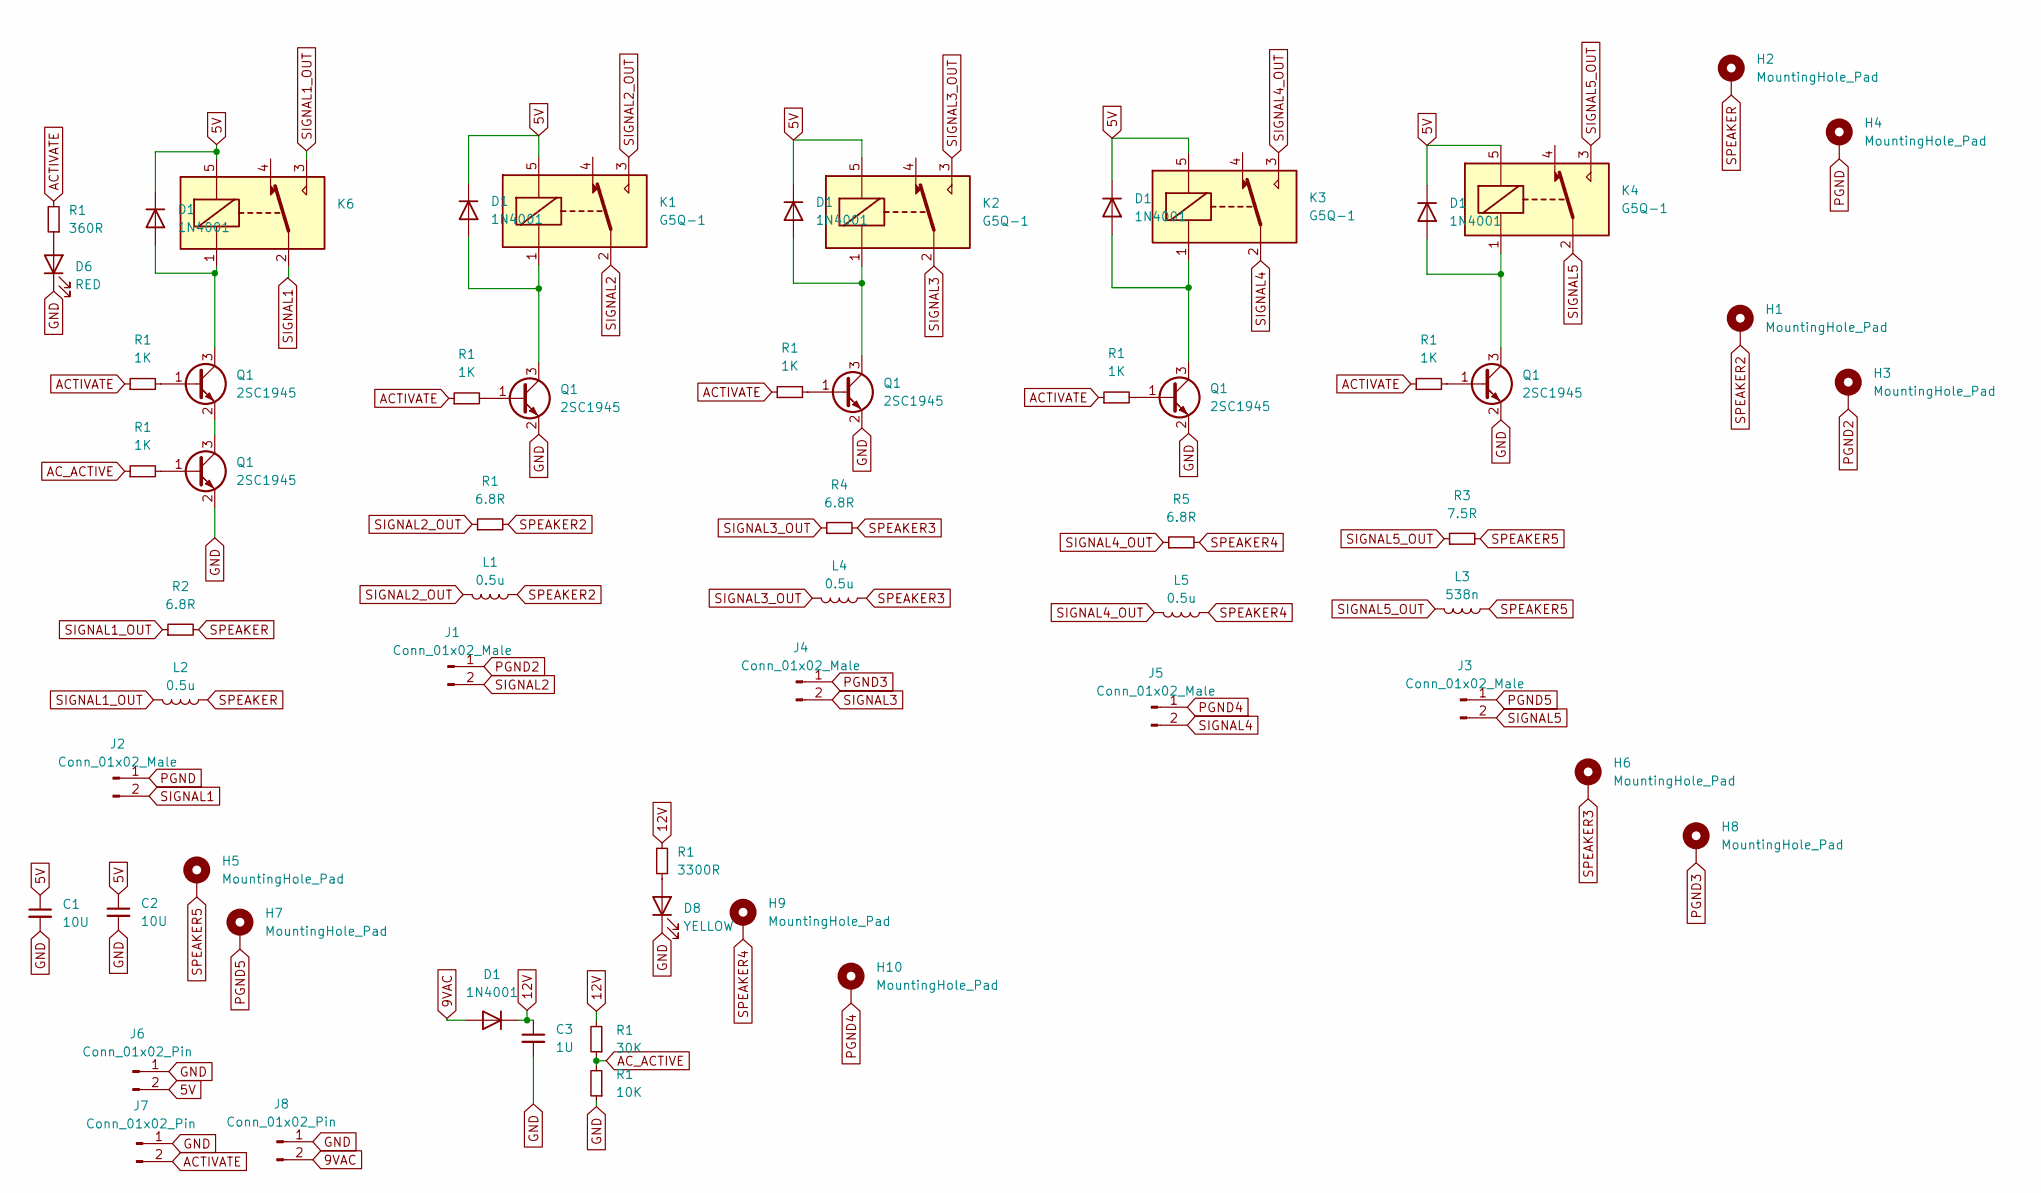
[picture p109: schematic BindingPosts.kicad_sch]

Parts:
C1, C2: 10U; C_1206_3216Metric_Pad1.33x1.80mm_HandSolder
C3: 1U; C_1206_3216Metric_Pad1.33x1.80mm_HandSolder
D1: 1N4001; D_SMA
D6: RED; LED_0805_2012Metric_Pad1.15x1.40mm_HandSolder
D8: YELLOW; LED_0805_2012Metric_Pad1.15x1.40mm_HandSolder
H1, H2, H3, H4, H5, H6, H7, H8, H9, H10: MountingHole_Pad; MountingHole_4.3mm_M4_DIN965_Pad
J1, J2, J3, J4, J5: Conn_01x02_Male; JST_VH_B2P-VH-B_1x02_P3.96mm_Vertical
J6, J7, J8: Conn_01x02_Pin; JST_PH_B2B-PH-K_1x02_P2.00mm_Vertical
K1, K2, K3, K4, K6: G5Q-1; Relay_SPST_Omron-G5Q-1A
L1, L2, L4, L5: 0.5u; Abracon 4125C Air Core Inductor 538nH
L3: 538n; Abracon 4125C Air Core Inductor 538nH
Q1: 2SC1945; SOT-23_Handsoldering
R1: 1K; R_0603_1608Metric
R2, R4, R5: 6.8R; R_4020_10251Metric_Pad1.65x5.30mm_HandSolder
R3: 7.5R; R_4020_10251Metric_Pad1.65x5.30mm_HandSolder

Connections:
5V: C1.1, C2.1, D1.1 (K), J6.2, K1.5, K2.5, K3.5, K4.5, K6.5
9VAC: D1.2 (A), J8.2
12V: C3.1, D1.1 (K), R1.2
ACTIVATE: J7.2, R1.1, R1.2
AC_ACTIVE: R1.1, R1.2
GND: C1.2, C2.2, C3.2, D6.1 (K), D8.1 (K), J6.1, J7.1, J8.1, Q1.2 (E), R1.1
unnamed: D1.2 (A), K1.1, K2.1, K3.1, K4.1, K6.1, Q1.3 (C)
unnamed: D6.2 (A), R1.1
unnamed: D8.2 (A), R1.1
unnamed: Q1.1 (B), R1.2
unnamed: Q1.2 (E), Q1.3 (C)
PGND: H4.1, J2.1
PGND2: H3.1, J1.1
PGND3: H8.1, J4.1
PGND4: H10.1, J5.1
PGND5: H7.1, J3.1
SIGNAL1: J2.2, K6.2
SIGNAL1_OUT: K6.3, L2.2, R2.1
SIGNAL2: J1.2, K1.2
SIGNAL2_OUT: K1.3, L1.2, R1.1
SIGNAL3: J4.2, K2.2
SIGNAL3_OUT: K2.3, L4.2, R4.1
SIGNAL4: J5.2, K3.2
SIGNAL4_OUT: K3.3, L5.2, R5.1
SIGNAL5: J3.2, K4.2
SIGNAL5_OUT: K4.3, L3.2, R3.1
SPEAKER: H2.1, L2.1, R2.2
SPEAKER2: H1.1, L1.1, R1.2
SPEAKER3: H6.1, L4.1, R4.2
SPEAKER4: H9.1, L5.1, R5.2
SPEAKER5: H5.1, L3.1, R3.2
