duanestorey/Hifi-Amplifier/PCBs/1/Channel Selector (Analog)/2.0/ChannelSelector.kicad_sch

## KiCad design PCBs/1/Channel Selector (Analog)/2.0/ChannelSelector.kicad_sch (2024-11-29)

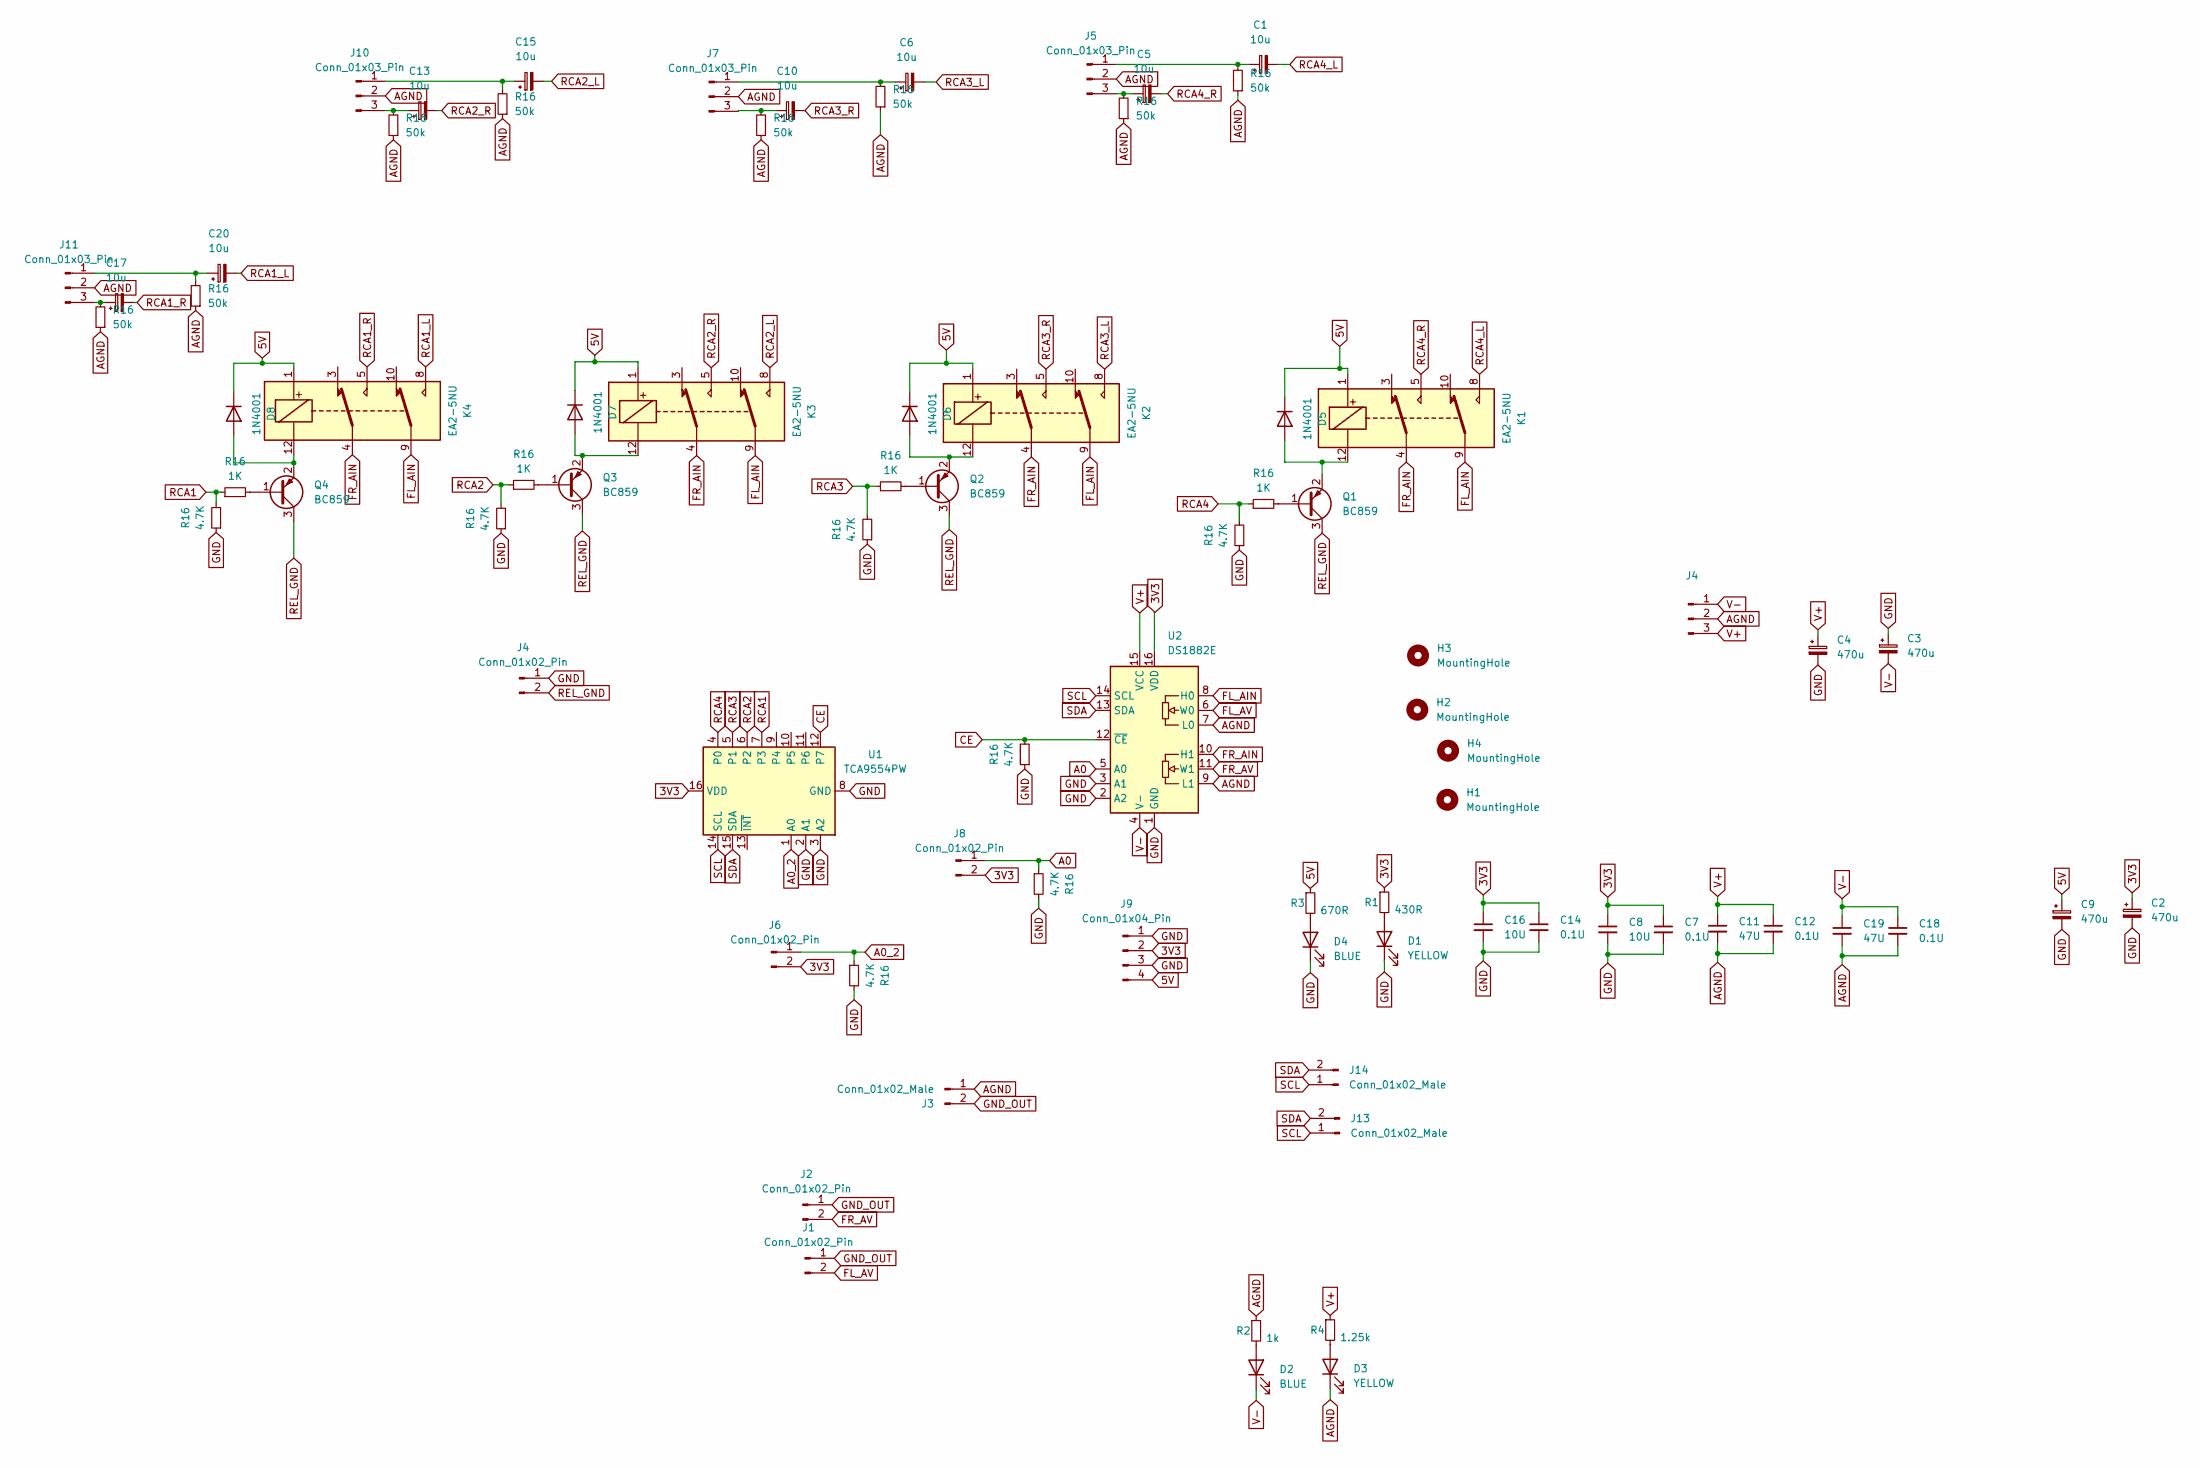
[picture p110: schematic ChannelSelector.kicad_sch]

Parts:
C1, C5, C6, C10, C13, C15, C17, C20: 10u; CP_Radial_D5.0mm_P2.00mm
C2, C3, C4, C9: 470u; CP_Radial_D6.3mm_P2.50mm
C7, C12, C14, C18: 0.1U; C_0805_2012Metric_Pad1.18x1.45mm_HandSolder
C8, C16: 10U; C_1206_3216Metric_Pad1.33x1.80mm_HandSolder
C11, C19: 47U; C_1206_3216Metric_Pad1.33x1.80mm_HandSolder
D1, D3: YELLOW; LED_0805_2012Metric_Pad1.15x1.40mm_HandSolder
D2, D4: BLUE; LED_0805_2012Metric_Pad1.15x1.40mm_HandSolder
D5, D6, D7, D8: 1N4001; D_SMA
H1, H2, H3, H4: MountingHole; MountingHole_3.2mm_M3
J1, J2: Conn_01x02_Pin; JST_PH_B2B-PH-K_1x02_P2.00mm_Vertical
J3: Conn_01x02_Male; PinHeader_1x02_P2.54mm_Vertical
J4: Conn_01x03_Male; JST_PH_B3B-PH-K_1x03_P2.00mm_Vertical
J5, J7, J10, J11: Conn_01x03_Pin; JST_PH_B3B-PH-K_1x03_P2.00mm_Vertical
J6, J8: Conn_01x02_Pin; PinHeader_1x02_P2.54mm_Vertical
J9: Conn_01x04_Pin; JST_XH_B4B-XH-A_1x04_P2.50mm_Vertical
J13, J14: Conn_01x02_Male; JST_PH_B2B-PH-K_1x02_P2.00mm_Vertical
K1, K2, K3, K4: EA2-5NU; KEMET EA2
Q1, Q2, Q3, Q4: BC859; SOT-23
R1: 430R; R_0603_1608Metric_Pad0.98x0.95mm_HandSolder
R2: 1k; R_0603_1608Metric_Pad0.98x0.95mm_HandSolder
R3: 670R; R_0603_1608Metric_Pad0.98x0.95mm_HandSolder
R4: 1.25k; R_0603_1608Metric_Pad0.98x0.95mm_HandSolder
R16: 50k; R_0603_1608Metric_Pad0.98x0.95mm_HandSolder
U1: TCA9554PW; TSSOP-16_4.4x5mm_P0.65mm
U2: DS1882E; TSSOP-16_4.4x5mm_P0.65mm

Connections:
3V3: C2.1, C7.1, C8.1, C14.1, C16.1, J6.2, J8.2, J9.2, R1.1, U1.16 (VDD), U2.16 (VDD)
5V: C9.1, D5.1 (K), D6.1 (K), D7.1 (K), D8.1 (K), J9.4, K1.1, K2.1, K3.1, K4.1, R3.1
A0: J8.1, R16.1, U2.5 (A0)
A0_2: J6.1, R16.1, U1.1 (A0)
AGND: C11.2, C12.2, C18.2, C19.2, D3.1 (K), J3.1, J4.2, J5.2, J7.2, J10.2, J11.2, R2.1, R16.1, U2.7 (L0), U2.9 (L1)
CE: R16.2, U1.12 (P7), U2.12 (~CE)
FL_AIN: K1.9, K2.9, K3.9, K4.9, U2.8 (H0)
FL_AV: J1.2, U2.6 (W0)
FR_AIN: K1.4, K2.4, K3.4, K4.4, U2.10 (H1)
FR_AV: J2.2, U2.11 (W1)
GND: C2.2, C3.1, C4.2, C7.2, C8.2, C9.2, C14.2, C16.2, D1.1 (K), D4.1 (K), J4.1, J9.1, J9.3, R16.1, R16.2, U1.2 (A1), U1.3 (A2), U1.8 (GND), U2.1 (GND), U2.2 (A2), U2.3 (A1)
GND_OUT: J1.1, J2.1, J3.2
unnamed: C1.1, J5.1, R16.2
unnamed: C5.1, J5.3, R16.2
unnamed: C6.1, J7.1, R16.2
unnamed: C10.1, J7.3, R16.2
unnamed: C13.1, J10.3, R16.2
unnamed: C15.1, J10.1, R16.2
unnamed: C17.1, J11.3, R16.2
unnamed: C20.1, J11.1, R16.2
unnamed: D1.2 (A), R1.2
unnamed: D2.2 (A), R2.2
unnamed: D3.2 (A), R4.2
unnamed: D4.2 (A), R3.2
unnamed: D5.2 (A), K1.12, Q1.2 (E)
unnamed: D6.2 (A), K2.12, Q2.2 (E)
unnamed: D7.2 (A), K3.12, Q3.2 (E)
unnamed: D8.2 (A), K4.12, Q4.2 (E)
unnamed: Q1.1 (B), R16.2
unnamed: Q2.1 (B), R16.2
unnamed: Q3.1 (B), R16.2
unnamed: Q4.1 (B), R16.2
RCA1: R16.1, R16.2, U1.7 (P3)
RCA1_L: C20.2, K4.8
RCA1_R: C17.2, K4.5
RCA2: R16.1, R16.2, U1.6 (P2)
RCA2_L: C15.2, K3.8
RCA2_R: C13.2, K3.5
RCA3: R16.1, R16.2, U1.5 (P1)
RCA3_L: C6.2, K2.8
RCA3_R: C10.2, K2.5
RCA4: R16.1, R16.2, U1.4 (P0)
RCA4_L: C1.2, K1.8
RCA4_R: C5.2, K1.5
REL_GND: J4.2, Q1.3 (C), Q2.3 (C), Q3.3 (C), Q4.3 (C)
SCL: J13.1, J14.1, U1.14 (SCL), U2.14 (SCL)
SDA: J13.2, J14.2, U1.15 (SDA), U2.13 (SDA)
V+: C4.1, C11.1, C12.1, J4.3, R4.1, U2.15 (VCC)
V-: C3.2, C18.1, C19.1, D2.1 (K), J4.1, U2.4 (V-)
