duanestorey/Hifi-Amplifier/PCBs/1/Ground Lift/v1.0.1/GroundLift.kicad_sch

## KiCad design PCBs/1/Ground Lift/v1.0.1/GroundLift.kicad_sch (2024-11-29)

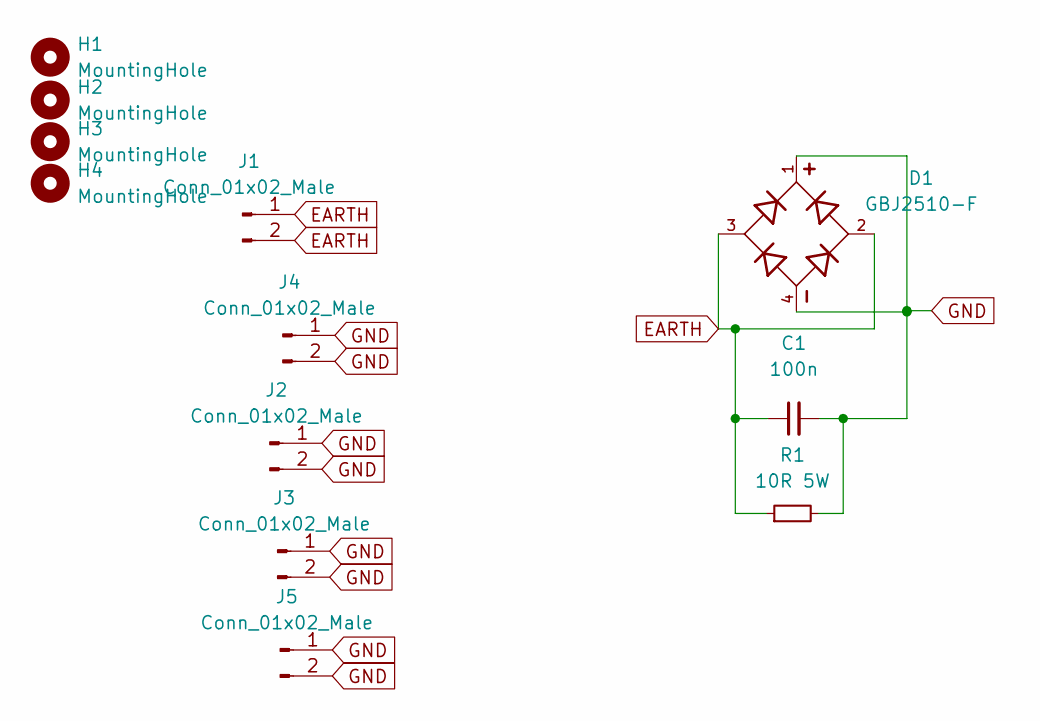
[picture p111: schematic GroundLift.kicad_sch]

Parts:
C1: 100n; C_Rect_L18.0mm_W5.0mm_P15.00mm_FKS3_FKP3
D1: GBJ2510-F; Diode_Bridge_19.0x19.0x6.8mm_P12.7mm
H1, H2, H3, H4: MountingHole; MountingHole_3.2mm_M3
J1: Conn_01x02_Male; JST_VH_B2P-VH-B_1x02_P3.96mm_Vertical
J2, J3, J4, J5: Conn_01x02_Male; TerminalBlock_Phoenix_MKDS-1,5-2-5.08_1x02_P5.08mm_Horizont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
R1: 10R 5W; R_Axial_Power_L25.0mm_W9.0mm_P27.94mm

Connections:
EARTH: C1.1, D1.2, D1.3, J1.1, J1.2, R1.1
GND: C1.2, D1.1, D1.4, J2.1, J2.2, J3.1, J3.2, J4.1, J4.2, J5.1, J5.2, R1.2
