duanestorey/Hifi-Amplifier/PCBs/1/Power Supply (Channel)/1.0.3/PowerSupply.kicad_sch

## KiCad design PCBs/1/Power Supply (Channel)/1.0.3/PowerSupply.kicad_sch (2023-10-17)

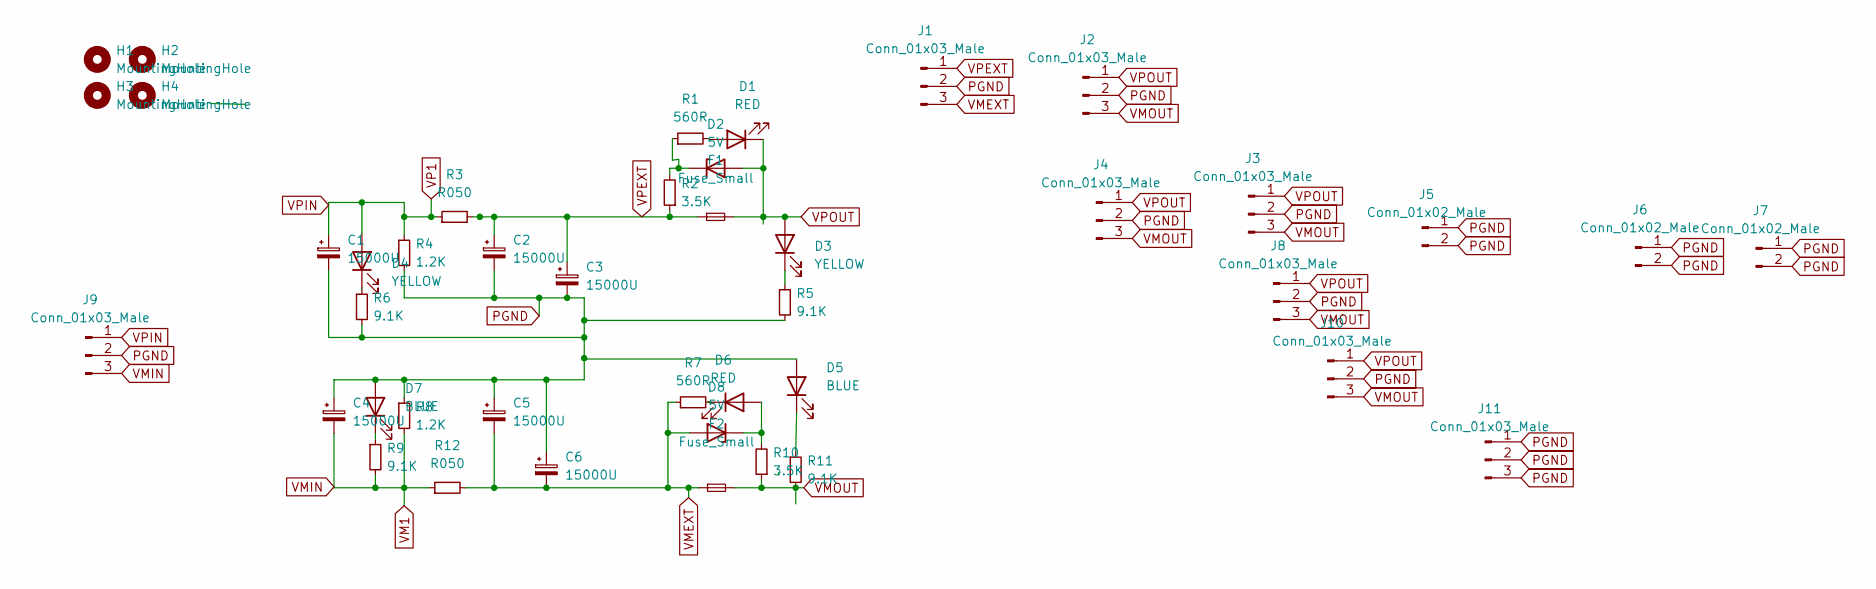
[picture p112: schematic PowerSupply.kicad_sch]

Parts:
C1, C2, C3, C4, C5, C6: 15000U; CP_Radial_D30.0mm_P10.00mm_SnapIn
D1, D6: RED; LED_0805_2012Metric_Pad1.15x1.40mm_HandSolder
D2, D8: 5V; D_MELF
D3, D4: YELLOW; LED_0805_2012Metric_Pad1.15x1.40mm_HandSolder
D5, D7: BLUE; LED_0805_2012Metric_Pad1.15x1.40mm_HandSolder
F1, F2: Fuse_Small; 5x20mm AliExpress 250V 6A
H1, H3: MountingHole; MountingHole_3mm
H2, H4: MountingHole; MountingHole_3.2mm_M3
J1, J2, J3, J4, J8, J9, J10: Conn_01x03_Male; JST_VH_B3P-VH_1x03_P3.96mm_Vertical
J5, J6: Conn_01x02_Male; JST_PH_B2B-PH-K_1x02_P2.00mm_Vertical
J7: Conn_01x02_Male; JST_VH_B2P-VH-B_1x02_P3.96mm_Vertical
J11: Conn_01x03_Male; JST_PH_B3B-PH-K_1x03_P2.00mm_Vertical
R1, R7: 560R; R_0805_2012Metric_Pad1.20x1.40mm_HandSolder
R2, R10: 3.5K; R_1206_3216Metric_Pad1.30x1.75mm_HandSolder
R3, R12: R050; R_2512_6332Metric_Pad1.40x3.35mm_HandSolder
R4, R8: 1.2K; R_2512_6332Metric_Pad1.40x3.35mm_HandSolder
R5, R6, R9, R11: 9.1K; R_0805_2012Metric_Pad1.20x1.40mm_HandSolder

Connections:
unnamed: D1.2 (A), R1.2
unnamed: D2.1 (K), R1.1, R2.2
unnamed: D3.1 (K), R5.1
unnamed: D4.1 (K), R6.1
unnamed: D5.1 (K), R11.1
unnamed: D6.1 (K), R7.2
unnamed: D6.2 (A), D8.1 (K), R10.2
unnamed: D7.1 (K), R9.1
PGND: C1.2, C2.2, C3.2, C4.1, C5.1, C6.1, D5.2 (A), D7.2 (A), J1.2, J2.2, J3.2, J4.2, J5.1, J5.2, J6.1, J6.2, J7.1, J7.2, J8.2, J9.2, J10.2, J11.1, J11.2, J11.3, R4.2, R5.2, R6.2, R8.1
VM1: C4.2, J9.3, R8.2, R9.2, R12.1
VMEXT: C5.2, C6.2, D8.2 (A), F2.1, J1.3, R7.1, R12.2
VMOUT: F2.2, J2.3, J3.3, J4.3, J8.3, J10.3, R10.1, R11.2
VP1: C1.1, D4.2 (A), J9.1, R3.1, R4.1
VPEXT: C2.1, C3.1, F1.1, J1.1, R2.1, R3.2
VPOUT: D1.1 (K), D2.2 (A), D3.2 (A), F1.2, J2.1, J3.1, J4.1, J8.1, J10.1
