duanestorey/Hifi-Amplifier/PCBs/1/Power Supply (Channel)/2.0/PowerSupply.kicad_sch

## KiCad design PCBs/1/Power Supply (Channel)/2.0/PowerSupply.kicad_sch (2024-11-29)

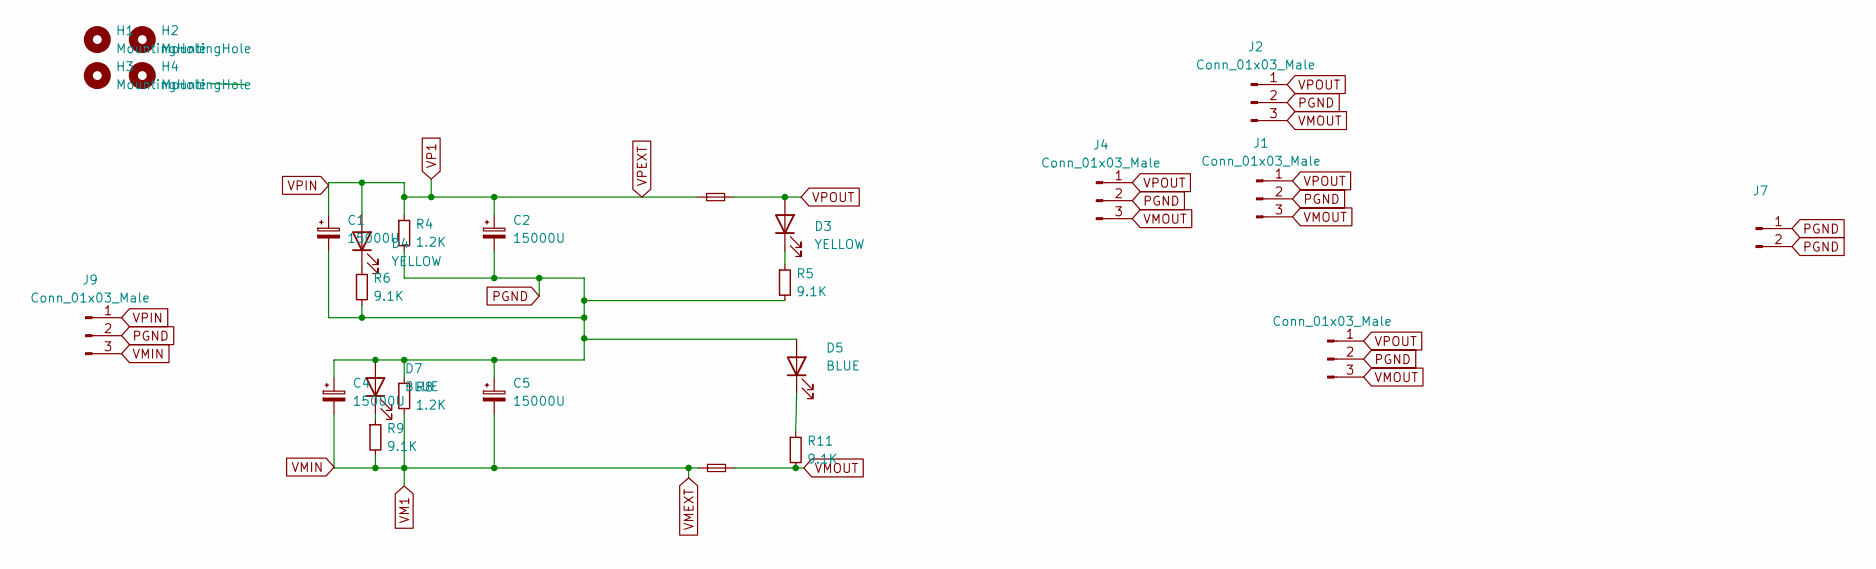
[picture p113: schematic PowerSupply.kicad_sch]

Parts:
C1, C2, C4, C5: 15000U; CP_Radial_D30.0mm_P10.00mm_SnapIn
D3, D4: YELLOW; LED_0805_2012Metric_Pad1.15x1.40mm_HandSolder
D5, D7: BLUE; LED_0805_2012Metric_Pad1.15x1.40mm_HandSolder
F1, F2: Fuse_Small; Aliexpress Fuse 5x20
H1, H3: MountingHole; MountingHole_3mm
H2, H4: MountingHole; MountingHole_3.2mm_M3
J1, J2, J4, J9, J10: Conn_01x03_Male; JST_VH_B3P-VH_1x03_P3.96mm_Vertical
J7: Conn_01x02_Male; JST_VH_B2P-VH-B_1x02_P3.96mm_Vertical
R4, R8: 1.2K; R_Axial_DIN0414_L11.9mm_D4.5mm_P15.24mm_Horizontal
R5, R6, R9, R11: 9.1K; R_0805_2012Metric_Pad1.20x1.40mm_HandSolder

Connections:
unnamed: D3.1 (K), R5.1
unnamed: D4.1 (K), R6.1
unnamed: D5.1 (K), R11.1
unnamed: D7.1 (K), R9.1
PGND: C1.2, C2.2, C4.1, C5.1, D5.2 (A), D7.2 (A), J1.2, J2.2, J4.2, J7.1, J7.2, J9.2, J10.2, R4.2, R5.2, R6.2, R8.1
VM1: C4.2, C5.2, F2.1, J9.3, R8.2, R9.2
VMOUT: F2.2, J1.3, J2.3, J4.3, J10.3, R11.2
VP1: C1.1, C2.1, D4.2 (A), F1.1, J9.1, R4.1
VPOUT: D3.2 (A), F1.2, J1.1, J2.1, J4.1, J10.1
