duanestorey/Hifi-Amplifier/PCBs/1/Rectifier/1.0/Rectifier.kicad_sch

## KiCad design PCBs/1/Rectifier/1.0/Rectifier.kicad_sch (2024-12-01)

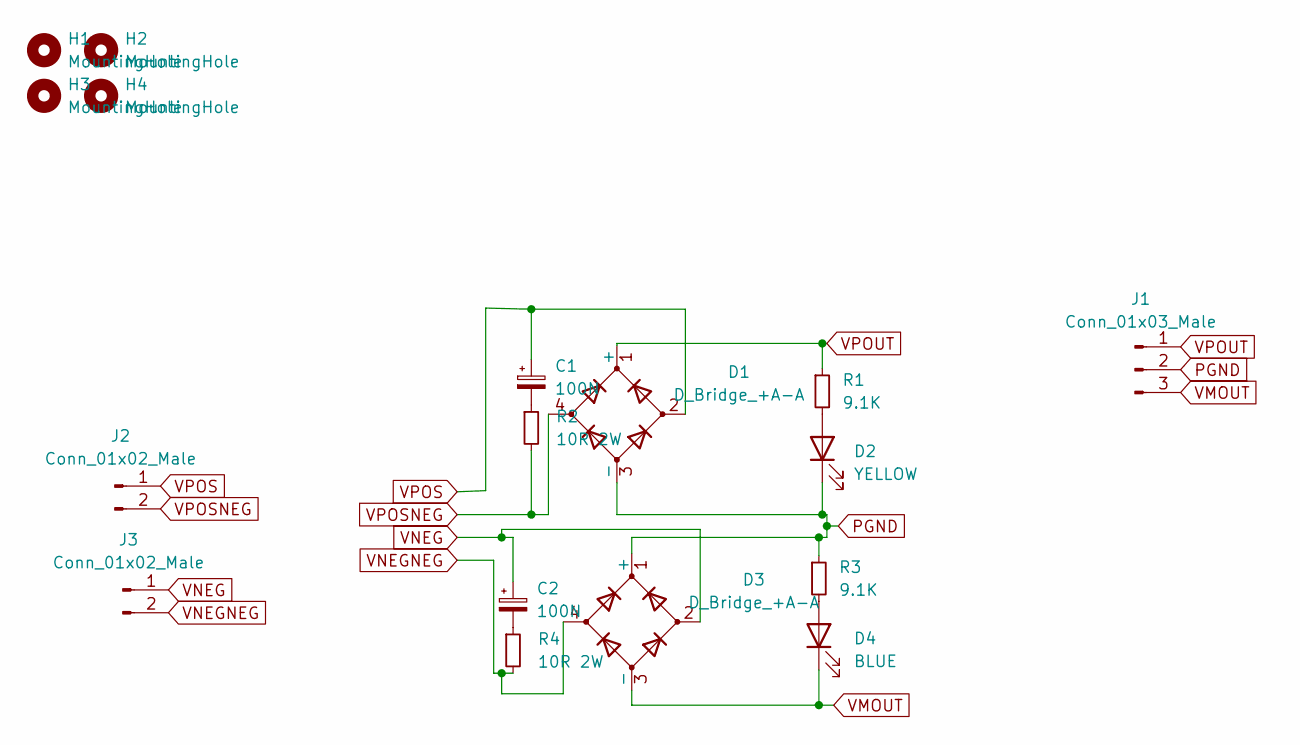
[picture p114: schematic Rectifier.kicad_sch]

Parts:
C1, C2: 100N; C_Rect_L13.0mm_W6.0mm_P10.00mm_FKS3_FKP3_MKS4
D1, D3: D_Bridge_+A-A; Diode_Bridge_19.0x19.0x6.8mm_P12.7mm
D2: YELLOW; LED_0805_2012Metric_Pad1.15x1.40mm_HandSolder
D4: BLUE; LED_0805_2012Metric_Pad1.15x1.40mm_HandSolder
H1, H3: MountingHole; MountingHole_3mm
H2, H4: MountingHole; MountingHole_3.2mm_M3
J1: Conn_01x03_Male; JST_VH_B3P-VH_1x03_P3.96mm_Vertical
J2, J3: Conn_01x02_Male; JST_VH_B2P-VH-B_1x02_P3.96mm_Vertical
R1, R3: 9.1K; R_0805_2012Metric_Pad1.20x1.40mm_HandSolder
R2, R4: 10R 2W; R_Axial_DIN0411_L9.9mm_D3.6mm_P15.24mm_Horizontal

Connections:
unnamed: C1.2, R2.1
unnamed: C2.2, R4.1
unnamed: D2.2 (A), R1.2
unnamed: D4.2 (A), R3.2
PGND: D1.3 (-), D2.1 (K), D3.1 (+), J1.2, R3.1
VMOUT: D3.3 (-), D4.1 (K), J1.3
VNEG: C2.1, D3.2, J3.1
VNEGNEG: D3.4, J3.2, R4.2
VPOS: C1.1, D1.2, J2.1
VPOSNEG: D1.4, J2.2, R2.2
VPOUT: D1.1 (+), J1.1, R1.1
