duanestorey/Hifi-Amplifier/PCBs/1/Relay AC/1.0/ ACRelay.kicad_sch

## KiCad design PCBs/1/Relay AC/1.0/ ACRelay.kicad_sch (2023-10-17)

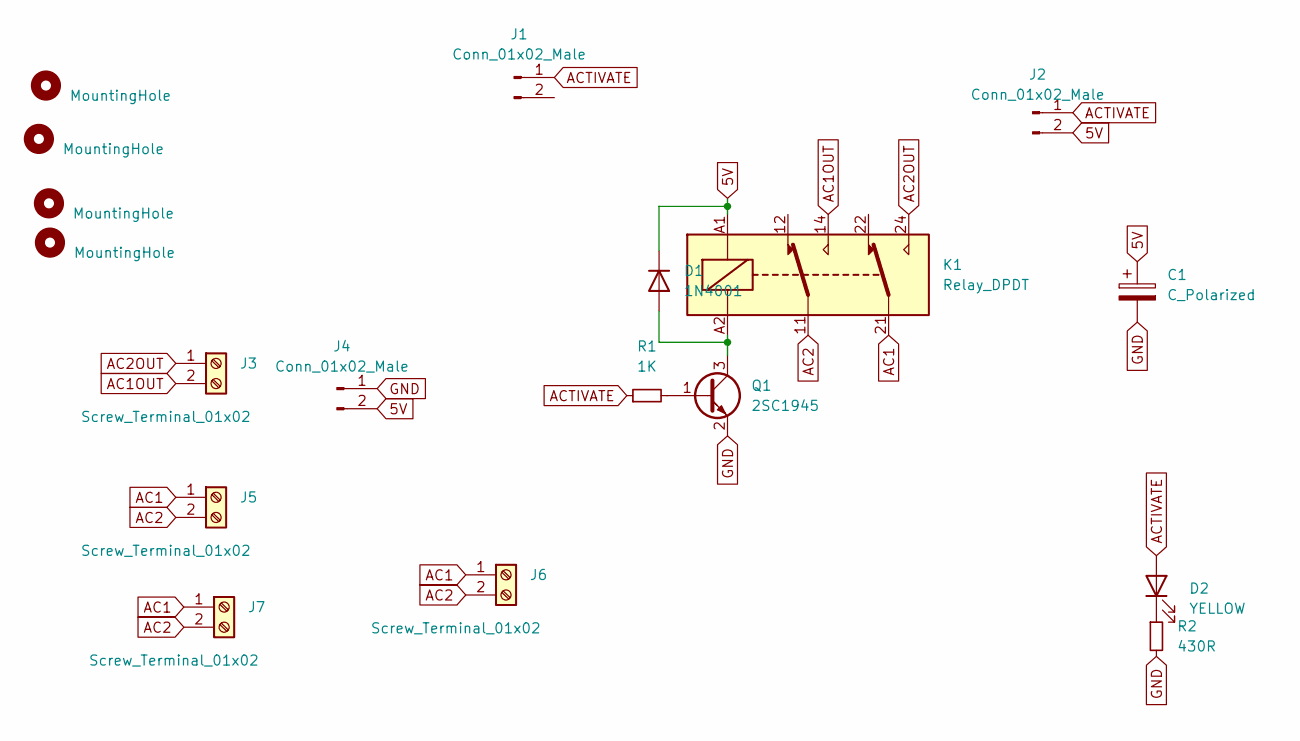
[picture p115: schematic ACRelay.kicad_sch]

Parts:
C1: C_Polarized; CP_Radial_D6.3mm_P2.50mm
D1: 1N4001; D_SMA
D2: YELLOW; D_0805_2012Metric_Pad1.15x1.40mm_HandSolder
H1, H2, H3, H4: MountingHole; MountingHole_3.2mm_M3
J1, J4: Conn_01x02_Male; JST_PH_B2B-PH-K_1x02_P2.00mm_Vertical
J2: Conn_01x02_Male; PinHeader_1x02_P2.54mm_Vertical
J3, J5, J6, J7: Screw_Terminal_01x02; JST_XH_B2B-XH-A_1x02_P2.50mm_Vertical
K1: Relay_DPDT; Relay_DPDT_Omron_G2RL-2
Q1: 2SC1945; SOT-23_Handsoldering
R1: 1K; R_0603_1608Metric
R2: 430R; R_0603_1608Metric_Pad0.98x0.95mm_HandSolder

Connections:
5V: C1.1, D1.1 (K), J2.2, J4.2, K1.A1
AC1: J5.1, J6.1, J7.1, K1.21
AC1OUT: J3.2, K1.14
AC2: J5.2, J6.2, J7.2, K1.11
AC2OUT: J3.1, K1.24
ACTIVATE: D2.2 (A), J1.1, J2.1, R1.1
GND: C1.2, J4.1, Q1.2 (E), R2.2
unnamed: D1.2 (A), K1.A2, Q1.3 (C)
unnamed: D2.1 (K), R2.1
unnamed: Q1.1 (B), R1.2
