duanestorey/Hifi-Amplifier/PCBs/1/Relay AC/2.0/ ACRelay.kicad_sch

## KiCad design PCBs/1/Relay AC/2.0/ ACRelay.kicad_sch (2023-10-27)

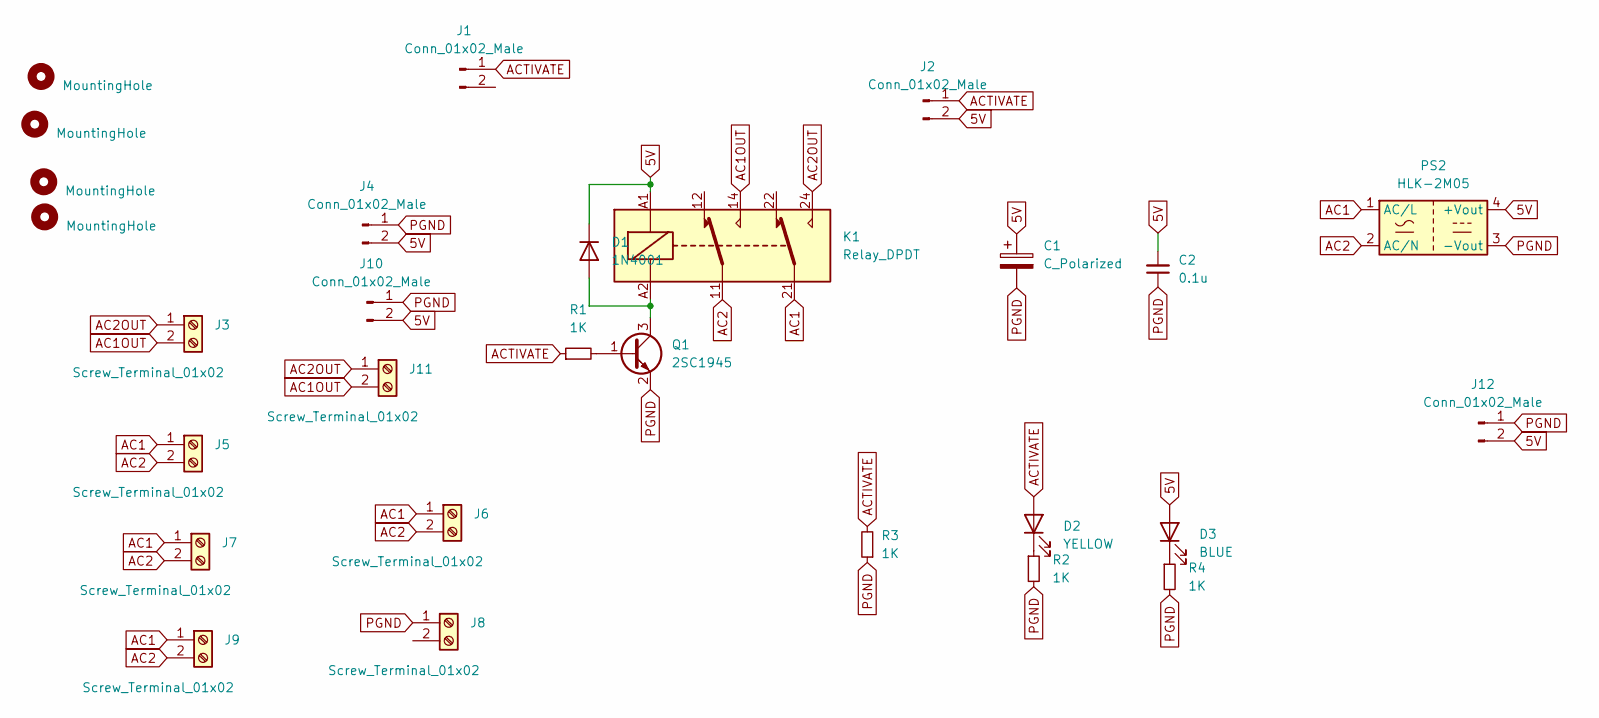
[picture p116: schematic ACRelay.kicad_sch]

Parts:
C1: C_Polarized; CP_Radial_D8.0mm_P2.50mm
C2: 0.1u; C_0805_2012Metric_Pad1.18x1.45mm_HandSolder
D1: 1N4001; D_SMA
D2: YELLOW; D_0805_2012Metric_Pad1.15x1.40mm_HandSolder
D3: BLUE; D_0805_2012Metric_Pad1.15x1.40mm_HandSolder
H1, H2, H3, H4: MountingHole; MountingHole_3.2mm_M3
J1, J4, J10: Conn_01x02_Male; JST_PH_B2B-PH-K_1x02_P2.00mm_Vertical
J2, J12: Conn_01x02_Male; PinHeader_1x02_P2.54mm_Vertical
J3, J5, J6, J7, J8, J9, J11: Screw_Terminal_01x02; JST_XH_B2B-XH-A_1x02_P2.50mm_Vertical
K1: Relay_DPDT; Relay_DPDT_Omron_G2RL-2
PS2: HLK-2M05
Q1: 2SC1945; SOT-23_Handsoldering
R1, R3: 1K; R_0603_1608Metric
R2, R4: 1K; R_0603_1608Metric_Pad0.98x0.95mm_HandSolder

Connections:
5V: C1.1, C2.2, D1.1 (K), D3.2 (A), J2.2, J4.2, J10.2, J12.2, K1.A1, PS2.4 (+Vout)
AC1: J5.1, J6.1, J7.1, J9.1, K1.21, PS2.1 (AC/L)
AC1OUT: J3.2, J11.2, K1.14
AC2: J5.2, J6.2, J7.2, J9.2, K1.11, PS2.2 (AC/N)
AC2OUT: J3.1, J11.1, K1.24
ACTIVATE: D2.2 (A), J1.1, J2.1, R1.1, R3.2
unnamed: D1.2 (A), K1.A2, Q1.3 (C)
unnamed: D2.1 (K), R2.1
unnamed: D3.1 (K), R4.1
unnamed: Q1.1 (B), R1.2
PGND: C1.2, C2.1, J4.1, J8.1, J10.1, J12.1, PS2.3 (-Vout), Q1.2 (E), R2.2, R3.1, R4.2
