duanestorey/Hifi-Amplifier/PCBs/1/Vinyl Pre-amp/1.0/Phono Pre-amp.kicad_sch

## KiCad design PCBs/1/Vinyl Pre-amp/1.0/Phono Pre-amp.kicad_sch (2023-10-04)

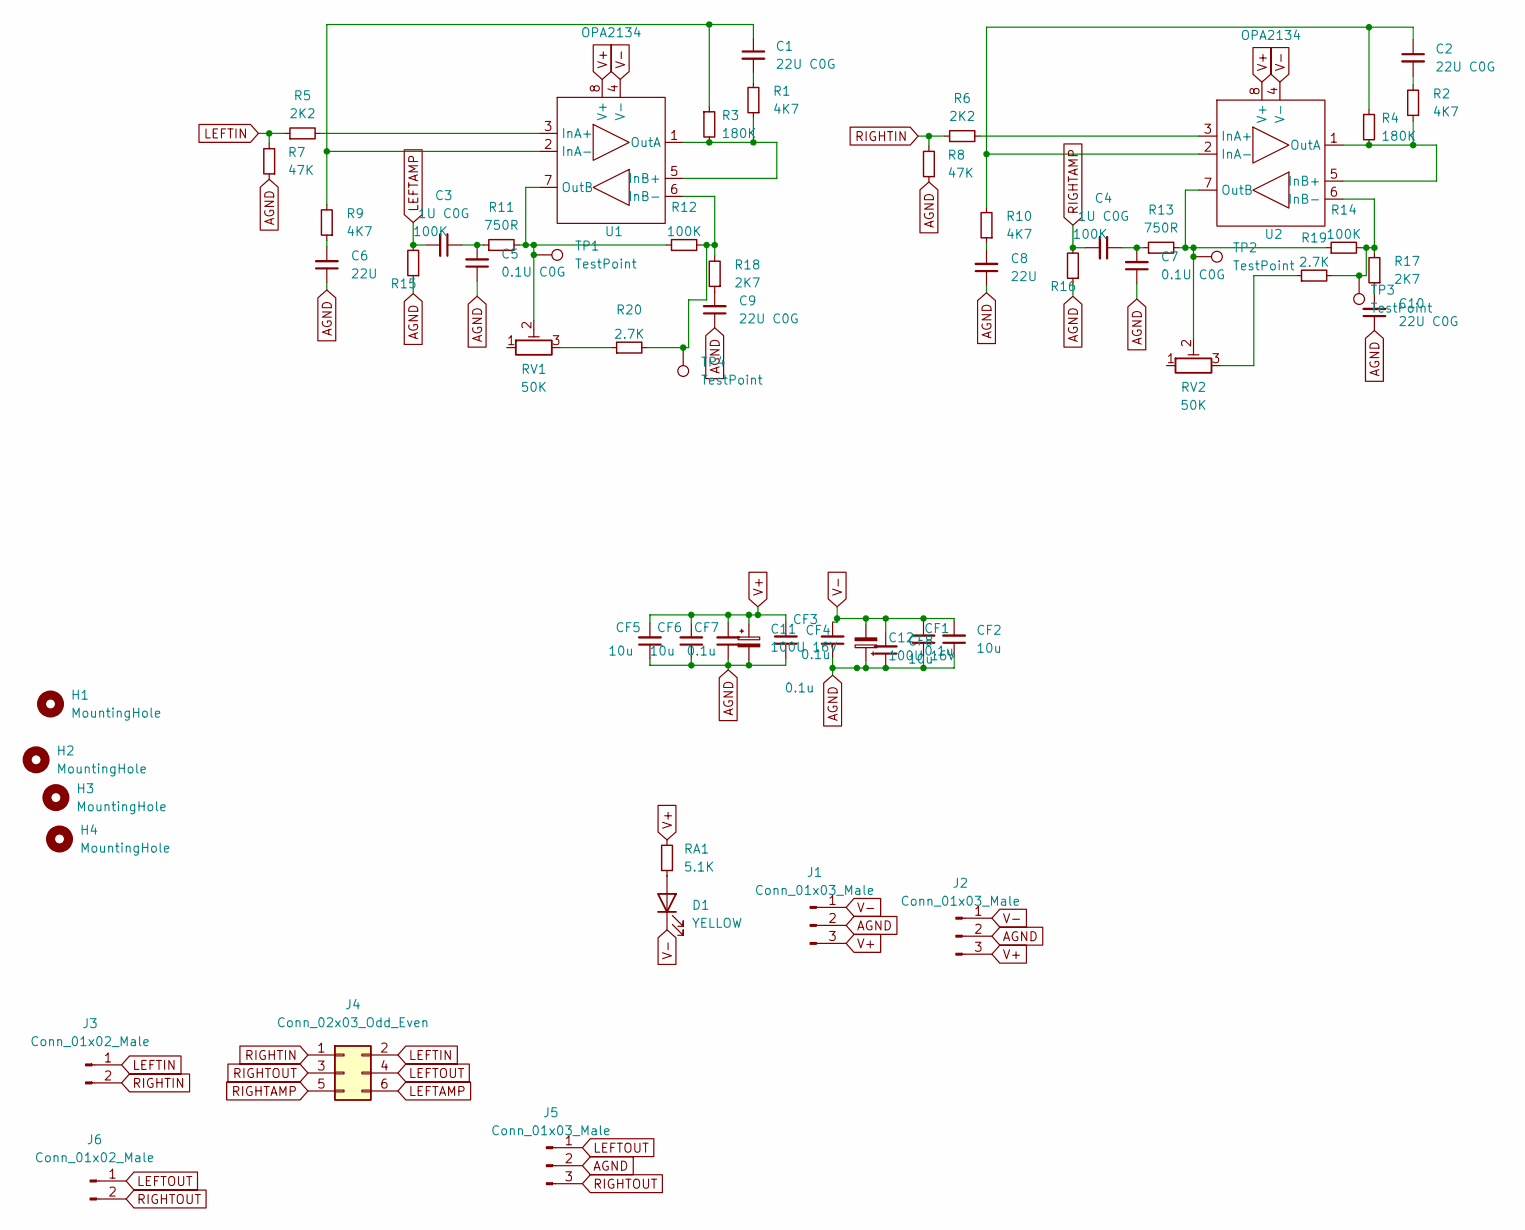
[picture p117: schematic Phono Pre-amp.kicad_sch]

Parts:
C1, C2, C9, C10: 22U C0G; CP_Radial_D5.0mm_P2.00mm
C3, C4: 1U C0G; CP_Radial_D5.0mm_P2.00mm
C5, C7: 0.1U C0G; C_1206_3216Metric_Pad1.33x1.80mm_HandSolder
C6, C8: 22U; CP_Radial_D5.0mm_P2.00mm
C11, C12: 100U 16V; CP_Radial_D6.3mm_P2.50mm
CF1, CF3, CF4, CF7: 0.1u; C_0805_2012Metric_Pad1.18x1.45mm_HandSolder
CF2, CF5, CF6, CF8: 10u; C_1206_3216Metric_Pad1.33x1.80mm_HandSolder
D1: YELLOW; LED_0805_2012Metric_Pad1.15x1.40mm_HandSolder
H1, H2, H3, H4: MountingHole; MountingHole_3.2mm_M3
J1, J2: Conn_01x03_Male; JST_PH_B3B-PH-K_1x03_P2.00mm_Vertical
J3, J6: Conn_01x02_Male; JST_PH_B2B-PH-K_1x02_P2.00mm_Vertical
J4: Conn_02x03_Odd_Even; PinHeader_2x03_P2.54mm_Vertical
J5: Conn_01x03_Male; PinHeader_1x03_P2.54mm_Vertical
R1, R2, R9, R10: 4K7; R_0805_2012Metric_Pad1.20x1.40mm_HandSolder
R3, R4: 180K; R_0805_2012Metric_Pad1.20x1.40mm_HandSolder
R5, R6: 2K2; R_0805_2012Metric_Pad1.20x1.40mm_HandSolder
R7, R8: 47K; R_0805_2012Metric_Pad1.20x1.40mm_HandSolder
R11, R13: 750R; R_0805_2012Metric_Pad1.20x1.40mm_HandSolder
R12, R14, R15, R16: 100K; R_0805_2012Metric_Pad1.20x1.40mm_HandSolder
R17, R18: 2K7; R_0805_2012Metric_Pad1.20x1.40mm_HandSolder
R19, R20: 2.7K; R_0805_2012Metric_Pad1.20x1.40mm_HandSolder
RA1: 5.1K; R_0603_1608Metric
RV1, RV2: 50K; Potentiometer_Bourns_3296W_Vertical
TP1, TP2, TP3, TP4: TestPoint; TestPoint_THTPad_1.5x1.5mm_Drill0.7mm
U1, U2: OPA2134; DIP-8_W7.62mm_Socket

Connections:
AGND: C5.1, C6.1, C7.1, C8.1, C9.1, C10.1, C11.2, C12.1, CF1.1, CF2.1, CF3.1, CF4.1, CF5.1, CF6.1, CF7.1, CF8.1, J1.2, J2.2, J5.2, R7.1, R8.1, R15.1, R16.1
LEFTAMP: C3.2, J4.6, R15.2
LEFTIN: J3.1, J4.2, R5.1, R7.2
LEFTOUT: J4.4, J5.1, J6.1
unnamed: C1.1, R3.1, R9.2, U1.2 (InA-)
unnamed: C1.2, R1.2
unnamed: C2.1, R4.1, R10.2, U2.2 (InA-)
unnamed: C2.2, R2.2
unnamed: C3.1, C5.2, R11.1
unnamed: C4.1, C7.2, R13.1
unnamed: C6.2, R9.1
unnamed: C8.2, R10.1
unnamed: C9.2, R18.1
unnamed: C10.2, R17.1
unnamed: D1.2 (A), RA1.1
unnamed: R1.1, R3.2, U1.1 (OutA), U1.5 (InB+)
unnamed: R2.1, R4.2, U2.1 (OutA), U2.5 (InB+)
unnamed: R5.2, U1.3 (InA+)
unnamed: R6.2, U2.3 (InA+)
unnamed: R11.2, R12.1, RV1.2, TP1.1, U1.7 (OutB)
unnamed: R12.2, R18.2, R20.2, TP4.1, U1.6 (InB-)
unnamed: R13.2, R14.1, RV2.2, TP2.1, U2.7 (OutB)
unnamed: R14.2, R17.2, R19.2, TP3.1, U2.6 (InB-)
unnamed: R19.1, RV2.3
unnamed: R20.1, RV1.3
RIGHTAMP: C4.2, J4.5, R16.2
RIGHTIN: J3.2, J4.1, R6.1, R8.2
RIGHTOUT: J4.3, J5.3, J6.2
V+: C11.1, CF3.2, CF5.2, CF6.2, CF7.2, J1.3, J2.3, RA1.2, U1.8 (V+), U2.8 (V+)
V-: C12.2, CF1.2, CF2.2, CF4.2, CF8.2, D1.1 (K), J1.1, J2.1, U1.4 (V-), U2.4 (V-)
