duanestorey/Hifi-Amplifier/PCBs/1/Vinyl Pre-amp/1.1/Phono Pre-amp.kicad_sch

## KiCad design PCBs/1/Vinyl Pre-amp/1.1/Phono Pre-amp.kicad_sch (2023-10-21)

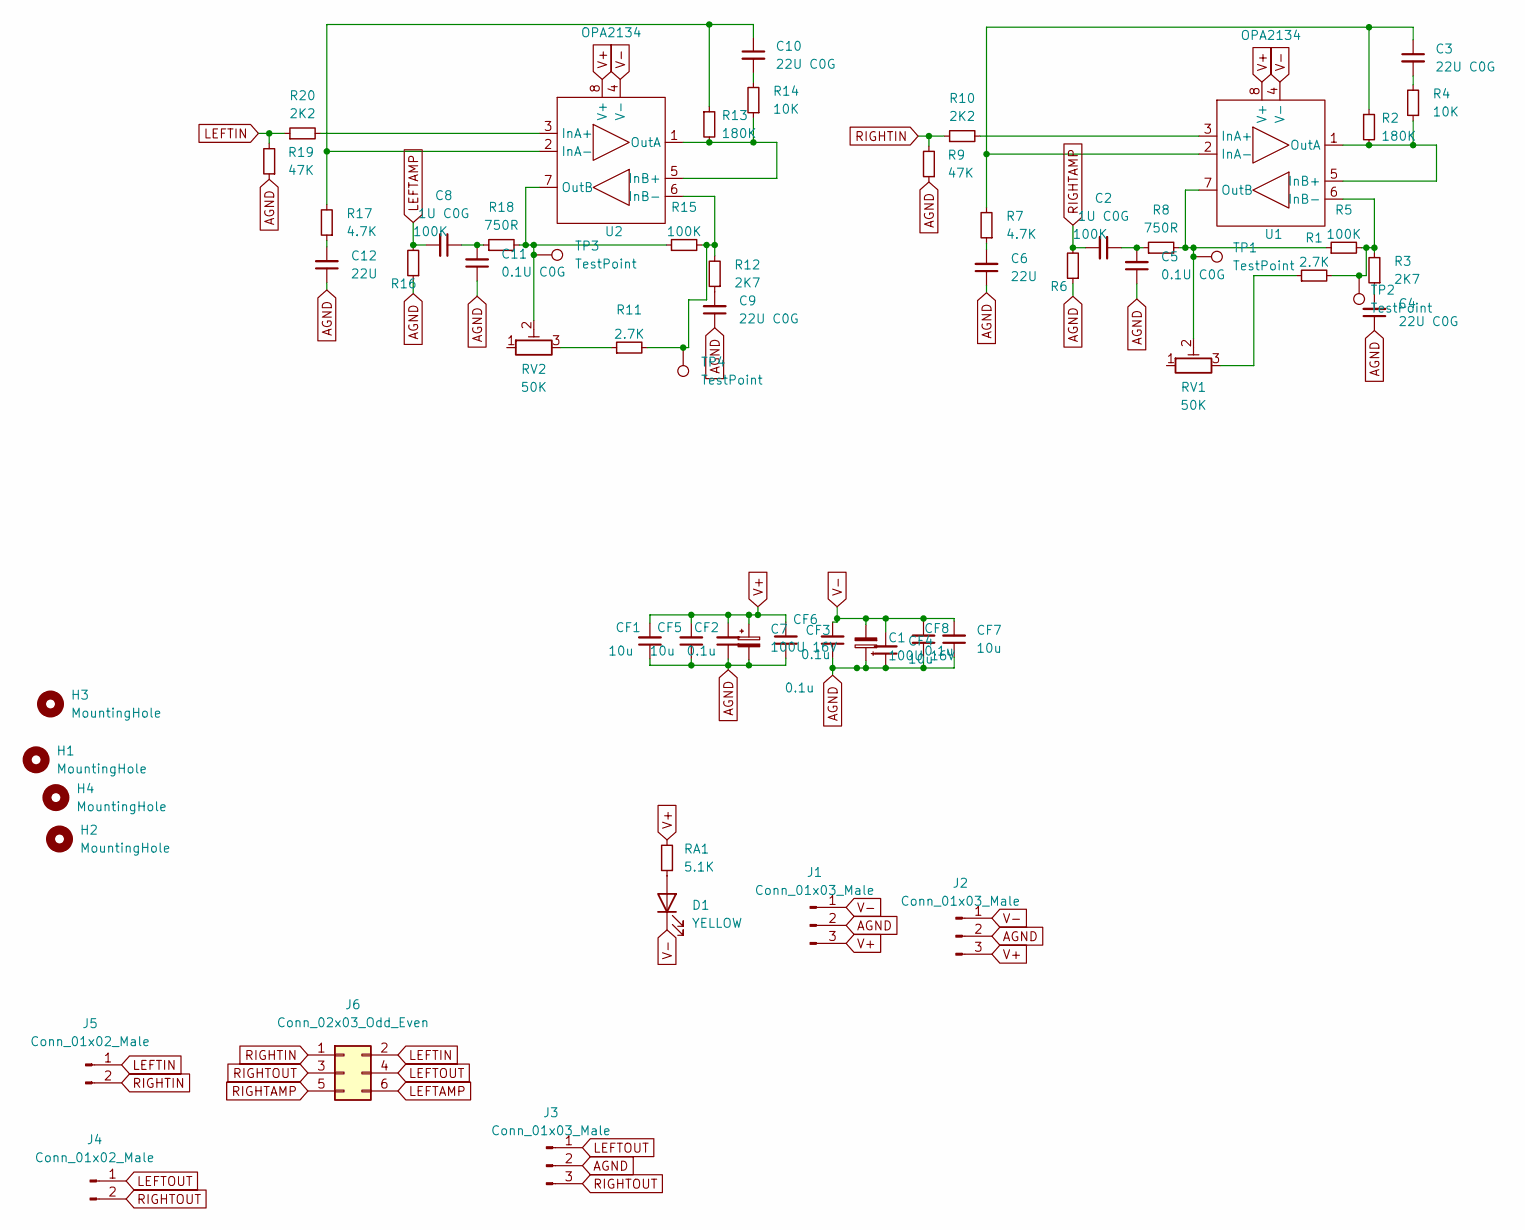
[picture p118: schematic Phono Pre-amp.kicad_sch]

Parts:
C1, C7: 100U 16V; CP_Radial_D6.3mm_P2.50mm
C2, C8: 1U C0G; CP_Radial_D5.0mm_P2.00mm
C3, C4, C9, C10: 22U C0G; CP_Radial_D5.0mm_P2.00mm
C5, C11: 0.1U C0G; C_1206_3216Metric_Pad1.33x1.80mm_HandSolder
C6, C12: 22U; CP_Radial_D5.0mm_P2.00mm
CF1, CF4, CF5, CF7: 10u; C_1206_3216Metric_Pad1.33x1.80mm_HandSolder
CF2, CF3, CF6, CF8: 0.1u; C_0805_2012Metric_Pad1.18x1.45mm_HandSolder
D1: YELLOW; LED_0805_2012Metric_Pad1.15x1.40mm_HandSolder
H1, H2, H3, H4: MountingHole; MountingHole_3.2mm_M3
J1, J2: Conn_01x03_Male; JST_PH_B3B-PH-K_1x03_P2.00mm_Vertical
J3: Conn_01x03_Male; PinHeader_1x03_P2.54mm_Vertical
J4, J5: Conn_01x02_Male; JST_PH_B2B-PH-K_1x02_P2.00mm_Vertical
J6: Conn_02x03_Odd_Even; PinHeader_2x03_P2.54mm_Vertical
R1, R11: 2.7K; R_0805_2012Metric_Pad1.20x1.40mm_HandSolder
R2, R13: 180K; R_0805_2012Metric_Pad1.20x1.40mm_HandSolder
R3, R12: 2K7; R_0805_2012Metric_Pad1.20x1.40mm_HandSolder
R4, R14: 10K; R_0805_2012Metric_Pad1.20x1.40mm_HandSolder
R5, R6, R15, R16: 100K; R_0805_2012Metric_Pad1.20x1.40mm_HandSolder
R7, R17: 4.7K; R_0805_2012Metric_Pad1.20x1.40mm_HandSolder
R8, R18: 750R; R_0805_2012Metric_Pad1.20x1.40mm_HandSolder
R9, R19: 47K; R_0805_2012Metric_Pad1.20x1.40mm_HandSolder
R10, R20: 2K2; R_0805_2012Metric_Pad1.20x1.40mm_HandSolder
RA1: 5.1K; R_0603_1608Metric
RV1, RV2: 50K; Potentiometer_Bourns_3296W_Vertical
TP1, TP2, TP3, TP4: TestPoint; TestPoint_THTPad_1.5x1.5mm_Drill0.7mm
U1, U2: OPA2134; DIP-8_W7.62mm_Socket

Connections:
AGND: C1.1, C4.1, C5.1, C6.1, C7.2, C9.1, C11.1, C12.1, CF1.1, CF2.1, CF3.1, CF4.1, CF5.1, CF6.1, CF7.1, CF8.1, J1.2, J2.2, J3.2, R6.1, R9.1, R16.1, R19.1
LEFTAMP: C8.2, J6.6, R16.2
LEFTIN: J5.1, J6.2, R19.2, R20.1
LEFTOUT: J3.1, J4.1, J6.4
unnamed: C2.1, C5.2, R8.1
unnamed: C3.1, R2.1, R7.2, U1.2 (InA-)
unnamed: C3.2, R4.2
unnamed: C4.2, R3.1
unnamed: C6.2, R7.1
unnamed: C9.2, R12.1
unnamed: C10.1, R13.1, R17.2, U2.2 (InA-)
unnamed: C10.2, R14.2
unnamed: C8.1, C11.2, R18.1
unnamed: C12.2, R17.1
unnamed: D1.2 (A), RA1.1
unnamed: R1.1, RV1.3
unnamed: R1.2, R3.2, R5.2, TP2.1, U1.6 (InB-)
unnamed: R2.2, R4.1, U1.1 (OutA), U1.5 (InB+)
unnamed: R5.1, R8.2, RV1.2, TP1.1, U1.7 (OutB)
unnamed: R10.2, U1.3 (InA+)
unnamed: R11.1, RV2.3
unnamed: R11.2, R12.2, R15.2, TP4.1, U2.6 (InB-)
unnamed: R13.2, R14.1, U2.1 (OutA), U2.5 (InB+)
unnamed: R15.1, R18.2, RV2.2, TP3.1, U2.7 (OutB)
unnamed: R20.2, U2.3 (InA+)
RIGHTAMP: C2.2, J6.5, R6.2
RIGHTIN: J5.2, J6.1, R9.2, R10.1
RIGHTOUT: J3.3, J4.2, J6.3
V+: C7.1, CF1.2, CF2.2, CF5.2, CF6.2, J1.3, J2.3, RA1.2, U1.8 (V+), U2.8 (V+)
V-: C1.2, CF3.2, CF4.2, CF7.2, CF8.2, D1.1 (K), J1.1, J2.1, U1.4 (V-), U2.4 (V-)
