duanestorey/Hifi-Amplifier/PCBs/Power Supply (Streamer)/1.0/Streamer/Streamer.kicad_sch

## KiCad design PCBs/Power Supply (Streamer)/1.0/Streamer/Streamer.kicad_sch (2023-10-25)

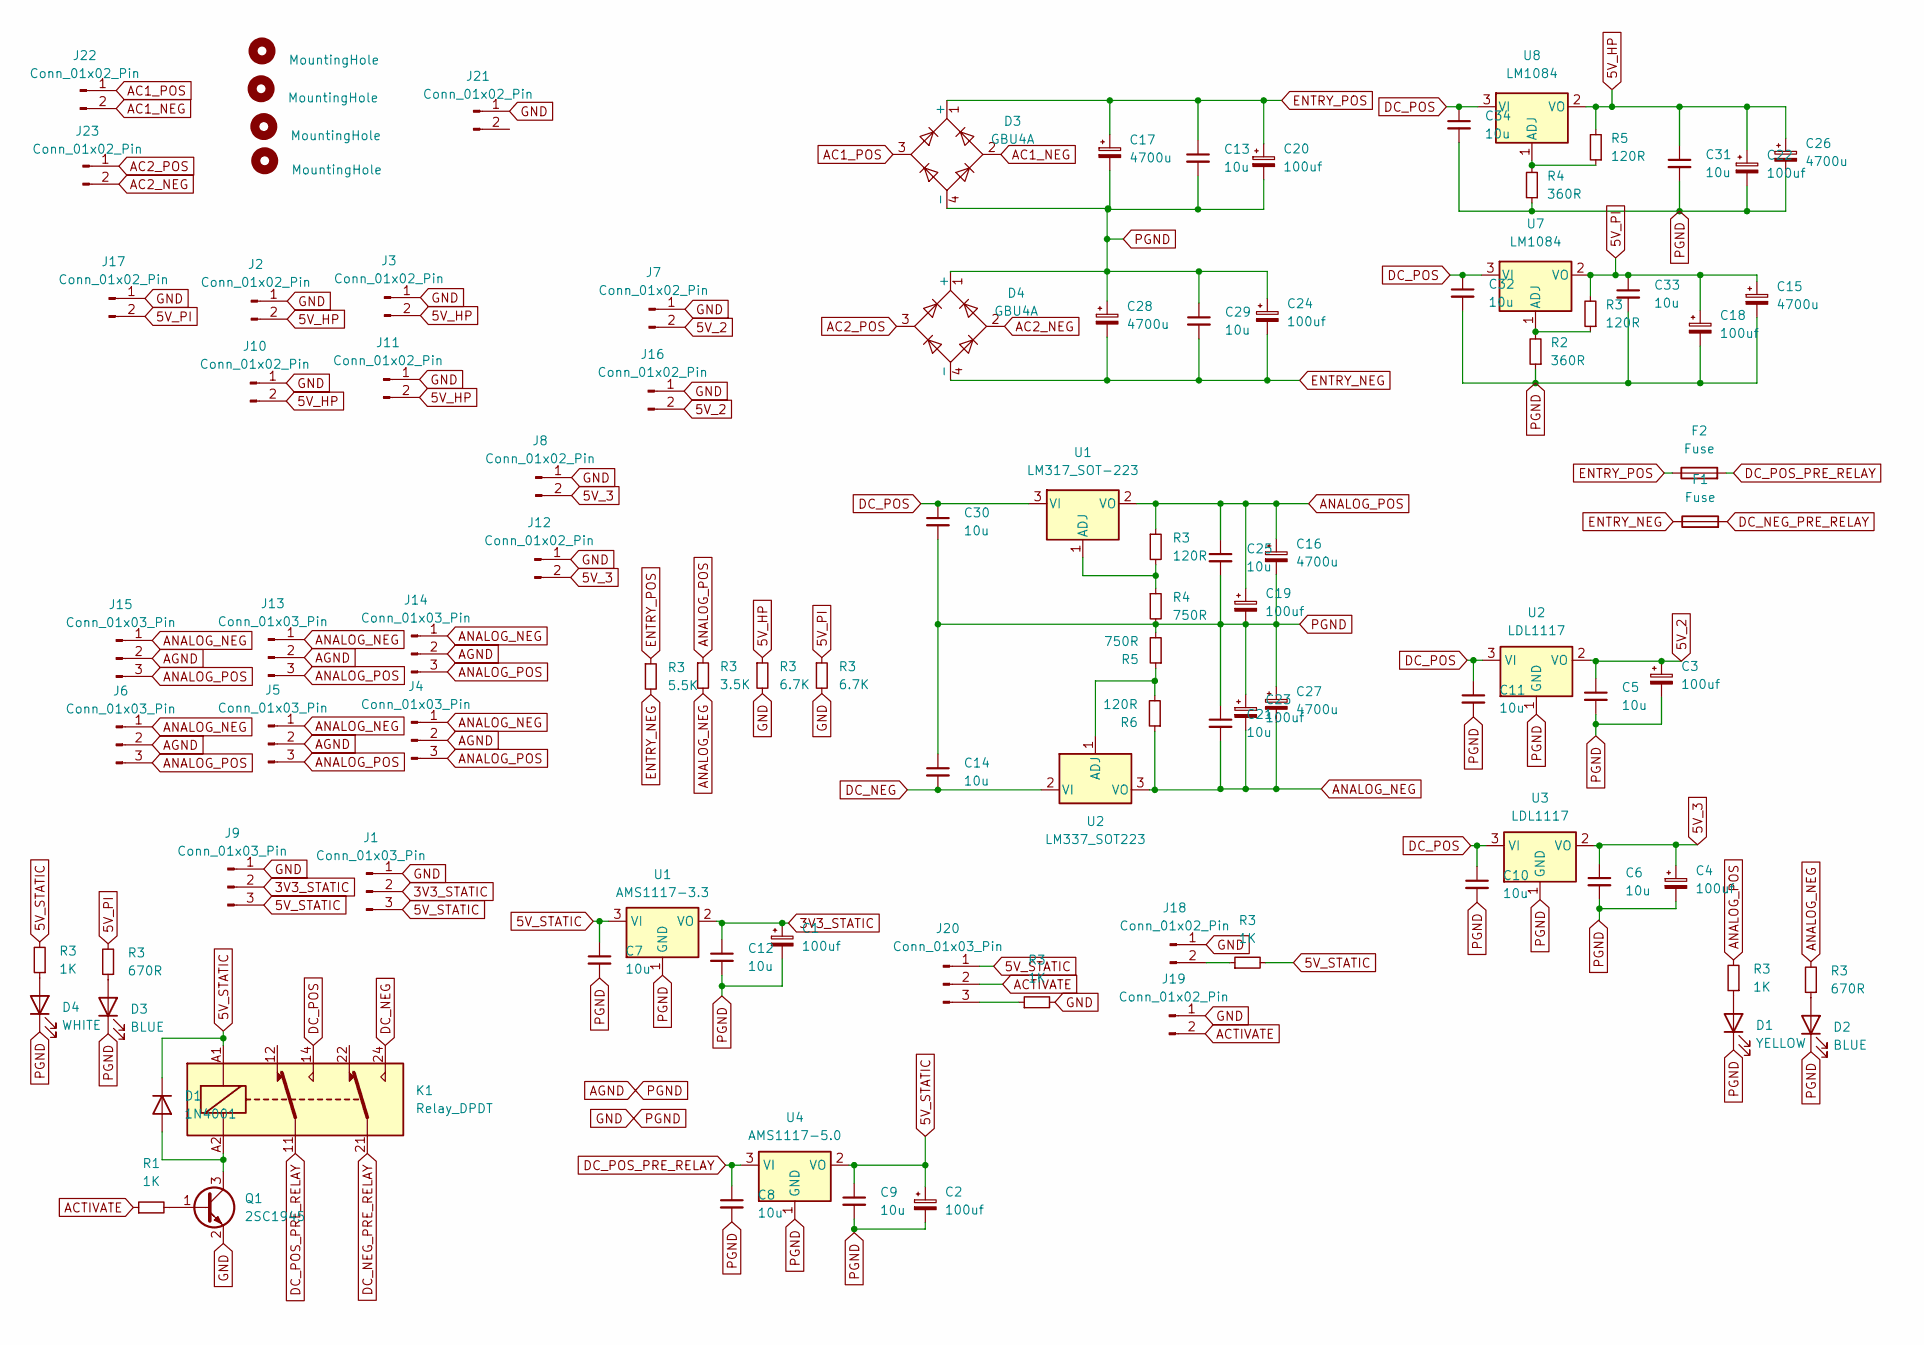
[picture p119: schematic Streamer.kicad_sch]

Parts:
C1, C2, C3, C4, C18, C19, C20, C22, C23, C24: 100uf; CP_Radial_D5.0mm_P2.00mm
C5, C6, C7, C8, C9, C10, C11, C12, C13, C14, C21, C25, C29, C30, C31, C32, C33, C34: 10u; C_1206_3216Metric_Pad1.33x1.80mm_HandSolder
C15, C16, C17, C26, C27, C28: 4700u; CP_Radial_D16.0mm_P7.50mm
D1: 1N4001; D_SMA
D2, D3: BLUE; LED_0805_2012Metric_Pad1.15x1.40mm_HandSolder
D4: WHITE; LED_0805_2012Metric_Pad1.15x1.40mm_HandSolder
F1, F2: Fuse; Aliexpress Fuse 5x20
H1, H2, H3, H4: MountingHole; MountingHole_3.2mm_M3
J1, J4, J5, J6, J20: Conn_01x03_Pin; JST_PH_B3B-PH-K_1x03_P2.00mm_Vertical
J2, J3, J17: Conn_01x02_Pin; JST_XH_B2B-XH-A_1x02_P2.50mm_Vertical
J7, J8, J18, J19: Conn_01x02_Pin; JST_PH_B2B-PH-K_1x02_P2.00mm_Vertical
J9, J13, J14, J15: Conn_01x03_Pin; PinHeader_1x03_P2.54mm_Vertical
J10, J11, J12, J16: Conn_01x02_Pin; PinHeader_1x02_P2.54mm_Vertical
J21, J22, J23: Conn_01x02_Pin; JST_VH_B2P-VH_1x02_P3.96mm_Vertical
K1: Relay_DPDT; Relay_DPDT_Omron_G2RL-2
Q1: 2SC1945; SOT-23_Handsoldering
R1: 1K; R_0603_1608Metric
R2, R4: 360R; R_0603_1608Metric_Pad0.98x0.95mm_HandSolder
R3: 1K; R_0603_1608Metric_Pad0.98x0.95mm_HandSolder
R5, R6: 120R; R_0603_1608Metric_Pad0.98x0.95mm_HandSolder
U1: AMS1117-3.3; SOT-223-3_TabPin2
U2, U3: LDL1117; SOT-223-3_TabPin2
U4: AMS1117-5.0; SOT-223-3_TabPin2
U7, U8: LM1084; TO-220-3_Vertical

Connections:
3V3_STATIC: C1.1, C12.1, J1.2, J9.2, U1.2 (VO)
5V_2: C3.1, C5.1, J7.2, J16.2, U2.2 (VI)
5V_3: C4.1, C6.1, J8.2, J12.2, U3.2 (VO)
5V_HP: C22.1, C26.1, C31.1, J2.2, J3.2, J10.2, J11.2, R3.1, R5.2, U8.2 (VO)
5V_PI: C15.1, C18.1, C33.1, J17.2, R3.1, R3.2, U7.2 (VO)
5V_STATIC: C2.1, C7.1, C9.1, D1.1 (K), J1.3, J9.3, J20.1, K1.A1, R3.2, U1.3 (VI), U4.2 (VO)
AC1_NEG: D3.2, J22.2
AC1_POS: D3.3, J22.1
AC2_NEG: D4.2, J23.2
AC2_POS: D4.3, J23.1
ACTIVATE: J19.2, J20.2, R1.1
AGND: C1.2, C2.2, C3.2, C4.2, C5.2, C6.2, C7.2, C8.2, C9.2, C10.2, C11.2, C12.2, C13.2, C14.1, C15.2, C16.2, C17.2, C18.2, C19.2, C20.2, C21.1, C22.2, C23.1, C24.1, C25.2, C26.2, C27.1, C28.1, C29.1, C30.2, C31.2, C32.2, C33.2, C34.2, D1.1 (K), D2.1 (K), D3.1 (+), D3.4 (-), D4.1 (+), J1.1, J2.1, J3.1, J4.2, J5.2, J6.2, J7.1, J8.1, J9.1, J10.1, J11.1, J12.1, J13.2, J14.2, J15.2, J16.1, J17.1, J18.1, J19.1, J21.1, Q1.2 (E), R2.1, R3.2, R4.1, R4.2, R5.2, U1.1 (ADJ), U2.1 (ADJ), U3.1 (GND), U4.1 (GND)
ANALOG_NEG: C21.2, C23.2, C27.2, J4.1, J5.1, J6.1, J13.1, J14.1, J15.1, R3.2, R6.1, U2.3 (VO)
ANALOG_POS: C16.1, C19.1, C25.1, J4.3, J5.3, J6.3, J13.3, J14.3, J15.3, R3.1, R3.2, U1.2 (VO)
DC_NEG: C14.2, K1.24, U2.2 (VI)
DC_NEG_PRE_RELAY: F1.2, K1.21
DC_POS: C10.1, C11.1, C30.1, C32.1, C34.1, K1.14, U1.3 (VI), U2.3 (VO), U3.3 (VI), U7.3 (VI), U8.3 (VI)
DC_POS_PRE_RELAY: C8.1, F2.2, K1.11, U4.3 (VI)
ENTRY_NEG: C24.2, C28.2, C29.2, D4.4 (-), F1.1, R3.2
ENTRY_POS: C13.1, C17.1, C20.1, D3.1 (+), F2.1, R3.1
unnamed: D1.2 (A), K1.A2, Q1.3 (C), R3.1
unnamed: D2.2 (A), R3.1
unnamed: D3.2, R3.1
unnamed: D4.2, R3.1
unnamed: J18.2, R3.1
unnamed: J20.3, R3.1
unnamed: Q1.1 (B), R1.2
unnamed: R2.2, R3.1, U7.1 (ADJ)
unnamed: R3.2, R4.1, U1.1 (ADJ)
unnamed: R4.2, R5.1, U8.1 (ADJ)
unnamed: R5.1, R6.2, U2.1 (ADJ)
