duanestorey/Hifi-Amplifier/Code/ESP32/amp/main/bluetooth.h

#ifndef __BLUETOOTH_H__
#define __BLUETOOTH_H__

#include "nimble/nimble_port.h"
#include "nimble/nimble_port_freertos.h"
#include "host/ble_hs.h"
#include "host/util/util.h"
#include "console/console.h"
#include "services/gap/ble_svc_gap.h"

struct ble_hs_adv_fields;
struct ble_gap_conn_desc;
struct ble_hs_cfg;
union ble_store_value;
union ble_store_key;

#define BLECENT_SVC_ALERT_UUID              0x1811
#define BLECENT_CHR_SUP_NEW_ALERT_CAT_UUID  0x2A47
#define BLECENT_CHR_NEW_ALERT               0x2A46
#define BLECENT_CHR_SUP_UNR_ALERT_CAT_UUID  0x2A48
#define BLECENT_CHR_UNR_ALERT_STAT_UUID     0x2A45
#define BLECENT_CHR_ALERT_NOT_CTRL_PT       0x2A44

class Bluetooth {
public:
    static Bluetooth &instance();
    void init();
protected:
    Bluetooth();

    static Bluetooth* mInstance;

    bool mAdvDone;
};

#endif
